loxodes/vna/breakouts/amp_cpw_hmc311/hmc311_cpw.png

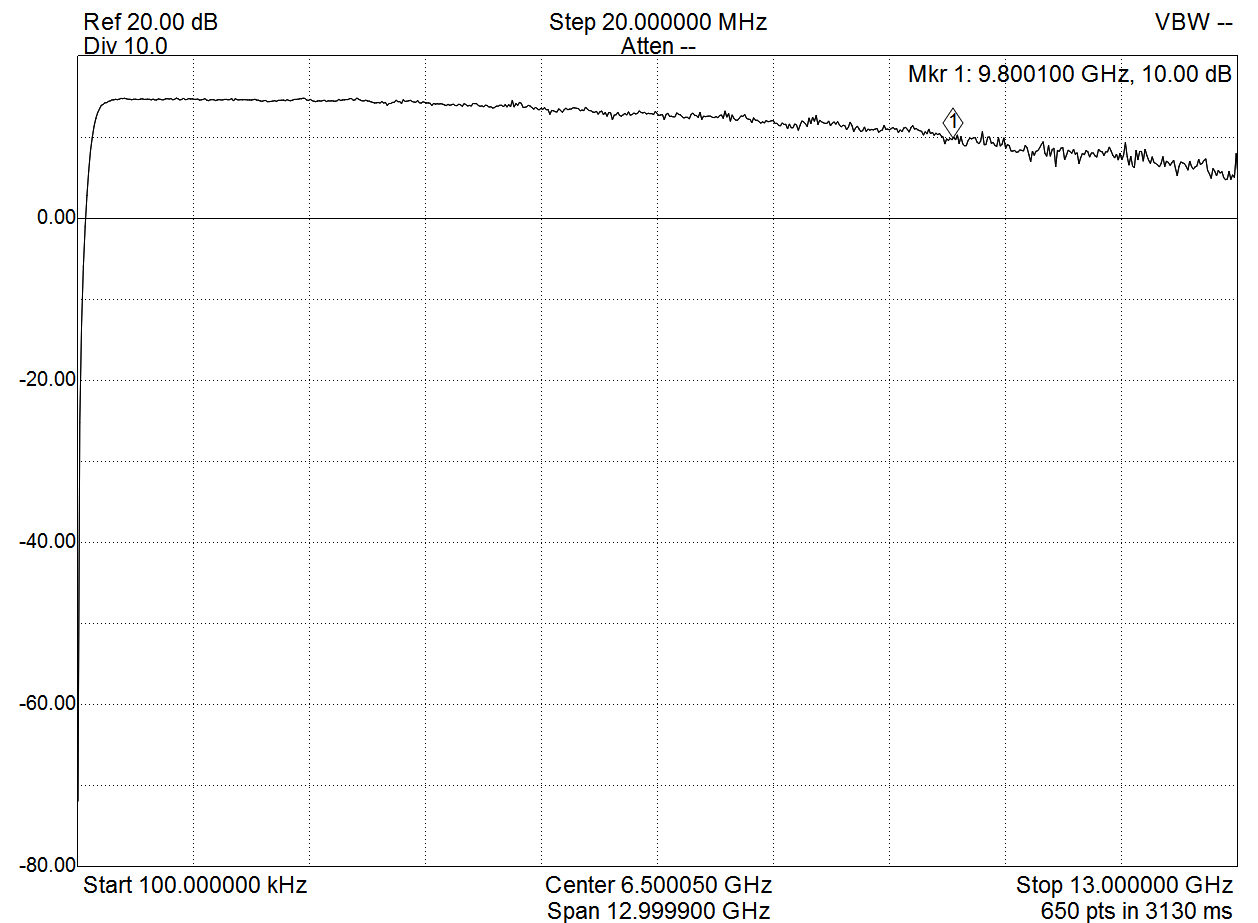
breakouts/amp_cpw_hmc311/hmc311_cpw.png
