loxodes/vna/doc/eevblog_forum_pictures/air_1foot_above_pile.png

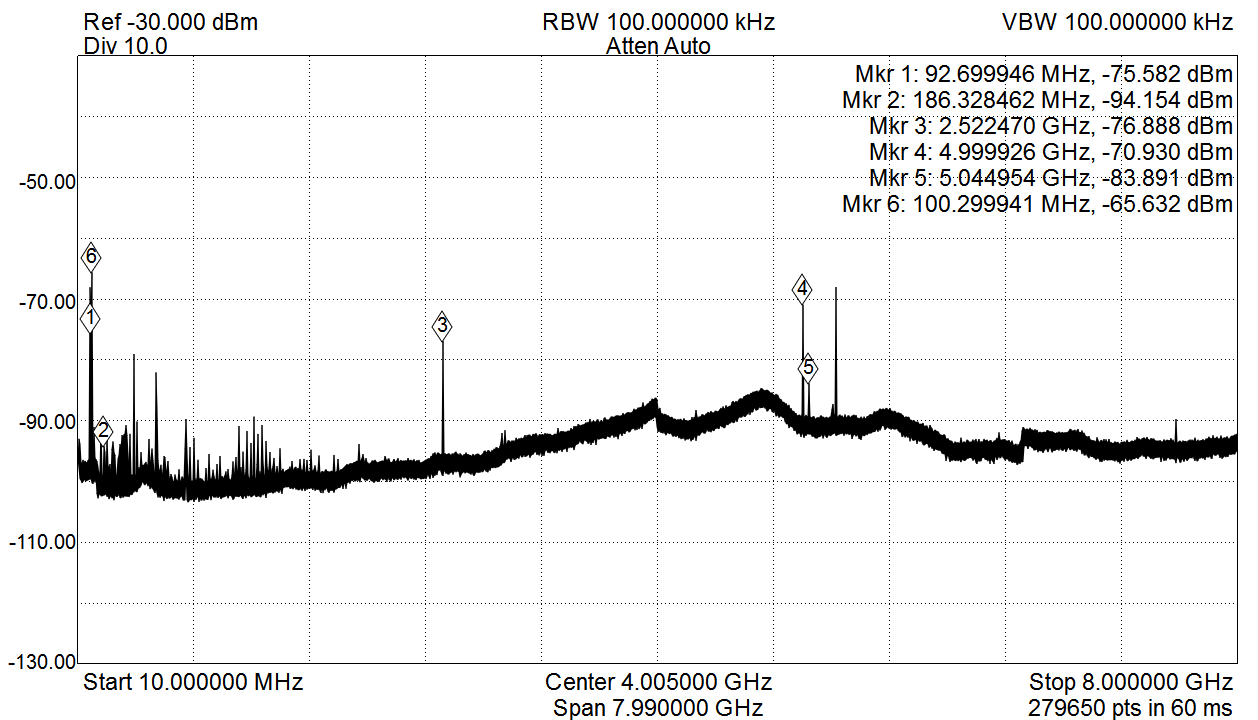
doc/eevblog_forum_pictures/air_1foot_above_pile.png
