loxodes/vna/doc/lpf_smith.png

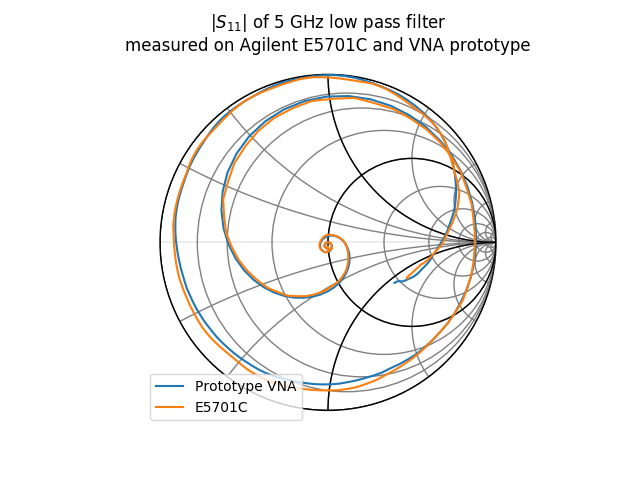
doc/lpf_smith.png
