loxodes/vna/doc/modules.jpg

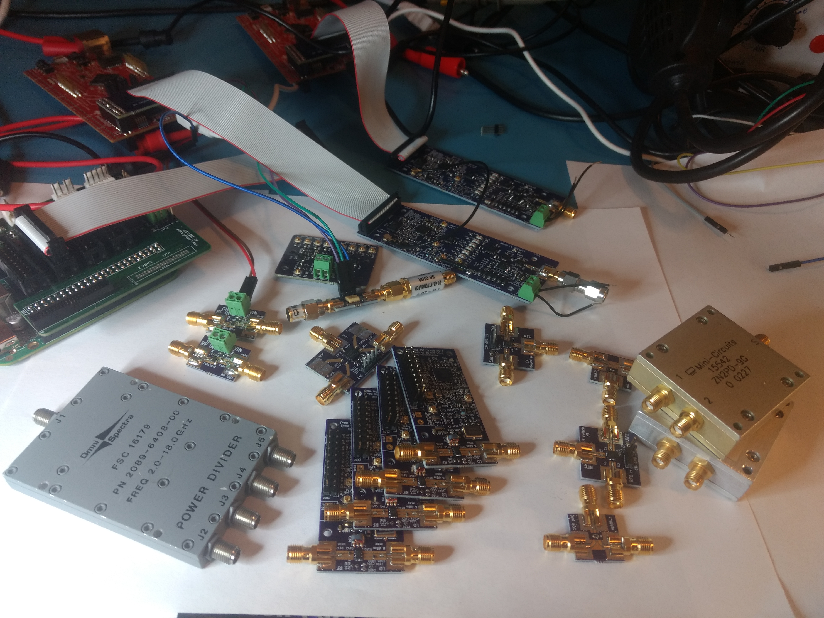
doc/modules.jpg
