loxodes/vna/doc/r0_vna.jpg

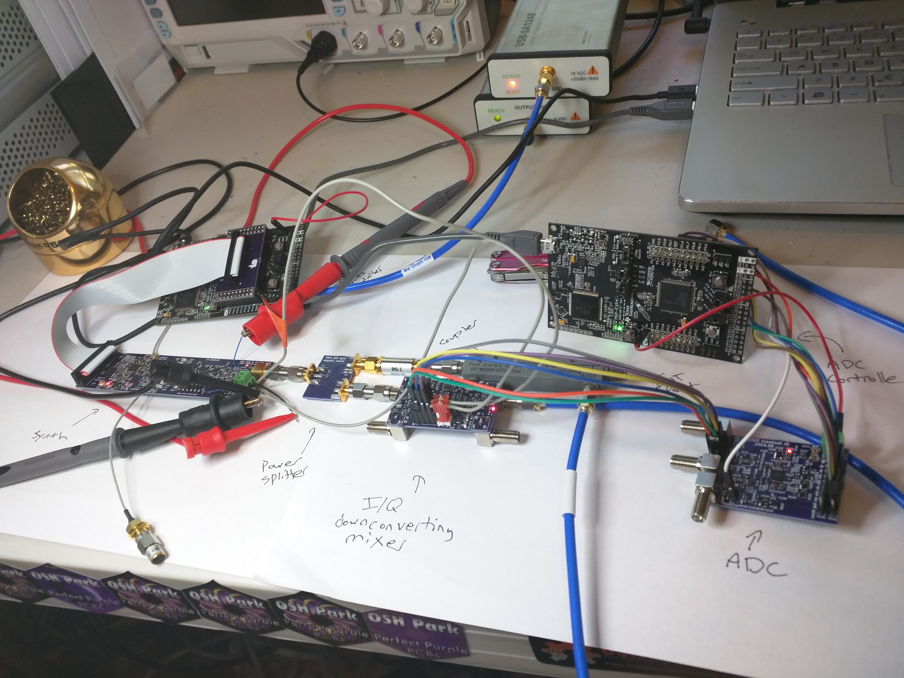
doc/r0_vna.jpg
