loxodes/vna/doc/synth.jpg

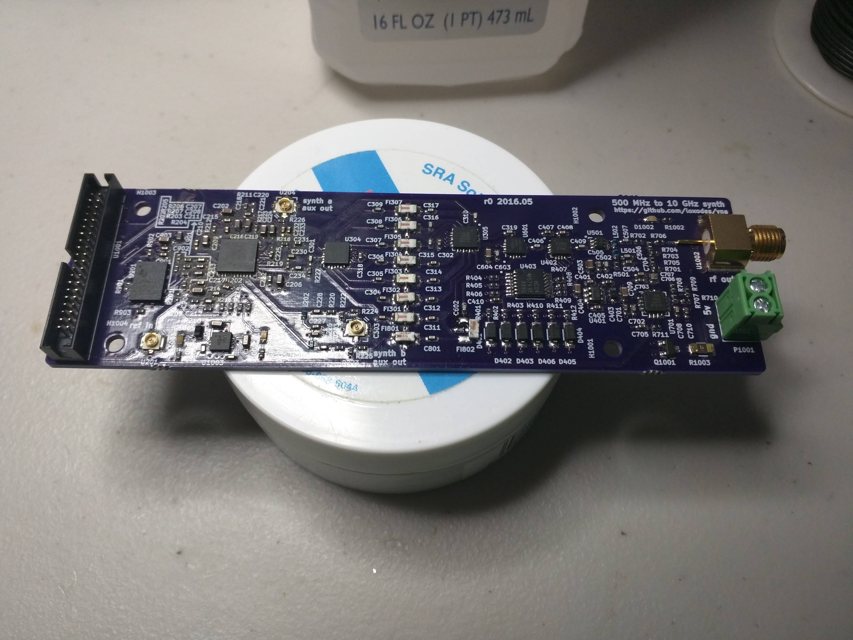
doc/synth.jpg
