loxodes/vna/doc/vna_pictures/cape.jpg

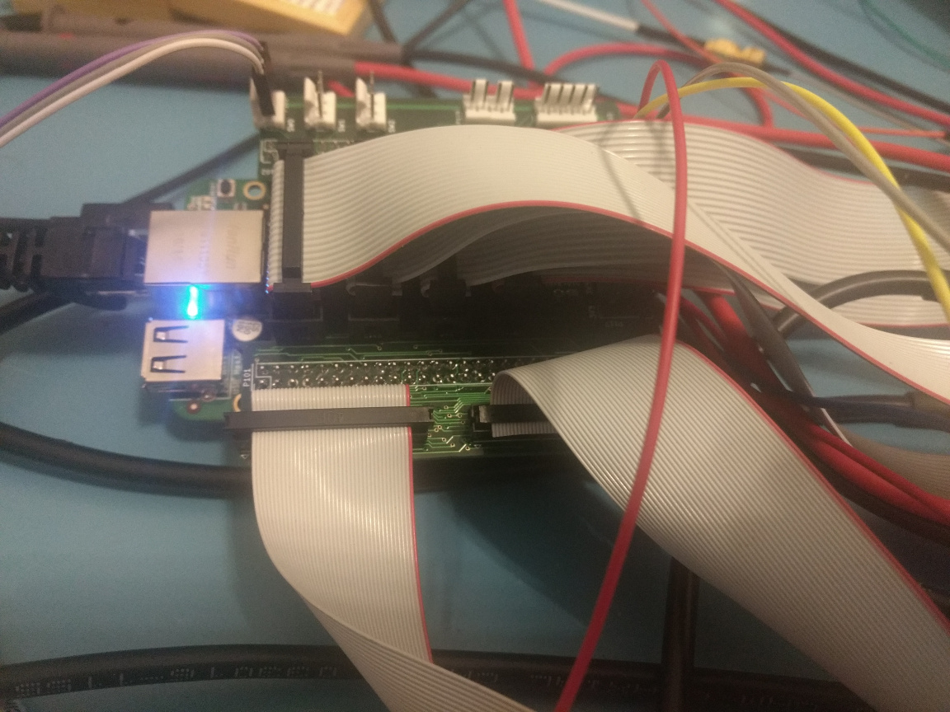
doc/vna_pictures/cape.jpg
