loxodes/vna/doc/vna_pictures/front_module_pile.jpg

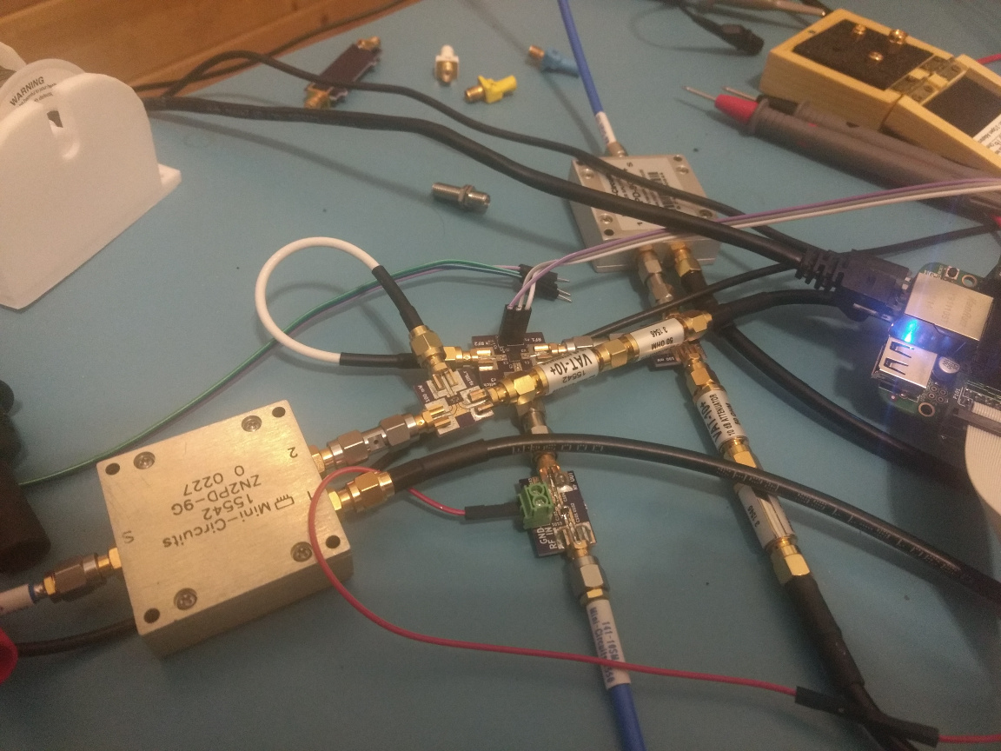
doc/vna_pictures/front_module_pile.jpg
