loxodes/vna/doc/vna_pictures/receivers.jpg

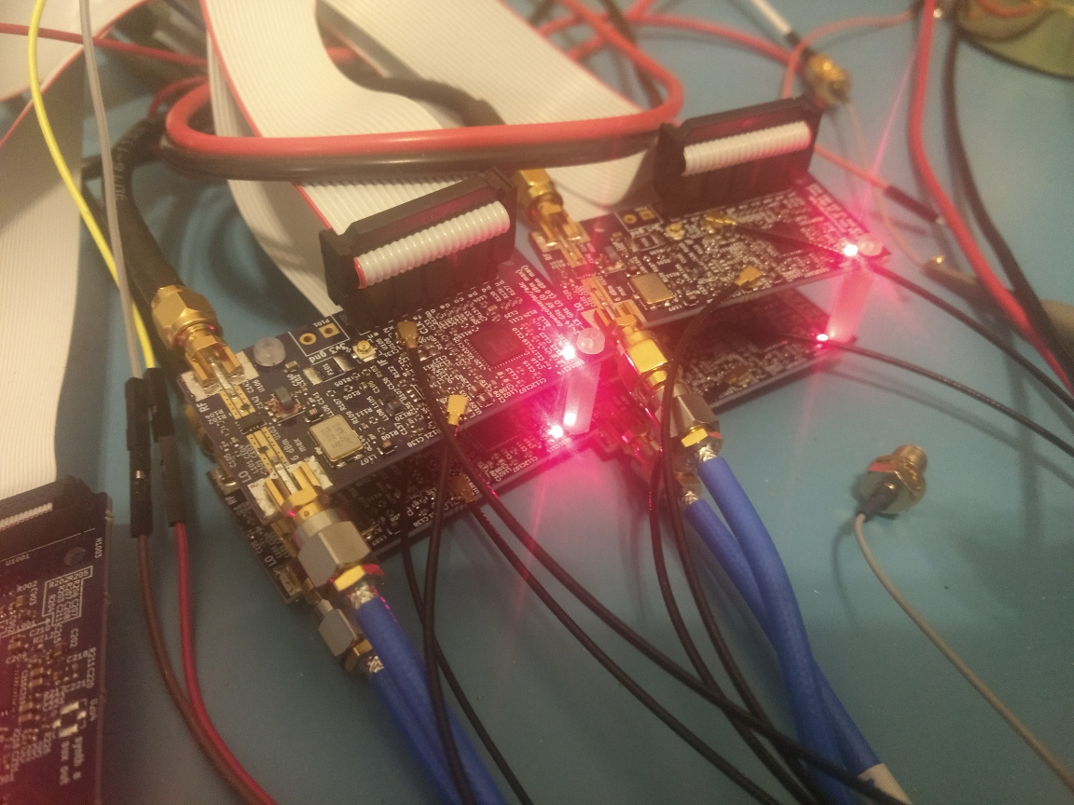
doc/vna_pictures/receivers.jpg
