loxodes/vna/doc/vna_pictures/s11_3dbatt.png

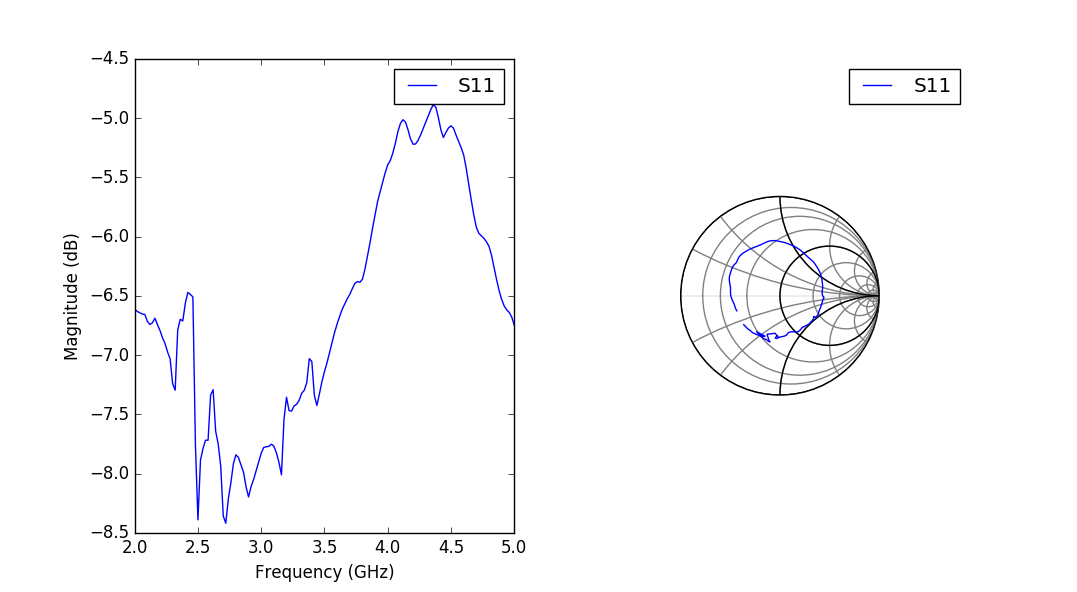
doc/vna_pictures/s11_3dbatt.png
