loxodes/vna/doc/vna_pictures/s11_10dbatt.png

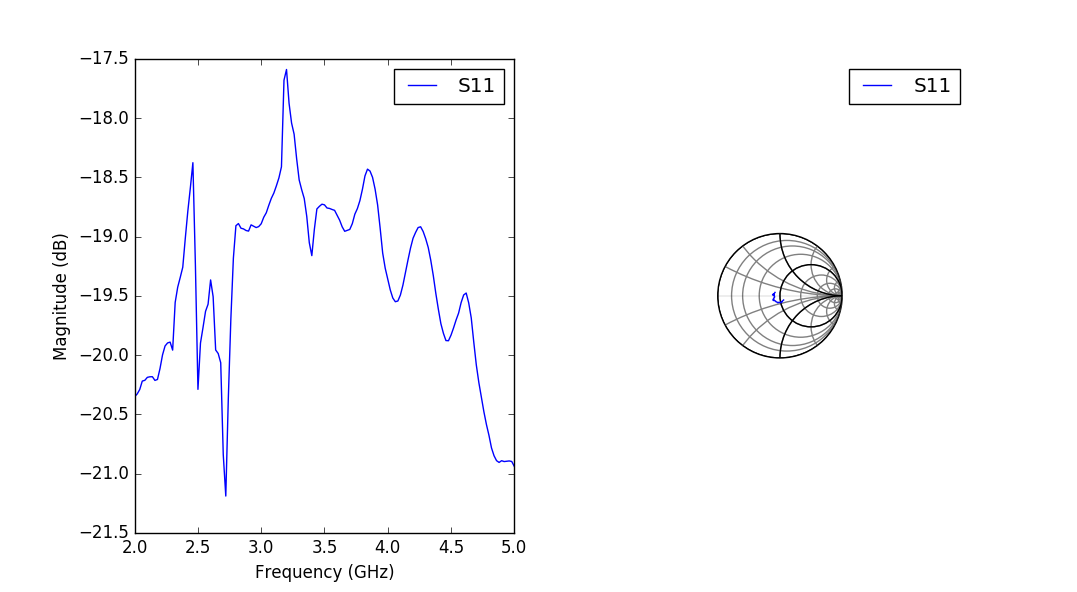
doc/vna_pictures/s11_10dbatt.png
