loxodes/vna/doc/vna_pictures/synth.jpg

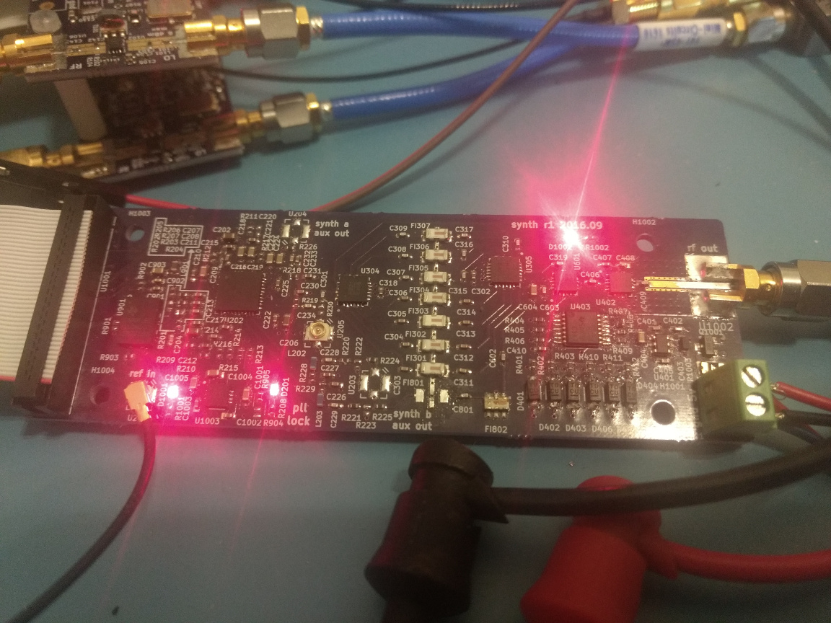
doc/vna_pictures/synth.jpg
