loxodes/vna/doc/vna_r1_ctrl.jpg

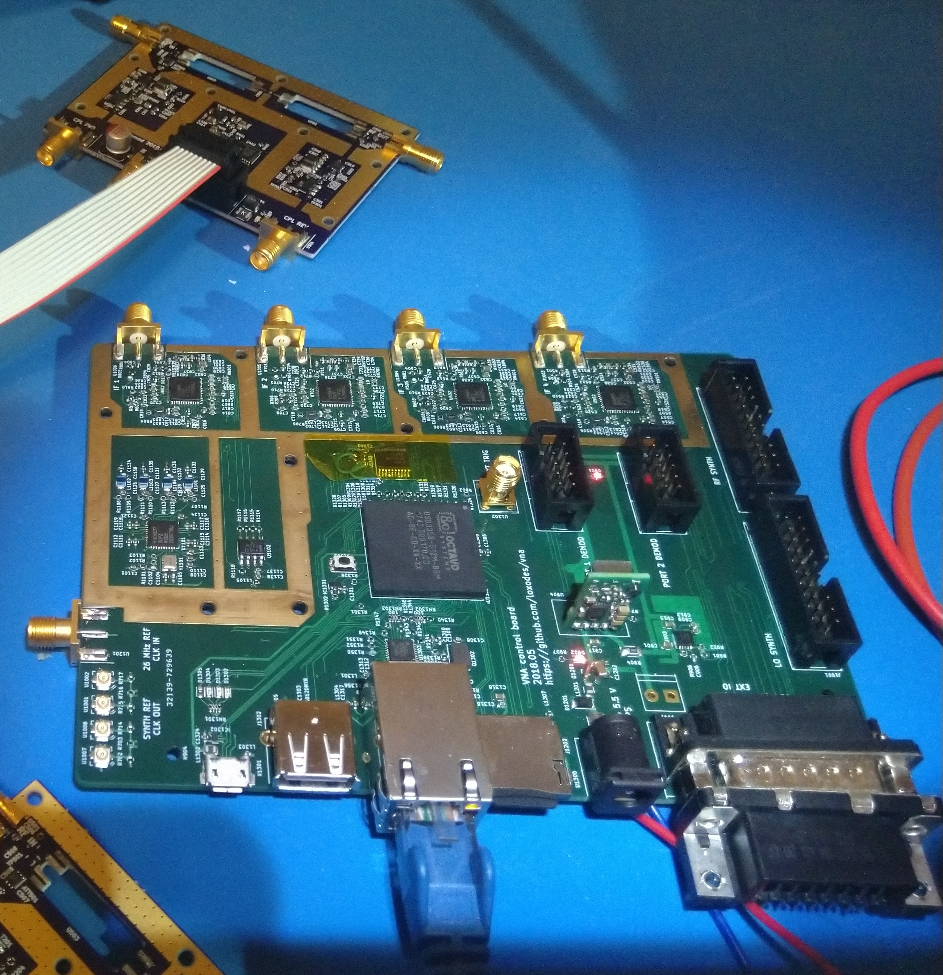
doc/vna_r1_ctrl.jpg
