loxodes/vna/simulations/ltspice/demod_baseband.asc

C1: cap; 22p
C2: cap; 100n
R1: res; 604
R2: res; 604
R3: res; 604
U1: LT1567
V1: voltage; 5
V2: voltage; .7
V3: voltage; ""; AC 1
Named nets: 0, vout
.ac oct 100 1k 5Meg
