loxodes/vna/hardware/mm_reflectometer/evalboards/ep2k1P/ep2k1P.kicad_pcb

## KiCad design hardware/mm_reflectometer/evalboards/ep2k1P/ep2k1P.kicad_pcb (2020-12-29)

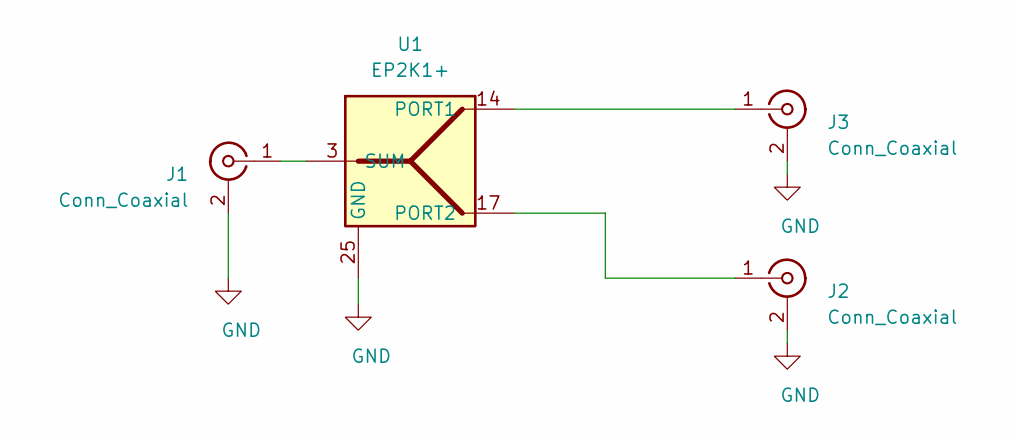
[picture p76: schematic ep2k1P.kicad_sch]

Parts:
J1, J2, J3: Conn_Coaxial; sw_edge_oshpark_4layer
U1: EP2K1+; DG1847; mpn EP2K1+; mouser# 139-EP2K1

Connections:
GND: J1.2 (Ext), J2.2 (Ext), J3.2 (Ext), U1.1 (NC), U1.2 (NC), U1.4 (NC), U1.5 (NC), U1.6 (NC), U1.7 (NC), U1.8 (NC), U1.9 (NC), U1.10 (NC), U1.11 (NC), U1.12 (NC), U1.13 (NC), U1.15 (NC), U1.16 (NC), U1.18 (NC), U1.19 (NC), U1.20 (NC), U1.21 (NC), U1.22 (NC), U1.23 (NC), U1.24 (NC), U1.25 (GND)
unnamed: J1.1 (In), U1.3 (SUM)
unnamed: J3.1 (In), U1.14 (PORT1)
unnamed: J2.1 (In), U1.17 (PORT2)

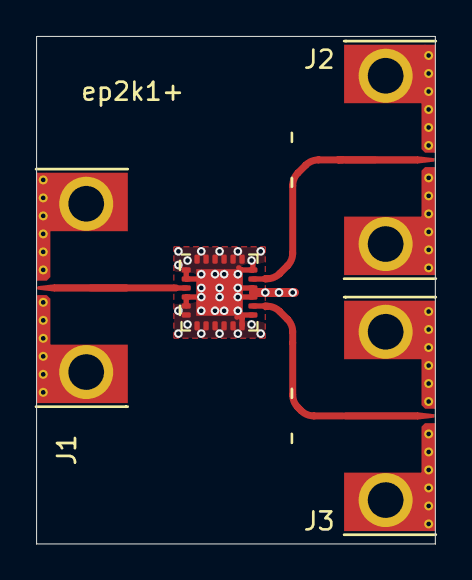
[picture p77: board ep2k1P.kicad_pcb from above]

Board: 4 copper layers, 22.2 x 28.2 mm, 4 parts (0 on the bottom side), 4 nets.
