loxodes/vna/hardware/mm_reflectometer/evalboards/fpc07181/fpc07181.kicad_pcb

## KiCad design hardware/mm_reflectometer/evalboards/fpc07181/fpc07181.kicad_pcb (2020-12-29)

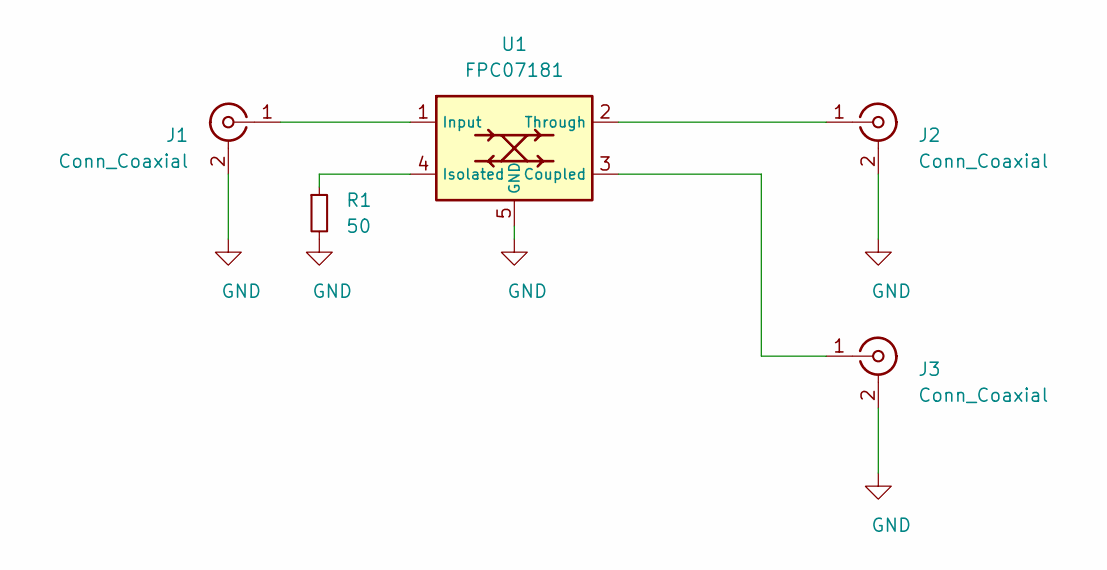
[picture p78: schematic fpc07181.kicad_sch]

Parts:
J1, J2, J3: Conn_Coaxial; sw_edge_oshpark_4layer
R1: 50; R_0402_1005Metric
U1: FPC07181; mpn FPC07181; digikey# 1761-1032-ND

Connections:
GND: J1.2 (Ext), J2.2 (Ext), J3.2 (Ext), R1.2, U1.5 (GND)
unnamed: J1.1 (In), U1.1 (Input)
unnamed: J2.1 (In), U1.2 (Through)
unnamed: J3.1 (In), U1.3 (Coupled)
unnamed: R1.1, U1.4 (Isolated)

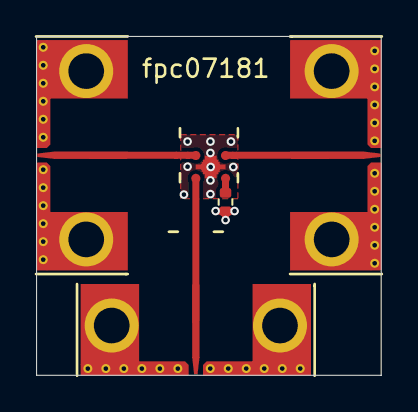
[picture p79: board fpc07181.kicad_pcb from above]

Board: 4 copper layers, 19.2 x 18.8 mm, 5 parts (0 on the bottom side), 5 nets.
