loxodes/vna/breakouts/balun/balun.kicad_pcb

## KiCad design breakouts/balun/balun.kicad_pcb (2020-07-13)

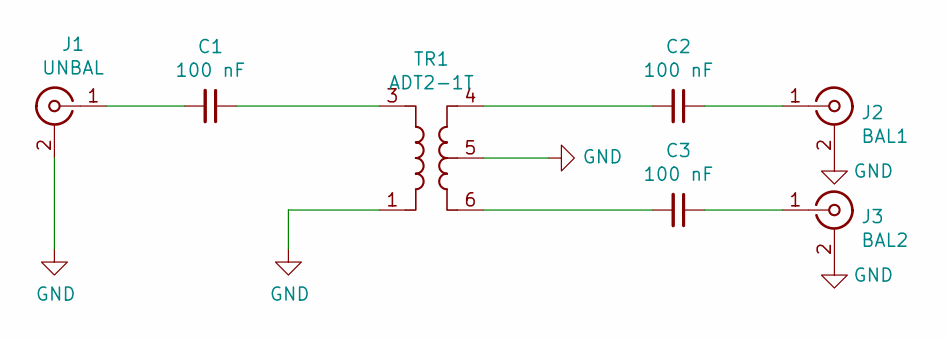
[picture p80: schematic balun.sch]

Parts:
C1, C2, C3: 100 nF; C_0603_1608Metric
J1: UNBAL; SMA_Amphenol_132134_Vertical
J2: BAL1; SMA_Amphenol_132134_Vertical
J3: BAL2; SMA_Amphenol_132134_Vertical
TR1: ADT2-1T; Mini-Circuits_CD542_H2.84mm

Connections:
GND: J1.2 (Ext), J2.2 (Ext), J3.2 (Ext), TR1.1, TR1.5
unnamed: C1.1, TR1.3
unnamed: C1.2, J1.1 (In)
unnamed: C2.1, J2.1 (In)
unnamed: C2.2, TR1.4
unnamed: C3.1, J3.1 (In)
unnamed: C3.2, TR1.6

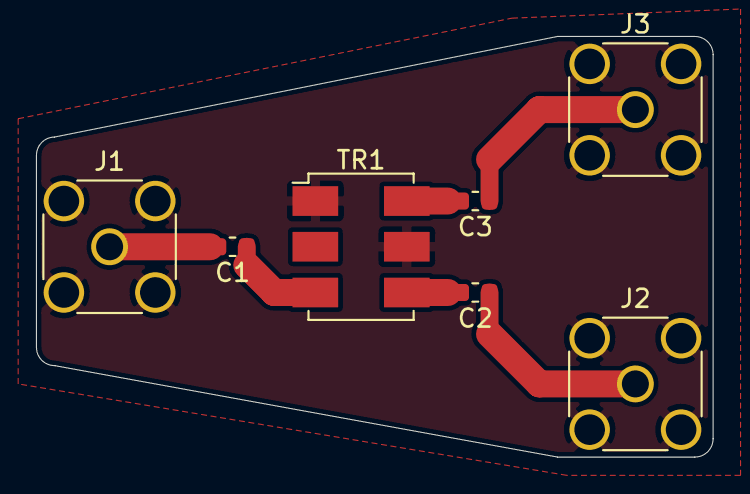
[picture p81: board balun.kicad_pcb from above]

Board: 2 copper layers, 37.6 x 23.4 mm, 7 parts (0 on the bottom side), 7 nets.
