loxodes/vna/hardware/vna_mm_synth/vna_mm_synth.kicad_pcb

## KiCad design hardware/vna_mm_synth/vna_mm_synth.kicad_pcb (2020-04-20)

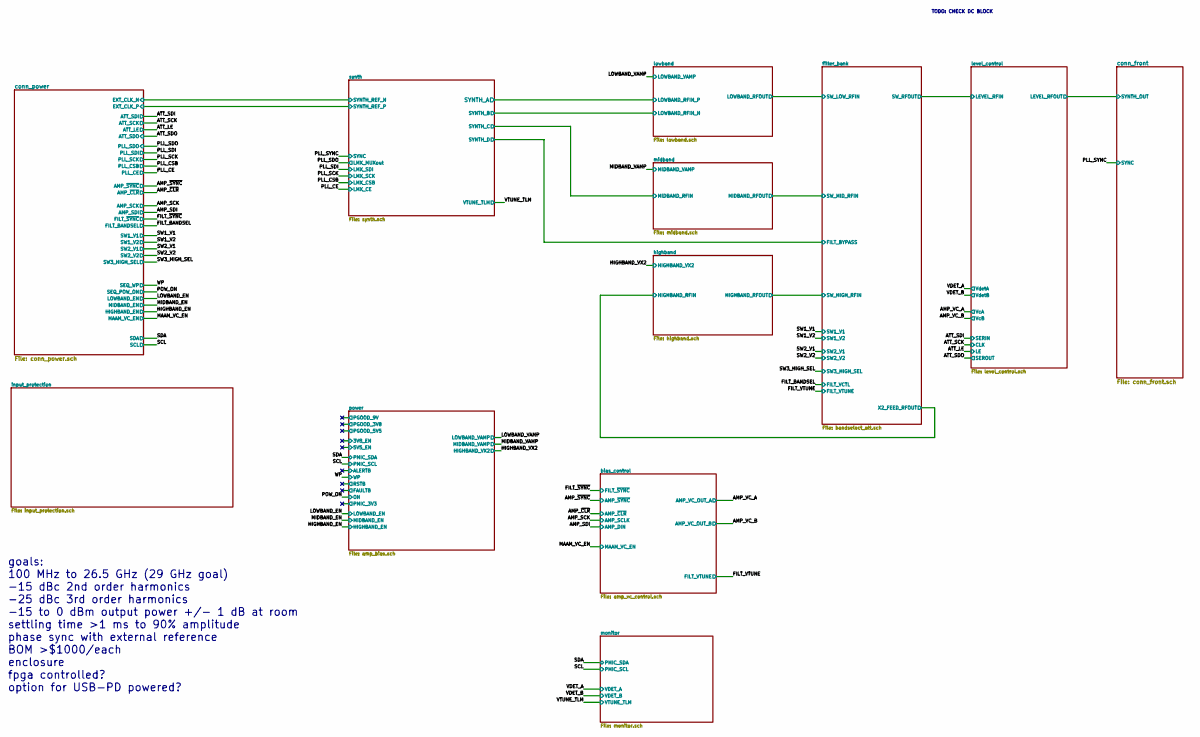
[picture p82: schematic vna_mm_synth.sch]

Notes on the sheet:
goals: 100 MHz to 26.5 GHz (29 GHz goal) -15 dBc 2nd order harmonics -25 dBc 3rd order harmonics -15 to 0 dBm output power +/- 1 dB at room settling time >1 ms to 90% amplitude phase sync with external reference BOM >$1000/each enclosure fpga controlled? option for USB-PD powered?
TODO: CHECK DC BLOCK

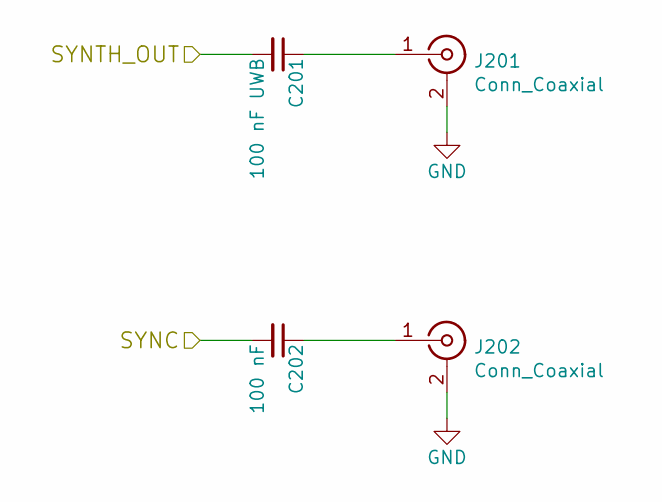
[picture p83: schematic conn_front.sch]

Parts:
C201: 100 nF UWB; C_0402_1005Metric
C202: 100 nF; C_0402_1005Metric
J201: Conn_Coaxial; sw_edge_ro4350b_10mil
J202: Conn_Coaxial; SMA_Amphenol_132289_EdgeMount

Connections:
/PLL_SYNC: C202.2; also elsewhere on the board
/level_control/LEVEL_RFOUT: C201.2; also elsewhere on the board
GND: J201.2 (Ext), J202.2 (Ext); also elsewhere on the board
unnamed: C201.1, J201.1 (In)
unnamed: C202.1, J202.1 (In)

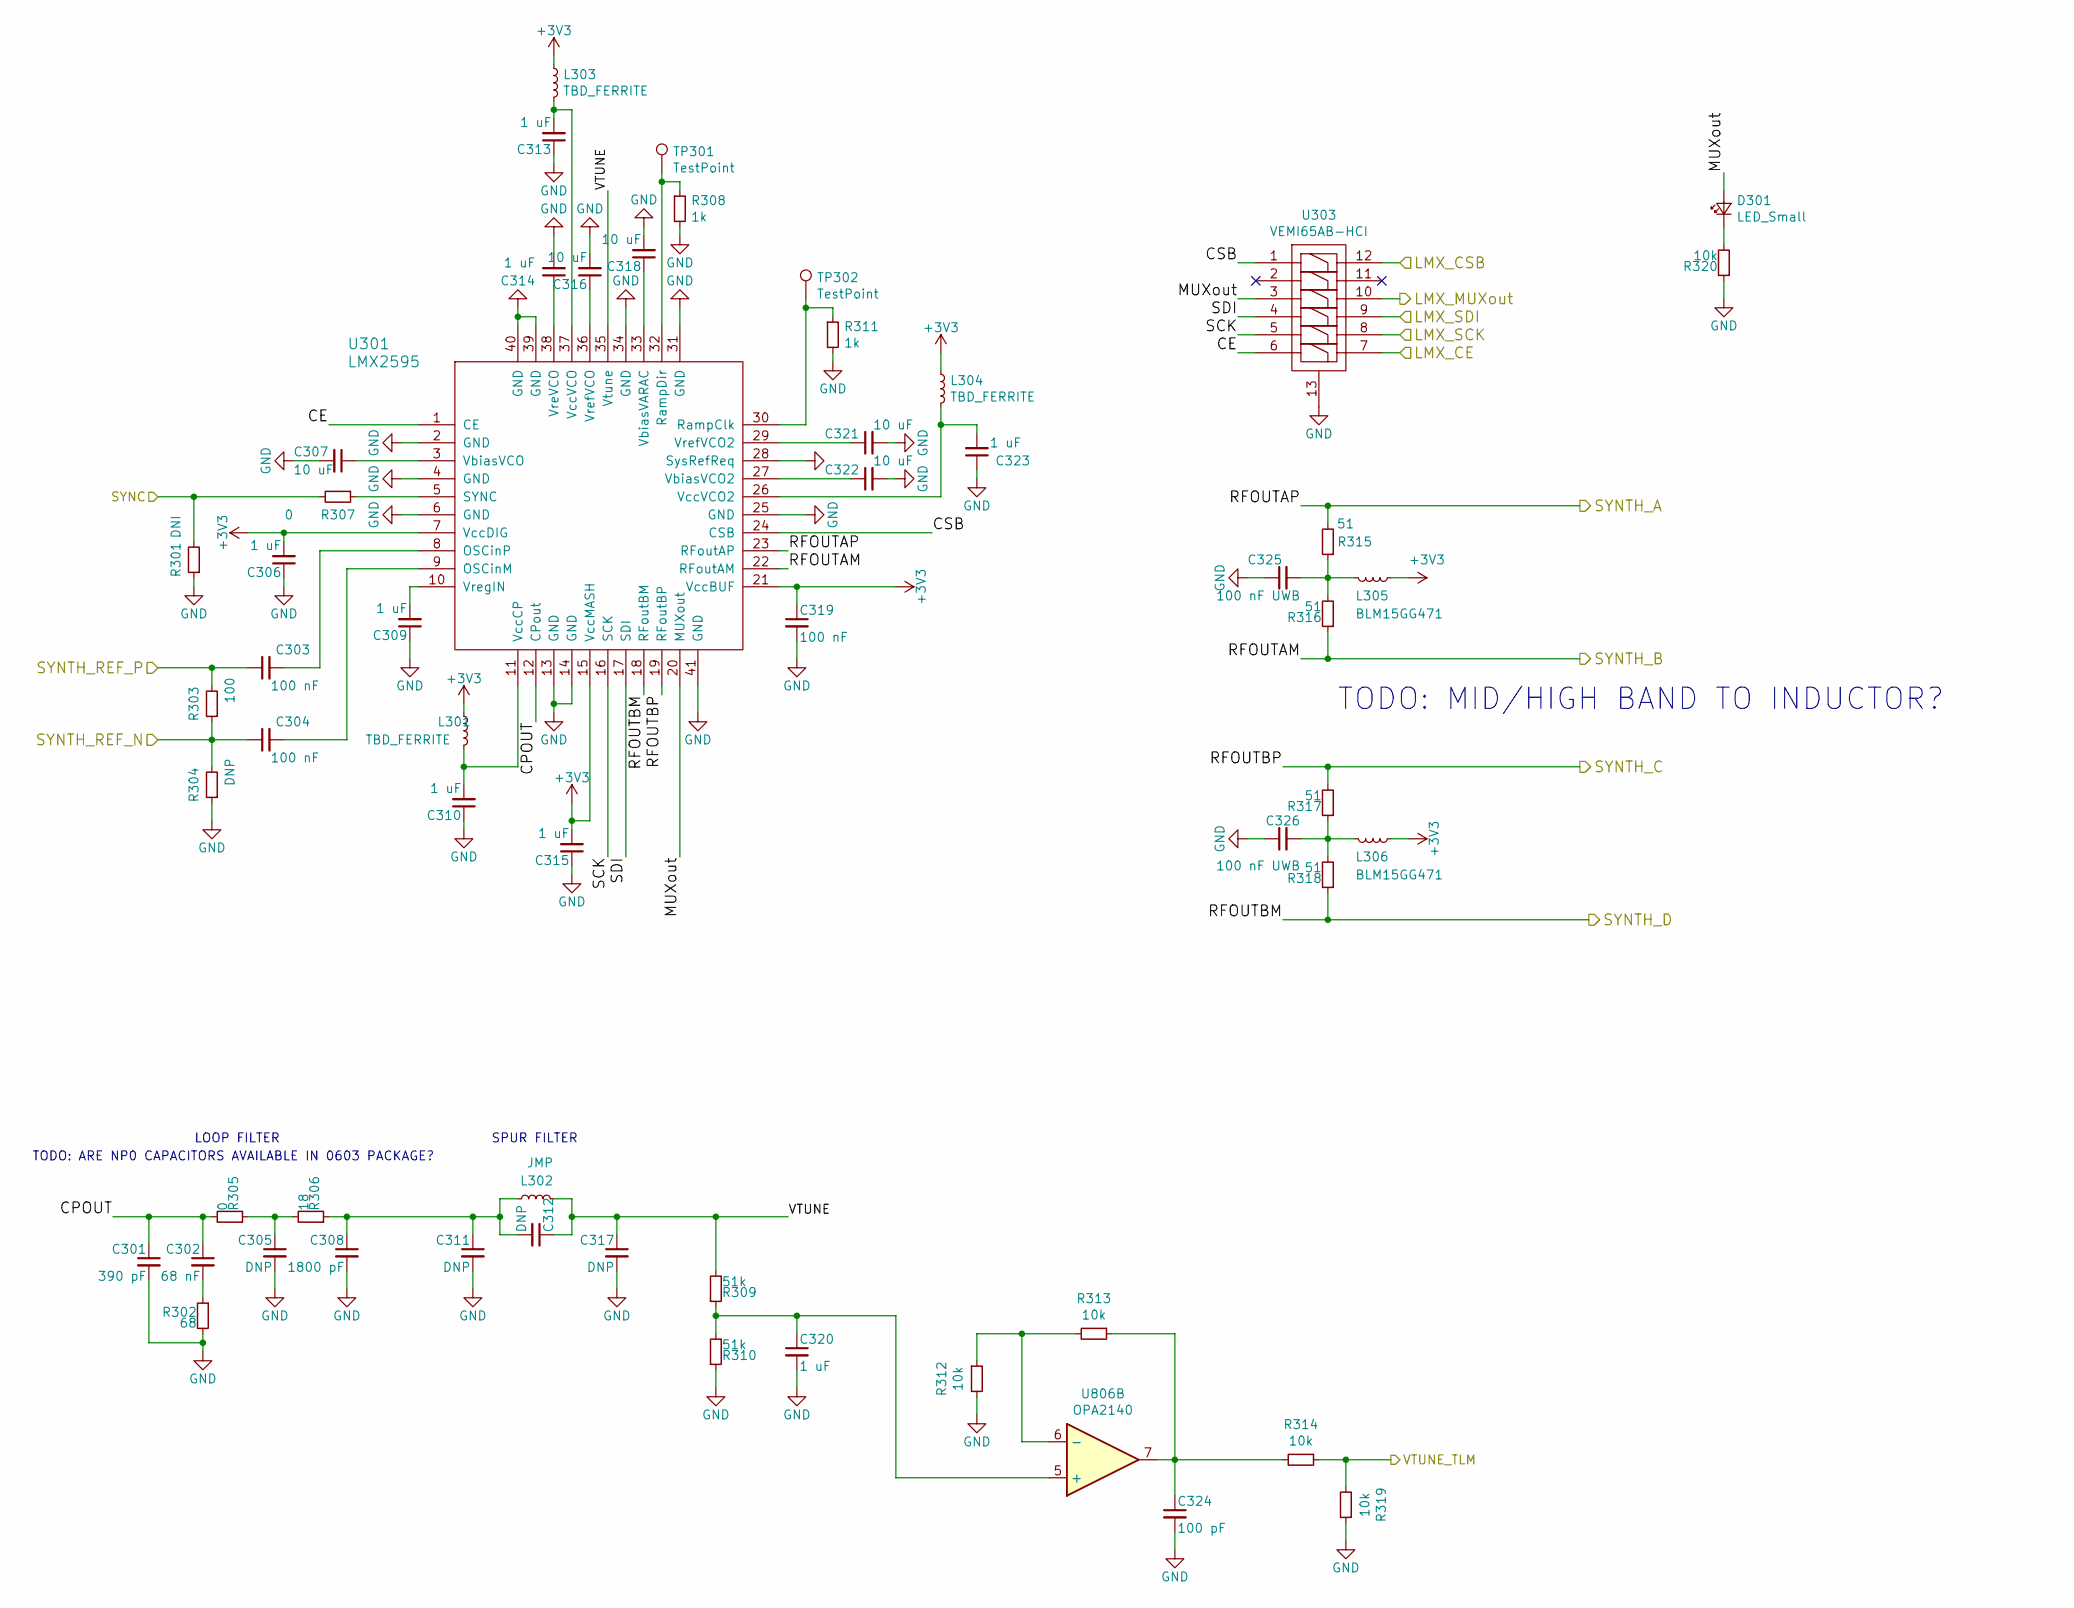
[picture p84: schematic synth.sch]

Parts:
C301: 390 pF; C_0603_1608Metric
C302: 68 nF; C_0603_1608Metric
C303, C304, C319: 100 nF; C_0402_1005Metric
C305, C311, C312, C317: DNP; C_0603_1608Metric
C306, C309, C310, C313, C314, C315, C320, C323: 1 uF; C_0402_1005Metric
C307, C316, C318, C321, C322: 10 uF; C_0603_1608Metric
C308: 1800 pF; C_0603_1608Metric
C324: 100 pF; C_0402_1005Metric
C325, C326: 100 nF UWB; C_0402_1005Metric
D301: LED_Small; LED_0603_1608Metric
L301, L303, L304: TBD_FERRITE; L_0603_1608Metric
L302: JMP; L_0603_1608Metric
L305, L306: BLM15GG471; L_0402_1005Metric
R301: DNI; R_0402_1005Metric
R302: 68; R_0402_1005Metric
R303: 100; R_0402_1005Metric
R304: DNP; R_0402_1005Metric
R305, R307: 0; R_0402_1005Metric
R306: 18; R_0402_1005Metric
R308, R311: 1k; R_0402_1005Metric
R309, R310: 51k; R_0402_1005Metric
R312, R313, R314, R319, R320: 10k; R_0402_1005Metric
R315, R316, R317, R318: 51; R_0402_1005Metric
TP301, TP302: TestPoint; TestPoint_Pad_1.0x1.0mm
U301: LMX2595; Texas_S-PVQFN-N40_EP4.6x4.6mm
U303: VEMI65AB-HCI; LLP2513-13L
U806: OPA2140; MSOP-8_3x3mm_P0.65mm

Connections:
+3V3: C306.2, C315.2, C319.1, L301.1, L303.1, L304.1, L305.1, L306.1, U301.7 (VccDIG), U301.15 (VccMASH), U301.21 (VccBUF); also elsewhere on the board
/PLL_CE: U303.7; also elsewhere on the board
/PLL_CSB: U303.12; also elsewhere on the board
/PLL_SCK: U303.8; also elsewhere on the board
/PLL_SDI: U303.9; also elsewhere on the board
/PLL_SDO: U303.10; also elsewhere on the board
/PLL_SYNC: R301.2, R307.2; also elsewhere on the board
/VTUNE_TLM: R314.1, R319.2; also elsewhere on the board
/conn_power/EXT_CLK_N: C304.1, R303.1, R304.2; also elsewhere on the board
/conn_power/EXT_CLK_P: C303.1, R303.2; also elsewhere on the board
/lowband/LOWBAND_RFIN_N: R316.1, U301.22 (RFoutAM); also elsewhere on the board
/lowband/LOWBAND_RFIN_P: R315.2, U301.23 (RFoutAP); also elsewhere on the board
/midband/MIDBAND_RFIN: R317.2, U301.19 (RFoutBP); also elsewhere on the board
/synth/CE: U301.1 (CE), U303.6
/synth/CPOUT: C301.1, C302.1, R305.2, U301.12 (CPout)
/synth/CSB: U301.24 (CSB), U303.1
/synth/MUXout: D301.2 (A), U301.20 (MUXout), U303.3
/synth/SCK: U301.16 (SCK), U303.5
/synth/SDI: U301.17 (SDI), U303.4
/synth/SYNTH_D: R318.1, U301.18 (RFoutBM)
/synth/VTUNE: C312.1, C317.1, L302.2, R309.2, U301.35 (Vtune)
GND: C301.2, C305.2, C306.1, C307.2, C308.2, C309.1, C310.1, C311.2, C313.1, C314.2, C315.1, C316.2, C317.2, C318.2, C319.2, C320.2, C321.2, C322.2, C323.1, C324.2, C325.1, C326.1, R301.1, R302.2, R304.1, R308.2, R310.1, R311.2, R312.2, R319.1, R320.1, U301.2 (GND), U301.4 (GND), U301.6 (GND), U301.13 (GND), U301.14 (GND), U301.25 (GND), U301.28 (SysRefReq), U301.31 (GND), U301.34 (GND), U301.39 (GND), U301.40 (GND), U301.41 (GND), U303.13; also elsewhere on the board
unnamed: C302.2, R302.1
unnamed: C303.2, U301.8 (OSCinP)
unnamed: C304.2, U301.9 (OSCinM)
unnamed: C305.1, R305.1, R306.2
unnamed: C307.1, U301.3 (VbiasVCO)
unnamed: C308.1, C311.1, C312.2, L302.1, R306.1
unnamed: C309.2, U301.10 (VregIN)
unnamed: C310.2, L301.2, U301.11 (VccCP)
unnamed: C313.2, L303.2, U301.37 (VccVCO)
unnamed: C314.1, U301.38 (VreVCO)
unnamed: C316.1, U301.36 (VrefVCO)
unnamed: C318.1, U301.33 (VbiasVARAC)
unnamed: C320.1, R309.1, R310.2, U806.5 (+)
unnamed: C321.1, U301.29 (VrefVCO2)
unnamed: C322.1, U301.27 (VbiasVCO2)
unnamed: C323.2, L304.2, U301.26 (VccVCO2)
unnamed: C324.1, R313.1, R314.2, U806.7
unnamed: C325.2, L305.2, R315.1, R316.2
unnamed: C326.2, L306.2, R317.1, R318.2
unnamed: D301.1 (K), R320.2
unnamed: R307.1, U301.5 (SYNC)
unnamed: R308.1, TP301.1, U301.32 (RampDir)
unnamed: R311.1, TP302.1, U301.30 (RampClk)
unnamed: R312.1, R313.2, U806.6 (-)

Notes on the sheet:
SPUR FILTER
LOOP FILTER
TODO: ARE NP0 CAPACITORS AVAILABLE IN 0603 PACKAGE?
TODO: MID/HIGH BAND TO INDUCTOR?

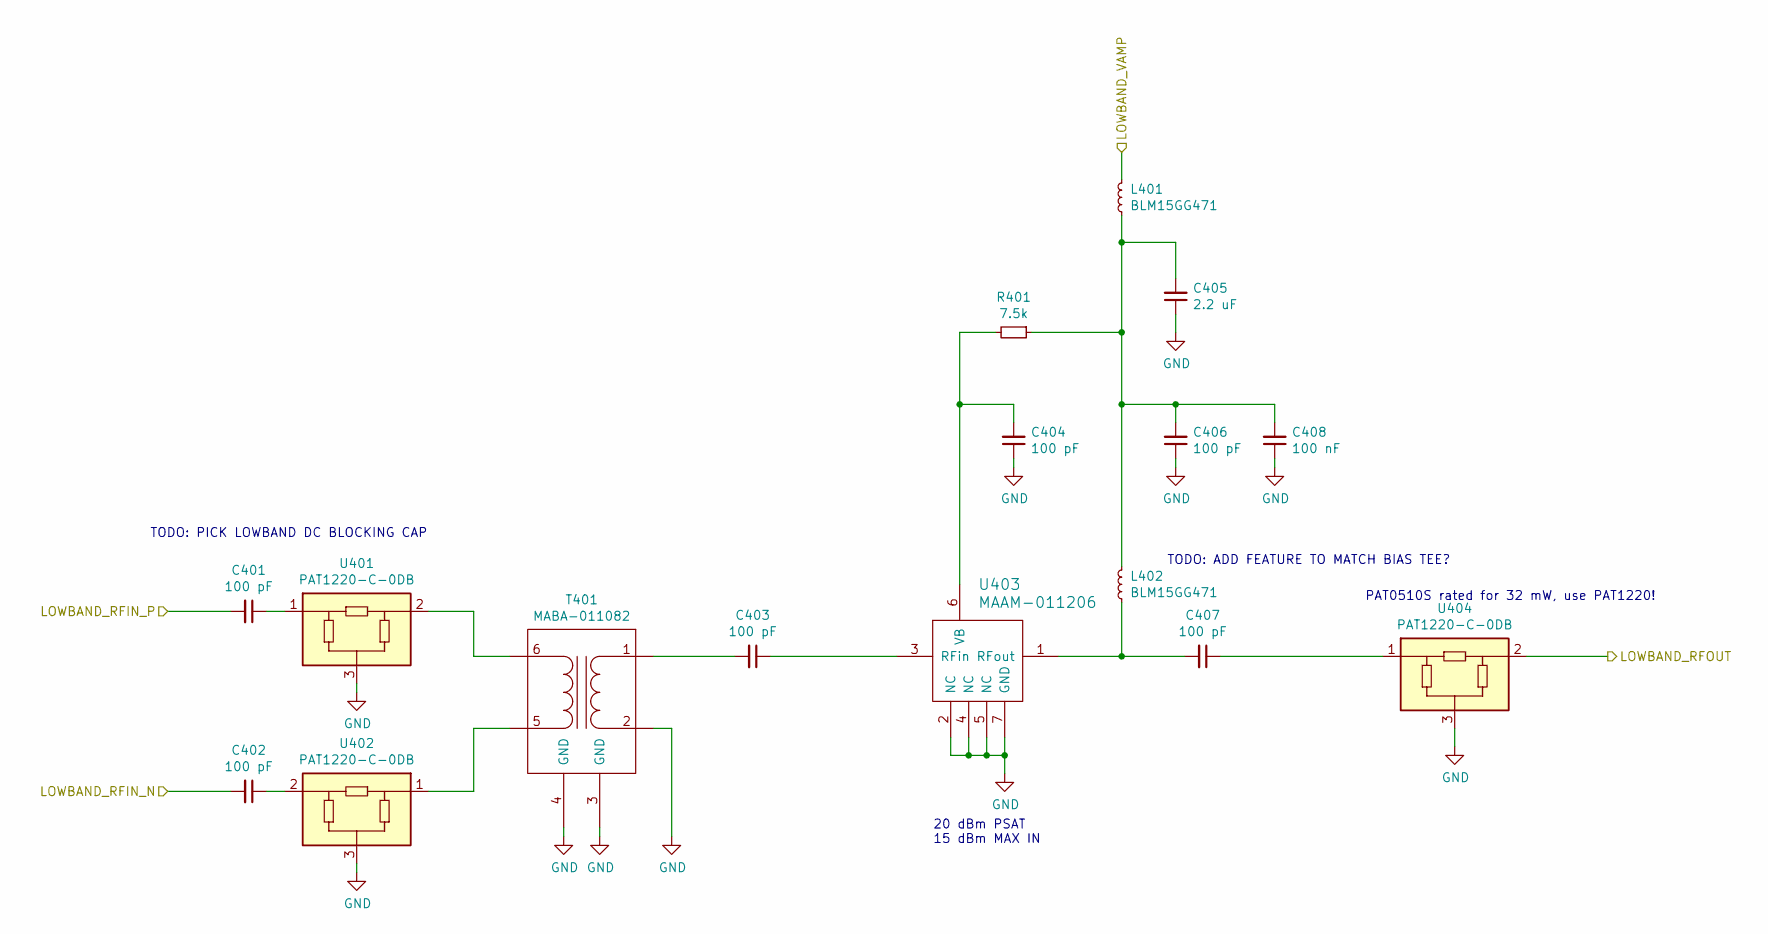
[picture p85: schematic lowband.sch]

Parts:
C401, C402, C403, C404, C406, C407: 100 pF; C_0402_1005Metric
C405: 2.2 uF; C_0603_1608Metric
C408: 100 nF; C_0402_1005Metric
L401, L402: BLM15GG471; L_0402_1005Metric
R401: 7.5k; R_0402_1005Metric
T401: MABA-011082; transformer_3p81_3p81
U401, U402, U404: PAT1220-C-0DB; RF_Attenuator_Susumu_PAT1220
U403: MAAM-011206; TDFN6

Connections:
/LOWBAND_VAMP: L401.2; also elsewhere on the board
/lowband/LOWBAND_RFIN_N: C402.2; also elsewhere on the board
/lowband/LOWBAND_RFIN_P: C401.2; also elsewhere on the board
/lowband/LOWBAND_RFOUT: U404.2; also elsewhere on the board
GND: C404.1, C405.1, C406.1, C408.1, T401.2, T401.3 (GND), T401.4 (GND), U401.3, U402.3, U403.2 (NC), U403.4 (NC), U403.5 (NC), U403.7 (GND), U404.3; also elsewhere on the board
unnamed: C401.1, U401.1
unnamed: C402.1, U402.2
unnamed: C403.1, U403.3 (RFin)
unnamed: C403.2, T401.1
unnamed: C404.2, R401.2, U403.6 (VB)
unnamed: C405.2, C406.2, C408.2, L401.1, L402.2, R401.1
unnamed: C407.1, U404.1
unnamed: C407.2, L402.1, U403.1 (RFout)
unnamed: T401.5, U402.1
unnamed: T401.6, U401.2

Notes on the sheet:
TODO: PICK LOWBAND DC BLOCKING CAP
TODO: ADD FEATURE TO MATCH BIAS TEE?
20 dBm PSAT 15 dBm MAX IN
PAT0510S rated for 32 mW, use PAT1220!

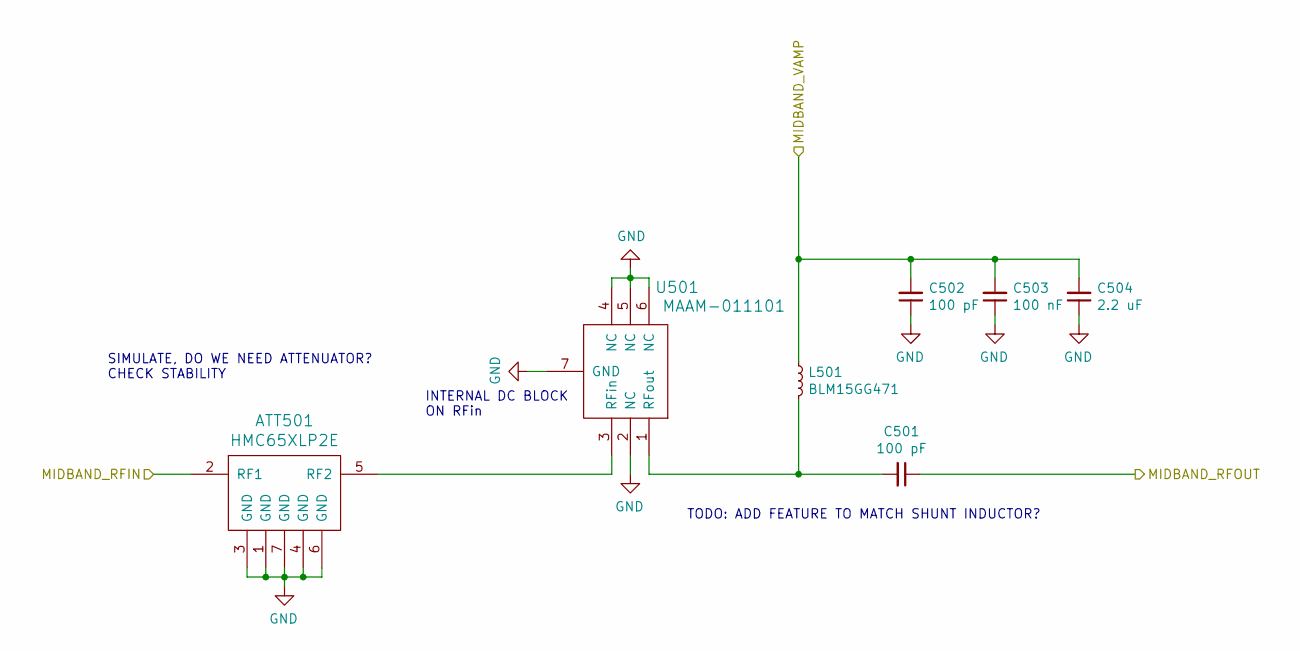
[picture p86: schematic midband.sch]

Parts:
ATT501: HMC65XLP2E; LP2E_DFN6_2x2mm_Pitch0.60mm
C501, C502: 100 pF; C_0402_1005Metric
C503: 100 nF; C_0402_1005Metric
C504: 2.2 uF; C_0603_1608Metric
L501: BLM15GG471; L_0402_1005Metric
U501: MAAM-011101; TDFN6

Connections:
/MIDBAND_VAMP: C502.2, C503.2, C504.2, L501.1; also elsewhere on the board
/midband/MIDBAND_RFIN: ATT501.2 (RF1); also elsewhere on the board
/midband/MIDBAND_RFOUT: C501.1; also elsewhere on the board
GND: ATT501.1 (GND), ATT501.3 (GND), ATT501.4 (GND), ATT501.6 (GND), ATT501.7 (GND), C502.1, C503.1, C504.1, U501.2 (NC), U501.4 (NC), U501.5 (NC), U501.6 (NC), U501.7 (GND); also elsewhere on the board
unnamed: ATT501.5 (RF2), U501.3 (RFin)
unnamed: C501.2, L501.2, U501.1 (RFout)

Notes on the sheet:
INTERNAL DC BLOCK ON RFin
SIMULATE, DO WE NEED ATTENUATOR? CHECK STABILITY
TODO: ADD FEATURE TO MATCH SHUNT INDUCTOR?

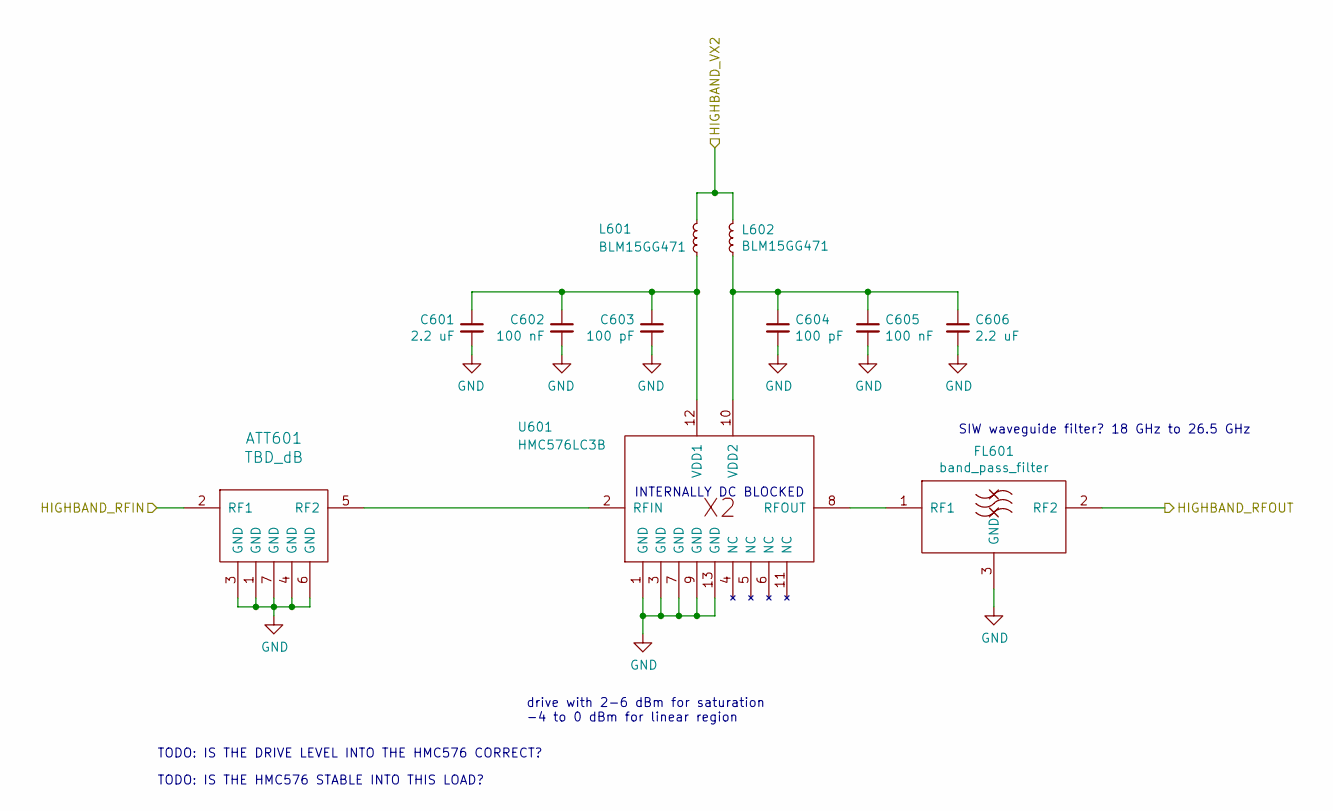
[picture p87: schematic highband.sch]

Parts:
ATT601: TBD_dB; LP2E_DFN6_2x2mm_Pitch0.60mm
C601, C606: 2.2 uF; C_0603_1608Metric
C602, C605: 100 nF; C_0402_1005Metric
C603, C604: 100 pF; C_0402_1005Metric
FL601: band_pass_filter; band_x2_siw_fr408_6p7mil
L601, L602: BLM15GG471; L_0402_1005Metric
U601: HMC576LC3B; LC3B

Connections:
/HIGHBAND_VX2: L601.1, L602.1; also elsewhere on the board
/highband/HIGHBAND_RFIN: ATT601.2 (RF1); also elsewhere on the board
/highband/HIGHBAND_RFOUT: FL601.2 (RF2); also elsewhere on the board
GND: ATT601.1 (GND), ATT601.3 (GND), ATT601.4 (GND), ATT601.6 (GND), ATT601.7 (GND), C601.2, C602.2, C603.2, C604.2, C605.2, C606.2, FL601.3 (GND), U601.1 (GND), U601.3 (GND), U601.7 (GND), U601.9 (GND), U601.13 (GND); also elsewhere on the board
unnamed: ATT601.5 (RF2), U601.2 (RFIN)
unnamed: C601.1, C602.1, C603.1, L601.2, U601.12 (VDD1)
unnamed: C604.1, C605.1, C606.1, L602.2, U601.10 (VDD2)
unnamed: FL601.1 (RF1), U601.8 (RFOUT)

Notes on the sheet:
SIW waveguide filter? 18 GHz to 26.5 GHz
INTERNALLY DC BLOCKED
TODO: IS THE DRIVE LEVEL INTO THE HMC576 CORRECT?
drive with 2-6 dBm for saturation -4 to 0 dBm for linear region
TODO: IS THE HMC576 STABLE INTO THIS LOAD?

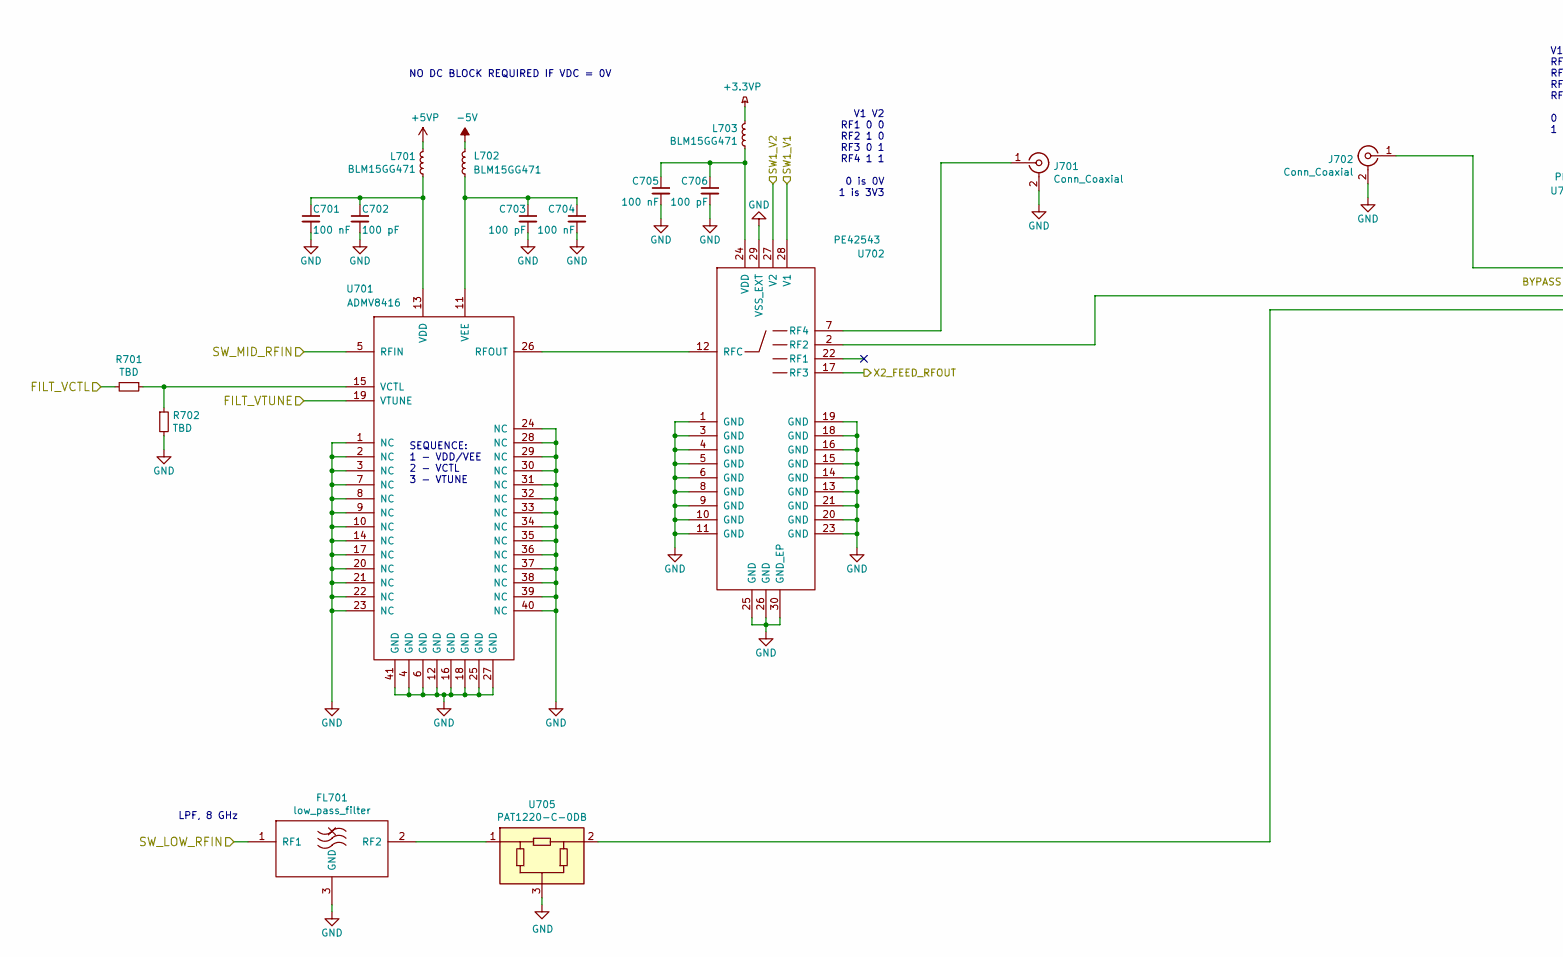
[picture p88: schematic bandselect_att.sch, part in row 1, column 1]

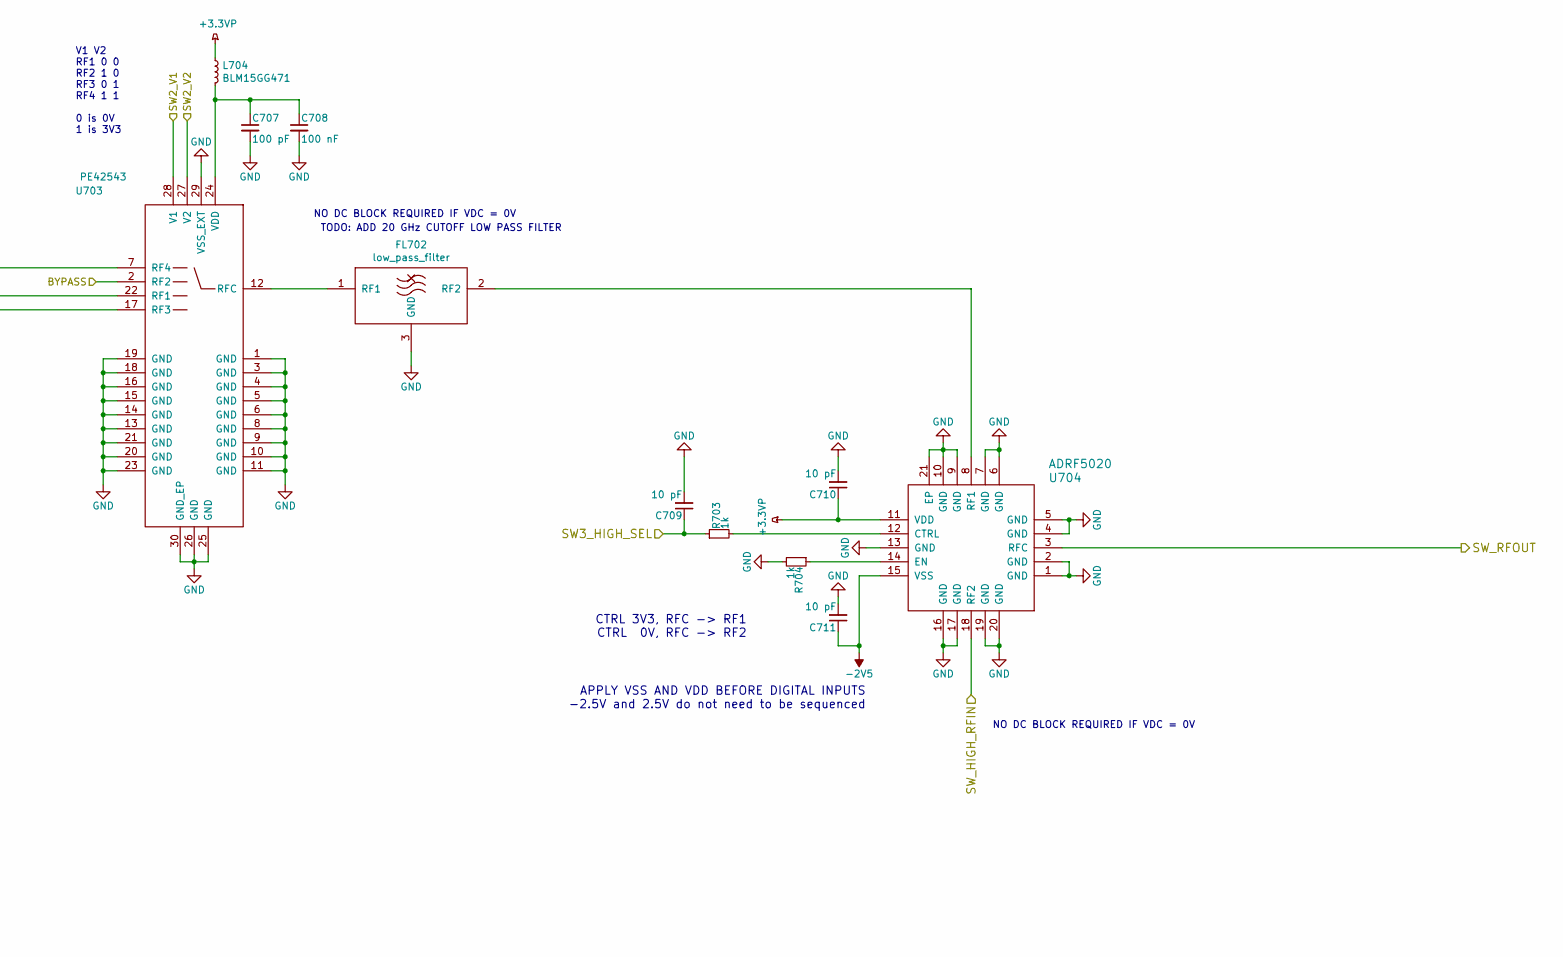
[picture p89: schematic bandselect_att.sch, part in row 1, column 2]

Parts:
C701, C704, C705, C708: 100 nF; C_0402_1005Metric
C702, C703, C706, C707: 100 pF; C_0402_1005Metric
C709, C710, C711: 10 pF; C_0402_1005Metric
FL701: low_pass_filter; stepped_lpf_8ghz_fr408
FL702: low_pass_filter; stepped_lpf_20ghz_fr408
J701, J702: Conn_Coaxial; SF2921-61345
L701, L702, L703, L704: BLM15GG471; L_0402_1005Metric
R701, R702: TBD; R_0402_1005Metric
R703, R704: 1k; R_0402_1005Metric
U701: ADMV8416; QFN-40-1EP_6x6mm_P0.5mm_EP4.6x4.6mm
U702, U703: PE42543; RFSW__PE42543A-X
U704: ADRF5020; ADRF5020BCCZN
U705: PAT1220-C-0DB; RF_Attenuator_Susumu_PAT1220

Connections:
+3.3VP: C710.1, L703.1, L704.1, U704.11 (VDD); also elsewhere on the board
+5VP: L701.1; also elsewhere on the board
-2V5: C711.1, U704.15 (VSS); also elsewhere on the board
-5V: L702.1; also elsewhere on the board
/FILT_BANDSEL: R701.2; also elsewhere on the board
/FILT_VTUNE: U701.19 (VTUNE); also elsewhere on the board
/SW1_V1: U702.28 (V1); also elsewhere on the board
/SW1_V2: U702.27 (V2); also elsewhere on the board
/SW2_V1: U703.28 (V1); also elsewhere on the board
/SW2_V2: U703.27 (V2); also elsewhere on the board
/SW3_HIGH_SEL: C709.1, R703.1; also elsewhere on the board
/filter_bank/BYPASS: U703.2 (RF2)
/highband/HIGHBAND_RFIN: U702.17 (RF3); also elsewhere on the board
/highband/HIGHBAND_RFOUT: U704.18 (RF2); also elsewhere on the board
/level_control/LEVEL_RFIN: U704.3 (RFC); also elsewhere on the board
/lowband/LOWBAND_RFOUT: FL701.1 (RF1); also elsewhere on the board
/midband/MIDBAND_RFOUT: U701.5 (RFIN); also elsewhere on the board
GND: C701.2, C702.2, C703.2, C704.2, C705.2, C706.2, C707.2, C708.2, C709.2, C710.2, C711.2, FL701.3 (GND), FL702.3 (GND), J701.2 (Ext), J702.2 (Ext), R702.2, R704.2, U701.1 (NC), U701.2 (NC), U701.3 (NC), U701.4 (GND), U701.6 (GND), U701.7 (NC), U701.8 (NC), U701.9 (NC), U701.10 (NC), U701.12 (GND), U701.14 (NC), U701.16 (GND), U701.17 (NC), U701.18 (GND), U701.20 (NC), U701.21 (NC), U701.22 (NC), U701.23 (NC), U701.24 (NC), U701.25 (GND), U701.27 (GND), U701.28 (NC), U701.29 (NC), U701.30 (NC), U701.31 (NC), U701.32 (NC), U701.33 (NC), U701.34 (NC), U701.35 (NC), U701.36 (NC), U701.37 (NC), U701.38 (NC), U701.39 (NC), U701.40 (NC), U701.41 (GND), U702.1 (GND), U702.3 (GND), U702.4 (GND), U702.5 (GND), U702.6 (GND), U702.8 (GND), U702.9 (GND), U702.10 (GND), U702.11 (GND), U702.13 (GND), U702.14 (GND), U702.15 (GND), U702.16 (GND), U702.18 (GND), U702.19 (GND), U702.20 (GND), U702.21 (GND), U702.23 (GND), U702.25 (GND), U702.26 (GND), U702.29 (VSS_EXT), U702.30 (GND_EP), U703.1 (GND), U703.3 (GND), U703.4 (GND), U703.5 (GND), U703.6 (GND), U703.8 (GND), U703.9 (GND), U703.10 (GND), U703.11 (GND), U703.13 (GND), U703.14 (GND), U703.15 (GND), U703.16 (GND), U703.18 (GND), U703.19 (GND), U703.20 (GND), U703.21 (GND), U703.23 (GND), U703.25 (GND), U703.26 (GND), U703.29 (VSS_EXT), U703.30 (GND_EP), U704.1 (GND), U704.2 (GND), U704.4 (GND), U704.5 (GND), U704.6 (GND), U704.7 (GND), U704.9 (GND), U704.10 (GND), U704.13 (GND), U704.16 (GND), U704.17 (GND), U704.19 (GND), U704.20 (GND), U704.21 (EP), U705.3; also elsewhere on the board
unnamed: C701.1, C702.1, L701.2, U701.13 (VDD)
unnamed: C703.1, C704.1, L702.2, U701.11 (VEE)
unnamed: C705.1, C706.1, L703.2, U702.24 (VDD)
unnamed: C707.1, C708.1, L704.2, U703.24 (VDD)
unnamed: FL701.2 (RF2), U705.1
unnamed: FL702.1 (RF1), U703.12 (RFC)
unnamed: FL702.2 (RF2), U704.8 (RF1)
unnamed: J701.1 (In), U702.7 (RF4)
unnamed: J702.1 (In), U703.7 (RF4)
unnamed: R701.1, R702.1, U701.15 (VCTL)
unnamed: R703.2, U704.12 (CTRL)
unnamed: R704.1, U704.14 (EN)
unnamed: U701.26 (RFOUT), U702.12 (RFC)
unnamed: U702.2 (RF2), U703.22 (RF1)
unnamed: U703.17 (RF3), U705.2

Notes on the sheet:
APPLY VSS AND VDD BEFORE DIGITAL INPUTS -2.5V and 2.5V do not need to be sequenced
CTRL 3V3, RFC -> RF1 CTRL 0V, RFC -> RF2
LPF, 8 GHz
TODO: ADD 20 GHz CUTOFF LOW PASS FILTER
NO DC BLOCK REQUIRED IF VDC = 0V
V1 V2 RF1 0 0 RF2 1 0 RF3 0 1 RF4 1 1 0 is 0V 1 is 3V3
SEQUENCE: 1 - VDD/VEE 2 - VCTL 3 - VTUNE
