loxodes/vna/hardware/vna_mm_synth/vna_mm_synth.kicad_pcb

## KiCad design hardware/vna_mm_synth/vna_mm_synth.kicad_pcb (continued)

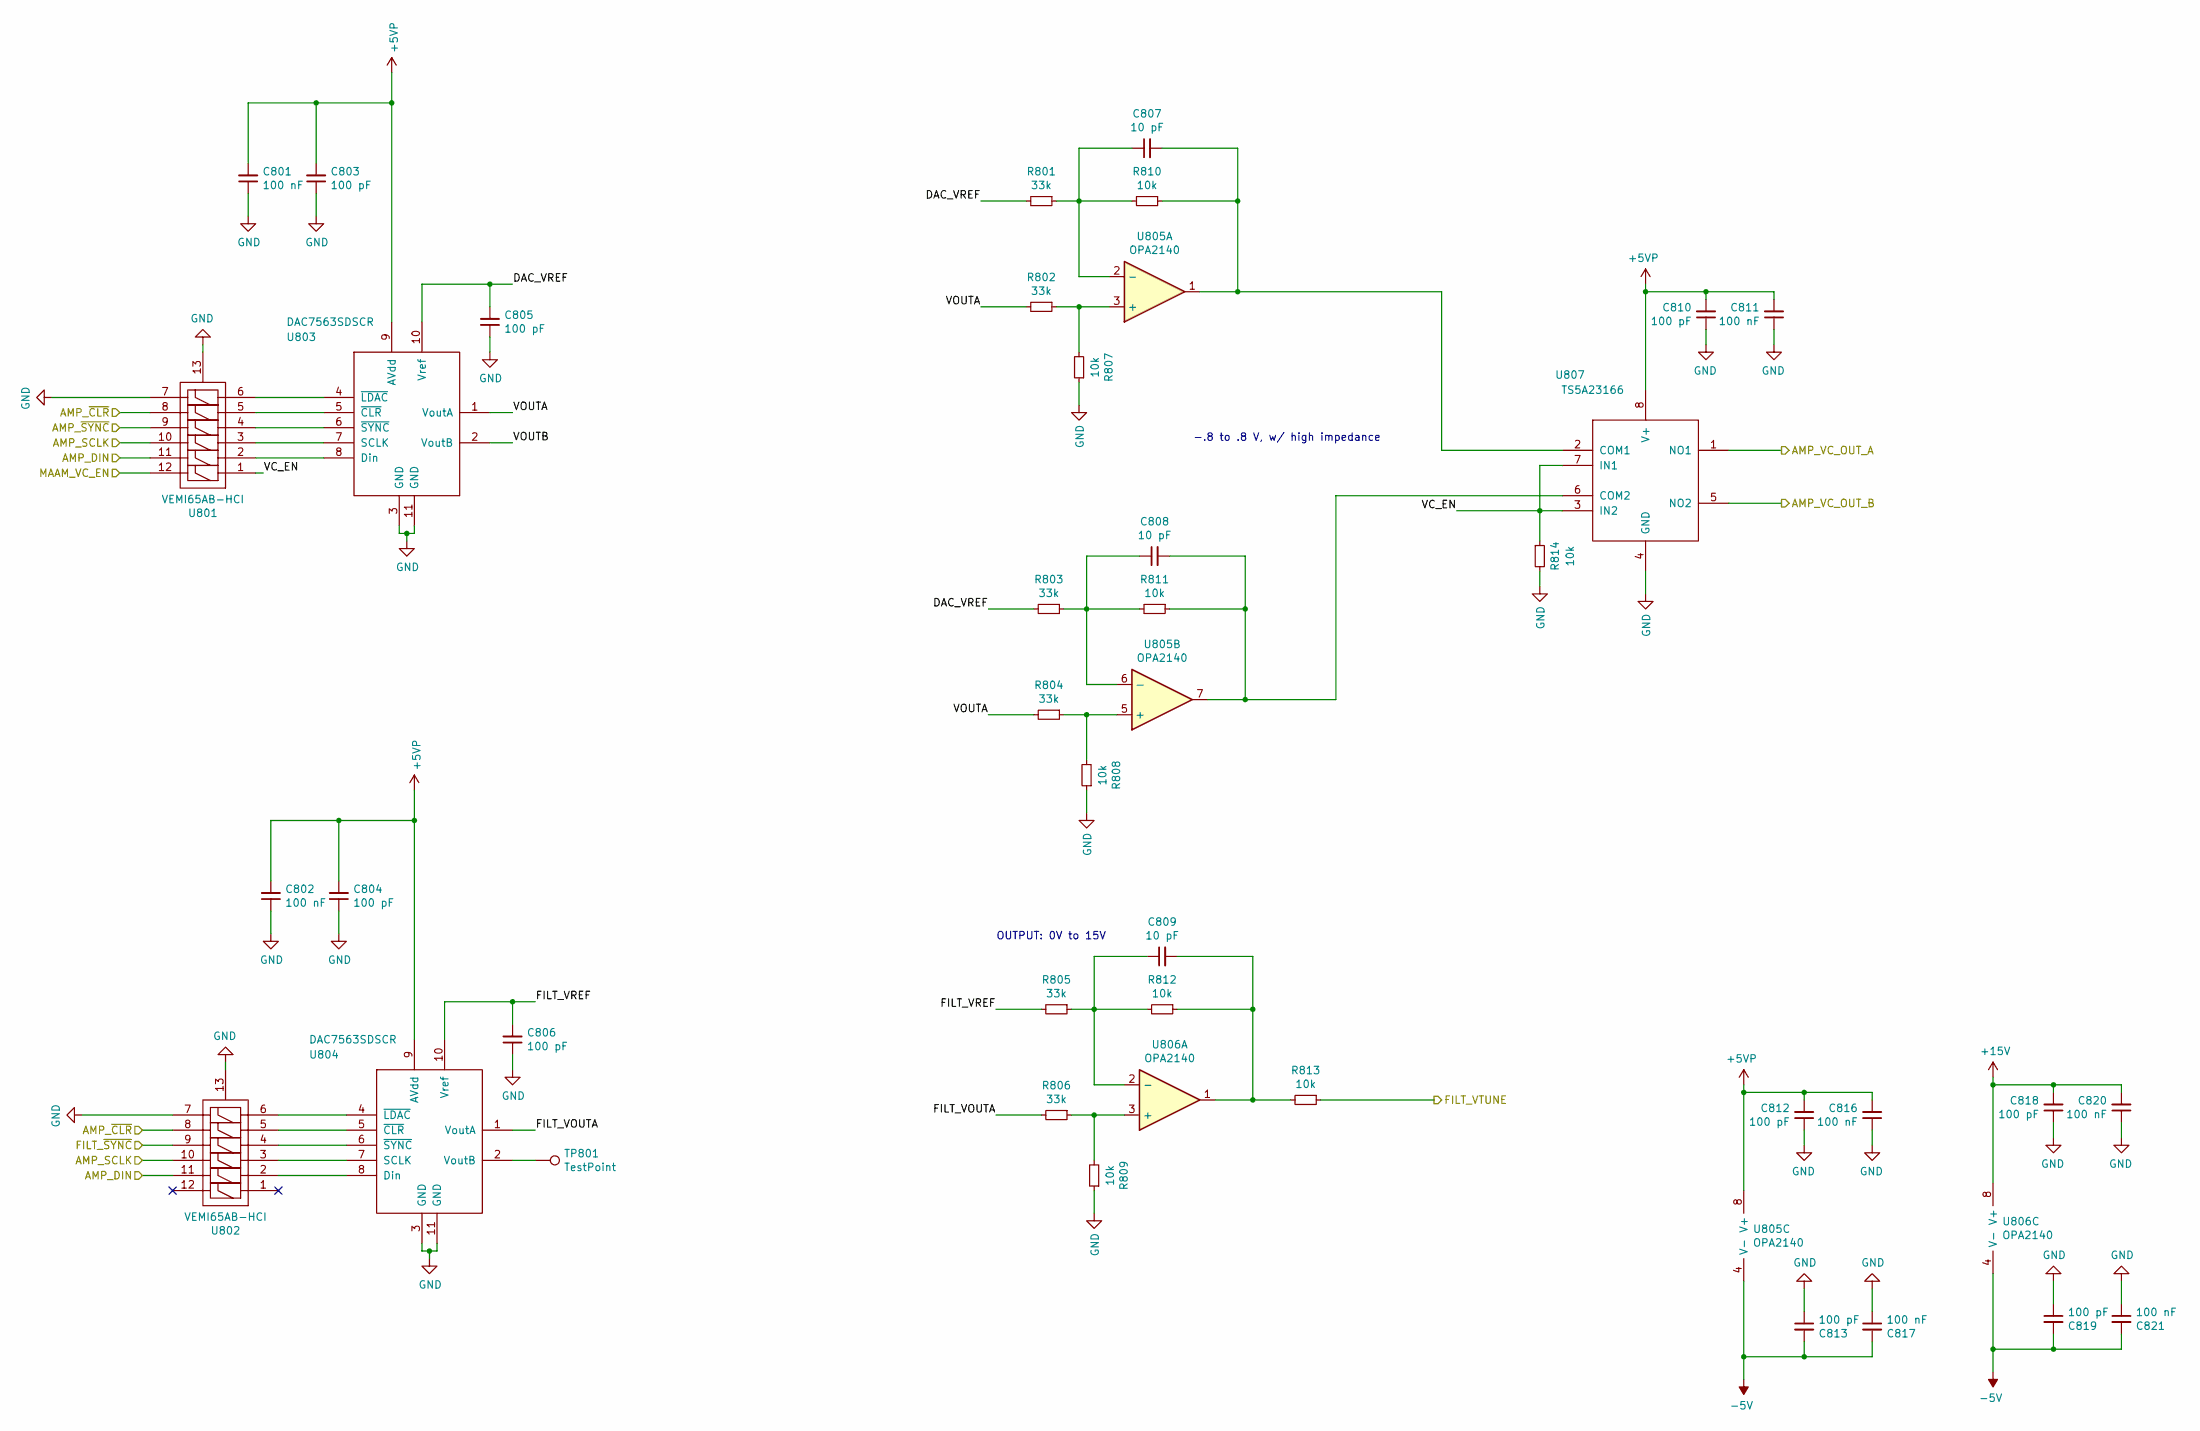
[picture p90: schematic amp_vc_control.sch]

Parts:
C801, C802, C811, C816, C817, C820, C821: 100 nF; C_0402_1005Metric
C803, C804, C805, C806, C810, C812, C813, C818, C819: 100 pF; C_0402_1005Metric
C807, C808, C809: 10 pF; C_0402_1005Metric
R801, R802, R803, R804, R805, R806: 33k; R_0402_1005Metric
R807, R808, R809, R810, R811, R812, R813, R814: 10k; R_0402_1005Metric
TP801: TestPoint; TestPoint_Pad_1.0x1.0mm
U801, U802: VEMI65AB-HCI; LLP2513-13L
U803, U804: DAC7563SDSCR; DFN-10_PWSON_N10_3x3mm_P0.5mm_EP1.05x2.55mm
U805, U806: OPA2140; MSOP-8_3x3mm_P0.65mm
U807: TS5A23166; VSSOP-8

Connections:
+5VP: C801.2, C802.2, C803.2, C804.2, C810.2, C811.2, C812.2, C816.2, U803.9 (AVdd), U804.9 (AVdd), U805.8 (V+), U807.8 (V+); also elsewhere on the board
+15V: C818.2, C820.2, U806.8 (V+); also elsewhere on the board
-5V: C813.2, C817.2, C819.2, C821.2, U805.4 (V-), U806.4 (V-); also elsewhere on the board
/AMP_SCK: U801.10, U802.10; also elsewhere on the board
/AMP_SDI: U801.11, U802.11; also elsewhere on the board
/AMP_VC_A: U807.1 (NO1); also elsewhere on the board
/AMP_VC_B: U807.5 (NO2); also elsewhere on the board
/AMP_~CLR: U801.8, U802.8; also elsewhere on the board
/AMP_~SYNC: U801.9; also elsewhere on the board
/FILT_VTUNE: R813.1; also elsewhere on the board
/FILT_~SYNC: U802.9; also elsewhere on the board
/MAAM_VC_EN: U801.12; also elsewhere on the board
/bias_control/DAC_VREF: C805.2, R801.2, R803.2, U803.10 (Vref)
/bias_control/FILT_VOUTA: R806.2, U804.1 (VoutA)
/bias_control/FILT_VREF: C806.2, R805.2, U804.10 (Vref)
/bias_control/VC_EN: R814.1, U801.1, U807.3 (IN2), U807.7 (IN1)
/bias_control/VOUTA: R802.2, R804.2, U803.1 (VoutA)
/bias_control/VOUTB: U803.2 (VoutB)
GND: C801.1, C802.1, C803.1, C804.1, C805.1, C806.1, C810.1, C811.1, C812.1, C813.1, C816.1, C817.1, C818.1, C819.1, C820.1, C821.1, R807.1, R808.1, R809.1, R814.2, U801.7, U801.13, U802.7, U802.13, U803.3 (GND), U803.11 (GND), U804.3 (GND), U804.11 (GND), U807.4 (GND); also elsewhere on the board
unnamed: C807.1, R801.1, R810.2, U805.2 (-)
unnamed: C807.2, R810.1, U805.1, U807.2 (COM1)
unnamed: C808.1, R803.1, R811.2, U805.6 (-)
unnamed: C808.2, R811.1, U805.7, U807.6 (COM2)
unnamed: C809.1, R805.1, R812.2, U806.2 (-)
unnamed: C809.2, R812.1, R813.2, U806.1
unnamed: R802.1, R807.2, U805.3 (+)
unnamed: R804.1, R808.2, U805.5 (+)
unnamed: R806.1, R809.2, U806.3 (+)
unnamed: TP801.1, U804.2 (VoutB)
unnamed: U801.2, U803.8 (Din)
unnamed: U801.3, U803.7 (SCLK)
unnamed: U801.4, U803.6 (~SYNC)
unnamed: U801.5, U803.5 (~CLR)
unnamed: U801.6, U803.4 (~LDAC)
unnamed: U802.2, U804.8 (Din)
unnamed: U802.3, U804.7 (SCLK)
unnamed: U802.4, U804.6 (~SYNC)
unnamed: U802.5, U804.5 (~CLR)
unnamed: U802.6, U804.4 (~LDAC)

Notes on the sheet:
-.8 to .8 V, w/ high impedance
OUTPUT: 0V to 15V

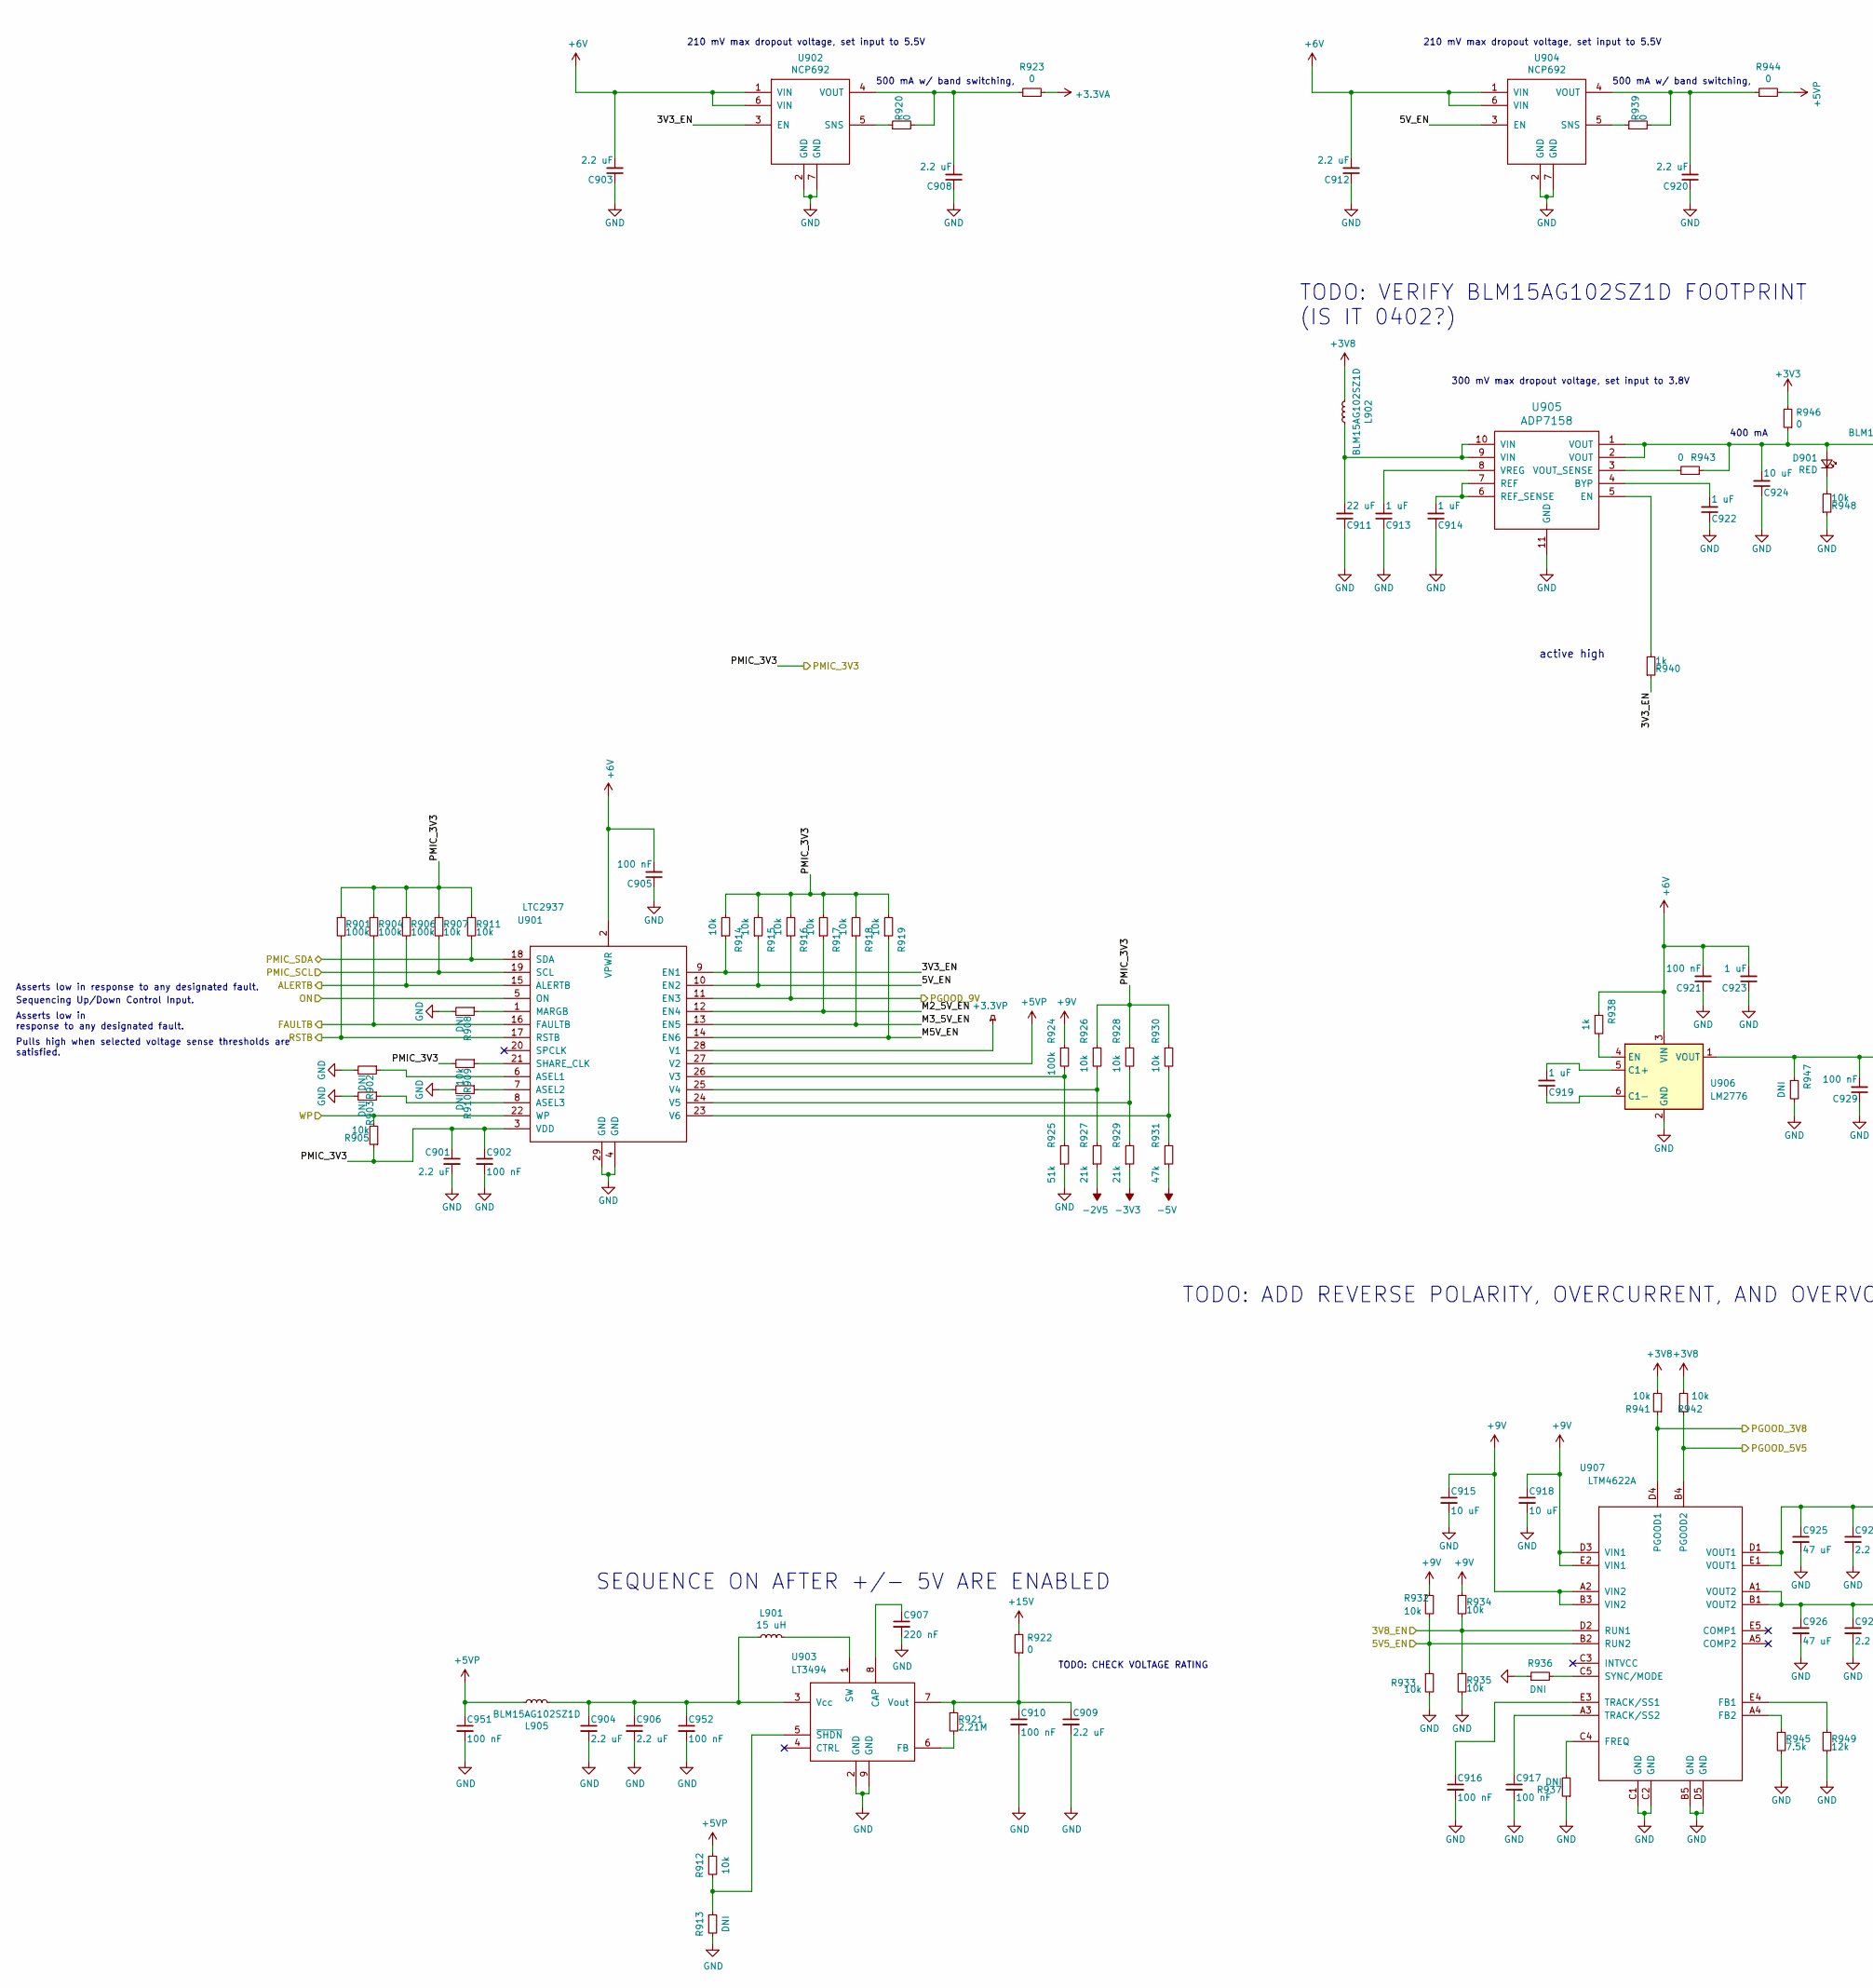
[picture p91: schematic amp_bias.sch, part in row 1, column 1]

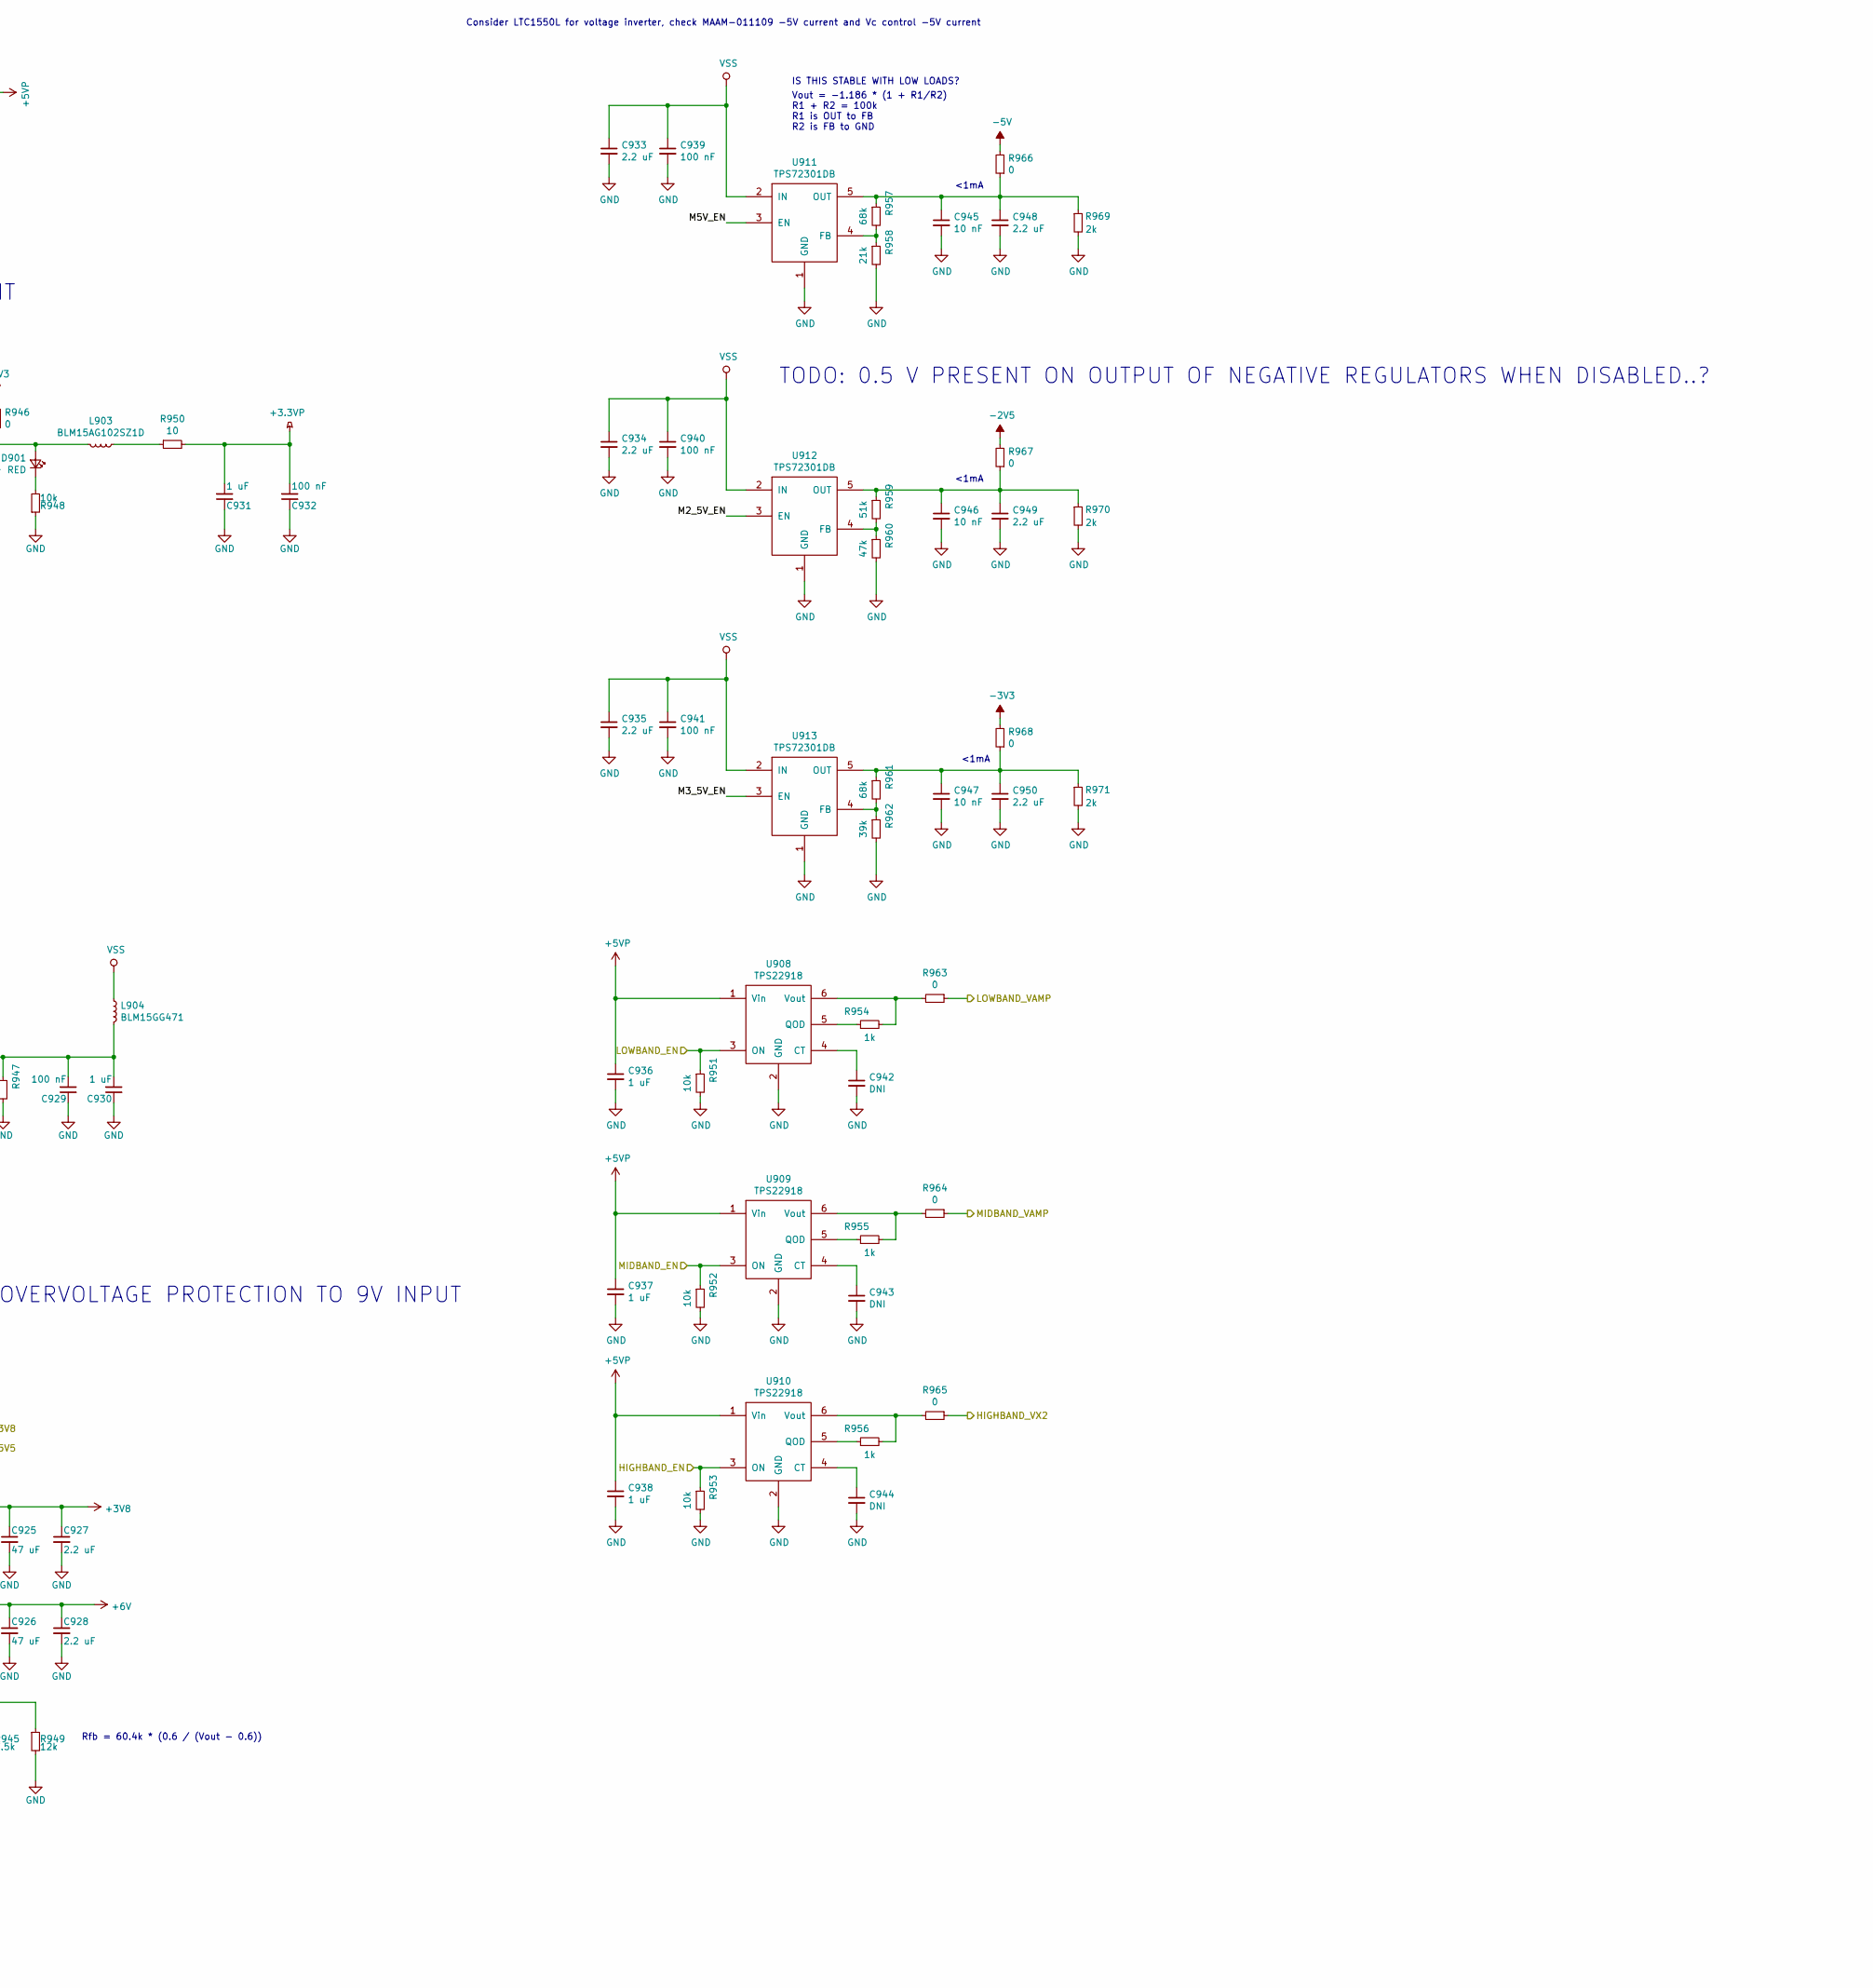
[picture p92: schematic amp_bias.sch, part in row 1, column 2]

Parts:
C901, C903, C904, C906, C908, C909, C912, C920, C927, C928, C933, C934, C935, C948, C949, C950: 2.2 uF; C_0603_1608Metric
C902, C905, C916, C917, C921, C929, C932, C939, C940, C941, C951, C952: 100 nF; C_0402_1005Metric
C907: 220 nF; C_0603_1608Metric
C910: 100 nF; C_0603_1608Metric
C911: 22 uF; C_0603_1608Metric
C913, C914, C919, C922, C923, C930, C931, C936, C937, C938: 1 uF; C_0402_1005Metric
C915, C918, C924: 10 uF; C_0603_1608Metric
C925, C926: 47 uF; C_1210_3225Metric
C942, C943, C944: DNI; C_0402_1005Metric
C945, C946, C947: 10 nF; C_0402_1005Metric
D901: RED; LED_0603_1608Metric
L901: 15 uH; L_1210_3225Metric
L902, L903, L905: BLM15AG102SZ1D; L_0402_1005Metric
L904: BLM15GG471; L_0402_1005Metric
R901, R904, R906, R924: 100k; R_0402_1005Metric
R902, R903, R908, R910, R913, R936, R937, R947: DNI; R_0402_1005Metric
R905, R907, R909, R911, R912, R914, R915, R916, R917, R918, R919, R926, R928, R930, R932, R933, R934, R935, R941, R942, R948, R951, R952, R953: 10k; R_0402_1005Metric
R920, R939, R943: 0; R_0402_1005Metric
R921: 2.21M; R_0402_1005Metric
R922, R923, R944, R946, R963, R964, R965, R966, R967, R968: 0; R_0603_1608Metric
R925, R959: 51k; R_0402_1005Metric
R927, R929, R958: 21k; R_0402_1005Metric
R931, R960: 47k; R_0402_1005Metric
R938, R940, R954, R955, R956: 1k; R_0402_1005Metric
R945: 7.5k; R_0402_1005Metric
R949: 12k; R_0402_1005Metric
R950: 10; R_0402_1005Metric
R957, R961: 68k; R_0402_1005Metric
R962: 39k; R_0402_1005Metric
R969, R970, R971: 2k; R_0402_1005Metric
U901: LTC2937; QFN-28_EP_6x5_Pitch0.5mm
U902, U904: NCP692; DFN-6-1EP_3x3mm_P0.95mm_EP1.7x2.6mm
U903: LT3494; DFN-8-1EP_2x3mm_P0.5mm_EP0.61x2.2mm
U905: ADP7158; DFN-10-1EP_3x3mm_P0.5mm_EP1.65x2.38mm
U906: LM2776; SOT-23-6
U907: LTM4622A; BGA-25_5x5_6.35x6.35mm
U908, U909, U910: TPS22918; SOT-23-6
U911, U912, U913: TPS72301DB; SOT-23-5

Connections:
+3.3VA: R923.2; also elsewhere on the board
+3.3VP: C931.2, C932.2, R950.2, U901.28 (V1); also elsewhere on the board
+3V3: R946.2; also elsewhere on the board
+3V8: C925.1, C927.1, L902.1, R941.2, R942.2, U907.D1 (VOUT1), U907.E1 (VOUT1); also elsewhere on the board
+5VP: C936.1, C937.1, C938.1, C951.1, L905.2, R912.1, R944.2, U901.27 (V2), U908.1 (Vin), U909.1 (Vin), U910.1 (Vin); also elsewhere on the board
+6V: C903.2, C905.2, C912.2, C921.2, C923.2, C926.1, C928.1, R938.1, U901.2 (VPWR), U902.1 (VIN), U902.6 (VIN), U904.1 (VIN), U904.6 (VIN), U906.3 (VIN), U907.A1 (VOUT2), U907.B1 (VOUT2)
+9V: C915.1, C918.1, R924.1, R932.1, R934.1, U907.A2 (VIN2), U907.B3 (VIN2), U907.D3 (VIN1), U907.E2 (VIN1); also elsewhere on the board
+15V: R922.2; also elsewhere on the board
-2V5: R927.1, R967.2; also elsewhere on the board
-3V3: R929.1, R968.2; also elsewhere on the board
-5V: R931.1, R966.2; also elsewhere on the board
/HIGHBAND_EN: R953.1, U910.3 (ON); also elsewhere on the board
/HIGHBAND_VX2: R965.1; also elsewhere on the board
/LOWBAND_EN: R951.1, U908.3 (ON); also elsewhere on the board
/LOWBAND_VAMP: R963.1; also elsewhere on the board
/MIDBAND_EN: R952.1, U909.3 (ON); also elsewhere on the board
/MIDBAND_VAMP: R964.1; also elsewhere on the board
/POW_ON: U901.5 (ON); also elsewhere on the board
/SCL: R907.2, U901.19 (SCL); also elsewhere on the board
/SDA: R911.2, U901.18 (SDA); also elsewhere on the board
/WP: R905.2, U901.22 (WP); also elsewhere on the board
/power/3V3_EN: R914.1, R940.1, U901.9 (EN1), U902.3 (EN)
/power/3V8_EN: R934.2, R935.1, U907.D2 (RUN1)
/power/5V5_EN: R932.2, R933.1, U907.B2 (RUN2)
/power/5V_EN: R915.1, U901.10 (EN2), U904.3 (EN)
/power/ALERTB: R906.2, U901.15 (ALERTB)
/power/FAULTB: R904.2, U901.16 (FAULTB)
/power/M2_5V_EN: R917.1, U901.12 (EN4), U912.3 (EN)
/power/M3_5V_EN: R918.1, U901.13 (EN5), U913.3 (EN)
/power/M5V_EN: R919.1, U901.14 (EN6), U911.3 (EN)
/power/PGOOD_3V8: R941.1, U907.D4 (PGOOD1)
/power/PGOOD_5V5: R942.1, U907.B4 (PGOOD2)
/power/PGOOD_9V: R916.1, U901.11 (EN3)
/power/PMIC_3V3: C901.1, C902.1, R901.1, R904.1, R905.1, R906.1, R907.1, R909.2, R911.1, R914.2, R915.2, R916.2, R917.2, R918.2, R919.2, R926.1, R928.1, R930.1, U901.3 (VDD)
/power/RSTB: R901.2, U901.17 (RSTB)
GND: C901.2, C902.2, C903.1, C904.2, C905.1, C906.2, C907.2, C908.1, C909.2, C910.2, C911.1, C912.1, C913.1, C914.1, C915.2, C916.2, C917.2, C918.2, C920.1, C921.1, C922.1, C923.1, C924.1, C925.2, C926.2, C927.2, C928.2, C929.1, C930.1, C931.1, C932.1, C933.2, C934.2, C935.2, C936.2, C937.2, C938.2, C939.2, C940.2, C941.2, C942.2, C943.2, C944.2, C945.2, C946.2, C947.2, C948.2, C949.2, C950.2, C951.2, C952.2, R902.2, R903.2, R908.2, R910.2, R913.2, R925.1, R933.2, R935.2, R936.1, R937.1, R945.2, R947.2, R948.1, R949.2, R951.2, R952.2, R953.2, R958.2, R960.2, R962.2, R969.2, R970.2, R971.2, U901.4 (GND), U901.29 (GND), U902.2 (GND), U902.7 (GND), U903.2 (GND), U903.9 (GND), U904.2 (GND), U904.7 (GND), U905.11 (GND), U906.2 (GND), U907.B5 (GND), U907.C1 (GND), U907.C2 (GND), U907.D5 (GND), U908.2 (GND), U909.2 (GND), U910.2 (GND), U911.1 (GND), U912.1 (GND), U913.1 (GND); also elsewhere on the board
unnamed: C904.1, C906.1, C952.1, L901.1, L905.1, U903.3 (Vcc)
unnamed: C907.1, U903.8 (CAP)
unnamed: C908.2, R920.2, R923.1, U902.4 (VOUT)
unnamed: C909.1, C910.1, R921.1, R922.1, U903.7 (Vout)
unnamed: C911.2, L902.2, U905.9 (VIN), U905.10 (VIN)
unnamed: C913.2, U905.8 (VREG)
unnamed: C914.2, U905.6 (REF_SENSE), U905.7 (REF)
unnamed: C916.1, U907.E3 (TRACK/SS1)
unnamed: C917.1, U907.A3 (TRACK/SS2)
unnamed: C919.1, U906.6 (C1-)
unnamed: C919.2, U906.5 (C1+)
unnamed: C920.2, R939.2, R944.1, U904.4 (VOUT)
unnamed: C922.2, U905.4 (BYP)
unnamed: C924.2, D901.2 (A), L903.1, R943.1, R946.1, U905.1 (VOUT), U905.2 (VOUT)
unnamed: C929.2, C930.2, L904.2, R947.1, U906.1 (VOUT)
unnamed: C942.1, U908.4 (CT)
unnamed: C943.1, U909.4 (CT)
unnamed: C944.1, U910.4 (CT)
unnamed: C945.1, C948.1, R957.1, R966.1, R969.1, U911.5 (OUT)
unnamed: C946.1, C949.1, R959.1, R967.1, R970.1, U912.5 (OUT)
unnamed: C947.1, C950.1, R961.1, R968.1, R971.1, U913.5 (OUT)
unnamed: D901.1 (K), R948.2
unnamed: L901.2, U903.1 (SW)
unnamed: L903.2, R950.1
unnamed: R902.1, U901.6 (ASEL1)
unnamed: R903.1, U901.8 (ASEL3)
unnamed: R908.1, U901.1 (MARGB)
unnamed: R909.1, U901.21 (SHARE_CLK)
unnamed: R910.1, U901.7 (ASEL2)
unnamed: R912.2, R913.1, U903.5 (~SHDN)
unnamed: R920.1, U902.5 (SNS)
unnamed: R921.2, U903.6 (FB)
unnamed: R924.2, R925.2, U901.26 (V3)
unnamed: R926.2, R927.2, U901.25 (V4)
unnamed: R928.2, R929.2, U901.24 (V5)
unnamed: R930.2, R931.2, U901.23 (V6)
unnamed: R936.2, U907.C5 (SYNC/MODE)
unnamed: R937.2, U907.C4 (FREQ)
unnamed: R938.2, U906.4 (EN)
unnamed: R939.1, U904.5 (SNS)
unnamed: R940.2, U905.5 (EN)
unnamed: R943.2, U905.3 (VOUT_SENSE)
unnamed: R945.1, U907.A4 (FB2)
unnamed: R949.1, U907.E4 (FB1)
unnamed: R954.1, U908.5 (QOD)
unnamed: R954.2, R963.2, U908.6 (Vout)
unnamed: R955.1, U909.5 (QOD)
unnamed: R955.2, R964.2, U909.6 (Vout)
unnamed: R956.1, U910.5 (QOD)
unnamed: R956.2, R965.2, U910.6 (Vout)
unnamed: R957.2, R958.1, U911.4 (FB)
unnamed: R959.2, R960.1, U912.4 (FB)
unnamed: R961.2, R962.1, U913.4 (FB)
VSS: C933.1, C934.1, C935.1, C939.1, C940.1, C941.1, L904.1, U911.2 (IN), U912.2 (IN), U913.2 (IN)

Notes on the sheet:
active high
<1mA
400 mA
IS THIS STABLE WITH LOW LOADS?
Vout = -1.186 * (1 + R1/R2) R1 + R2 = 100k R1 is OUT to FB R2 is FB to GND
Consider LTC1550L for voltage inverter, check MAAM-011109 -5V current and Vc control -5V current
500 mA w/ band switching,
300 mV max dropout voltage, set input to 3.8V
210 mV max dropout voltage, set input to 5.5V
Asserts low in response to any designated fault.
Sequencing Up/Down Control Input.
Asserts low in response to any designated fault.
Pulls high when selected voltage sense thresholds are satisfied.
Rfb = 60.4k * (0.6 / (Vout - 0.6))
TODO: CHECK VOLTAGE RATING
TODO: ADD REVERSE POLARITY, OVERCURRENT, AND OVERVOLTAGE PROTECTION TO 9V INPUT
SEQUENCE ON AFTER +/- 5V ARE ENABLED
TODO: 0.5 V PRESENT ON OUTPUT OF NEGATIVE REGULATORS WHEN DISABLED..?
TODO: VERIFY BLM15AG102SZ1D FOOTPRINT (IS IT 0402?)

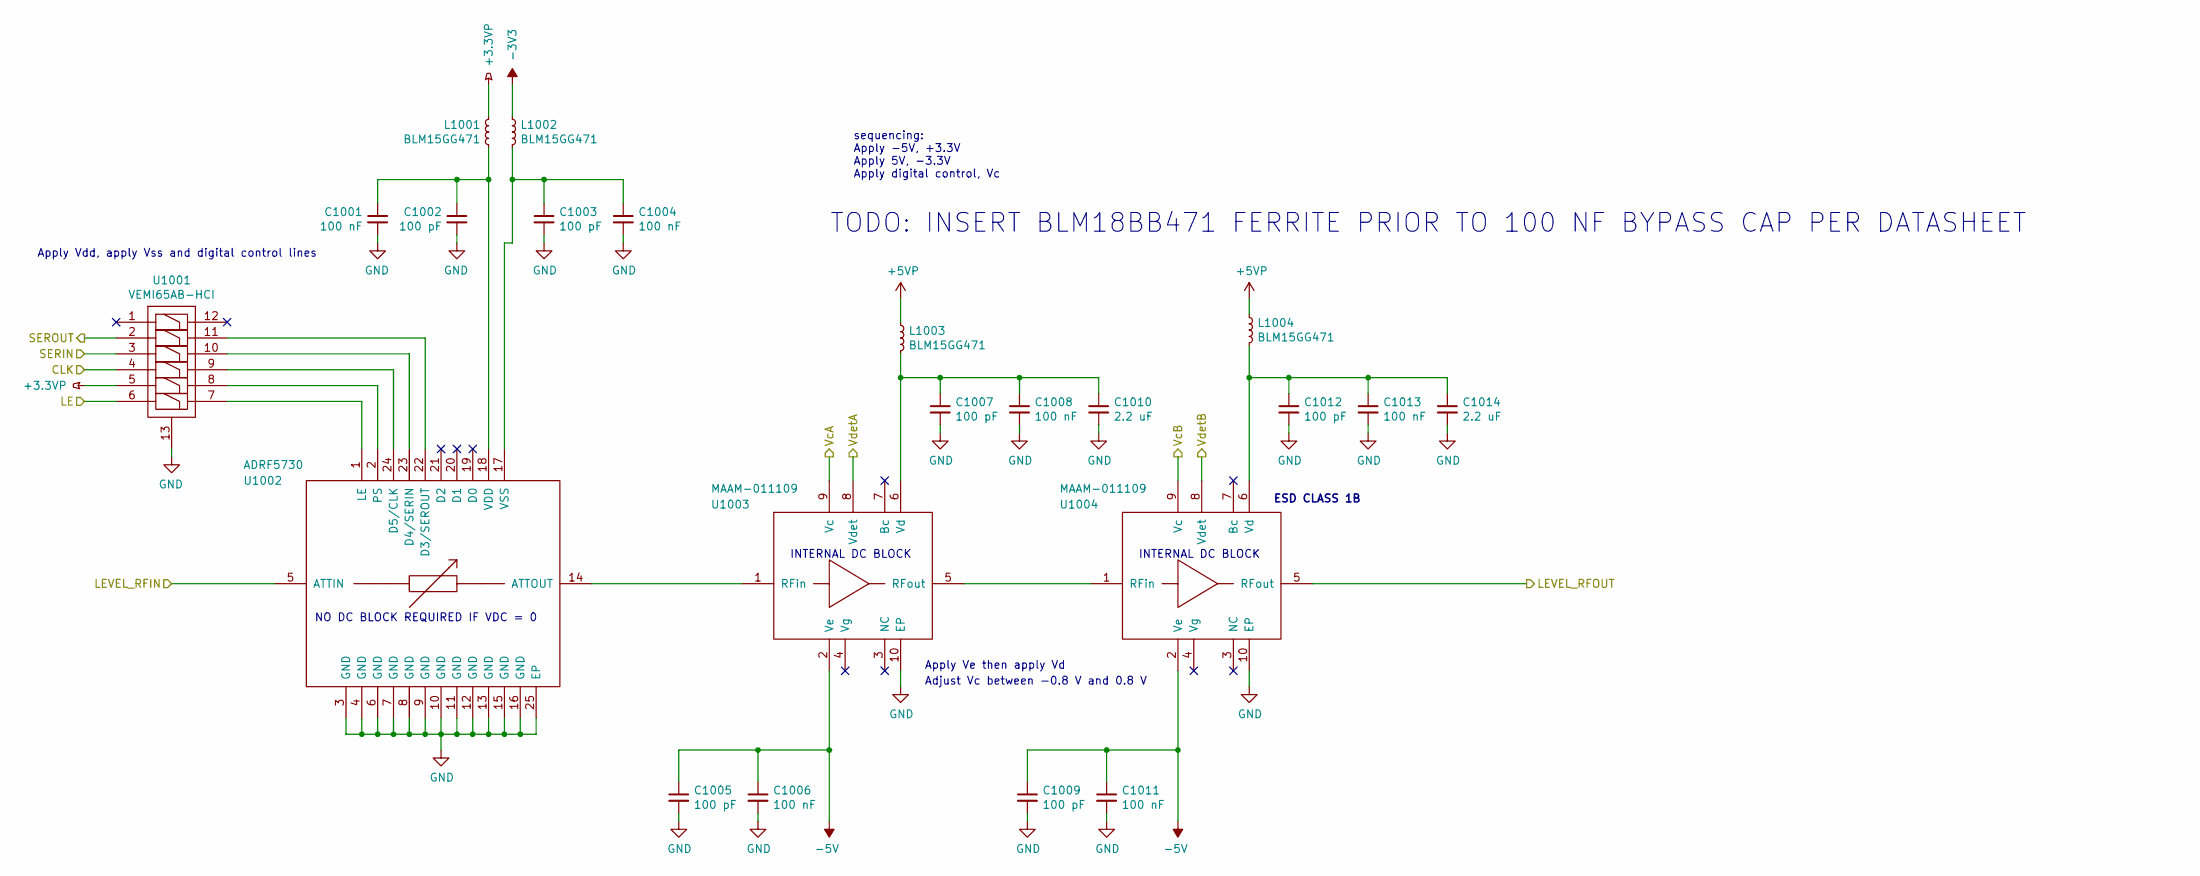
[picture p93: schematic level_control.sch]

Parts:
C1001, C1004, C1006, C1008, C1011, C1013: 100 nF; C_0402_1005Metric
C1002, C1003, C1005, C1007, C1009, C1012: 100 pF; C_0402_1005Metric
C1010, C1014: 2.2 uF; C_0603_1608Metric
L1001, L1002, L1003, L1004: BLM15GG471; L_0402_1005Metric
U1001: VEMI65AB-HCI; LLP2513-13L
U1002: ADRF5730; LGA-24_EP_4x4_Pitch0.5mm
U1003, U1004: MAAM-011109; MACOM_LGA9

Connections:
+3.3VP: L1001.1, U1001.5; also elsewhere on the board
+5VP: L1003.1, L1004.1; also elsewhere on the board
-3V3: L1002.1; also elsewhere on the board
-5V: C1005.1, C1006.1, C1009.1, C1011.1, U1003.2 (Ve), U1004.2 (Ve); also elsewhere on the board
/AMP_VC_A: U1003.9 (Vc); also elsewhere on the board
/AMP_VC_B: U1004.9 (Vc); also elsewhere on the board
/ATT_LE: U1001.6; also elsewhere on the board
/ATT_SCK: U1001.4; also elsewhere on the board
/ATT_SDI: U1001.3; also elsewhere on the board
/ATT_SDO: U1001.2; also elsewhere on the board
/VDET_A: U1003.8 (Vdet); also elsewhere on the board
/VDET_B: U1004.8 (Vdet); also elsewhere on the board
/level_control/LEVEL_RFIN: U1002.5 (ATTIN); also elsewhere on the board
/level_control/LEVEL_RFOUT: U1004.5 (RFout); also elsewhere on the board
GND: C1001.2, C1002.2, C1003.2, C1004.2, C1005.2, C1006.2, C1007.2, C1008.2, C1009.2, C1010.2, C1011.2, C1012.2, C1013.2, C1014.2, U1001.13, U1002.3 (GND), U1002.4 (GND), U1002.6 (GND), U1002.7 (GND), U1002.8 (GND), U1002.9 (GND), U1002.10 (GND), U1002.11 (GND), U1002.12 (GND), U1002.13 (GND), U1002.15 (GND), U1002.16 (GND), U1002.25 (EP), U1003.10 (EP), U1004.10 (EP); also elsewhere on the board
unnamed: C1001.1, C1002.1, L1001.2, U1002.18 (VDD)
unnamed: C1003.1, C1004.1, L1002.2, U1002.17 (VSS)
unnamed: C1007.1, C1008.1, C1010.1, L1003.2, U1003.6 (Vd)
unnamed: C1012.1, C1013.1, C1014.1, L1004.2, U1004.6 (Vd)
unnamed: U1001.7, U1002.1 (LE)
unnamed: U1001.8, U1002.2 (PS)
unnamed: U1001.9, U1002.24 (D5/CLK)
unnamed: U1001.10, U1002.23 (D4/SERIN)
unnamed: U1001.11, U1002.22 (D3/SEROUT)
unnamed: U1002.14 (ATTOUT), U1003.1 (RFin)
unnamed: U1003.5 (RFout), U1004.1 (RFin)

Notes on the sheet:
NO DC BLOCK REQUIRED IF VDC = 0
INTERNAL DC BLOCK
ESD CLASS 1B
Apply Ve then apply Vd
Adjust Vc between -0.8 V and 0.8 V
Apply Vdd, apply Vss and digital control lines
sequencing: Apply -5V, +3.3V Apply 5V, -3.3V Apply digital control, Vc
TODO: INSERT BLM18BB471 FERRITE PRIOR TO 100 NF BYPASS CAP PER DATASHEET
