loxodes/vna/hardware/vna_mm_synth/vna_mm_synth.kicad_pcb

## KiCad design hardware/vna_mm_synth/vna_mm_synth.kicad_pcb (continued)

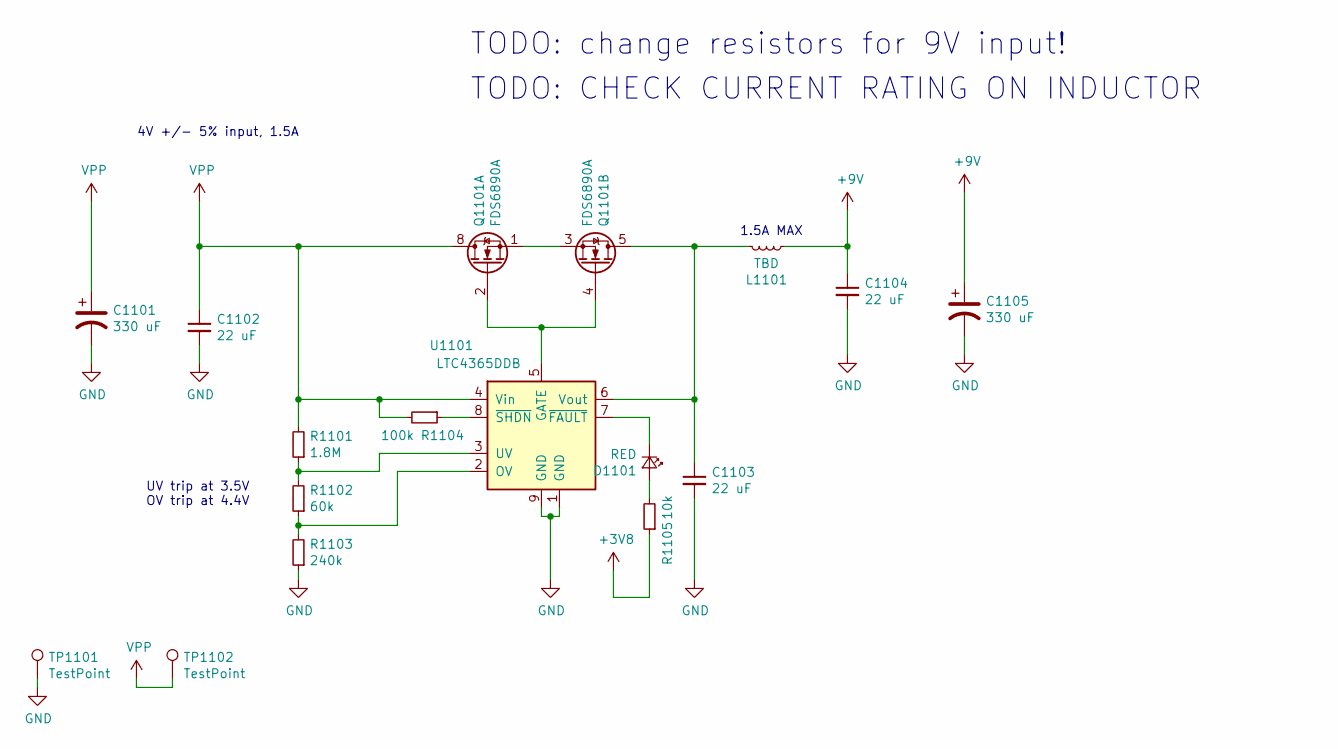
[picture p94: schematic input_protection.sch]

Parts:
C1101, C1105: 330 uF; CP_Elec_6.3x5.9
C1102, C1103, C1104: 22 uF; C_0805_2012Metric
D1101: RED; LED_0603_1608Metric
L1101: TBD; L_0805_2012Metric
Q1101: FDS6890A; SOIC-8_3.9x4.9mm_P1.27mm
R1101: 1.8M; R_0402_1005Metric
R1102: 60k; R_0402_1005Metric
R1103: 240k; R_0402_1005Metric
R1104: 100k; R_0402_1005Metric
R1105: 10k; R_0402_1005Metric
TP1101, TP1102: TestPoint; TURRET_MILLMAX_2101
U1101: LTC4365DDB; DFN-8-1EP_2x3mm_P0.5mm_EP0.61x2.2mm

Connections:
+3V8: R1105.1; also elsewhere on the board
+9V: C1104.1, C1105.1, L1101.1; also elsewhere on the board
GND: C1101.2, C1102.2, C1103.2, C1104.2, C1105.2, R1103.1, TP1101.1, U1101.1 (GND), U1101.9 (GND); also elsewhere on the board
unnamed: C1103.1, L1101.2, Q1101.5 (D2), Q1101.6 (D2), U1101.6 (Vout)
unnamed: D1101.1 (K), U1101.7 (~FAULT)
unnamed: D1101.2 (A), R1105.2
unnamed: Q1101.1 (S1), Q1101.3 (S2)
unnamed: Q1101.2 (G1), Q1101.4 (G2), U1101.5 (GATE)
unnamed: R1101.1, R1102.2, U1101.3 (UV)
unnamed: R1102.1, R1103.2, U1101.2 (OV)
unnamed: R1104.1, U1101.8 (~SHDN)
VPP: C1101.1, C1102.1, Q1101.7 (D1), Q1101.8 (D1), R1101.2, R1104.2, TP1102.1, U1101.4 (Vin); also elsewhere on the board

Notes on the sheet:
1.5A MAX
4V +/- 5% input, 1.5A
UV trip at 3.5V OV trip at 4.4V
TODO: change resistors for 9V input!
TODO: CHECK CURRENT RATING ON INDUCTOR

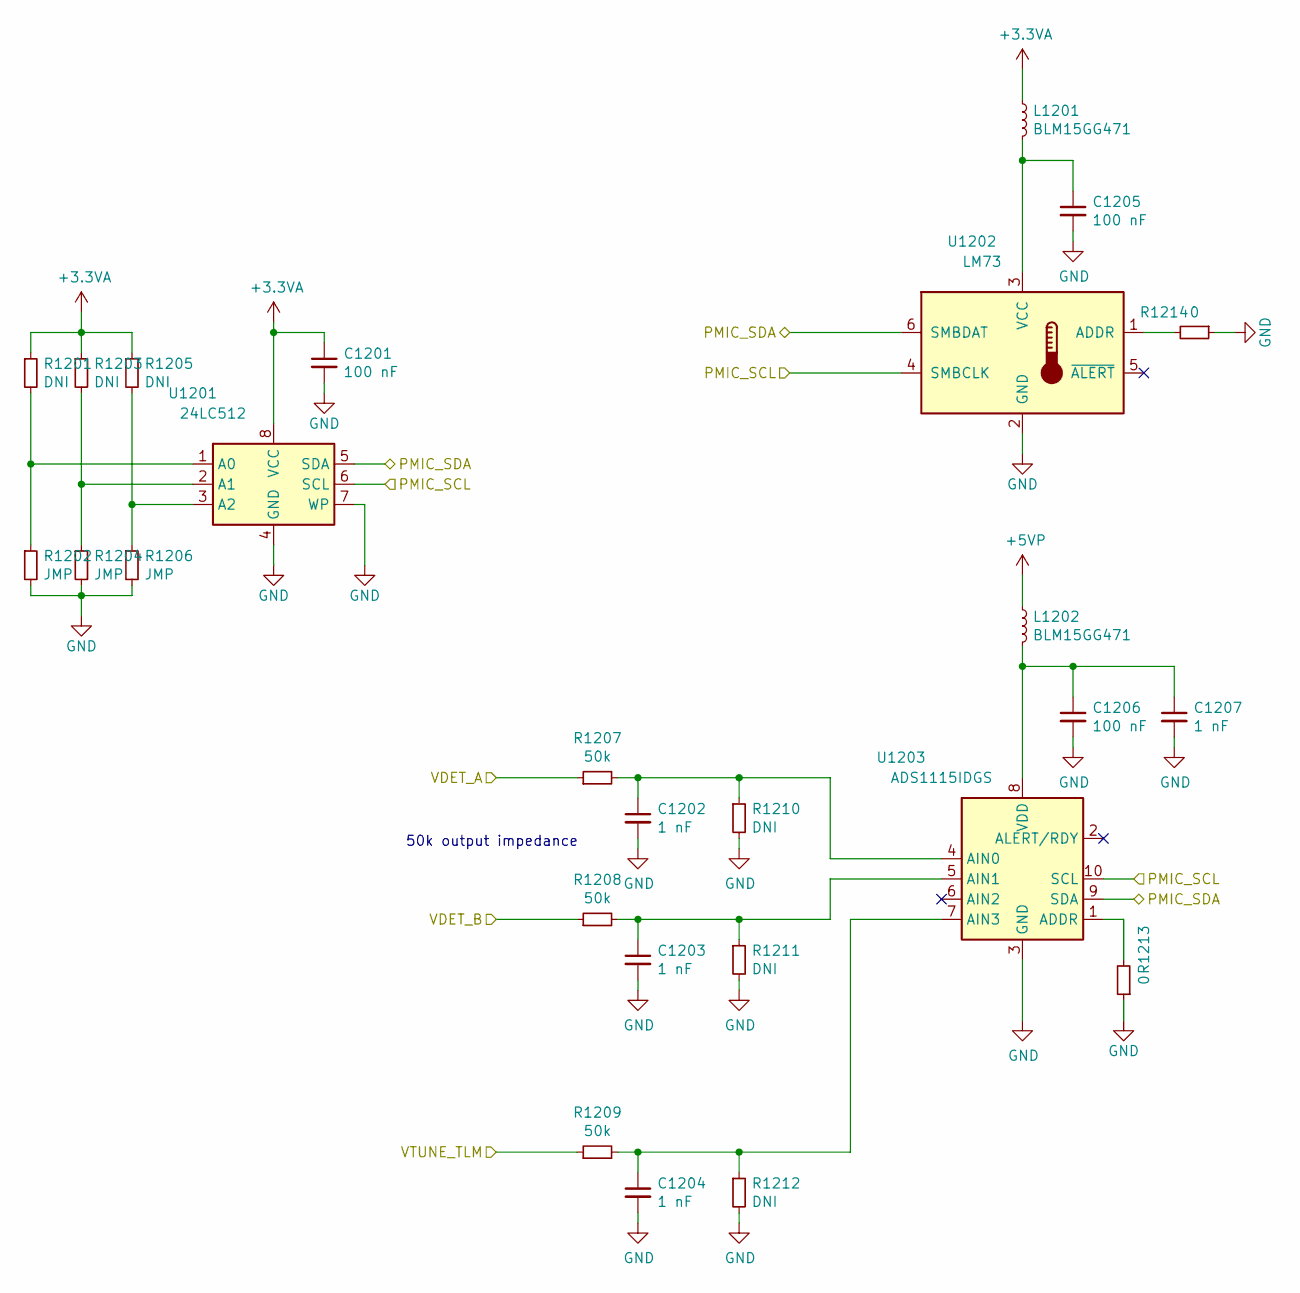
[picture p95: schematic monitor.sch]

Parts:
C1201, C1205, C1206: 100 nF; C_0402_1005Metric
C1202, C1203, C1204, C1207: 1 nF; C_0402_1005Metric
L1201, L1202: BLM15GG471; L_0402_1005Metric
R1201, R1203, R1205, R1210, R1211, R1212: DNI; R_0402_1005Metric
R1202, R1204, R1206: JMP; R_0402_1005Metric
R1207, R1208, R1209: 50k; R_0402_1005Metric
R1213, R1214: 0; R_0402_1005Metric
U1201: 24LC512; TSSOP-8_4.4x3mm_P0.65mm
U1202: LM73; SOT-23-6
U1203: ADS1115IDGS; TSSOP-10_3x3mm_P0.5mm

Connections:
+3.3VA: C1201.1, L1201.1, R1201.1, R1203.1, R1205.1, U1201.8 (VCC); also elsewhere on the board
+5VP: L1202.1; also elsewhere on the board
/SCL: U1201.6 (SCL), U1202.4 (SMBCLK), U1203.10 (SCL); also elsewhere on the board
/SDA: U1201.5 (SDA), U1202.6 (SMBDAT), U1203.9 (SDA); also elsewhere on the board
/VDET_A: R1207.1; also elsewhere on the board
/VDET_B: R1208.1; also elsewhere on the board
/VTUNE_TLM: R1209.1; also elsewhere on the board
GND: C1201.2, C1202.2, C1203.2, C1204.2, C1205.2, C1206.2, C1207.2, R1202.2, R1204.2, R1206.2, R1210.2, R1211.2, R1212.2, R1213.1, R1214.1, U1201.4 (GND), U1201.7 (WP), U1202.2 (GND), U1203.3 (GND); also elsewhere on the board
unnamed: C1202.1, R1207.2, R1210.1, U1203.4 (AIN0)
unnamed: C1203.1, R1208.2, R1211.1, U1203.5 (AIN1)
unnamed: C1204.1, R1209.2, R1212.1, U1203.7 (AIN3)
unnamed: C1205.1, L1201.2, U1202.3 (VCC)
unnamed: C1206.1, C1207.1, L1202.2, U1203.8 (VDD)
unnamed: R1201.2, R1202.1, U1201.1 (A0)
unnamed: R1203.2, R1204.1, U1201.2 (A1)
unnamed: R1205.2, R1206.1, U1201.3 (A2)
unnamed: R1213.2, U1203.1 (ADDR)
unnamed: R1214.2, U1202.1 (ADDR)

Notes on the sheet:
50k output impedance

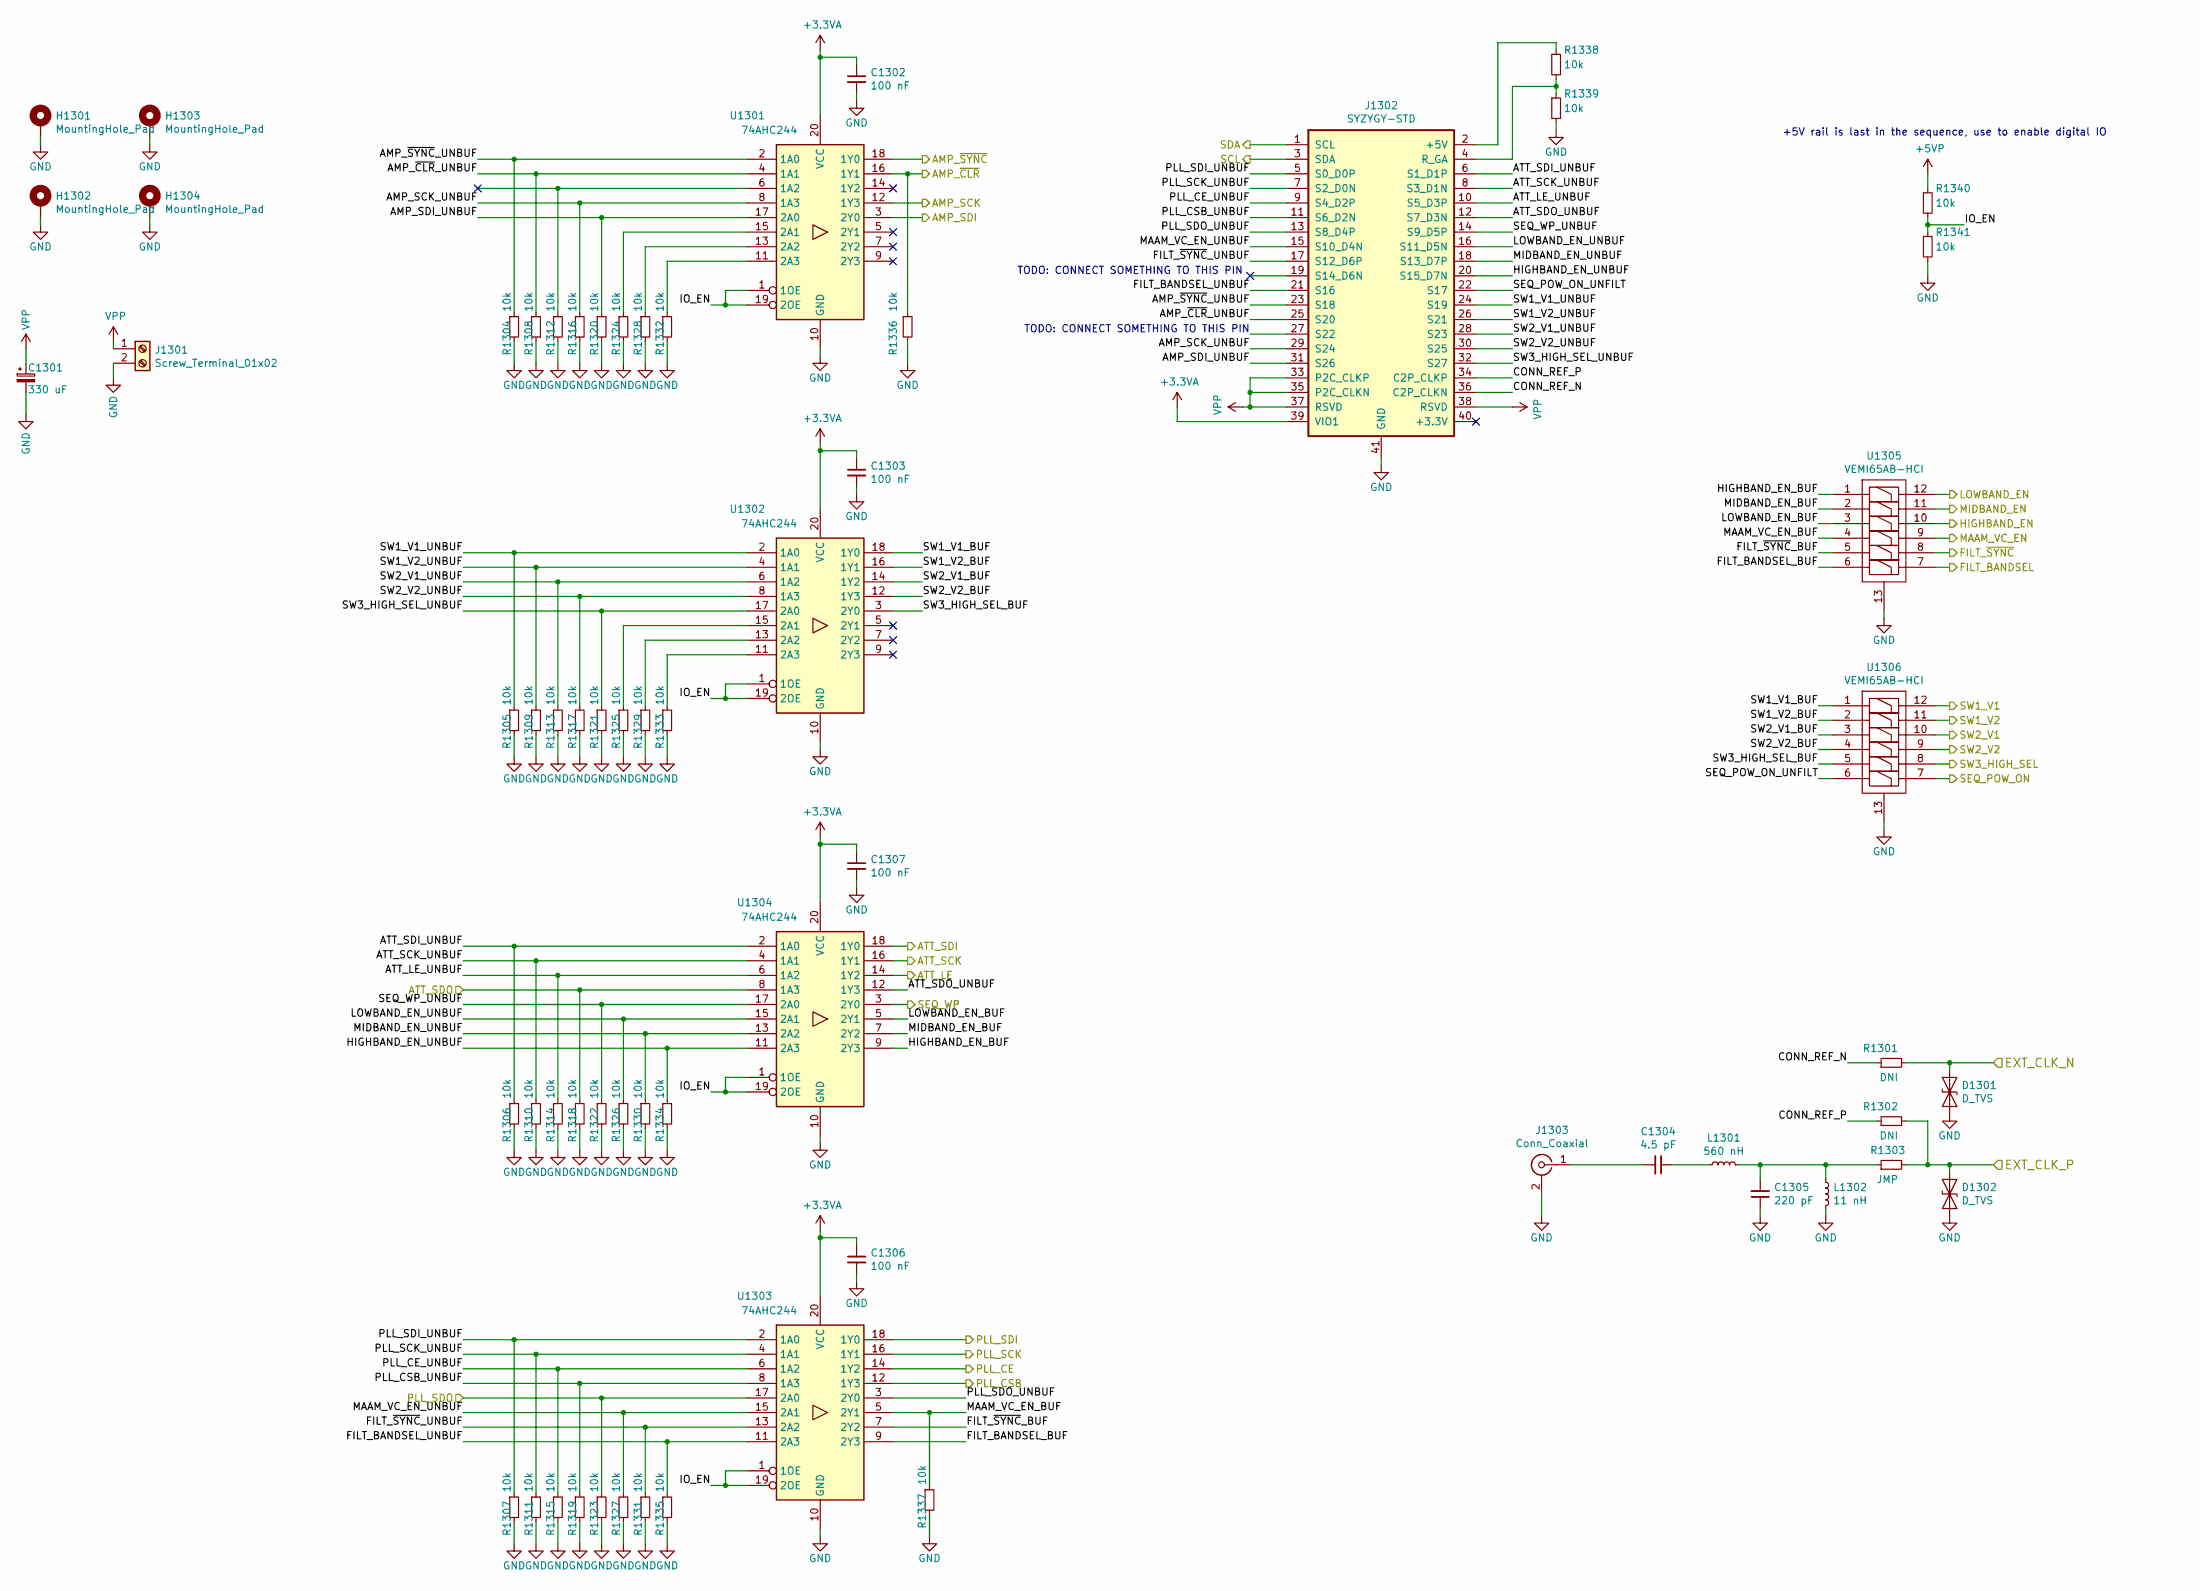
[picture p96: schematic conn_power.sch]

Parts:
C1301: 330 uF; CP_Elec_6.3x5.8
C1302, C1303, C1306, C1307: 100 nF; C_0402_1005Metric
C1304: 4.5 pF; C_0402_1005Metric
C1305: 220 pF; C_0402_1005Metric
D1301, D1302: D_TVS; D_0603_1608Metric
H1301, H1302, H1303, H1304: MountingHole_Pad; MountingHole_2.2mm_M2_Pad_Via
J1301: Screw_Terminal_01x02; TerminalBlock_Phoenix_MPT-0,5-2-2.54_1x02_P2.54mm_Horizontal
J1302: SYZYGY-STD; SYZYGY_standard_carrier
J1303: Conn_Coaxial; SMA_Amphenol_132289_EdgeMount
L1301: 560 nH; L_0603_1608Metric
L1302: 11 nH; L_0402_1005Metric
R1301, R1302: DNI; R_0402_1005Metric
R1303: JMP; R_0402_1005Metric
R1304, R1305, R1306, R1307, R1308, R1309, R1310, R1311, R1312, R1313, R1314, R1315, R1316, R1317, R1318, R1319, R1320, R1321, R1322, R1323, R1324, R1325, R1326, R1327, R1328, R1329, R1330, R1331, R1332, R1333, R1334, R1335, R1336, R1337, R1338, R1339, R1340, R1341: 10k; R_0402_1005Metric
U1301, U1302, U1303, U1304: 74AHC244; TSSOP-20_4.4x6.5mm_P0.65mm
U1305, U1306: VEMI65AB-HCI; LLP2513-13L

Connections:
+3.3VA: C1302.1, C1303.1, C1306.1, C1307.1, J1302.39 (VIO1), U1301.20 (VCC), U1302.20 (VCC), U1303.20 (VCC), U1304.20 (VCC); also elsewhere on the board
+5VP: R1340.1; also elsewhere on the board
/AMP_SCK: U1301.12 (1Y3); also elsewhere on the board
/AMP_SDI: U1301.3 (2Y0); also elsewhere on the board
/AMP_~CLR: R1336.1, U1301.16 (1Y1); also elsewhere on the board
/AMP_~SYNC: U1301.18 (1Y0); also elsewhere on the board
/ATT_LE: U1304.14 (1Y2); also elsewhere on the board
/ATT_SCK: U1304.16 (1Y1); also elsewhere on the board
/ATT_SDI: U1304.18 (1Y0); also elsewhere on the board
/ATT_SDO: R1318.1, U1304.8 (1A3); also elsewhere on the board
/FILT_BANDSEL: U1305.7; also elsewhere on the board
/FILT_~SYNC: U1305.8; also elsewhere on the board
/HIGHBAND_EN: U1305.10; also elsewhere on the board
/LOWBAND_EN: U1305.12; also elsewhere on the board
/MAAM_VC_EN: U1305.9; also elsewhere on the board
/MIDBAND_EN: U1305.11; also elsewhere on the board
/PLL_CE: U1303.14 (1Y2); also elsewhere on the board
/PLL_CSB: U1303.12 (1Y3); also elsewhere on the board
/PLL_SCK: U1303.16 (1Y1); also elsewhere on the board
/PLL_SDI: U1303.18 (1Y0); also elsewhere on the board
/PLL_SDO: R1323.1, U1303.17 (2A0); also elsewhere on the board
/POW_ON: U1306.7; also elsewhere on the board
/SCL: J1302.3 (SDA); also elsewhere on the board
/SDA: J1302.1 (SCL); also elsewhere on the board
/SW1_V1: U1306.12; also elsewhere on the board
/SW1_V2: U1306.11; also elsewhere on the board
/SW2_V1: U1306.10; also elsewhere on the board
/SW2_V2: U1306.9; also elsewhere on the board
/SW3_HIGH_SEL: U1306.8; also elsewhere on the board
/WP: U1304.3 (2Y0); also elsewhere on the board
/conn_power/AMP_SCK_UNBUF: J1302.29 (S24), R1316.1, U1301.8 (1A3)
/conn_power/AMP_SDI_UNBUF: J1302.31 (S26), R1320.1, U1301.17 (2A0)
/conn_power/AMP_~CLR~_UNBUF: J1302.25 (S20), R1308.1, U1301.4 (1A1)
/conn_power/AMP_~SYNC~_UNBUF: J1302.23 (S18), R1304.1, U1301.2 (1A0)
/conn_power/ATT_LE_UNBUF: J1302.10 (S5_D3P), R1314.1, U1304.6 (1A2)
/conn_power/ATT_SCK_UNBUF: J1302.8 (S3_D1N), R1310.1, U1304.4 (1A1)
/conn_power/ATT_SDI_UNBUF: J1302.6 (S1_D1P), R1306.1, U1304.2 (1A0)
/conn_power/ATT_SDO_UNBUF: J1302.12 (S7_D3N), U1304.12 (1Y3)
/conn_power/CONN_REF_N: J1302.36 (C2P_CLKN), R1301.1
/conn_power/CONN_REF_P: J1302.34 (C2P_CLKP), R1302.1
/conn_power/EXT_CLK_N: D1301.1 (A1), R1301.2; also elsewhere on the board
/conn_power/EXT_CLK_P: D1302.1 (A1), R1302.2, R1303.2; also elsewhere on the board
/conn_power/FILT_BANDSEL_BUF: U1303.9 (2Y3), U1305.6
/conn_power/FILT_BANDSEL_UNBUF: J1302.21 (S16), R1335.1, U1303.11 (2A3)
/conn_power/FILT_~SYNC~_BUF: U1303.7 (2Y2), U1305.5
/conn_power/FILT_~SYNC~_UNBUF: J1302.17 (S12_D6P), R1331.1, U1303.13 (2A2)
/conn_power/HIGHBAND_EN_BUF: U1304.9 (2Y3), U1305.1
/conn_power/HIGHBAND_EN_UNBUF: J1302.20 (S15_D7N), R1334.1, U1304.11 (2A3)
/conn_power/IO_EN: R1340.2, R1341.1, U1301.1 (1OE), U1301.19 (2OE), U1302.1 (1OE), U1302.19 (2OE), U1303.1 (1OE), U1303.19 (2OE), U1304.1 (1OE), U1304.19 (2OE)
/conn_power/LOWBAND_EN_BUF: U1304.5 (2Y1), U1305.3
/conn_power/LOWBAND_EN_UNBUF: J1302.16 (S11_D5N), R1326.1, U1304.15 (2A1)
/conn_power/MAAM_VC_EN_BUF: R1337.1, U1303.5 (2Y1), U1305.4
/conn_power/MAAM_VC_EN_UNBUF: J1302.15 (S10_D4N), R1327.1, U1303.15 (2A1)
/conn_power/MIDBAND_EN_BUF: U1304.7 (2Y2), U1305.2
/conn_power/MIDBAND_EN_UNBUF: J1302.18 (S13_D7P), R1330.1, U1304.13 (2A2)
/conn_power/PLL_CE_UNBUF: J1302.9 (S4_D2P), R1315.1, U1303.6 (1A2)
/conn_power/PLL_CSB_UNBUF: J1302.11 (S6_D2N), R1319.1, U1303.8 (1A3)
/conn_power/PLL_SCK_UNBUF: J1302.7 (S2_D0N), R1311.1, U1303.4 (1A1)
/conn_power/PLL_SDI_UNBUF: J1302.5 (S0_D0P), R1307.1, U1303.2 (1A0)
/conn_power/PLL_SDO_UNBUF: J1302.13 (S8_D4P), U1303.3 (2Y0)
/conn_power/SEQ_POW_ON_UNFILT: J1302.22 (S17), U1306.6
/conn_power/SEQ_WP_UNBUF: J1302.14 (S9_D5P), R1322.1, U1304.17 (2A0)
/conn_power/SW1_V1_BUF: U1302.18 (1Y0), U1306.1
/conn_power/SW1_V1_UNBUF: J1302.24 (S19), R1305.1, U1302.2 (1A0)
/conn_power/SW1_V2_BUF: U1302.16 (1Y1), U1306.2
/conn_power/SW1_V2_UNBUF: J1302.26 (S21), R1309.1, U1302.4 (1A1)
/conn_power/SW2_V1_BUF: U1302.14 (1Y2), U1306.3
/conn_power/SW2_V1_UNBUF: J1302.28 (S23), R1313.1, U1302.6 (1A2)
/conn_power/SW2_V2_BUF: U1302.12 (1Y3), U1306.4
/conn_power/SW2_V2_UNBUF: J1302.30 (S25), R1317.1, U1302.8 (1A3)
/conn_power/SW3_HIGH_SEL_BUF: U1302.3 (2Y0), U1306.5
/conn_power/SW3_HIGH_SEL_UNBUF: J1302.32 (S27), R1321.1, U1302.17 (2A0)
GND: C1301.2, C1302.2, C1303.2, C1305.1, C1306.2, C1307.2, D1301.2 (A2), D1302.2 (A2), H1301.1, H1302.1, H1303.1, H1304.1, J1301.2, J1302.41 (GND), J1303.2 (Ext), L1302.2, R1304.2, R1305.2, R1306.2, R1307.2, R1308.2, R1309.2, R1310.2, R1311.2, R1312.2, R1313.2, R1314.2, R1315.2, R1316.2, R1317.2, R1318.2, R1319.2, R1320.2, R1321.2, R1322.2, R1323.2, R1324.2, R1325.2, R1326.2, R1327.2, R1328.2, R1329.2, R1330.2, R1331.2, R1332.2, R1333.2, R1334.2, R1335.2, R1336.2, R1337.2, R1339.2, R1341.2, U1301.10 (GND), U1302.10 (GND), U1303.10 (GND), U1304.10 (GND), U1305.13, U1306.13; also elsewhere on the board
unnamed: C1304.1, L1301.1
unnamed: C1304.2, J1303.1 (In)
unnamed: C1305.2, L1301.2, L1302.1, R1303.1
unnamed: J1302.2 (+5V), R1338.1
unnamed: J1302.4 (R_GA), R1338.2, R1339.1
unnamed: R1312.1, U1301.6 (1A2)
unnamed: R1324.1, U1301.15 (2A1)
unnamed: R1325.1, U1302.15 (2A1)
unnamed: R1328.1, U1301.13 (2A2)
unnamed: R1329.1, U1302.13 (2A2)
unnamed: R1332.1, U1301.11 (2A3)
unnamed: R1333.1, U1302.11 (2A3)
VPP: C1301.1, J1301.1, J1302.33 (P2C_CLKP), J1302.35 (P2C_CLKN), J1302.37 (RSVD), J1302.38 (RSVD); also elsewhere on the board

Notes on the sheet:
+5V rail is last in the sequence, use to enable digital IO
TODO: CONNECT SOMETHING TO THIS PIN

Board: 6 copper layers, 435 parts (0 on the bottom side), 301 nets, no tracks yet.
