loxodes/vna/hardware/vna_mm_ref/vna_mm_ref.kicad_pcb

## KiCad design hardware/vna_mm_ref/vna_mm_ref.kicad_pcb (2020-04-20)

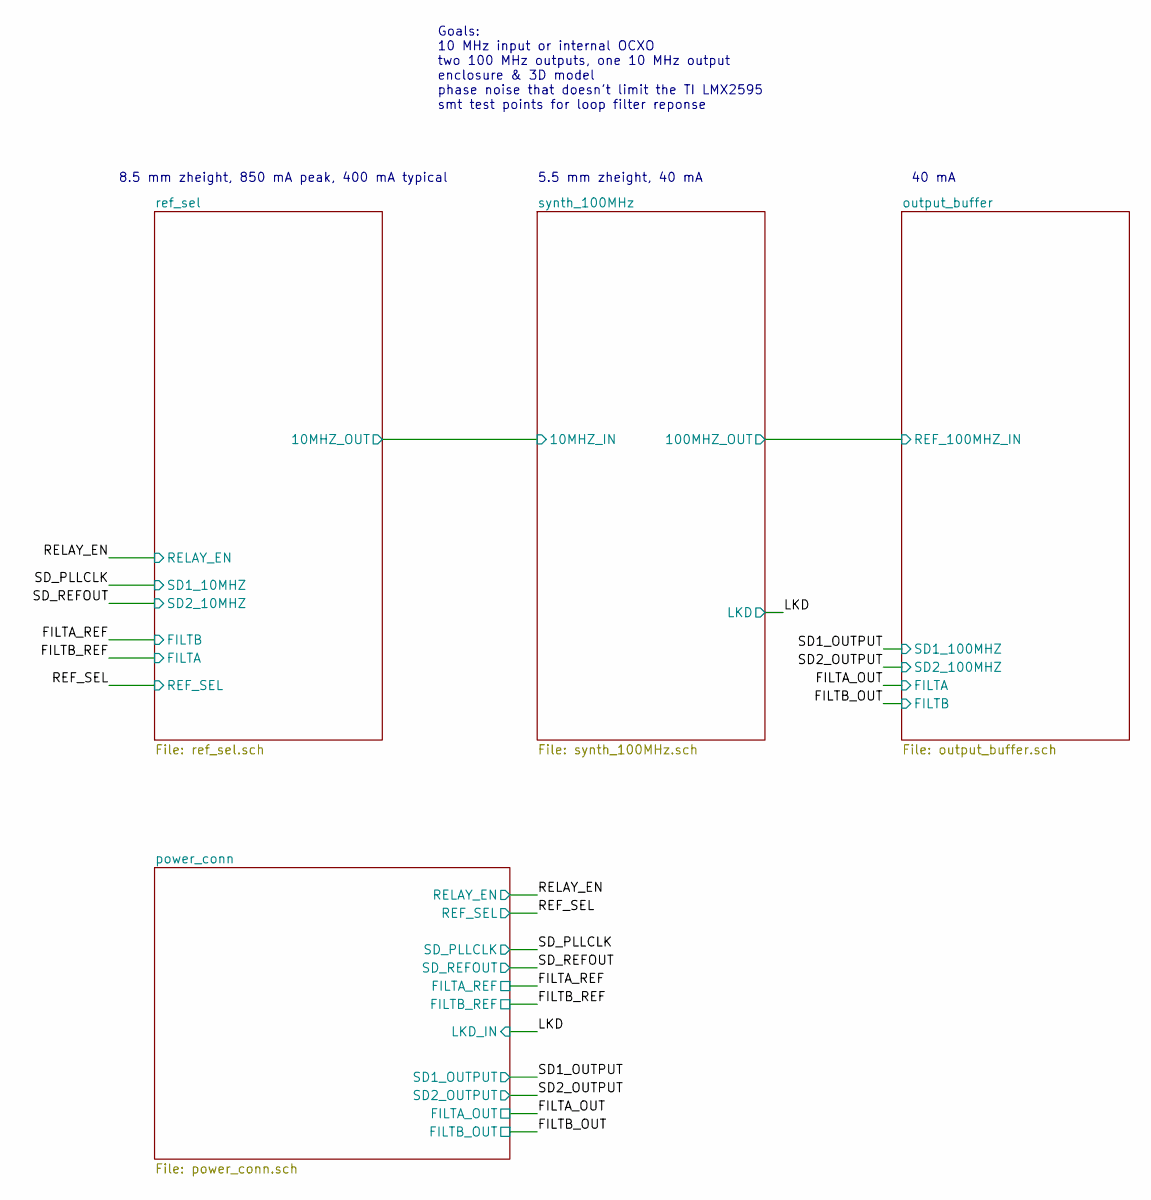
[picture p97: schematic vna_mm_ref.sch]

Notes on the sheet:
Goals: 10 MHz input or internal OCXO two 100 MHz outputs, one 10 MHz output enclosure & 3D model phase noise that doesn't limit the TI LMX2595 smt test points for loop filter reponse
8.5 mm zheight, 850 mA peak, 400 mA typical
5.5 mm zheight, 40 mA
40 mA

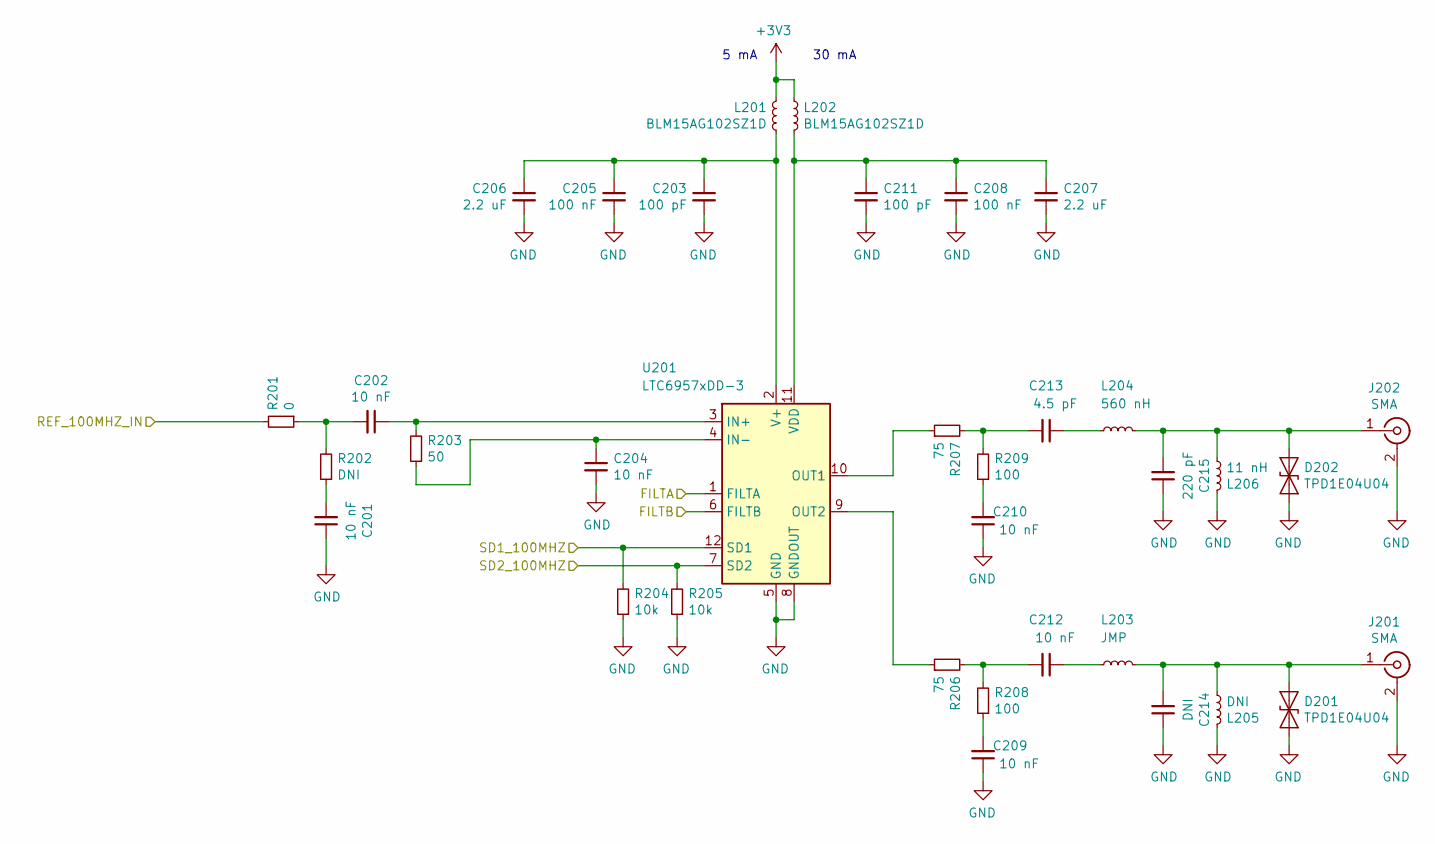
[picture p98: schematic output_buffer.sch]

Parts:
C201, C202, C204, C209, C210, C212: 10 nF; C_0402_1005Metric
C203, C211: 100 pF; C_0402_1005Metric
C205, C208: 100 nF; C_0402_1005Metric
C206, C207: 2.2 uF; C_0603_1608Metric
C213: 4.5 pF; C_0402_1005Metric
C214: DNI; C_0402_1005Metric
C215: 220 pF; C_0402_1005Metric
D201, D202: TPD1E04U04; D_0402_1005Metric
J201, J202: SMA; SMA_Amphenol_132289_EdgeMount
L201, L202: BLM15AG102SZ1D; L_0402_1005Metric
L203: JMP; L_0805_2012Metric
L204: 560 nH; L_0805_2012Metric
L205: DNI; L_0402_1005Metric
L206: 11 nH; L_0402_1005Metric
R201: 0; R_0402_1005Metric
R202: DNI; R_0402_1005Metric
R203: 50; R_0402_1005Metric
R204, R205: 10k; R_0402_1005Metric
R206, R207: 75; R_0402_1005Metric
R208, R209: 100; R_0402_1005Metric
U201: LTC6957xDD-3; DFN-12-1EP_3x3mm_P0.45mm_EP1.66x2.38mm

Connections:
+3V3: L201.1, L202.1; also elsewhere on the board
/FILTA_OUT: U201.1 (FILTA); also elsewhere on the board
/FILTB_OUT: U201.6 (FILTB); also elsewhere on the board
/SD1_OUTPUT: R204.2, U201.12 (SD1); also elsewhere on the board
/SD2_OUTPUT: R205.2, U201.7 (SD2); also elsewhere on the board
/synth_100MHz/100MHZ_OUT: R201.2; also elsewhere on the board
GND: C201.1, C203.2, C204.2, C205.2, C206.2, C207.2, C208.2, C209.1, C210.1, C211.2, C214.1, C215.1, D201.2 (A2), D202.2 (A2), J201.2 (Ext), J202.2 (Ext), L205.1, L206.1, R204.1, R205.1, U201.5 (GND), U201.8 (GNDOUT), U201.13 (GND); also elsewhere on the board
unnamed: C201.2, R202.1
unnamed: C202.1, R203.2, U201.3 (IN+)
unnamed: C202.2, R201.1, R202.2
unnamed: C203.1, C205.1, C206.1, L201.2, U201.2 (V+)
unnamed: C204.1, R203.1, U201.4 (IN-)
unnamed: C207.1, C208.1, C211.1, L202.2, U201.11 (VDD)
unnamed: C209.2, R208.1
unnamed: C210.2, R209.1
unnamed: C212.1, L203.2
unnamed: C212.2, R206.2, R208.2
unnamed: C213.1, L204.2
unnamed: C213.2, R207.2, R209.2
unnamed: C214.2, D201.1 (A1), J201.1 (In), L203.1, L205.2
unnamed: C215.2, D202.1 (A1), J202.1 (In), L204.1, L206.2
unnamed: R206.1, U201.9 (OUT2)
unnamed: R207.1, U201.10 (OUT1)

Notes on the sheet:
5 mA
30 mA

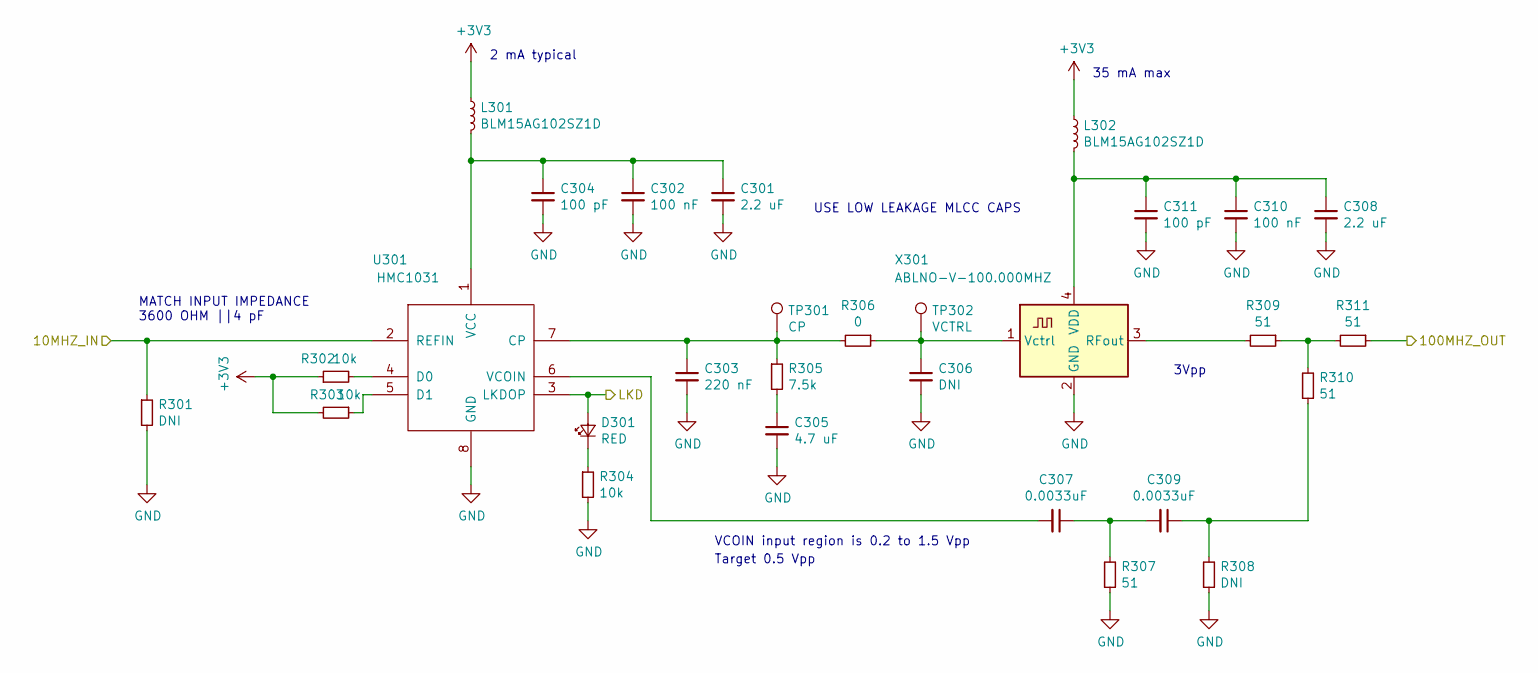
[picture p99: schematic synth_100MHz.sch]

Parts:
C301, C308: 2.2 uF; C_0603_1608Metric
C302, C310: 100 nF; C_0402_1005Metric
C303: 220 nF; C_0402_1005Metric
C304, C311: 100 pF; C_0402_1005Metric
C305: 4.7 uF; C_0603_1608Metric
C306: DNI; C_0402_1005Metric
C307, C309: 0.0033uF; C_0402_1005Metric
D301: RED; LED_0603_1608Metric
L301, L302: BLM15AG102SZ1D; L_0402_1005Metric
R301, R308: DNI; R_0402_1005Metric
R302, R303, R304: 10k; R_0402_1005Metric
R305: 7.5k; R_0402_1005Metric
R306: 0; R_0402_1005Metric
R307, R309, R310, R311: 51; R_0402_1005Metric
TP301: CP; TestPoint_Keystone_5015_Micro-Minature
TP302: VCTRL; TestPoint_Keystone_5015_Micro-Minature
U301: HMC1031; MSOP-8_3x3mm_P0.65mm
X301: ABLNO-V-100.000MHZ; Oscillator_SMD_Abracon_ABLNO

Connections:
+3V3: L301.1, L302.1, R302.1, R303.2; also elsewhere on the board
/LKD: D301.2 (A), U301.3 (LKDOP); also elsewhere on the board
/synth_100MHz/10MHZ_IN: R301.1, U301.2 (REFIN); also elsewhere on the board
/synth_100MHz/100MHZ_OUT: R311.1; also elsewhere on the board
GND: C301.2, C302.2, C303.2, C304.2, C305.2, C306.2, C308.2, C310.2, C311.2, R301.2, R304.2, R307.1, R308.1, U301.8 (GND), X301.2 (GND); also elsewhere on the board
unnamed: C301.1, C302.1, C304.1, L301.2, U301.1 (VCC)
unnamed: C303.1, R305.1, R306.2, TP301.1, U301.7 (CP)
unnamed: C305.1, R305.2
unnamed: C306.1, R306.1, TP302.1, X301.1 (Vctrl)
unnamed: C307.1, C309.2, R307.2
unnamed: C307.2, U301.6 (VCOIN)
unnamed: C308.1, C310.1, C311.1, L302.2, X301.4 (VDD)
unnamed: C309.1, R308.2, R310.1
unnamed: D301.1 (K), R304.1
unnamed: R302.2, U301.4 (D0)
unnamed: R303.1, U301.5 (D1)
unnamed: R309.1, R310.2, R311.2
unnamed: R309.2, X301.3 (RFout)

Notes on the sheet:
USE LOW LEAKAGE MLCC CAPS
2 mA typical
35 mA max
MATCH INPUT IMPEDANCE 3600 OHM ||4 pF
VCOIN input region is 0.2 to 1.5 Vpp
3Vpp
Target 0.5 Vpp

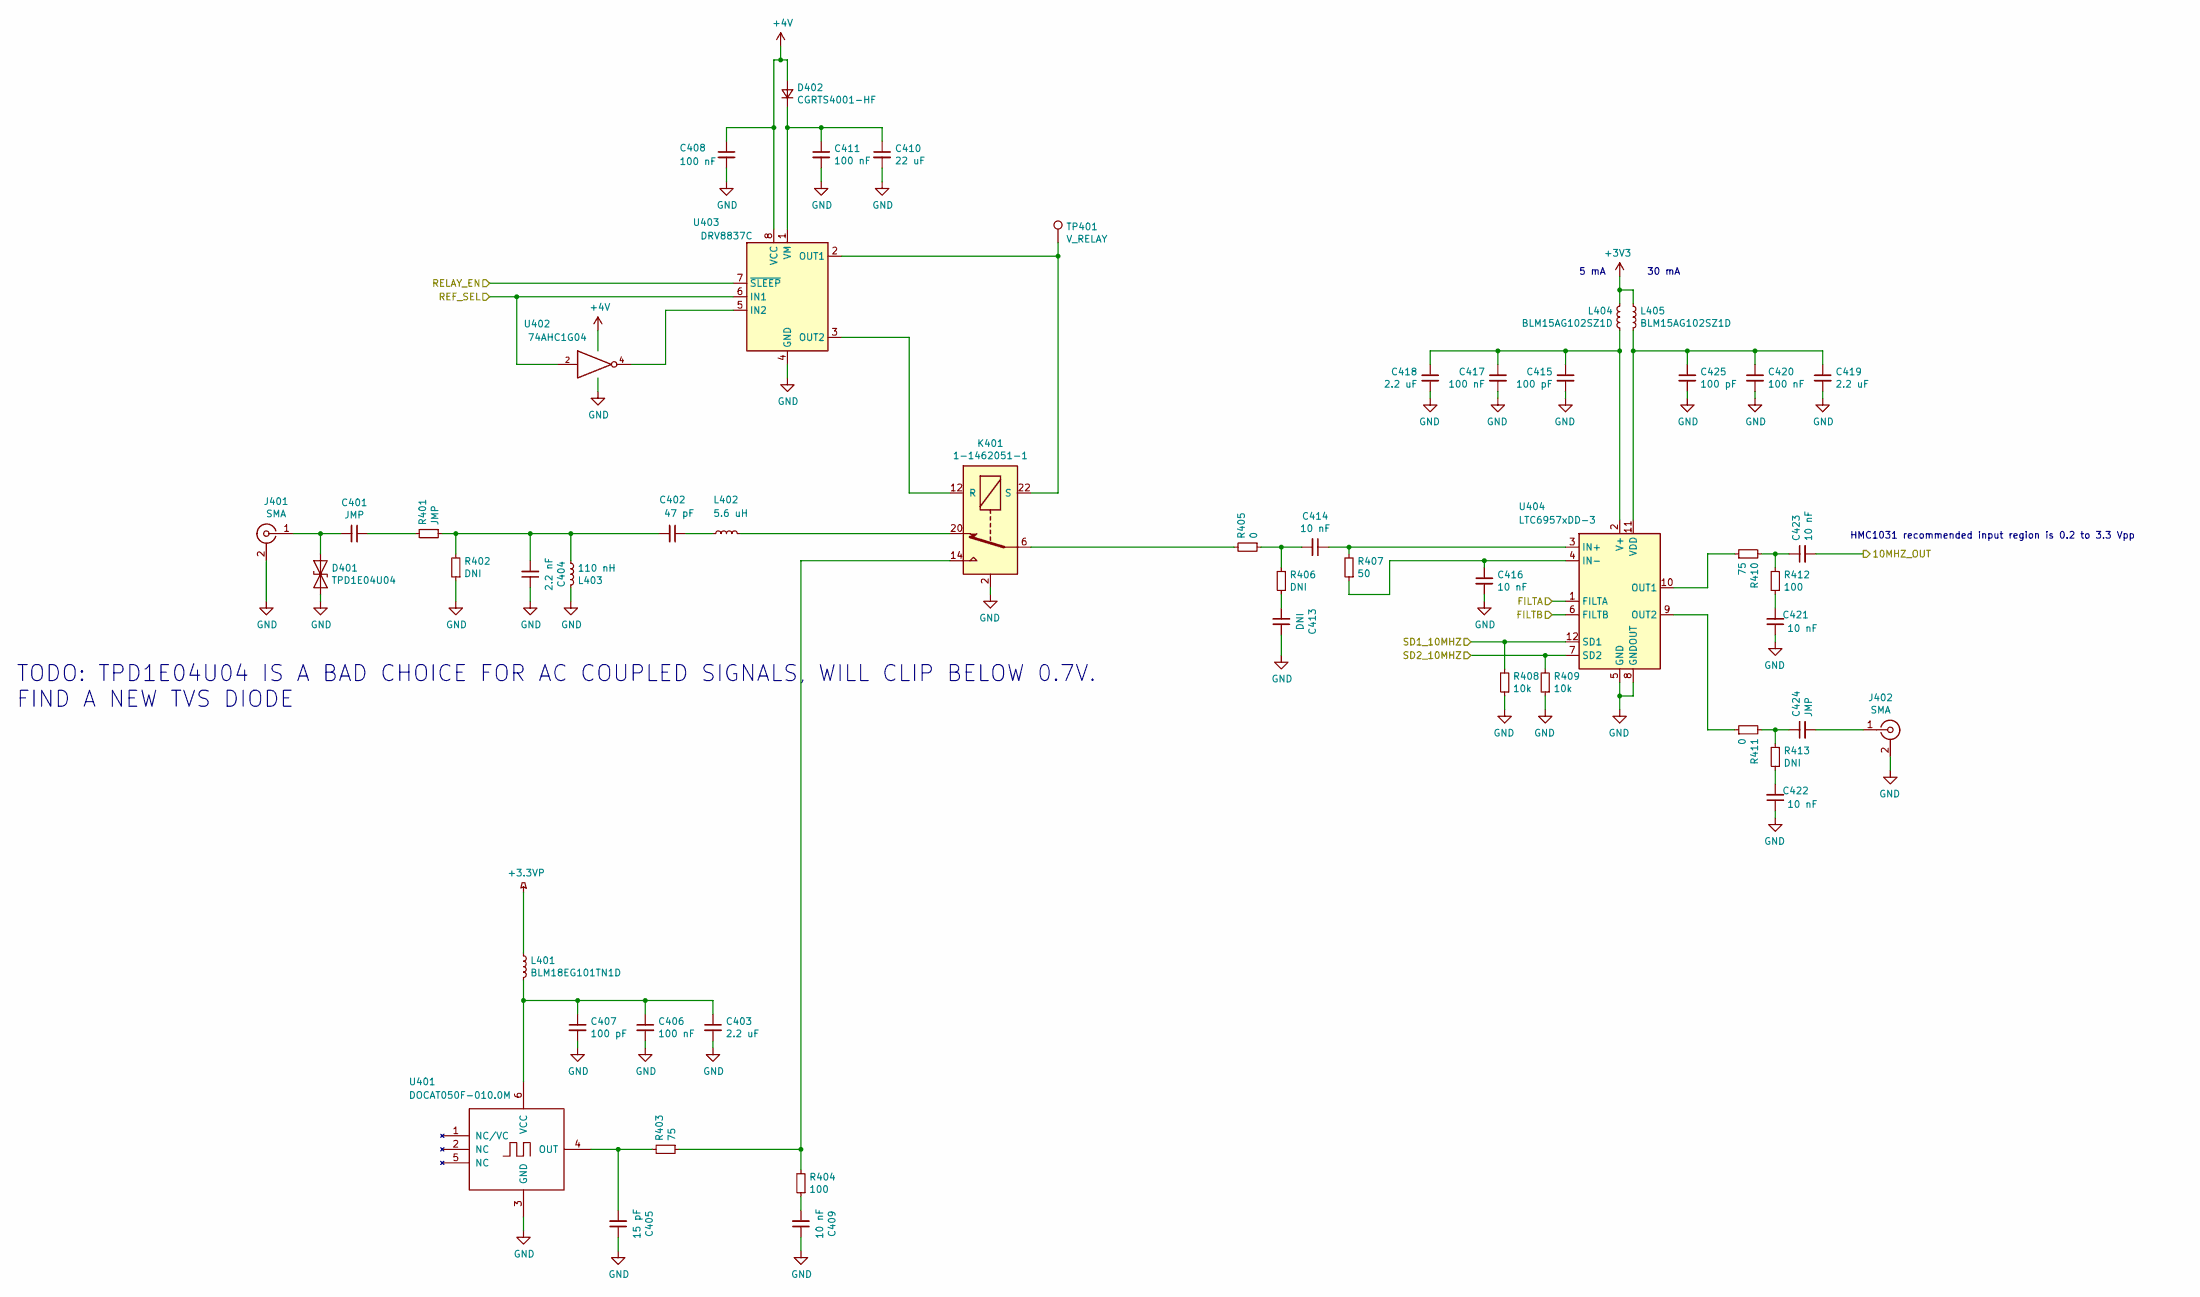
[picture p100: schematic ref_sel.sch]

Parts:
C401, C424: JMP; C_0402_1005Metric
C402: 47 pF; C_0402_1005Metric
C403, C418, C419: 2.2 uF; C_0603_1608Metric
C404: 2.2 nF; C_0402_1005Metric
C405: 15 pF; C_0402_1005Metric
C406, C408, C411, C417, C420: 100 nF; C_0402_1005Metric
C407, C415, C425: 100 pF; C_0402_1005Metric
C409, C414, C416, C421, C422, C423: 10 nF; C_0402_1005Metric
C410: 22 uF; C_0805_2012Metric
C413: DNI; C_0402_1005Metric
D401: TPD1E04U04; D_0402_1005Metric
D402: CGRTS4001-HF; D_SOD-123F
J401, J402: SMA; SMA_Amphenol_132289_EdgeMount
K401: 1-1462051-1; Relay_SPDT_AXICOM_HF3Series_50ohms_Pitch1.27mm
L401: BLM18EG101TN1D; L_0603_1608Metric
L402: 5.6 uH; L_0805_2012Metric
L403: 110 nH; L_0603_1608Metric
L404, L405: BLM15AG102SZ1D; L_0402_1005Metric
R401: JMP; R_0402_1005Metric
R402, R406, R413: DNI; R_0402_1005Metric
R403, R410: 75; R_0402_1005Metric
R404, R412: 100; R_0402_1005Metric
R405, R411: 0; R_0402_1005Metric
R407: 50; R_0402_1005Metric
R408, R409: 10k; R_0402_1005Metric
TP401: V_RELAY; TestPoint_Keystone_5015_Micro-Minature
U401: DOCAT050F-010.0M; DOCAT_9.1x14.1mm
U402: 74AHC1G04; SOT-353_SC-70-5
U403: DRV8837C; WSON-8-1EP_2x2mm_P0.5mm_EP0.9x1.6mm
U404: LTC6957xDD-3; DFN-12-1EP_3x3mm_P0.45mm_EP1.66x2.38mm

Connections:
+3.3VP: L401.1; also elsewhere on the board
+3V3: L404.1, L405.1; also elsewhere on the board
+4V: C408.1, D402.2 (A), U402.5 (VCC), U403.8 (VCC); also elsewhere on the board
/FILTA_REF: U404.6 (FILTB); also elsewhere on the board
/FILTB_REF: U404.1 (FILTA); also elsewhere on the board
/REF_SEL: U402.2, U403.6 (IN1); also elsewhere on the board
/RELAY_EN: U403.7 (~SLEEP); also elsewhere on the board
/SD_PLLCLK: R408.2, U404.12 (SD1); also elsewhere on the board
/SD_REFOUT: R409.2, U404.7 (SD2); also elsewhere on the board
/synth_100MHz/10MHZ_IN: C423.2; also elsewhere on the board
GND: C403.2, C404.1, C405.1, C406.2, C407.2, C408.2, C409.1, C410.2, C411.2, C413.1, C415.2, C416.2, C417.2, C418.2, C419.2, C420.2, C421.1, C422.1, C425.2, D401.2 (A2), J401.2 (Ext), J402.2 (Ext), K401.2, K401.5, K401.7, K401.10, K401.13, K401.15, K401.17, K401.19, K401.21, L403.1, R402.1, R408.1, R409.1, U401.3 (GND), U402.3 (GND), U403.4 (GND), U403.9 (GND), U404.5 (GND), U404.8 (GNDOUT), U404.13 (GND); also elsewhere on the board
unnamed: C401.1, R401.2
unnamed: C401.2, D401.1 (A1), J401.1 (In)
unnamed: C402.1, L402.2
unnamed: C402.2, C404.2, L403.2, R401.1, R402.2
unnamed: C403.1, C406.1, C407.1, L401.2, U401.6 (VCC)
unnamed: C405.2, R403.2, U401.4 (OUT)
unnamed: C409.2, R404.1
unnamed: C410.1, C411.1, D402.1 (K), U403.1 (VM)
unnamed: C413.2, R406.1
unnamed: C414.1, R407.2, U404.3 (IN+)
unnamed: C414.2, R405.1, R406.2
unnamed: C415.1, C417.1, C418.1, L404.2, U404.2 (V+)
unnamed: C416.1, R407.1, U404.4 (IN-)
unnamed: C419.1, C420.1, C425.1, L405.2, U404.11 (VDD)
unnamed: C421.2, R412.1
unnamed: C422.2, R413.1
unnamed: C423.1, R410.2, R412.2
unnamed: C424.1, R411.2, R413.2
unnamed: C424.2, J402.1 (In)
unnamed: K401.1, K401.12 (R), U403.3 (OUT2)
unnamed: K401.6, R405.2
unnamed: K401.11, K401.22 (S), TP401.1, U403.2 (OUT1)
unnamed: K401.14, R403.1, R404.2
unnamed: K401.20, L402.1
unnamed: R410.1, U404.10 (OUT1)
unnamed: R411.1, U404.9 (OUT2)
unnamed: U402.4, U403.5 (IN2)

Notes on the sheet:
5 mA
30 mA
HMC1031 recommended input region is 0.2 to 3.3 Vpp
TODO: TPD1E04U04 IS A BAD CHOICE FOR AC COUPLED SIGNALS, WILL CLIP BELOW 0.7V. FIND A NEW TVS DIODE
