loxodes/vna/hardware/vna_mm_ref/vna_mm_ref.kicad_pcb

## KiCad design hardware/vna_mm_ref/vna_mm_ref.kicad_pcb (continued)

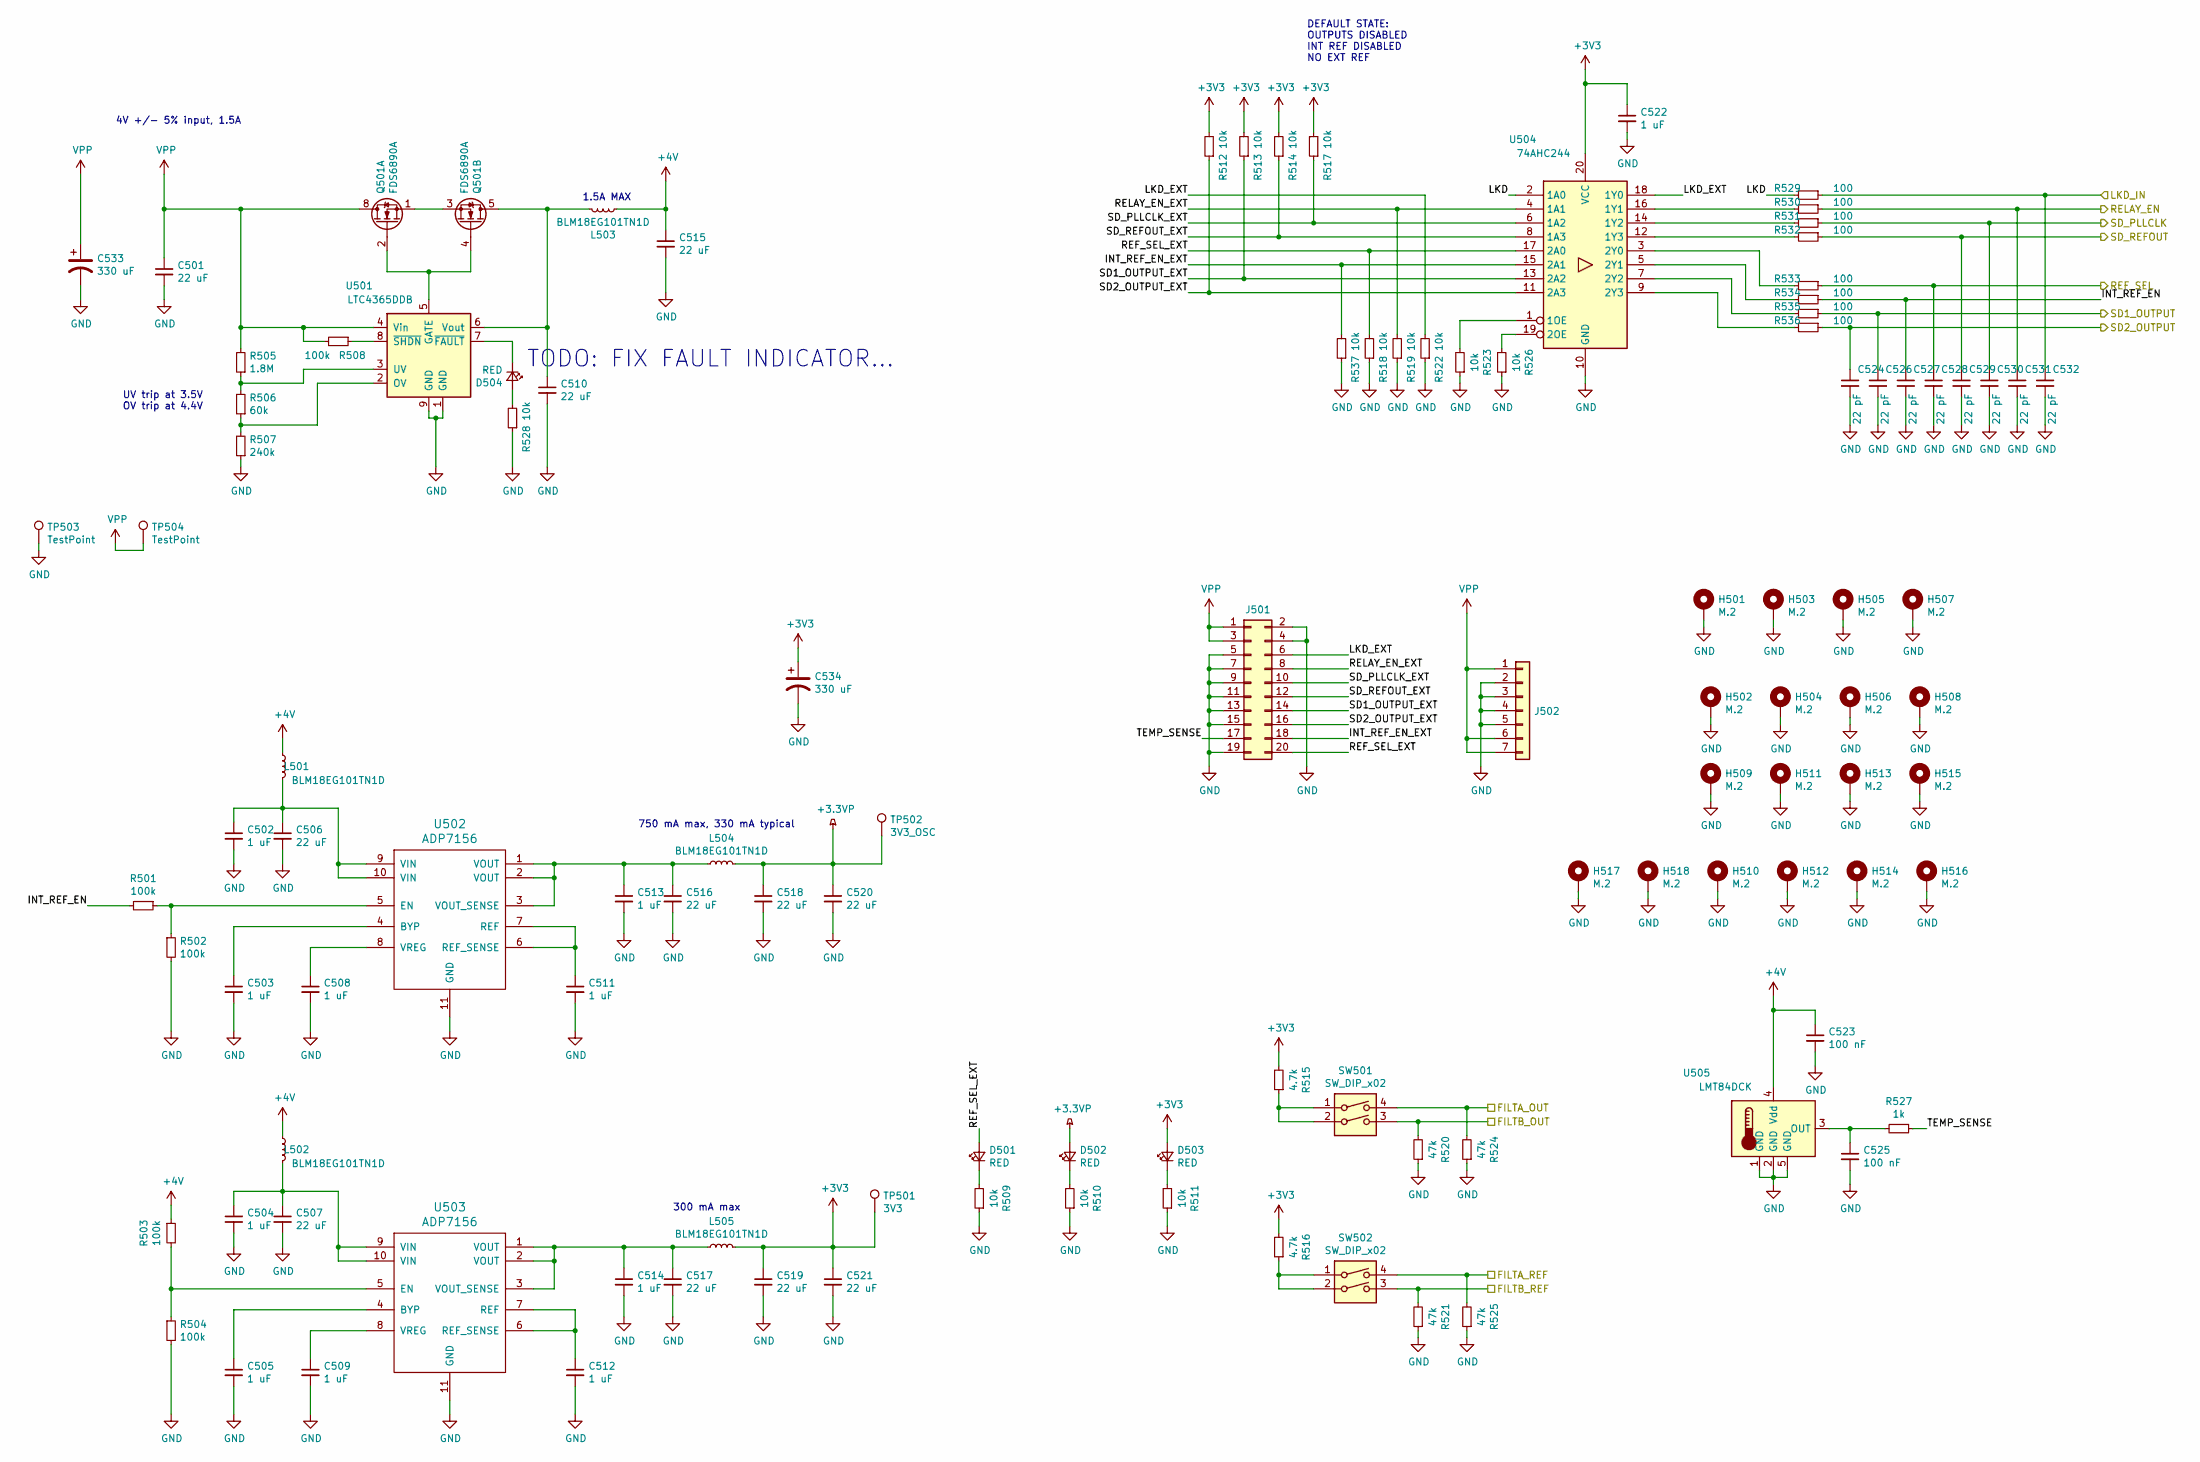
[picture p101: schematic power_conn.sch]

Parts:
C501, C506, C507, C510, C515, C516, C517, C518, C519, C520, C521: 22 uF; C_0805_2012Metric
C502, C503, C504, C505, C508, C509, C511, C512, C513, C514, C522: 1 uF; C_0402_1005Metric
C523, C525: 100 nF; C_0402_1005Metric
C524, C526, C527, C528, C529, C530, C531, C532: 22 pF; C_0402_1005Metric
C533, C534: 330 uF; CP_Elec_6.3x5.9
D501, D502, D503, D504: RED; LED_0603_1608Metric
H501, H502, H503, H504, H505, H506, H507, H508, H509, H510, H511, H512, H513, H514, H515, H516, H517, H518: M.2; MountingHole_2.2mm_M2_Pad_Via
J501: Conn_02x10_Odd_Even; PinHeader_2x10_P2.54mm_Vertical
J502: Conn_01x07; PinHeader_1x07_P2.54mm_Vertical
L501, L502, L503, L504, L505: BLM18EG101TN1D; L_0603_1608Metric
Q501: FDS6890A; SOIC-8_3.9x4.9mm_P1.27mm
R501, R502, R503, R504, R508: 100k; R_0402_1005Metric
R505: 1.8M; R_0402_1005Metric
R506: 60k; R_0402_1005Metric
R507: 240k; R_0402_1005Metric
R509, R510, R511, R512, R513, R514, R517, R518, R519, R522, R523, R526, R528, R537: 10k; R_0402_1005Metric
R515, R516: 4.7k; R_0402_1005Metric
R520, R521, R524, R525: 47k; R_0402_1005Metric
R527: 1k; R_0402_1005Metric
R529, R530, R531, R532, R533, R534, R535, R536: 100; R_0402_1005Metric
SW501, SW502: SW_DIP_x02; SW_DIP_SPSTx02_Slide_6.7x6.64mm_W6.73mm_P2.54mm_LowProfile_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
TP501: 3V3; TestPoint_Keystone_5015_Micro-Minature
TP502: 3V3_OSC; TestPoint_Keystone_5015_Micro-Minature
TP503, TP504: TestPoint; TURRET_MILLMAX_2101
U501: LTC4365DDB; DFN-8-1EP_2x3mm_P0.5mm_EP0.61x2.2mm
U502, U503: ADP7156; DFN-10-1EP_3x3mm_P0.5mm_EP1.65x2.38mm
U504: 74AHC244; TSSOP-20_4.4x6.5mm_P0.65mm
U505: LMT84DCK; SOT-353_SC-70-5

Connections:
+3.3VP: C518.1, C520.1, D502.2 (A), L504.2, TP502.1; also elsewhere on the board
+3V3: C519.1, C521.1, C522.1, C534.1, D503.2 (A), L505.2, R512.2, R513.2, R514.2, R515.2, R516.2, R517.2, TP501.1, U504.20 (VCC); also elsewhere on the board
+4V: C515.1, C523.1, L501.1, L502.1, L503.1, R503.1, U505.4 (Vdd); also elsewhere on the board
/FILTA_OUT: R524.2, SW501.4; also elsewhere on the board
/FILTA_REF: R525.2, SW502.4; also elsewhere on the board
/FILTB_OUT: R520.2, SW501.3; also elsewhere on the board
/FILTB_REF: R521.2, SW502.3; also elsewhere on the board
/LKD: C532.1, R529.1; also elsewhere on the board
/REF_SEL: C528.1, R533.1; also elsewhere on the board
/RELAY_EN: C531.1, R530.1; also elsewhere on the board
/SD1_OUTPUT: C526.1, R535.1; also elsewhere on the board
/SD2_OUTPUT: C524.1, R536.1; also elsewhere on the board
/SD_PLLCLK: C530.1, R531.1; also elsewhere on the board
/SD_REFOUT: C529.1, R532.1; also elsewhere on the board
/power_conn/INT_REF_EN: C527.1, R501.2, R534.1
/power_conn/INT_REF_EN_EXT: J501.18, R537.2, U504.15 (2A1)
/power_conn/LKD: R529.2, U504.2 (1A0)
/power_conn/LKD_EXT: J501.6, R522.2, U504.18 (1Y0)
/power_conn/REF_SEL_EXT: D501.2 (A), J501.20, R518.2, U504.17 (2A0)
/power_conn/RELAY_EN_EXT: J501.8, R519.2, U504.4 (1A1)
/power_conn/SD1_OUTPUT_EXT: J501.14, R513.1, U504.13 (2A2)
/power_conn/SD2_OUTPUT_EXT: J501.16, R512.1, U504.11 (2A3)
/power_conn/SD_PLLCLK_EXT: J501.10, R517.1, U504.6 (1A2)
/power_conn/SD_REFOUT_EXT: J501.12, R514.1, U504.8 (1A3)
/power_conn/TEMP_SENSE: J501.17, R527.1
GND: C501.2, C502.2, C503.2, C504.2, C505.2, C506.2, C507.2, C508.2, C509.2, C510.2, C511.2, C512.2, C513.2, C514.2, C515.2, C516.2, C517.2, C518.2, C519.2, C520.2, C521.2, C522.2, C523.2, C524.2, C525.2, C526.2, C527.2, C528.2, C529.2, C530.2, C531.2, C532.2, C533.2, C534.2, H501.1, H502.1, H503.1, H504.1, H505.1, H506.1, H507.1, H508.1, H509.1, H510.1, H511.1, H512.1, H513.1, H514.1, H515.1, H516.1, H517.1, H518.1, J501.2, J501.4, J501.5, J501.7, J501.9, J501.11, J501.13, J501.15, J501.19, J502.2, J502.3, J502.4, J502.5, R502.2, R504.2, R507.1, R509.1, R510.1, R511.1, R518.1, R519.1, R520.1, R521.1, R522.1, R523.1, R524.1, R525.1, R526.1, R528.1, R537.1, TP503.1, U501.1 (GND), U501.9 (GND), U502.11 (GND), U503.11 (GND), U504.10 (GND), U505.1 (GND), U505.2 (GND), U505.5 (GND); also elsewhere on the board
unnamed: C502.1, C506.1, L501.2, U502.9 (VIN), U502.10 (VIN)
unnamed: C503.1, U502.4 (BYP)
unnamed: C504.1, C507.1, L502.2, U503.9 (VIN), U503.10 (VIN)
unnamed: C505.1, U503.4 (BYP)
unnamed: C508.1, U502.8 (VREG)
unnamed: C509.1, U503.8 (VREG)
unnamed: C510.1, L503.2, Q501.5 (D2), Q501.6 (D2), U501.6 (Vout)
unnamed: C511.1, U502.6 (REF_SENSE), U502.7 (REF)
unnamed: C512.1, U503.6 (REF_SENSE), U503.7 (REF)
unnamed: C513.1, C516.1, L504.1, U502.1 (VOUT), U502.2 (VOUT), U502.3 (VOUT_SENSE)
unnamed: C514.1, C517.1, L505.1, U503.1 (VOUT), U503.2 (VOUT), U503.3 (VOUT_SENSE)
unnamed: C525.1, R527.2, U505.3 (OUT)
unnamed: D501.1 (K), R509.2
unnamed: D502.1 (K), R510.2
unnamed: D503.1 (K), R511.2
unnamed: D504.1 (K), U501.7 (~FAULT)
unnamed: D504.2 (A), R528.2
unnamed: Q501.1 (S1), Q501.3 (S2)
unnamed: Q501.2 (G1), Q501.4 (G2), U501.5 (GATE)
unnamed: R501.1, R502.1, U502.5 (EN)
unnamed: R503.2, R504.1, U503.5 (EN)
unnamed: R505.1, R506.2, U501.3 (UV)
unnamed: R506.1, R507.2, U501.2 (OV)
unnamed: R508.1, U501.8 (~SHDN)
unnamed: R515.1, SW501.1, SW501.2
unnamed: R516.1, SW502.1, SW502.2
unnamed: R523.2, U504.1 (1OE)
unnamed: R526.2, U504.19 (2OE)
unnamed: R530.2, U504.16 (1Y1)
unnamed: R531.2, U504.14 (1Y2)
unnamed: R532.2, U504.12 (1Y3)
unnamed: R533.2, U504.3 (2Y0)
unnamed: R534.2, U504.5 (2Y1)
unnamed: R535.2, U504.7 (2Y2)
unnamed: R536.2, U504.9 (2Y3)
VPP: C501.1, C533.1, J501.1, J501.3, J502.1, J502.6, J502.7, Q501.7 (D1), Q501.8 (D1), R505.2, R508.2, TP504.1, U501.4 (Vin)

Notes on the sheet:
300 mA max
1.5A MAX
750 mA max, 330 mA typical
4V +/- 5% input, 1.5A
UV trip at 3.5V OV trip at 4.4V
DEFAULT STATE: OUTPUTS DISABLED INT REF DISABLED NO EXT REF
TODO: FIX FAULT INDICATOR...

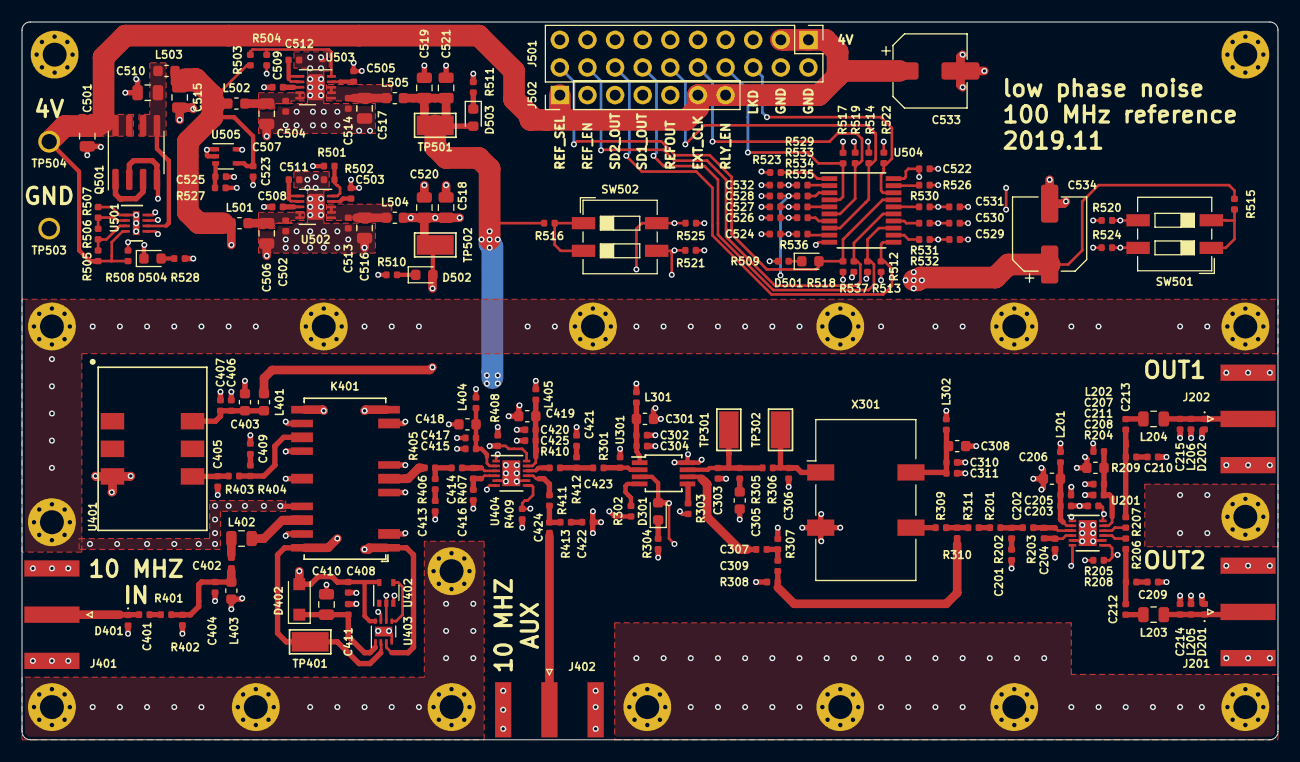
[picture p102: board vna_mm_ref.kicad_pcb from above]

Board: 4 copper layers, 115.5 x 66.0 mm, 228 parts (0 on the bottom side), 120 nets.
