loxodes/vna/breakouts/hyperram/hyperram_3p3v/hyperram_3p3v.kicad_pcb

## KiCad design breakouts/hyperram/hyperram_3p3v/hyperram_3p3v.kicad_pcb (2020-04-20)

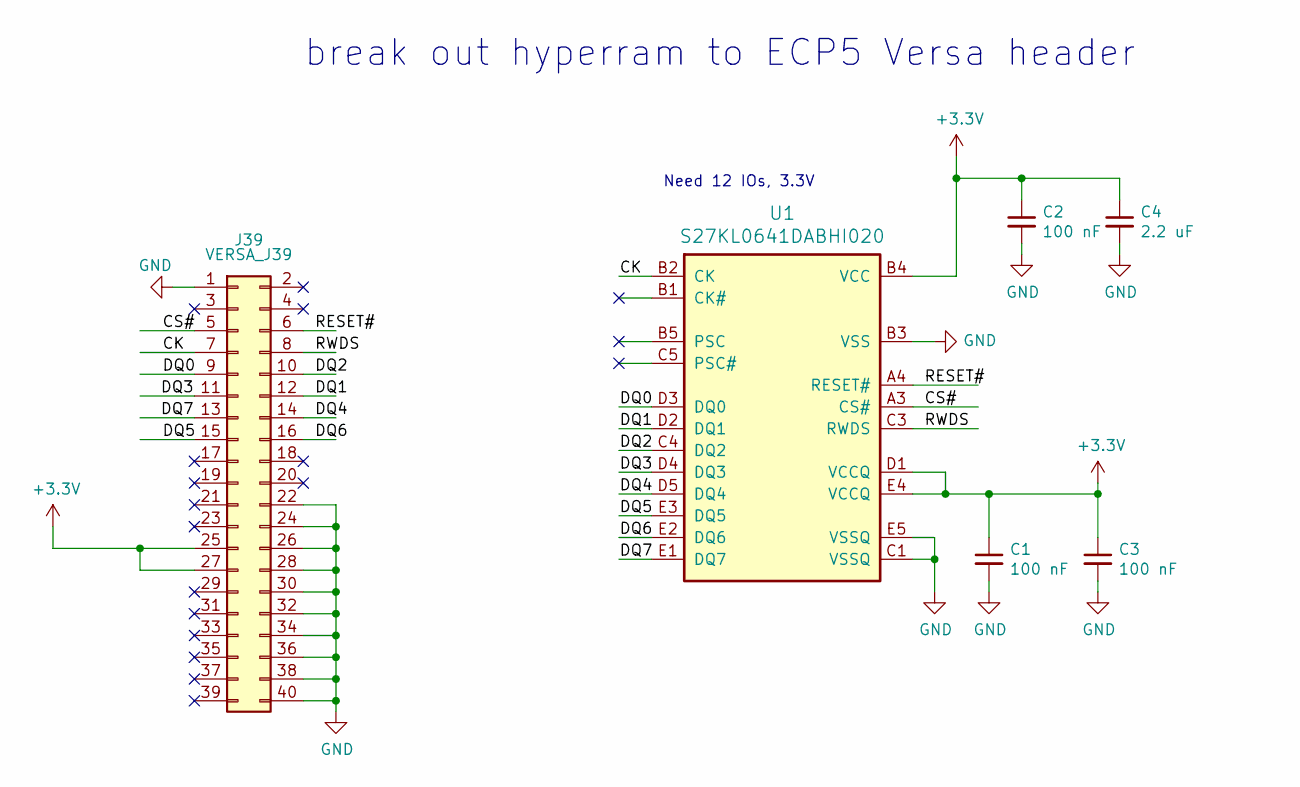
[picture p103: schematic hyperram_3p3v.sch]

Parts:
C1, C2, C3: 100 nF; C_0402_1005Metric
C4: 2.2 uF; C_0603_1608Metric
J39: VERSA_J39; PinSocket_2x20_P2.54mm_Vertical
U1: S27KL0641DABHI020; T-PBGA-24_6.0x8.0mm_Layout5x5_P1.0mm

Connections:
+3V3: C1.1, C2.1, C3.1, C4.1, J39.25, J39.27, U1.B4 (VCC), U1.D1 (VCCQ), U1.E4 (VCCQ)
/CK: J39.7, U1.B2 (CK)
/CS#: J39.5, U1.A3 (CS#)
/DQ0: J39.9, U1.D3 (DQ0)
/DQ1: J39.12, U1.D2 (DQ1)
/DQ2: J39.10, U1.C4 (DQ2)
/DQ3: J39.11, U1.D4 (DQ3)
/DQ4: J39.14, U1.D5 (DQ4)
/DQ5: J39.15, U1.E3 (DQ5)
/DQ6: J39.16, U1.E2 (DQ6)
/DQ7: J39.13, U1.E1 (DQ7)
/RESET#: J39.6, U1.A4 (RESET#)
/RWDS: J39.8, U1.C3 (RWDS)
GND: C1.2, C2.2, C3.2, C4.2, J39.1, J39.22, J39.24, J39.26, J39.28, J39.30, J39.32, J39.34, J39.36, J39.38, J39.40, U1.B3 (VSS), U1.C1 (VSSQ), U1.E5 (VSSQ)

Notes on the sheet:
Need 12 IOs, 3.3V
break out hyperram to ECP5 Versa header

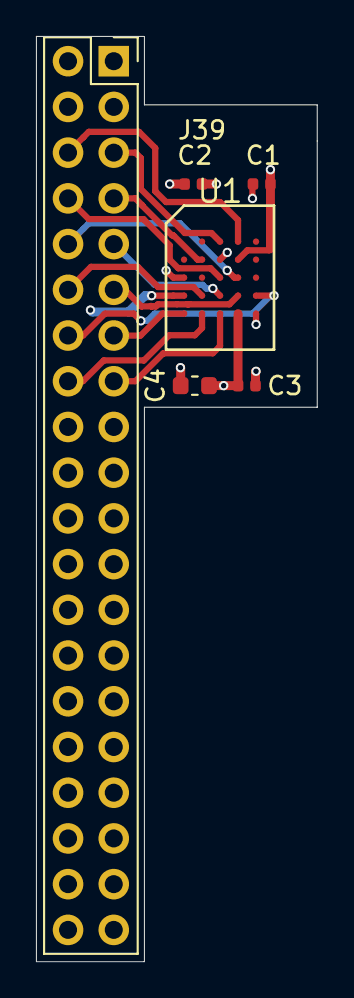
[picture p104: board hyperram_3p3v.kicad_pcb from above]

Board: 4 copper layers, 15.6 x 51.4 mm, 6 parts (0 on the bottom side), 14 nets.
