loxodes/vna/hardware/vna_rev1/vna_r1_demod/vna_r1_demod.kicad_pcb

## KiCad design hardware/vna_rev1/vna_r1_demod/vna_r1_demod.kicad_pcb (2018-05-20)

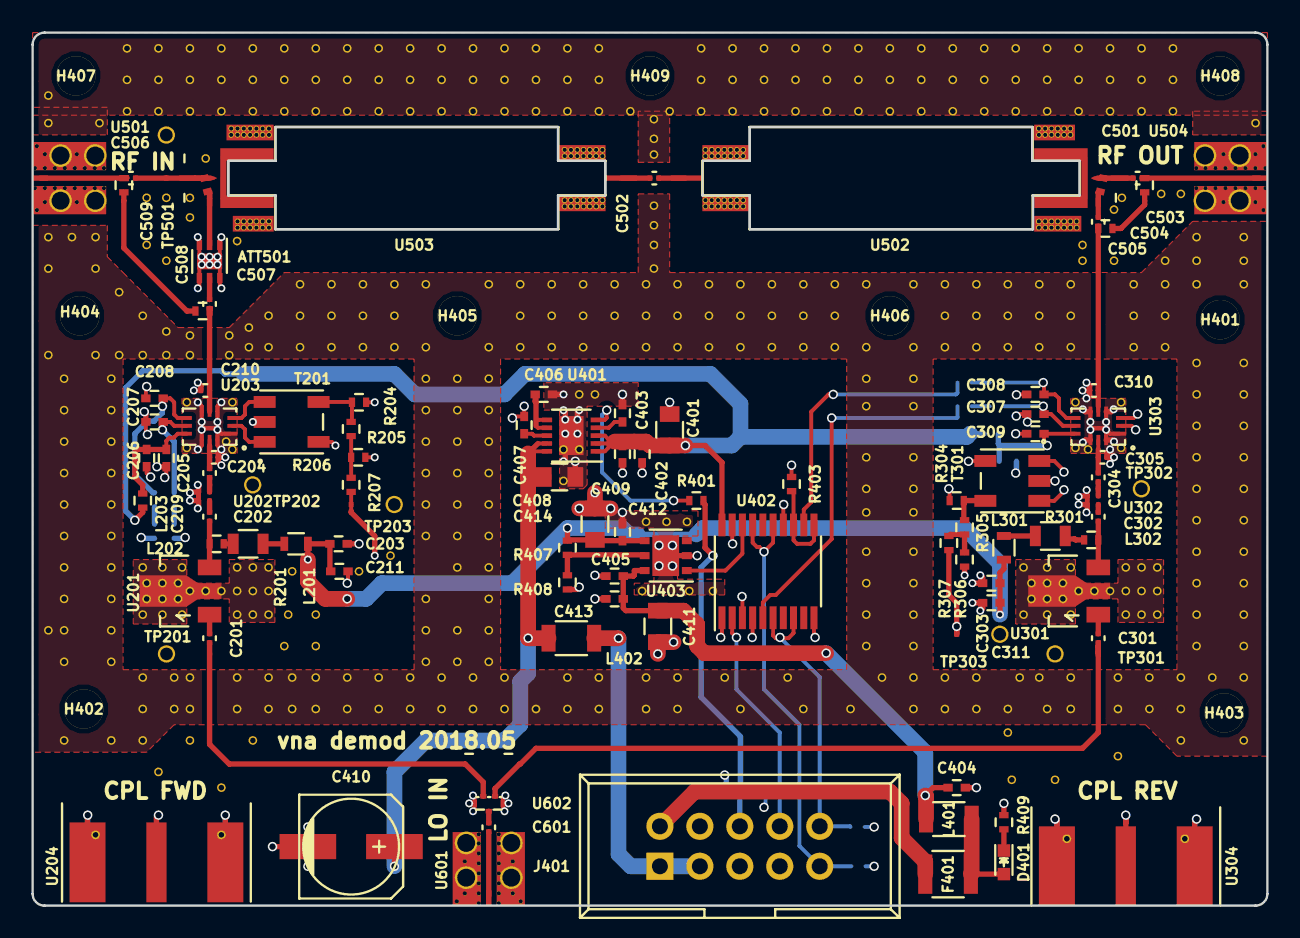
[picture p105: board vna_r1_demod.kicad_pcb from above]

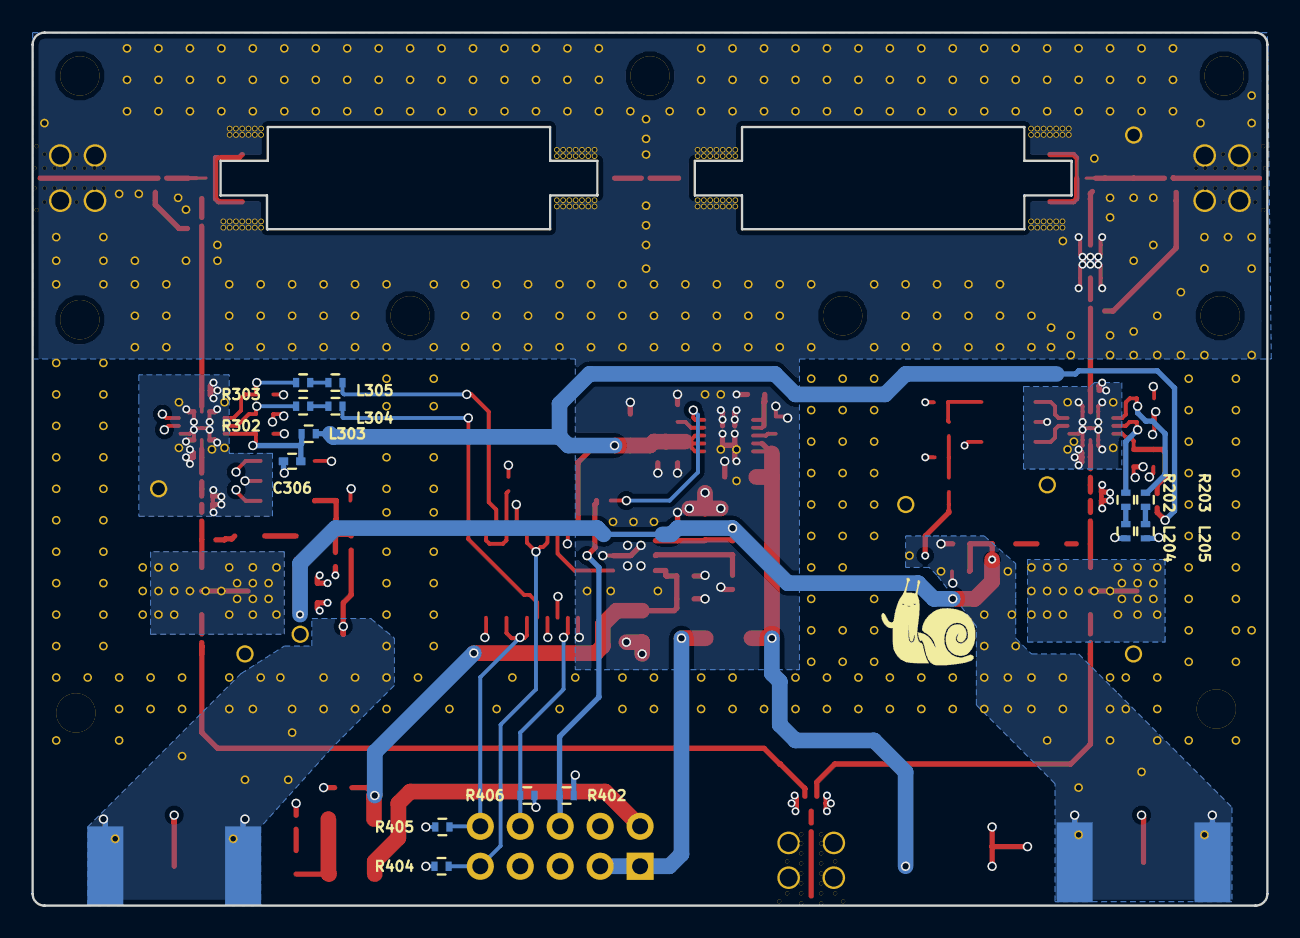
[picture p106: board vna_r1_demod.kicad_pcb from below]

Board: 4 copper layers, 78.5 x 55.5 mm, 120 parts (14 on the bottom side), 75 nets.

Parts:
ATT501: HMC657LP2E; DFN-6-1EP_2x2mm_Pitch0.65mm
C201, C202, C204, C205, C301, C302, C304, C305, C505, C507, C601: C_Small; C_0201
C203, C206, C207, C208, C209, C211, C303, C306, C307, C308, C309, C311, C409: C_Small; C_0402
C210, C310: DNP; C_0201
C401, C408: 10 uF; C_0805
C402, C403, C404, C406, C407, C413: 1 uF; C_0402
C405, C412: 100 nF; C_0402
C410: 4.7 uF; c_elec_6.3x5.8
C411, C414: 4.7 uF; C_0805
C501, C502, C506: 10 pF; C_0201
C503, C504, C508, C509: DNP; R_0402
D401: LED; LED_0603
F401: Polyfuse_Small; R_1210
H401, H402, H403, H404, H405, H406, H407, H408, H409: MOUNTING_HOLE; MountingHole_2-5mm
J401: Conn_02x05_Odd_Even; IDC_Header_Straight_10pins
L201, L301: L_Small; R_0603
L202, L203, L204, L205, L302, L303, L304, L305: L_Small; R_0402
L401, L402: L_Small; R_1206
R201, R301: 13; R_0805
R202, R203, R204, R205, R206, R207, R302, R303, R304, R305, R306, R307: R_Small; R_0402
R401: 100; R_0402
R402, R403, R404, R405, R406, R409: 10k; R_0402
R407: 47k; R_0402
R408: 12k; R_0402
T201, T301: Transformer_SP_1S; 5LEAD_BALUN_4p83mm_3p3mm
TP201, TP202, TP203, TP301, TP302, TP303, TP501: TP_RF; TP-P20B
U201, U301: SKY65013-70LF; SOT89-3_Housing
U202, U302: PAT0510S-C-XDB-T10; PAT0510S
U203, U303: LTC5548; QFN_12_3mm2mm
U204, U304: CONN_SMA; 732511150_sma_thin
U401: ADP7158; DFN-10-1EP_3x3mm_Pitch0.5mm
U402: 74HC244; TSSOP-20_4.4x6.5mm_Pitch0.65mm
U403: LD39100; DFN-6-1EP_3x3mm_Pitch0.95mm
U501, U504, U601: CONN_SMA_2GND; SMA_901-10512_6p7MIL_FR408_CPW_LAUNCH
U502: resistive_bridge; resistive_bridge_osh_fr408_ustrip_mirrored
U503: resistive_bridge; resistive_bridge_osh_fr408_ustrip
U602: PWR_SPLITTER; PS1608

Connections:
+3V3: C401.1, C402.1, C409.1, L203.2, L303.2, U401.1, U401.2, U401.3, U402.20
+5V: C404.1, C405.1, C411.1, C413.1, L401.2, U403.6
/LO_AMP_A: C203.2, C211.2, C303.2, C311.2, C412.1, C414.1, L201.2, L301.2, R407.1, U403.4
/MIX_EN_A: L205.2, U402.14
/MIX_EN_B: L305.2, U402.12
/X2_EN_A: L204.2, U402.3
/X2_EN_B: L304.2, U402.5
/couplers/CPL_FWD: C210.2, C507.1, C508.2, U203.5
/couplers/CPL_REV: C310.2, C504.2, C505.1, U303.5
/lo_split/LO_A: C201.2, TP201.1, U602.3
/lo_split/LO_B: C301.2, TP301.1, U602.2
/power_conn/EXT_3V3_EN: J401.6, R401.2, R402.2
/power_conn/EXT_LO_AMP_EN: J401.8, R406.2, U402.2
/power_conn/EXT_MIX_EN: J401.10, R405.2, U402.6, U402.8
/power_conn/EXT_X2_EN: J401.9, R404.2, U402.15, U402.17
/power_conn/LO_AMP_EN: U402.18, U403.1
GND: ATT501.1, ATT501.3, ATT501.4, ATT501.6, ATT501.7, C203.1, C205.2, C206.2, C207.1, C208.1, C209.2, C210.1, C211.1, C303.1, C305.2, C306.2, C307.1, C308.1, C309.2, C310.1, C311.1, C401.2, C402.2, C403.2, C404.2, C405.2, C406.2, C407.2, C408.2, C409.2, C410.2, C411.2, C412.2, C413.2, C414.2, J401.4, J401.5, J401.7, R204.2, R206.2, R304.2, R306.2, R402.1, R403.1, R404.1, R405.1, R406.1, R408.2, R409.1, T201.2, T201.5, T301.2, T301.5, TP201.2, TP202.2, TP203.2, TP301.2, TP302.2, TP303.2, TP501.2, U201.2, U202.3, U202.4, U203.1, U203.4, U203.6, U203.10, U203.12, U203.13, U204.2, U204.3, U204.4, U204.5, U301.2, U302.3, U302.4, U303.1, U303.4, U303.6, U303.10, U303.12, U303.13, U304.2, U304.3, U304.4, U304.5, U401.11, U402.1, U402.4, U402.10, U402.19, U403.2, U403.7, U501.2, U501.3, U502.4, U503.4, U504.2, U504.3, U601.2, U601.3, U602.4
unnamed: ATT501.2, U503.3
unnamed: ATT501.5, C507.2
unnamed: C201.1, U201.1
unnamed: C202.1, U202.2
unnamed: C202.2, L202.1, U201.3
unnamed: C204.1, TP202.1, U202.1
unnamed: C204.2, C205.1, U203.11
unnamed: C206.1, C209.1, L203.1, U203.9
unnamed: C207.2, R202.1, U203.8
unnamed: C208.2, R203.1, U203.7
unnamed: C301.1, U301.1
unnamed: C302.1, U302.2
unnamed: C302.2, L302.1, U301.3
unnamed: C304.1, TP302.1, U302.1
unnamed: C304.2, C305.1, U303.11
unnamed: C306.1, C309.1, L303.1, U303.9
unnamed: C307.2, R302.1, U303.8
unnamed: C308.2, R303.1, U303.7
unnamed: C403.1, U401.4
unnamed: C406.1, U401.6, U401.7
unnamed: C407.1, U401.8
unnamed: C501.1, U502.2
unnamed: C501.2, C503.2, U504.1
unnamed: C502.1, U503.1
unnamed: C502.2, U502.1
unnamed: C503.1, C504.1
unnamed: C505.2, U502.3
unnamed: C506.1, C509.2, U501.1
unnamed: C506.2, TP501.1, U503.2
unnamed: C508.1, C509.1
unnamed: C601.1, U602.1
unnamed: C601.2, U601.1
unnamed: D401.1, R409.2
unnamed: D401.2, F401.1, L401.1
unnamed: F401.2, J401.2
unnamed: J401.1, J401.3, L402.2
unnamed: L201.1, R201.2
unnamed: L202.2, R201.1
unnamed: L204.1, R202.2
unnamed: L205.1, R203.2
unnamed: L301.1, R301.2
unnamed: L302.2, R301.1
unnamed: L304.1, R302.2
unnamed: L305.1, R303.2
unnamed: R204.1, R205.1, T201.4
unnamed: R205.2, R206.1, R207.1
unnamed: R207.2, TP203.1, U204.1
unnamed: R304.1, R305.1, T301.4
unnamed: R305.2, R306.1, R307.1
unnamed: R307.2, TP303.1, U304.1
unnamed: R401.1, U401.5
unnamed: R403.2, U402.11, U402.13
unnamed: R407.2, R408.1, U403.5
unnamed: T201.1, U203.2
unnamed: T201.3, U203.3
unnamed: T301.1, U303.2
unnamed: T301.3, U303.3
VPP: C408.1, C410.1, L402.1, U401.9, U401.10
