loxodes/vna/hardware/vna_rev1/vna_r1_controller/vna_r1.kicad_pcb

## KiCad design hardware/vna_rev1/vna_r1_controller/vna_r1.kicad_pcb (2019-08-02)

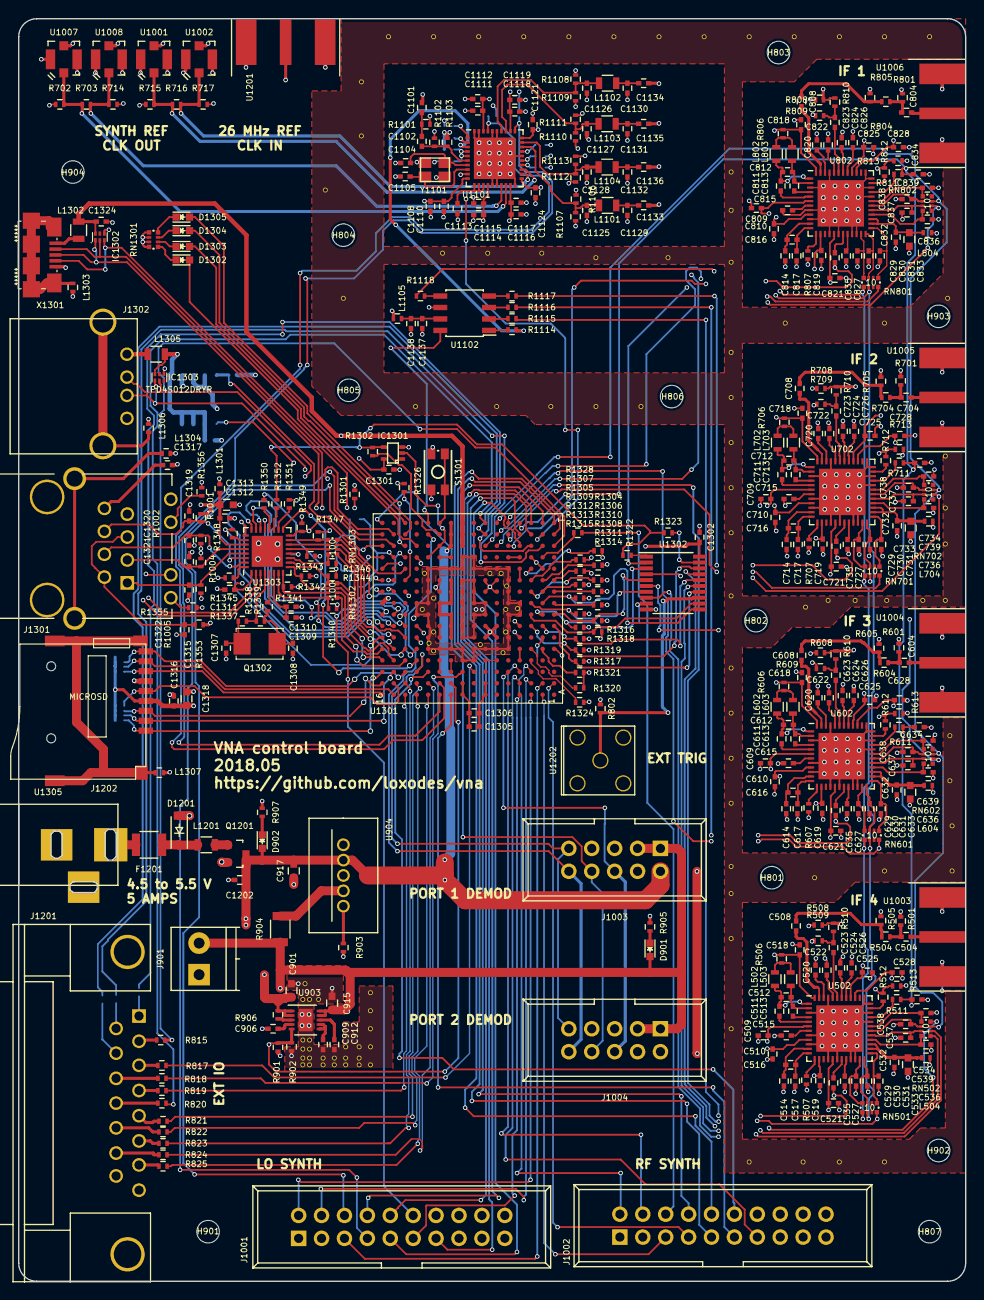
[picture p107: board vna_r1.kicad_pcb from above]

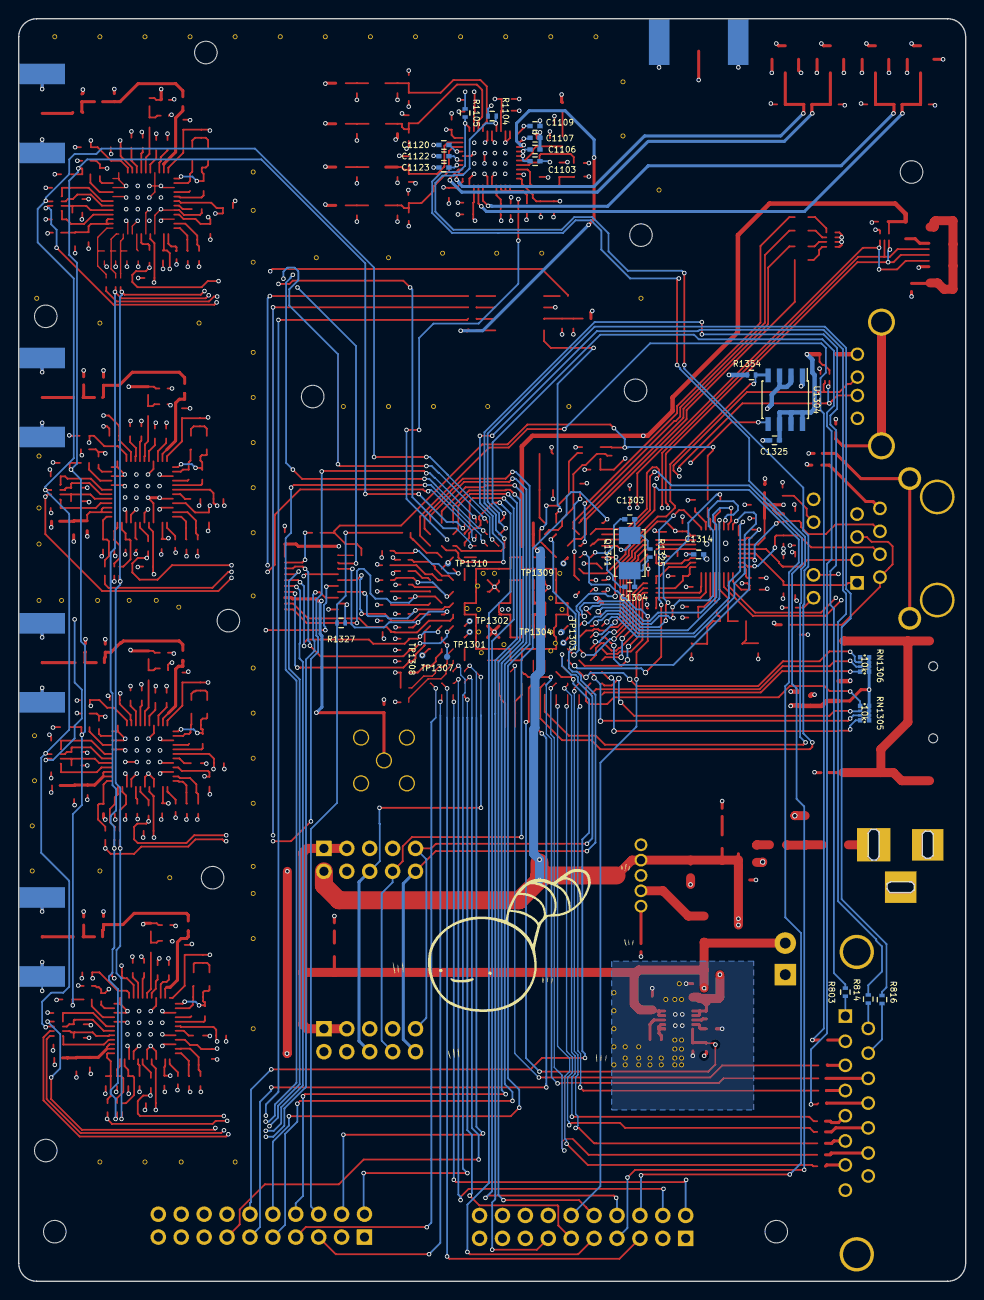
[picture p108: board vna_r1.kicad_pcb from below]

Board: 4 copper layers, 105.0 x 140.0 mm, 447 parts (31 on the bottom side), 375 nets.

Parts:
C504, C508, C516, C523, C524, C604, C608, C616, C623, C624, C704, C708, C716, C723, C724, C804, C808, C816, C823, C824, C1110, C1111, C1115, C1117, C1118: 10 nF; C_0402
C509, C510, C518, C519, C520, C521, C522, C525, C527, C528, C532, C535, C609, C610, C618, C619, C620, C621, C622, C625, C627, C628, C632, C635, C709, C710, C718, C719, C720, C721, C722, C725, C727, C728, C732, C735, C809, C810, C818, C819, C820, C821, C822, C825, C827, C828, C832, C835, C1101, C1103, C1106, C1107, C1108, C1109, C1112, C1114, C1116, C1119, C1120, C1121, C1122, C1123, C1124, C1133, C1134, C1135, C1136, C1137, C1202, C1301, C1302, C1305, C1311, C1312, C1314, C1316, C1324, C1325: 100 nF; C_0402
C511, C513, C514, C517, C611, C613, C614, C617, C711, C713, C714, C717, C811, C813, C814, C817: 100 pF; C_0402
C512, C612, C712, C812, C1129, C1130, C1131, C1132: 120 pF; C_0402
C515, C615, C715, C815: 2.2 nF; C_0402
C526, C626, C726, C826, C1306: 1 nF; C_0402
C529, C530, C531, C534, C536, C537, C538, C539, C629, C630, C631, C634, C636, C637, C638, C639, C729, C730, C731, C734, C736, C737, C738, C739, C829, C830, C831, C834, C836, C837, C838, C839: 10 pF; C_0402
C533, C633, C733, C833, C901, C915, C917, C1313, C1318: 10 uF; C_0603
C906, C909, C912, C1138, C1309: 1 uF; C_0402
C1102, C1104, C1105: 22 pF; C_0402
C1113: 220 nF; C_0402
C1125, C1126, C1127, C1128, C1303, C1304: 18 pF; C_0402
C1307, C1308: 30 pF; C_0402
C1310: 470 pF; C_0402
C1315, C1317: 22 nF; C_0402
C1319, C1320, C1321, C1322: 15 pF; C_0402
D901, D902: LED_Small; LED_0603
D1201: 5.6V; SOD-123
D1302: USR0; LED_0603
D1303: USR1; LED_0603
D1304: USR2; LED_0603
D1305: USR3; LED_0603
F1201: Polyfuse_Small; R_1210
H801, H802, H803, H804, H805, H806, H807, H901, H902, H903, H904: MOUNTING_HOLE; MountingHole_2-5mm
IC1301: SN74LVC1G07DCK; SC-70-5
IC1302, IC1303: TPD4S012DRYR; SON-6(TI)-DRY
J901: CONN_01X02; TerminalBlock_Pheonix_PT-3.5mm_2pol
J1001, J1002: Conn_02x10_Odd_Even; IDC_Header_Straight_20pins
J1003, J1004: Conn_02x05_Odd_Even; IDC_Header_Straight_10pins
J1201: DB15_FEMALE_MountingHoles; DB15MC
J1202: BARREL_JACK
J1301: 0480254000; RJ45_TRANSFO
J1302: USB_A
L502, L503, L602, L603, L702, L703, L802, L803: 6.8 uH BRL1608T6R8M; R_0603
L504, L604, L704, L804: BLM15GG471; R_0402
L1101, L1102, L1103, L1104: 130 nH; R_0805
L1105, L1301, L1303, L1304, L1306, L1307: L_Small; R_0402
L1201, L1302, L1305: L_Small; R_0805
Q1201: Q_PMOS_DGS; SOT-23
Q1301: 24 MHz; CRYSTAL_5X3.2MM
Q1302: 25 MHz; CRYSTAL_5X3.2MM
R501, R513, R601, R613, R701, R702, R713, R714, R715, R716, R717, R801, R813, R901, R1320, R1321: DNP; R_0402
R504, R604, R704, R804: 470 nH; R_0402
R505, R605, R705, R805: 22 pF; R_0402
R506, R606, R706, R806, R1001, R1002, R1004, R1005, R1101: 51; R_0402
R507, R607, R707, R807, R1304, R1305, R1306, R1307, R1308, R1309, R1310, R1311, R1312, R1313, R1314, R1315, R1316, R1317, R1318, R1319: 100k; R_0402
R508, R509, R510, R608, R609, R610, R708, R709, R710, R808, R809, R810: R_Small; R_0402
R511, R611, R711, R811, R1325, R1355, R1356: 1k; R_0402
R512, R612, R712, R812, R906, R1114, R1302, R1322, R1323, R1326, R1327, R1328, R1339, R1352, R1353: JMP; R_0402
R703, R902, R905, R907, R1102, R1103, R1104, R1105, R1106, R1107, R1108, R1109, R1110, R1111, R1112, R1113, R1301, R1324, R1340, R1341, R1342, R1343, R1351, R1354: 10k; R_0402
R802: 50; R_0402
R803, R814, R815, R816, R817, R818, R819, R820, R821, R822, R823, R824, R825: 22; R_0402
R903: 390; R_0402
R904: JMP; R_1206
R1115, R1116, R1117, R1118: 30; R_0402
R1337: 10; R_0402
R1338: 1M; R_0402
R1344, R1346, R1347, R1349: 1.5k; R_0402
R1345: 12.1k; R_0402
R1348, R1350: 100; R_0402
RN501, RN502, RN601, RN602, RN701, RN702, RN801, RN802: 10; RN0804
RN1301: RESISTOR.NETWORK-_4_; RN0804
RN1302, RN1303: 100; RN0804
RN1305, RN1306: 10k; RN0804
S1301: MINI_PUSHBUTTON
TP1301, TP1302, TP1303, TP1304, TP1307, TP1308, TP1309, TP1310: TEST; TP07R
U502, U602, U702, U802: ad9864; QFN-48-1EP_7x7mm_Pitch0.5mm
U903: ADP7158; DFN-10-1EP_3x3mm_Pitch0.5mm
U904: OKR-T/3-W12-C; OKRT3_C72
U1001, U1002, U1007, U1008: CONN_SMA_2GND; 734120110_ufl_umc
U1003, U1004, U1005, U1006, U1201: CONN_SMA; 732511150_sma_thin
U1101: AD9577; QFN-40-1EP_6x6mm_Pitch0.5mm
U1102: NB3N551; SOIC-8_3.9x4.9mm_Pitch1.27mm
U1202: CONN_SMA; 732512200_SMA
U1301: OSD3358-512M-BSM; OSD335X-BGA-256
U1302: 74HC244; TSSOP-20_4.4x6.5mm_Pitch0.65mm
U1303: LAN8710A; QFN-32-1EP_5x5mm_Pitch0.5mm
U1304: TPS2051; SOIC-8_3.9x4.9mm_Pitch1.27mm
U1305: MICROSD
X1301: 10118192-0001LF; 10118192-0001LF(MICRO-USB-B-AMPHENOL-FCI)
Y1101: 26 MHz 7M-26.000MEEQ-T; crystal_FA238-TSX3225

Connections:
+1V8: U1301.F10, U1301.G10, U1301.H10, U1301.H11, U1301.J10, U1301.J11, U1301.K10, U1301.L10
+3V3: C509.1, C510.1, C518.2, C519.2, C521.2, C525.2, C528.2, C609.1, C610.1, C618.2, C619.2, C621.2, C625.2, C628.2, C709.1, C710.1, C718.2, C719.2, C721.2, C725.2, C728.2, C809.1, C810.1, C818.2, C819.2, C821.2, C825.2, C828.2, C901.2, C1103.1, C1106.1, C1107.1, C1108.1, C1109.1, C1110.1, C1111.1, C1112.1, C1114.1, C1115.1, C1116.1, C1117.1, C1118.1, C1119.1, C1120.1, C1121.1, C1122.1, C1123.1, C1124.1, L504.2, L604.2, L704.2, L804.2, L1105.1, R506.1, R606.1, R706.1, R806.1, R906.2, R1102.1, R1104.1, R1105.1, R1106.1, R1108.1, R1110.1, R1112.1, U502.6, U502.9, U502.14, U502.17, U502.39, U502.40, U502.48, U602.6, U602.9, U602.14, U602.17, U602.39, U602.40, U602.48, U702.6, U702.9, U702.14, U702.17, U702.39, U702.40, U702.48, U802.6, U802.9, U802.14, U802.17, U802.39, U802.40, U802.48, U903.1, U903.2, U1101.1, U1101.2, U1101.4, U1101.5, U1101.10, U1101.14, U1101.19, U1101.21, U1101.24, U1101.25, U1101.27, U1101.30, U1101.32, U1101.38
+5V: C917.2, C1202.1, D902.2, J1001.19, J1001.20, J1002.19, J1002.20, J1003.2, J1004.2, J1201.8, Q1201.3, U904.2, U1301.P10, U1301.R10, U1301.T10
/3V3_DEMOD_EXT_EN: J1003.6, J1004.6, U1301.C5
/3V3_PLL_EN: R901.2, R902.1, U903.5, U1301.B10
/ADC_CLK_A: C535.2, R512.1, R513.2, R1115.2
/ADC_CLK_B: C635.2, R612.1, R613.2, R1116.2
/ADC_CLK_C: C735.2, R712.1, R713.2, R1117.2
/ADC_CLK_D: C835.2, R812.1, R813.2, R1118.1
/ADC_CLK_EN: U1102.8, U1301.T12
/AD_CLKOUT: RN502.5, U1302.15
/AD_DOUTA_A: RN502.6, U1302.8
/AD_DOUTA_B: RN602.6, U1302.6
/AD_DOUTA_C: RN702.6, U1302.4
/AD_DOUTA_D: RN802.6, U1302.2
/AD_DOUTB: RN502.7, RN602.7, RN702.7, RN802.7, U1301.P7
/AD_FS: RN502.8, U1302.17
/AD_PC: RN501.5, RN601.5, RN701.5, RN801.5, U1301.R6
/AD_PD: RN501.6, RN601.6, RN701.6, RN801.6, U1301.T6
/AD_PE_A: RN501.8, U1301.P6
/AD_PE_B: RN601.8, U1301.T5
/AD_PE_C: RN701.8, U1301.R5
/AD_PE_D: RN801.8, U1301.P5
/AD_SYNCB: C534.1, C634.1, C734.1, C834.1, R511.1, R611.1, R711.1, R811.1, U1301.T4
/EXT_AIN0: R817.1, U1301.C8
/EXT_AIN1: R818.1, U1301.C9
/EXT_IO_0: R803.1, U1301.P3
/EXT_IO_1: R814.1, U1301.P2
/EXT_IO_2: R815.1, U1301.P1
/EXT_IO_3: R816.1, U1301.R7
/EXT_PLL_REF: C1101.2, U1201.1
/EXT_SPI_CLK: R823.1, U1301.B14
/EXT_SPI_CS0: R819.1, U1301.A14
/EXT_SPI_CS1: R820.1, U1301.T7
/EXT_SPI_MISO: R821.1, U1301.B13
/EXT_SPI_MOSI: R822.1, U1301.A13
/EXT_TRIG: R802.1, U1202.1, U1302.13
/EXT_UART_MRX: R825.1, U1301.A12
/EXT_UART_MTX: R824.1, U1301.B12
/IF_REF_A: C1134.1, R508.1, R510.1
/IF_REF_B: C1135.1, R608.1, R610.1
/IF_REF_C: C1136.1, R708.1, R710.1
/IF_REF_D: C1133.1, R808.1, R810.1
/LO_3V3_EN: J1001.12, U1301.N14
/LO_-5V_EN: J1001.13, U1301.R3
/LO_AMP_EN: J1001.11, U1301.A4
/LO_BUF_AMP_EN: J1003.8, J1004.8, U1301.T16
/LO_DAC_CS: J1001.7, U1301.R16
/LO_PORT_SEL: J1001.6, U1301.P15
/LO_SPI_CLK: J1001.2, U1301.A3
/LO_SPI_SDI: J1001.4, U1301.B3
/LO_SYNTH_CE: J1001.8, U1301.R4
/LO_SYNTH_CS: J1001.5, U1301.B2
/LO_SYNTH_LOCK: J1001.9, U1301.P4
/MIX_EN: J1003.10, J1004.10, U1301.R12
/MIX_X2: J1003.9, J1004.9, U1301.C13
/PLL_REF_SEL: U1101.9, U1301.R2
/RF_3V3_EN: J1002.12, U1301.C12
/RF_-5V_EN: J1002.13, U1301.B4
/RF_AMP_EN: J1002.11, U1301.A10
/RF_DAC_CS: J1002.7, U1301.B1
/RF_FILT_SW_1: J1002.10, U1301.R1
/RF_FILT_SW_2: J1001.10, U1301.T3
/RF_PORT_SEL: J1002.6, R1327.2, R1328.2
/RF_SPI_CLK: J1002.2, U1301.C3
/RF_SPI_SDI: J1002.4, U1301.C4
/RF_SYNTH_CE: J1002.8, U1301.T2
/RF_SYNTH_CS: J1002.5, U1301.A2
/RF_SYNTH_LOCK: J1002.9, U1301.T1
/SCL: R1104.2, U1101.37, U1301.B11
/SDA: R1105.2, U1101.31, U1301.A11
/SYNTH_REF_AN: R703.2, R714.1, U1008.1, U1101.17
/SYNTH_REF_AP: R702.2, R703.1, U1007.1, U1101.18
/SYNTH_REF_BN: R716.2, R717.1, U1002.1, U1101.22
/SYNTH_REF_BP: R715.2, R716.1, U1001.1, U1101.23
/clock_synth/ADC_CLK: R1114.2, U1101.3
/clock_synth/OUT0N: C1127.1, L1103.1, R1110.2, R1111.1, U1101.33
/clock_synth/OUT0P: C1126.1, L1102.1, R1108.2, R1109.1, U1101.34
/clock_synth/OUT1N: C1125.1, L1101.1, R1106.2, R1107.1, U1101.28
/clock_synth/OUT1P: C1128.1, L1104.1, R1112.2, R1113.1, U1101.29
/control/EEPROM_WP: TP1310.1, U1301.M2, U1301.N3
/control/ETH_LEDG: J1301.GA, U1303.3
/control/ETH_LEDY: J1301.YA, U1303.2
/control/LCD_D7: R1312.1, U1301.J2, U1302.11
/control/MDC: U1301.D13, U1303.17
/control/MDIO: R1349.2, U1301.E13, U1303.16
/control/MII_COL: RN1303.4, U1301.F15
/control/MII_CRS: RN1303.3, U1301.F14
/control/MII_RXD0: RN1303.1, U1301.E14
/control/MII_RXD1: RN1302.4, U1301.D16
/control/MII_RXD2: RN1302.3, U1301.D15
/control/MII_RXD3: RN1302.2, U1301.D14
/control/MII_RX_CLK: RN1302.1, U1301.E16
/control/MII_RX_DV: R1348.2, U1301.F16
/control/MII_RX_ER: RN1303.2, U1301.E15
/control/MII_TXD0: U1301.H15, U1303.22
/control/MII_TXD1: U1301.H14, U1303.23
/control/MII_TXD2: U1301.G16, U1303.24
/control/MII_TXD3: U1301.G15, U1303.25
/control/MII_TX_CLK: R1350.1, U1301.H16
/control/MII_TX_EN: U1301.G14, U1303.21
/control/MMC0_CD: RN1306.2, U1301.C14, U1305.9
/control/MMC0_CLK: RN1305.1, U1301.B15, U1305.5
/control/MMC0_CMD: RN1305.2, U1301.B16, U1305.3
/control/MMC0_D0: RN1306.4, U1301.A16, U1305.7
/control/MMC0_D1: RN1306.3, U1301.A15, U1305.8
/control/MMC0_D2: RN1305.4, U1301.C16, U1305.1
/control/MMC0_D3: RN1305.3, U1301.C15, U1305.2
/control/PMIC_PGOOD: IC1301.2, U1301.N12, U1301.P11
/control/PORT_SEL_GPIO: R1328.1, U1301.N2
/control/PORT_SEL_PRU: R1327.1, U1302.9
/control/RX_N: C1319.1, J1301.6, R1001.2, U1303.30
/control/RX_P: C1320.1, J1301.4, R1002.2, U1303.31
/control/TX_N: C1321.1, J1301.3, R1004.2, U1303.28
/control/TX_P: C1322.1, J1301.1, R1005.2, U1303.29
/control/USB1_DRVVBUS: R1354.1, U1301.M14, U1304.4
/control/USB_DEV_DM: IC1302.2, U1301.K16, X1301.D-
/control/USB_DEV_DP: IC1302.1, U1301.K15, X1301.D+
/control/USB_DEV_ID: IC1302.3, U1301.K14, X1301.ID
/control/USB_HOST_DM: IC1303.2, J1302.2, U1301.L16
/control/USB_HOST_DP: IC1303.1, J1302.3, U1301.L15
/control/USB_HOST_OC: U1301.R15, U1304.5
/control/USR0_LED: D1302.2, U1301.P13
/control/USR1_LED: D1303.2, U1301.T14
/control/USR2_LED: D1304.2, U1301.R14
/control/USR3_LED: D1305.2, U1301.P14
/control/nRST: IC1301.4, R1302.1, R1322.1, R1323.1, R1352.1
/demod_a/CLKP: C535.1, U502.19
/demod_a/FREF: R512.2, U502.35
/demod_a/IFIN: C508.2, U502.47
/demod_b/CLKP: C635.1, U602.19
/demod_b/FREF: R612.2, U602.35
/demod_b/IFIN: C608.2, U602.47
/demod_c/CLKP: C735.1, U702.19
/demod_c/FREF: R712.2, U702.35
/demod_c/IFIN: C708.2, U702.47
/demod_d/CLKP: C835.1, U802.19
/demod_d/FREF: R812.2, U802.35
/demod_d/IFIN: C808.2, U802.47
/front_panel/DEMOD_1: C504.2, U1003.1
/front_panel/DEMOD_2: C604.2, U1004.1
/front_panel/DEMOD_3: C704.2, U1005.1
/front_panel/DEMOD_4: C804.2, U1006.1
GND: C509.2, C510.2, C514.1, C515.2, C517.1, C518.1, C519.1, C520.2, C521.1, C522.2, C524.2, C525.1, C526.2, C527.1, C528.1, C529.1, C530.1, C531.1, C532.1, C533.1, C534.2, C536.1, C537.1, C538.1, C539.1, C609.2, C610.2, C614.1, C615.2, C617.1, C618.1, C619.1, C620.2, C621.1, C622.2, C624.2, C625.1, C626.2, C627.1, C628.1, C629.1, C630.1, C631.1, C632.1, C633.1, C634.2, C636.1, C637.1, C638.1, C639.1, C709.2, C710.2, C714.1, C715.2, C717.1, C718.1, C719.1, C720.2, C721.1, C722.2, C724.2, C725.1, C726.2, C727.1, C728.1, C729.1, C730.1, C731.1, C732.1, C733.1, C734.2, C736.1, C737.1, C738.1, C739.1, C809.2, C810.2, C814.1, C815.2, C817.1, C818.1, C819.1, C820.2, C821.1, C822.2, C824.2, C825.1, C826.2, C827.1, C828.1, C829.1, C830.1, C831.1, C832.1, C833.1, C834.2, C836.1, C837.1, C838.1, C839.1, C901.1, C906.1, C909.1, C912.1, C915.1, C917.1, C1103.2, C1104.2, C1105.2, C1106.2, C1107.2, C1108.2, C1109.2, C1110.2, C1111.2, C1112.2, C1113.2, C1114.2, C1115.2, C1116.2, C1117.2, C1118.2, C1119.2, C1120.2, C1121.2, C1122.2, C1123.2, C1124.2, C1125.2, C1126.2, C1127.2, C1128.2, C1129.2, C1130.2, C1131.2, C1132.2, C1137.2, C1138.2, C1202.2, C1301.2, C1302.2, C1307.2, C1308.2, C1309.2, C1310.2, C1311.2, C1312.2, C1313.2, C1314.2, C1315.2, C1316.2, C1317.2, C1318.2, C1319.2, C1320.2, C1321.2, C1322.2, C1324.2, C1325.2, D1201.2, IC1301.3, IC1302.4, IC1303.4, J901.1, J1001.1, J1001.3, J1001.14, J1001.17, J1001.18, J1002.1, J1002.3, J1002.14, J1002.17, J1002.18, J1003.4, J1003.5, J1003.7, J1004.4, J1004.5, J1004.7, J1201.15, J1202.2, J1202.3, J1302.4, L1303.2, L1304.1, L1306.2, L1307.2, Q1201.2, R501.2, R505.2, R507.2, R508.2, R509.2, R513.1, R601.2, R605.2, R607.2, R608.2, R609.2, R613.1, R701.2, R702.1, R705.2, R707.2, R708.2, R709.2, R713.1, R714.2, R715.1, R717.2, R801.2, R802.2, R805.2, R807.2, R808.2, R809.2, R813.1, R902.2, R903.2, R905.2, R907.2, R1101.2, R1103.2, R1107.2, R1109.2, R1111.2, R1113.2, R1301.2, R1304.2, R1306.2, R1307.2, R1308.2, R1309.2, R1310.2, R1311.2, R1312.2, R1313.2, R1314.2, R1317.2, R1318.2, R1319.2, R1324.2, R1326.1, R1340.2, R1341.2, R1342.2, R1343.2, R1345.2, R1351.1, R1354.2, R1355.1, R1356.1, RN1301.5, RN1301.6, RN1301.7, RN1301.8, S1301.1, S1301.2, U502.3, U502.8, U502.10, U502.16, U502.18, U502.21, U502.22, U502.32, U502.34, U502.36, U502.37, U502.45, U502.49, U602.3, U602.8, U602.10, U602.16, U602.18, U602.21, U602.22, U602.32, U602.34, U602.36, U602.37, U602.45, U602.49, U702.3, U702.8, U702.10, U702.16, U702.18, U702.21, U702.22, U702.32, U702.34, U702.36, U702.37, U702.45, U702.49, U802.3, U802.8, U802.10, U802.16, U802.18, U802.21, U802.22, U802.32, U802.34, U802.36, U802.37, U802.45, U802.49, U903.11, U904.3, U1001.2, U1001.3, U1002.2, U1002.3, U1003.2, U1003.3, U1003.4, U1003.5, U1004.2, U1004.3, U1004.4, U1004.5, U1005.2, U1005.3, U1005.4, U1005.5, U1006.2, U1006.3, U1006.4, U1006.5, U1007.2, U1007.3, U1008.2, U1008.3, U1101.15, U1101.16, U1101.20, U1101.26, U1101.35, U1101.36, U1101.39, U1101.40, U1101.41, U1102.6, U1201.2, U1201.3, U1201.4, U1201.5, U1202.2, U1202.3, U1202.4, U1202.5, U1301.D8, U1301.D9, U1301.E5, U1301.E6, U1301.E7, U1301.E8, U1301.E9, U1301.E10, U1301.E11, U1301.E12, U1301.F5, U1301.F12, U1301.G5, U1301.G12, U1301.H4, U1301.H5, U1301.H12, U1301.H13, U1301.J4, U1301.J5, U1301.J12, U1301.J13, U1301.K5, U1301.K12, U1301.L5, U1301.L12, U1301.M5, U1301.M6, U1301.M7, U1301.M8, U1301.M9, U1301.M10, U1301.M11, U1301.M12, U1301.N8, U1301.N9, U1302.10, U1303.33, U1304.1, U1305.6, X1301.GND, Y1101.2, Y1101.4
unnamed: C504.1, R501.1, R504.1
unnamed: C508.1, R504.2, R505.1
unnamed: C511.1, C512.1, L502.2, U502.1
unnamed: C511.2, U502.5
unnamed: C512.2, C513.1, L503.2, U502.2
unnamed: C513.2, U502.4
unnamed: C514.2, C516.1, U502.11
unnamed: C515.1, U502.7
unnamed: C516.2, C517.2, U502.12
unnamed: C520.1, U502.46
unnamed: C522.1, U502.44
unnamed: C523.1, U502.43
unnamed: C523.2, R509.1, R510.2
unnamed: C524.1, U502.42
unnamed: C526.1, U502.41
unnamed: C527.2, U502.20
unnamed: C529.2, RN501.4, U502.23
unnamed: C530.2, RN501.3, U502.24
unnamed: C531.2, RN501.1, U502.25
unnamed: C532.2, C533.2, L504.1, U502.26, U502.27
unnamed: C536.2, RN502.4, U502.28
unnamed: C537.2, RN502.3, U502.29
unnamed: C538.2, RN502.2, U502.30
unnamed: C539.2, RN502.1, U502.31
unnamed: C604.1, R601.1, R604.1
unnamed: C608.1, R604.2, R605.1
unnamed: C611.1, C612.1, L602.2, U602.1
unnamed: C611.2, U602.5
unnamed: C612.2, C613.1, L603.2, U602.2
unnamed: C613.2, U602.4
unnamed: C614.2, C616.1, U602.11
unnamed: C615.1, U602.7
unnamed: C616.2, C617.2, U602.12
unnamed: C620.1, U602.46
unnamed: C622.1, U602.44
unnamed: C623.1, U602.43
unnamed: C623.2, R609.1, R610.2
unnamed: C624.1, U602.42
unnamed: C626.1, U602.41
unnamed: C627.2, U602.20
unnamed: C629.2, RN601.4, U602.23
unnamed: C630.2, RN601.3, U602.24
unnamed: C631.2, RN601.1, U602.25
unnamed: C632.2, C633.2, L604.1, U602.26, U602.27
unnamed: C636.2, RN602.4, U602.28
unnamed: C637.2, RN602.3, U602.29
unnamed: C638.2, RN602.2, U602.30
unnamed: C639.2, RN602.1, U602.31
unnamed: C704.1, R701.1, R704.1
unnamed: C708.1, R704.2, R705.1
unnamed: C711.1, C712.1, L702.2, U702.1
unnamed: C711.2, U702.5
unnamed: C712.2, C713.1, L703.2, U702.2
unnamed: C713.2, U702.4
unnamed: C714.2, C716.1, U702.11
unnamed: C715.1, U702.7
unnamed: C716.2, C717.2, U702.12
unnamed: C720.1, U702.46
unnamed: C722.1, U702.44
unnamed: C723.1, U702.43
unnamed: C723.2, R709.1, R710.2
unnamed: C724.1, U702.42
unnamed: C726.1, U702.41
unnamed: C727.2, U702.20
unnamed: C729.2, RN701.4, U702.23
unnamed: C730.2, RN701.3, U702.24
unnamed: C731.2, RN701.1, U702.25
unnamed: C732.2, C733.2, L704.1, U702.26, U702.27
unnamed: C736.2, RN702.4, U702.28
unnamed: C737.2, RN702.3, U702.29
unnamed: C738.2, RN702.2, U702.30
unnamed: C739.2, RN702.1, U702.31
unnamed: C804.1, R801.1, R804.1
unnamed: C808.1, R804.2, R805.1
unnamed: C811.1, C812.1, L802.2, U802.1
unnamed: C811.2, U802.5
unnamed: C812.2, C813.1, L803.2, U802.2
unnamed: C813.2, U802.4
unnamed: C814.2, C816.1, U802.11
unnamed: C815.1, U802.7
unnamed: C816.2, C817.2, U802.12
unnamed: C820.1, U802.46
unnamed: C822.1, U802.44
unnamed: C823.1, U802.43
unnamed: C823.2, R809.1, R810.2
unnamed: C824.1, U802.42
unnamed: C826.1, U802.41
unnamed: C827.2, U802.20
unnamed: C829.2, RN801.4, U802.23
unnamed: C830.2, RN801.3, U802.24
unnamed: C831.2, RN801.1, U802.25
unnamed: C832.2, C833.2, L804.1, U802.26, U802.27
unnamed: C836.2, RN802.4, U802.28
unnamed: C837.2, RN802.3, U802.29
unnamed: C838.2, RN802.2, U802.30
unnamed: C839.2, RN802.1, U802.31
unnamed: C906.2, U903.4
unnamed: C909.2, U903.6, U903.7
unnamed: C912.2, U903.8
unnamed: C1101.1, C1102.2, R1101.1
unnamed: C1102.1, R1102.2, R1103.1, U1101.6
unnamed: C1104.1, U1101.7, Y1101.1
unnamed: C1105.1, U1101.8, Y1101.3
unnamed: C1113.1, U1101.11, U1101.12, U1101.13
unnamed: C1129.1, C1133.2, L1101.2
unnamed: C1130.1, C1134.2, L1102.2
unnamed: C1131.1, C1135.2, L1103.2
unnamed: C1132.1, C1136.2, L1104.2
unnamed: C1137.1, C1138.1, L1105.2, U1102.7
unnamed: C1303.1, Q1301.2, R1325.1, U1301.P16
unnamed: C1303.2, C1304.2, U1301.N15
unnamed: C1304.1, Q1301.1, R1325.2, U1301.N16
unnamed: C1305.1, C1306.1, U1301.A7, U1301.B7
unnamed: C1305.2, C1306.2, U1301.A9, U1301.B9
unnamed: C1307.1, Q1302.2, R1337.1
unnamed: C1308.1, Q1302.1, R1338.2, R1339.2
unnamed: C1309.1, C1310.1, U1303.6
unnamed: C1311.1, C1312.1, C1313.1, L1301.2, R1001.1, R1002.1, R1004.1, R1005.1, R1353.1, U1303.1, U1303.27
unnamed: C1315.1, J1301.2, J1301.5, R1353.2
unnamed: C1317.1, J1301.8
unnamed: D901.1, R905.1
unnamed: D902.1, R907.1
unnamed: D1201.1, F1201.1, L1201.1
unnamed: D1302.1, RN1301.1
unnamed: D1303.1, RN1301.2
unnamed: D1304.1, RN1301.3
unnamed: D1305.1, RN1301.4
unnamed: F1201.2, J1202.1
unnamed: J1201.1, R803.2
unnamed: J1201.2, R815.2
unnamed: J1201.3, R817.2
unnamed: J1201.4, R819.2
unnamed: J1201.5, R821.2
unnamed: J1201.6, R823.2
unnamed: J1201.7, R825.2
unnamed: J1201.9, R814.2
unnamed: J1201.10, R816.2
unnamed: J1201.11, R818.2
unnamed: J1201.12, R820.2
unnamed: J1201.13, R822.2
unnamed: J1201.14, R824.2
unnamed: J1301.13, L1304.2
unnamed: J1301.GK, R1355.2
unnamed: J1301.YK, R1356.2
unnamed: J1302.1, L1305.1
unnamed: J1302.5, L1306.1
unnamed: L502.1, L503.1, R506.2
unnamed: L602.1, L603.1, R606.2
unnamed: L702.1, L703.1, R706.2
unnamed: L802.1, L803.1, R806.2
unnamed: L1201.2, Q1201.1
unnamed: L1302.2, X1301.VBUS
unnamed: L1303.1, X1301.CGND
unnamed: L1307.1, U1305.G1, U1305.G2, U1305.G3, U1305.G4
unnamed: R507.1, U502.13
unnamed: R511.2, U502.33
unnamed: R607.1, U602.13
unnamed: R611.2, U602.33
unnamed: R707.1, U702.13
unnamed: R711.2, U702.33
unnamed: R807.1, U802.13
unnamed: R811.2, U802.33
unnamed: R903.1, U904.5
unnamed: R904.2, U904.4
unnamed: R906.1, U903.3
unnamed: R1114.1, U1102.1
unnamed: R1115.1, U1102.2
unnamed: R1116.1, U1102.3
unnamed: R1117.1, U1102.4
unnamed: R1118.2, U1102.5
unnamed: R1301.1, U1301.M16
unnamed: R1302.2, U1301.R11
unnamed: R1304.1, U1301.M3
unnamed: R1305.1, U1301.L1
unnamed: R1306.1, U1301.L2
unnamed: R1307.1, U1301.L3
unnamed: R1308.1, U1301.K1
unnamed: R1309.1, U1301.K2
unnamed: R1310.1, U1301.K3
unnamed: R1311.1, U1301.J1
unnamed: R1313.1, U1301.J3, U1302.7
unnamed: R1314.1, U1301.H1, U1302.5
unnamed: R1315.1, U1301.H2, U1302.3
unnamed: R1316.1, U1301.H3, U1302.12
unnamed: R1317.1, U1301.G1, U1302.14
unnamed: R1318.1, U1301.G2, U1302.16
unnamed: R1319.1, U1301.G3, U1302.18
unnamed: R1320.1, U1301.E3
unnamed: R1321.1, U1301.E2
unnamed: R1322.2, U1302.1
unnamed: R1323.2, U1302.19
unnamed: R1324.1, U1301.D3
unnamed: R1326.2, U1301.L14
unnamed: R1337.2, R1338.1, U1303.4
unnamed: R1339.1, U1303.5
unnamed: R1340.1, RN1302.8, U1303.7
unnamed: R1341.1, RN1302.7, U1303.8
unnamed: R1342.1, RN1302.6, U1303.9
unnamed: R1343.1, RN1303.7, U1303.13
unnamed: R1344.1, RN1302.5, U1303.10
unnamed: R1345.1, U1303.32
unnamed: R1346.1, RN1303.8, U1303.11
unnamed: R1347.1, RN1303.5, U1303.15
unnamed: R1348.1, U1303.26
unnamed: R1350.2, U1303.20
unnamed: R1351.2, U1303.18
unnamed: R1352.2, U1303.19
unnamed: RN1303.6, U1303.14
unnamed: S1301.3, S1301.4, U1301.T11
unnamed: TP1301.1, U1301.F4
unnamed: TP1302.1, U1301.G4
unnamed: TP1303.1, U1301.F13
unnamed: TP1304.1, U1301.G13
unnamed: TP1307.1, U1301.F2
unnamed: TP1308.1, U1301.E1
unnamed: TP1309.1, U1301.N13
unnamed: U1301.C10, U1301.D10
unnamed: U1301.C11, U1301.D11
unnamed: U1301.D4, U1301.E4
unnamed: U1301.D6, U1301.D7
unnamed: U1301.L4, U1301.M4
unnamed: U1301.N4, U1301.N5
unnamed: U1301.N10, U1301.N11
SYS_5V: U1301.K6, U1301.K7, U1301.L6, U1301.L7, U1304.2, U1304.3
USB_DC: C1324.1, IC1302.6, L1302.1, U1301.J16, U1301.P9, U1301.R9, U1301.T9
VDD_3V3A: C1302.1, R1305.2, R1315.2, R1316.2, R1320.2, R1321.2, U1301.F8, U1301.F9, U1301.G8, U1301.G9, U1301.H7, U1301.H8, U1301.H9, U1301.J7, U1301.J8, U1301.J9, U1301.K8, U1301.K9, U1301.L8, U1301.L9, U1302.20
VDD_3V3AUX: U1301.F11, U1301.G11
VDD_3V3B: C1314.1, C1316.1, C1318.1, L1301.1, R1344.2, R1346.2, R1347.2, R1349.1, RN1305.5, RN1305.6, RN1305.7, RN1305.8, RN1306.5, RN1306.6, RN1306.7, RN1306.8, U1301.F6, U1301.F7, U1301.G6, U1301.G7, U1303.12, U1305.4
VDD_5V: C1325.1, IC1303.6, L1305.2, U1304.6, U1304.7, U1304.8
VDD_RTC: C1301.1, IC1301.5, U1301.K11, U1301.L11
VPP: C915.2, D901.2, J901.2, J1001.15, J1001.16, J1002.15, J1002.16, J1003.1, J1003.3, J1004.1, J1004.3, R901.1, R904.1, U903.9, U903.10
