loxodes/vna/hardware/vna_rev1/vna_r1_synth/vna_r1_synth.kicad_pcb

## KiCad design hardware/vna_rev1/vna_r1_synth/vna_r1_synth.kicad_pcb (2018-05-20)

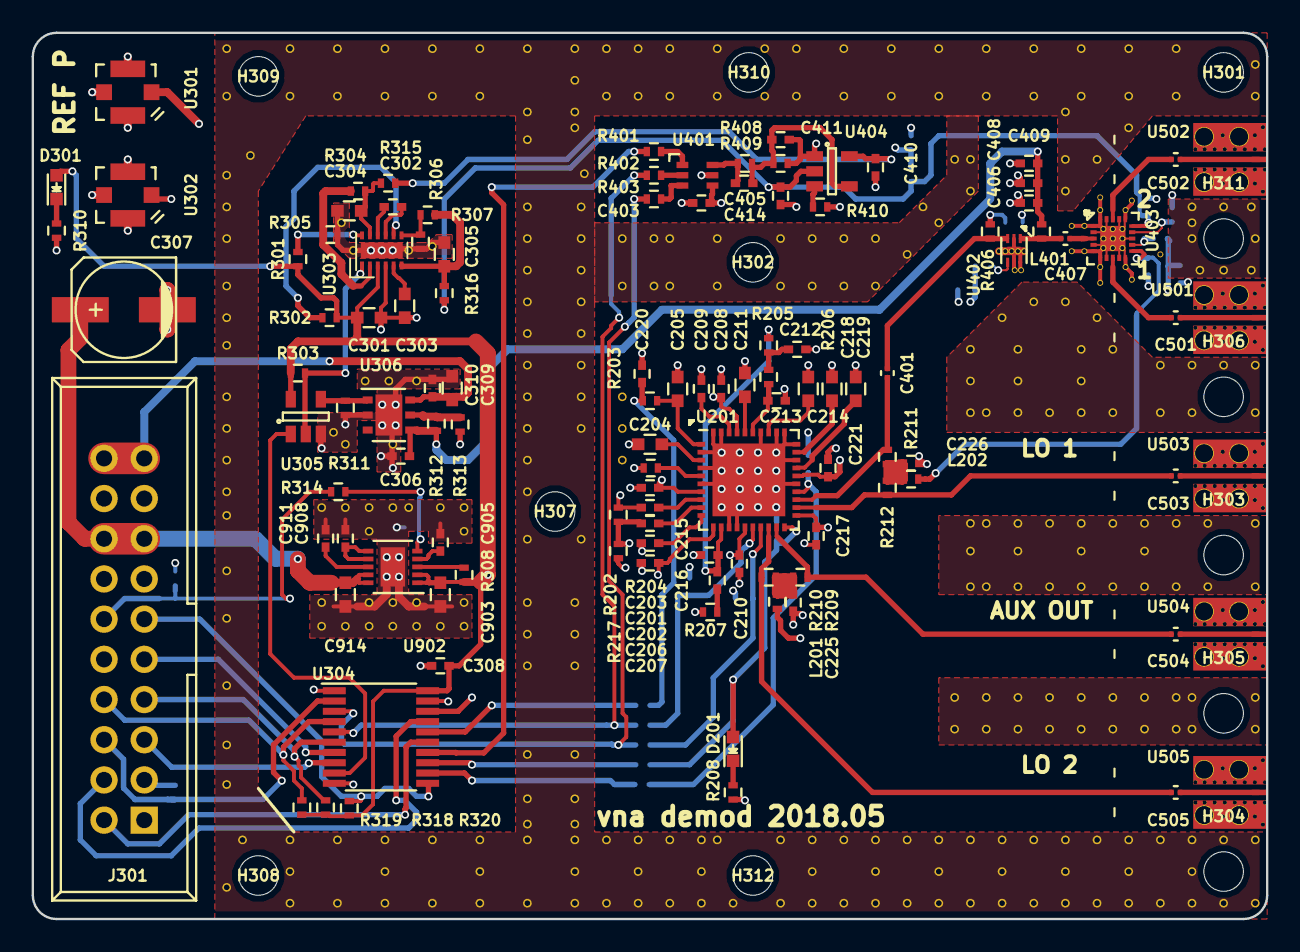
[picture p109: board vna_r1_synth.kicad_pcb from above]

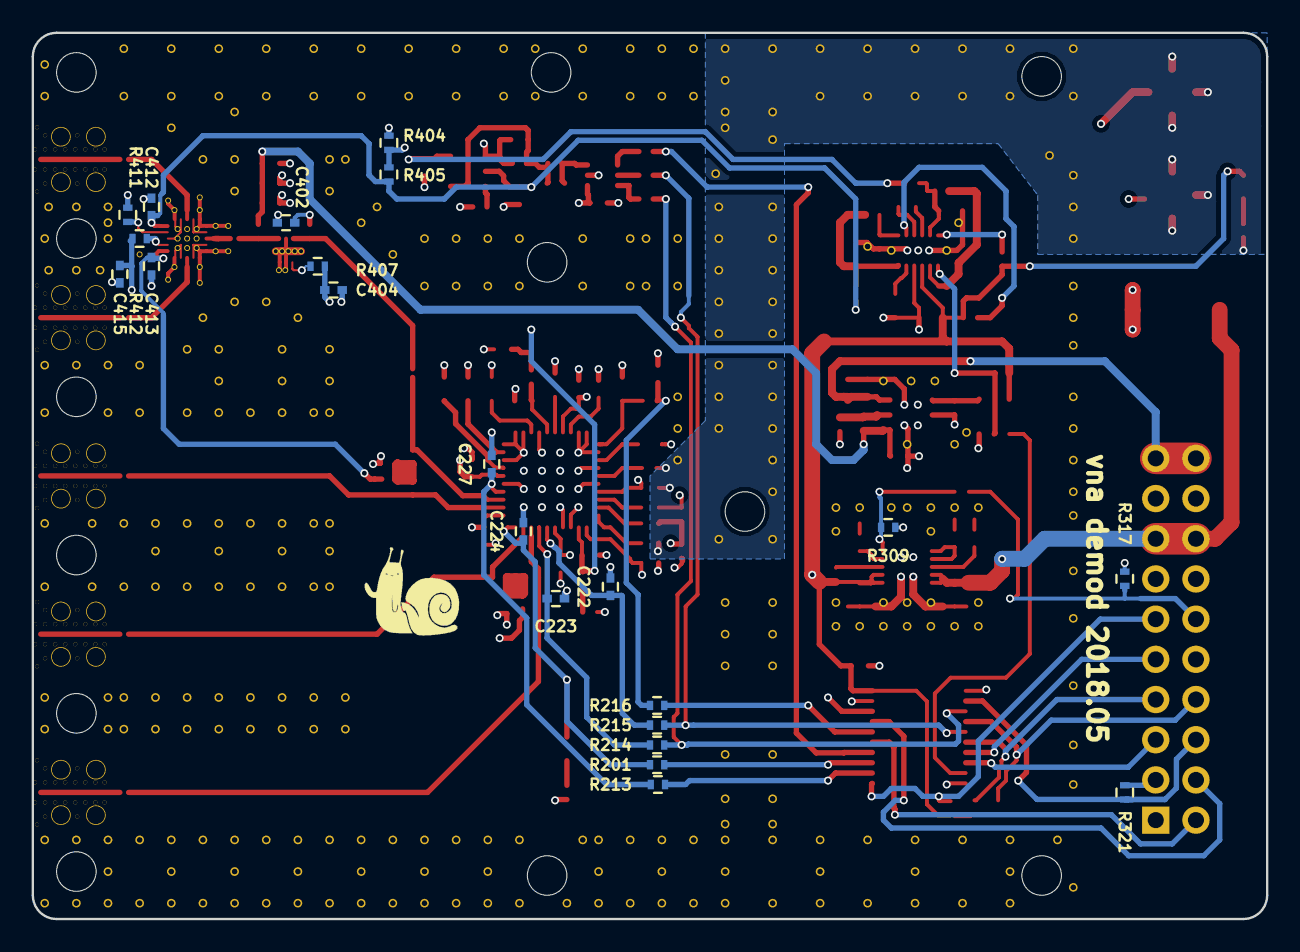
[picture p110: board vna_r1_synth.kicad_pcb from below]

Board: 4 copper layers, 78.0 x 56.0 mm, 147 parts (22 on the bottom side), 92 nets.

Parts:
C201, C202, C217, C310, C402, C403, C408, C410, C414: 100 nF; C_0402
C203, C206, C207, C208, C209, C210, C221, C302, C308, C409, C905, C908, C911: 1 uF; C_0402
C204, C211, C214, C218, C219, C903, C914: 10 uF; C_0603
C205: 10 pF; C_0603
C212, C405, C411: DNP; C_0402
C213: 1800 pF; C_0402
C215: 390 pF; C_0402
C216: 68 nF; C_0402
C220, C222, C223, C224, C227, C404, C406, C412, C413, C415: 10 pF; C_0402
C225, C226: 10 nF; C_0402
C301, C303, C304, C305, C309: 2.2 uF; C_0603
C306: 2.2 uF; C_0402
C307: 220 uF; c_elec_6.3x5.8
C401, C407: 10 pF; C_0201
C501, C502, C503, C504, C505: C_Small; C_0201
D201, D301: RED; LED_0603
H301, H302, H303, H304, H305, H306, H307, H308, H309, H310, H311, H312: MOUNTING_HOLE; MountingHole_2-5mm
J301: Conn_02x10_Odd_Even; IDC_Header_Straight_20pins
L201, L202: 22 nH; R_0402
L401: BLM15GG471; R_0402
R201, R214, R215, R216: 22; R_0402
R202: 100; R_0402
R203, R204, R314, R406, R412: 1k; R_0402
R205, R308, R315, R316, R407, R410, R411: JMP; R_0402
R206: 18; R_0402
R207: 68; R_0402
R208, R301, R302, R303, R309, R310, R311, R312, R317, R318, R319, R320, R321: 10k; R_0402
R209, R210, R211, R212, R213: 51; R_0402
R217: DNP; R_0402
R304, R305, R306, R307: 499k; R_0402
R313: 47k; R_0402
R401, R402, R403: R_Small; R_0402
R404: 4k7; R_0402
R405: 1k2; R_0402
R408: 100k; R_0402
R409: 82k; R_0402
U201: LMX2594; QFN-40-1EP_6x6mm_Pitch0.5mm
U301, U302: CONN_SMA_2GND; 734120110_ufl_umc
U303: LM27762; WSON-12-1EP_3x2mm_Pitch0.5mm
U304: 74HC244; TSSOP-20_4.4x6.5mm_Pitch0.65mm
U305: 74LVC1G32; SOT-23-5
U306: LD39100; DFN-6-1EP_3x3mm_Pitch0.95mm
U401: LTC2630-LZ8; SC-70-6
U402: MAAM-011100; TDFN6
U403: ADRF5020; ADRF5020BCCZN
U404: LTC2054CS5; SOT-23-5
U501, U502, U503, U504, U505: CONN_SMA_2GND; SMA_901-10512_6p7MIL_FR408_CPW_LAUNCH
U902: ADP7158; DFN-10-1EP_3x3mm_Pitch0.5mm

Connections:
+2V5: C410.1, R315.2, U404.5
+3V3: C203.2, C207.2, C208.2, C210.2, C217.1, C221.2, C301.2, C308.2, C403.2, C413.1, C903.2, D301.2, L201.1, L202.1, R301.2, R302.2, R303.2, R308.1, R318.1, R319.1, R320.1, U201.7, U201.11, U201.15, U201.21, U201.26, U201.37, U303.3, U304.20, U305.5, U401.4, U403.11, U902.1, U902.2
+5V: C309.2, C310.2, J301.19, J301.20, U306.6
-2V5: C412.1, C414.1, R316.2, R405.1, U403.15, U404.2
/AMP_VD: C306.2, C406.1, C408.1, C409.1, L401.1, R312.2, U306.4
/AUX_OUT: C504.2, R209.2, U201.19
/DAC_CS: R401.2, U304.14
/LO_PORT1: C503.2, R212.1, U201.22
/LO_PORT2: C505.2, R210.1, U201.18
/PORT_SEL: C415.1, R412.1, U304.18
/RF_PORT: C401.2, R211.2, U201.23
/SPI_SCK: R215.2, R402.2, U304.5
/SPI_SDI: R214.2, R403.2, U304.3
/conn_front/PORT_1: C501.2, U403.8
/conn_front/PORT_2: C502.2, U403.18
/conn_power/3V3_DEMOD_ENABLE: J301.12, R314.1, R317.2
/conn_power/DAC_CS_EXT: J301.7, R318.2, U304.6
/conn_power/LMX_CE: R216.2, U304.16
/conn_power/LMX_CE_EXT: J301.8, R319.2, U304.4
/conn_power/LMX_CS: R213.2, U304.12
/conn_power/LMX_CS_EXT: J301.5, U304.8
/conn_power/LMX_LCK: R201.2, U304.13
/conn_power/LMX_LCK_EXT: J301.9, U304.7
/conn_power/PORT_SEL_EXT: J301.6, R321.2, U304.2
/conn_power/SCK_EXT: J301.2, U304.15
/conn_power/SDI_EXT: J301.4, U304.17
/conn_power/SYNTH_REF_N: C202.1, R202.1, R217.2, U302.1
/conn_power/SYNTH_REF_P: C201.1, R202.2, U301.1
/conn_power/~AMP_EN: U304.9, U305.1
/conn_power/~AMP_EN_EXT: J301.11, R320.2, U304.11
/conn_power/~PGOOD: R303.1, U303.1, U305.2
/rf_port_amp_sw/AMP_VCTL: C404.1, C411.2, R407.1, R409.1, U404.1
/synth/CE: C220.1, R203.2, R216.1
/synth/CPOUT: C215.1, C216.1, R205.2, U201.12
/synth/CSB: C227.1, R213.1, U201.24
/synth/MUXout: C224.1, D201.2, R201.1, U201.20
/synth/SCK: C222.1, R215.1, U201.16
/synth/SDI: C223.1, R214.1, U201.17
GND: C203.1, C204.2, C205.2, C206.1, C207.1, C208.1, C209.2, C210.1, C211.2, C212.2, C213.2, C214.2, C215.2, C217.2, C218.2, C219.2, C220.2, C221.1, C222.2, C223.2, C224.2, C225.1, C226.1, C227.2, C301.1, C303.1, C304.1, C305.2, C306.1, C307.2, C308.1, C309.1, C310.1, C402.2, C403.1, C404.2, C406.2, C408.2, C409.2, C410.2, C412.2, C413.2, C414.2, C415.2, C903.1, C905.1, C908.1, C911.1, C914.1, J301.1, J301.3, J301.14, J301.17, J301.18, R204.2, R207.2, R208.1, R217.1, R305.1, R306.2, R309.1, R310.1, R311.2, R313.1, R317.1, R321.1, R404.2, R410.1, R411.2, U201.2, U201.4, U201.6, U201.13, U201.14, U201.25, U201.28, U201.30, U201.31, U201.32, U201.34, U201.39, U201.40, U201.41, U301.2, U301.3, U302.2, U302.3, U303.4, U303.13, U304.1, U304.10, U304.19, U305.3, U306.2, U306.7, U401.5, U402.2, U402.5, U402.6, U402.7, U403.1, U403.2, U403.4, U403.5, U403.6, U403.7, U403.9, U403.10, U403.13, U403.16, U403.17, U403.19, U403.20, U403.21, U501.2, U501.3, U502.2, U502.3, U503.2, U503.3, U504.2, U504.3, U505.2, U505.3, U902.11
unnamed: C201.2, U201.8
unnamed: C202.2, U201.9
unnamed: C204.1, U201.3
unnamed: C205.1, R203.1, U201.1
unnamed: C206.2, U201.10
unnamed: C209.1, U201.38
unnamed: C211.1, U201.36
unnamed: C212.1, R205.1, R206.2
unnamed: C213.1, R206.1, U201.35
unnamed: C214.1, U201.33
unnamed: C216.2, R207.1
unnamed: C218.1, U201.29
unnamed: C219.1, U201.27
unnamed: C225.2, L201.2, R209.1, R210.2
unnamed: C226.2, L202.2, R211.1, R212.2
unnamed: C302.1, U303.10
unnamed: C302.2, U303.9
unnamed: C303.2, U303.5
unnamed: C304.2, R304.2, R315.1, U303.11
unnamed: C305.1, R307.1, R316.1, U303.6
unnamed: C401.1, R406.2, U402.3
unnamed: C402.1, R404.1, R405.2, R406.1
unnamed: C405.1, R408.1, U401.6
unnamed: C405.2, C411.1, R408.2, R409.2, U404.4
unnamed: C407.1, U403.3
unnamed: C407.2, L401.2, U402.1
unnamed: C501.1, U501.1
unnamed: C502.1, U502.1
unnamed: C503.1, U503.1
unnamed: C504.1, U504.1
unnamed: C505.1, U505.1
unnamed: C905.2, U902.4
unnamed: C908.2, U902.6, U902.7
unnamed: C911.2, U902.8
unnamed: D201.1, R208.2
unnamed: D301.1, R310.2
unnamed: R204.1, U201.5
unnamed: R301.1, U303.12
unnamed: R302.1, U303.8
unnamed: R304.1, R305.2, U303.2
unnamed: R306.1, R307.2, U303.7
unnamed: R308.2, U902.3
unnamed: R309.2, R314.2, U902.5
unnamed: R311.1, U305.4, U306.1
unnamed: R312.1, R313.2, U306.5
unnamed: R401.1, U401.1
unnamed: R402.1, U401.2
unnamed: R403.1, U401.3
unnamed: R407.2, U402.4
unnamed: R410.2, U404.3
unnamed: R411.1, U403.14
unnamed: R412.2, U403.12
VPP: C307.1, C914.2, J301.15, J301.16, U902.9, U902.10
