loxodes/vna/breakouts/maam_011109_bias/maam_011109_bias.kicad_pcb

## KiCad design breakouts/maam_011109_bias/maam_011109_bias.kicad_pcb (2019-10-19)

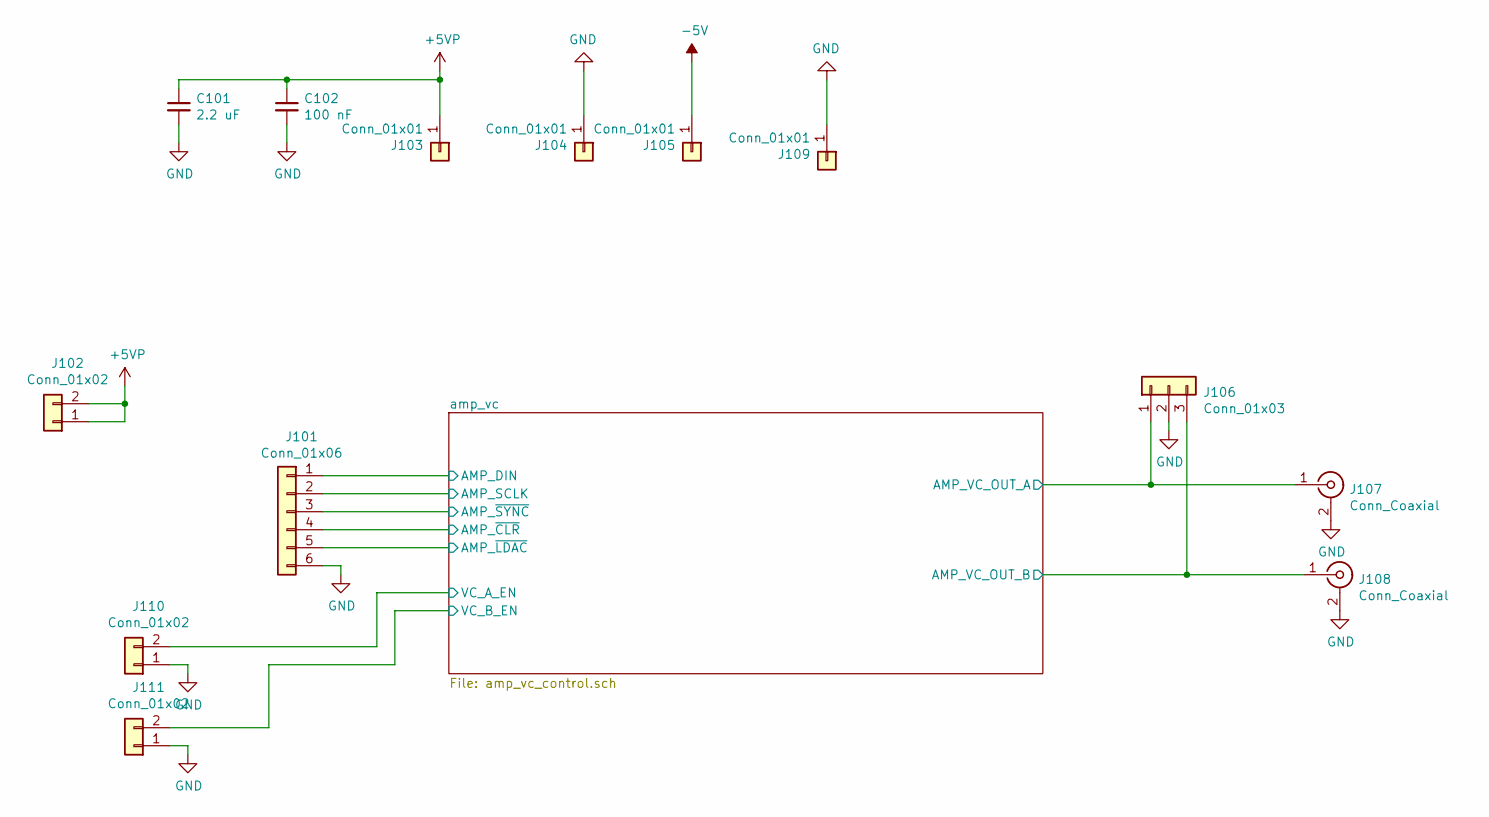
[picture p111: schematic maam_011109_bias.sch]

Parts:
C101: 2.2 uF; C_0603
C102: 100 nF; C_0402
J101: Conn_01x06; Pin_Header_Straight_1x06
J102, J110, J111: Conn_01x02; Pin_Header_Straight_1x02
J103, J104, J105, J109: Conn_01x01; TURRET_MILLMAX_2101
J106: Conn_01x03; Pin_Header_Straight_1x03
J107, J108: Conn_Coaxial; 732512200_SMA

Connections:
+5VP: C101.1, C102.1, J102.1, J102.2, J103.1; also elsewhere on the board
-5V: J105.1; also elsewhere on the board
/amp_vc/AMP_DIN: J101.1; also elsewhere on the board
/amp_vc/AMP_SCLK: J101.2; also elsewhere on the board
/amp_vc/AMP_VC_OUT_A: J106.1, J107.1 (In); also elsewhere on the board
/amp_vc/AMP_VC_OUT_B: J106.3, J108.1 (In); also elsewhere on the board
/amp_vc/AMP_~CLR: J101.4; also elsewhere on the board
/amp_vc/AMP_~LDAC: J101.5; also elsewhere on the board
/amp_vc/AMP_~SYNC: J101.3; also elsewhere on the board
/amp_vc/VC_A_EN: J110.2; also elsewhere on the board
/amp_vc/VC_B_EN: J111.2; also elsewhere on the board
GND: C101.2, C102.2, J101.6, J104.1, J106.2, J107.2 (Ext), J108.2 (Ext), J109.1, J110.1, J111.1; also elsewhere on the board
