loxodes/vna/breakouts/maam_011109_bias/maam_011109_bias.kicad_pcb

## KiCad design breakouts/maam_011109_bias/maam_011109_bias.kicad_pcb (continued)

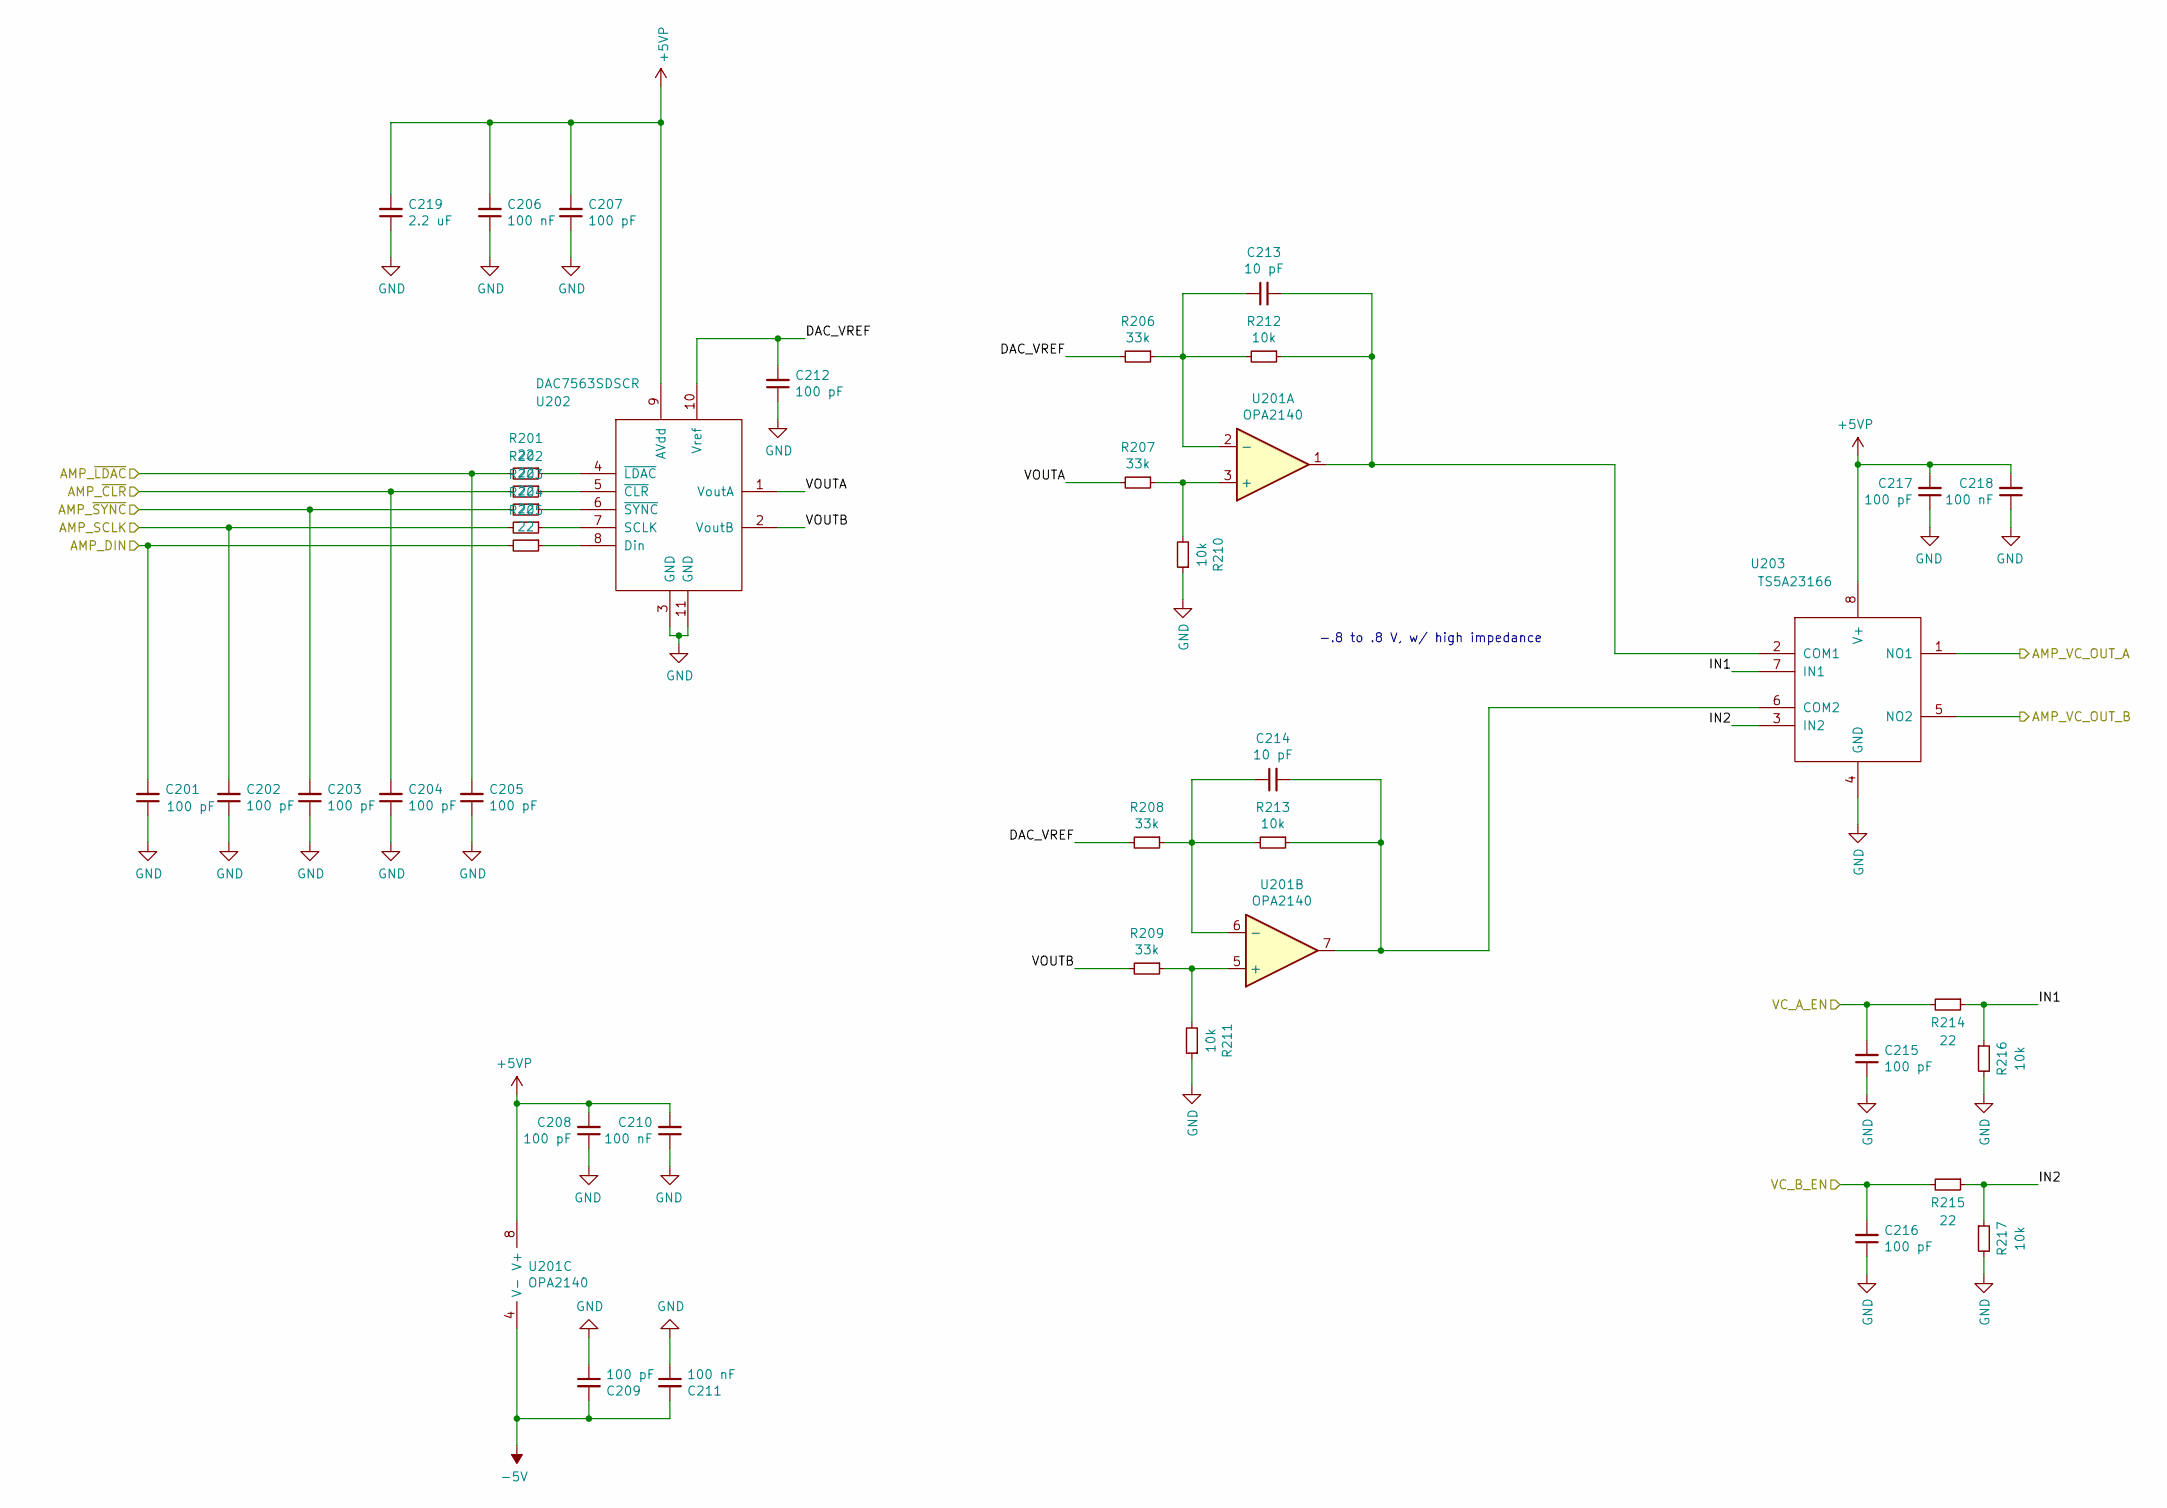
[picture p112: schematic amp_vc_control.sch]

Parts:
C201, C202, C203, C204, C205, C207, C208, C209, C212, C215, C216, C217: 100 pF; C_0402
C206, C210, C211, C218: 100 nF; C_0402
C213, C214: 10 pF; C_0402
C219: 2.2 uF; C_0603
R201, R202, R203, R204, R205, R214, R215: 22; R_0402
R206, R207, R208, R209: 33k; R_0603
R210, R211, R212, R213: 10k; R_0603
R216, R217: 10k; R_0402
U201: OPA2140; MSOP-8_3x3mm_Pitch0.65mm
U202: DAC7563SDSCR; DFN-10-1EP_3x3mm_Pitch0.5mm
U203: TS5A23166; VSSOP-8

Connections:
+5VP: C206.2, C207.2, C208.2, C210.2, C217.2, C218.2, C219.2, U201.8 (V+), U202.9 (AVdd), U203.8 (V+); also elsewhere on the board
-5V: C209.2, C211.2, U201.4 (V-); also elsewhere on the board
/amp_vc/AMP_DIN: C201.2, R205.2; also elsewhere on the board
/amp_vc/AMP_SCLK: C202.2, R204.2; also elsewhere on the board
/amp_vc/AMP_VC_OUT_A: U203.1 (NO1); also elsewhere on the board
/amp_vc/AMP_VC_OUT_B: U203.5 (NO2); also elsewhere on the board
/amp_vc/AMP_~CLR: C204.2, R202.2; also elsewhere on the board
/amp_vc/AMP_~LDAC: C205.2, R201.2; also elsewhere on the board
/amp_vc/AMP_~SYNC: C203.2, R203.2; also elsewhere on the board
/amp_vc/DAC_VREF: C212.2, R206.2, R208.2, U202.10 (Vref)
/amp_vc/IN1: R214.1, R216.1, U203.7 (IN1)
/amp_vc/IN2: R215.1, R217.1, U203.3 (IN2)
/amp_vc/VC_A_EN: C215.2, R214.2; also elsewhere on the board
/amp_vc/VC_B_EN: C216.2, R215.2; also elsewhere on the board
/amp_vc/VOUTA: R207.2, U202.1 (VoutA)
/amp_vc/VOUTB: R209.2, U202.2 (VoutB)
GND: C201.1, C202.1, C203.1, C204.1, C205.1, C206.1, C207.1, C208.1, C209.1, C210.1, C211.1, C212.1, C215.1, C216.1, C217.1, C218.1, C219.1, R210.1, R211.1, R216.2, R217.2, U202.3 (GND), U202.11 (GND), U203.4 (GND); also elsewhere on the board
unnamed: C213.1, R206.1, R212.2, U201.2 (-)
unnamed: C213.2, R212.1, U201.1, U203.2 (COM1)
unnamed: C214.1, R208.1, R213.2, U201.6 (-)
unnamed: C214.2, R213.1, U201.7, U203.6 (COM2)
unnamed: R201.1, U202.4 (~LDAC)
unnamed: R202.1, U202.5 (~CLR)
unnamed: R203.1, U202.6 (~SYNC)
unnamed: R204.1, U202.7 (SCLK)
unnamed: R205.1, U202.8 (Din)
unnamed: R207.1, R210.2, U201.3 (+)
unnamed: R209.1, R211.2, U201.5 (+)

Notes on the sheet:
-.8 to .8 V, w/ high impedance

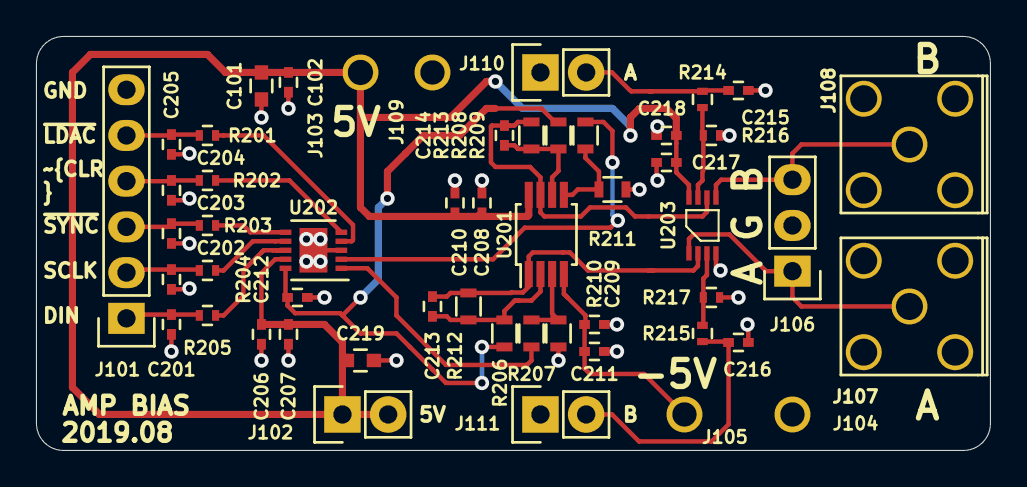
[picture p113: board maam_011109_bias.kicad_pcb from above]

Board: 2 copper layers, 53.0 x 23.0 mm, 52 parts (0 on the bottom side), 28 nets.
