loxodes/vna/breakouts/sequencing_ltc2937/sequencing_ltc2937.kicad_pcb

## KiCad design breakouts/sequencing_ltc2937/sequencing_ltc2937.kicad_pcb (2019-10-01)

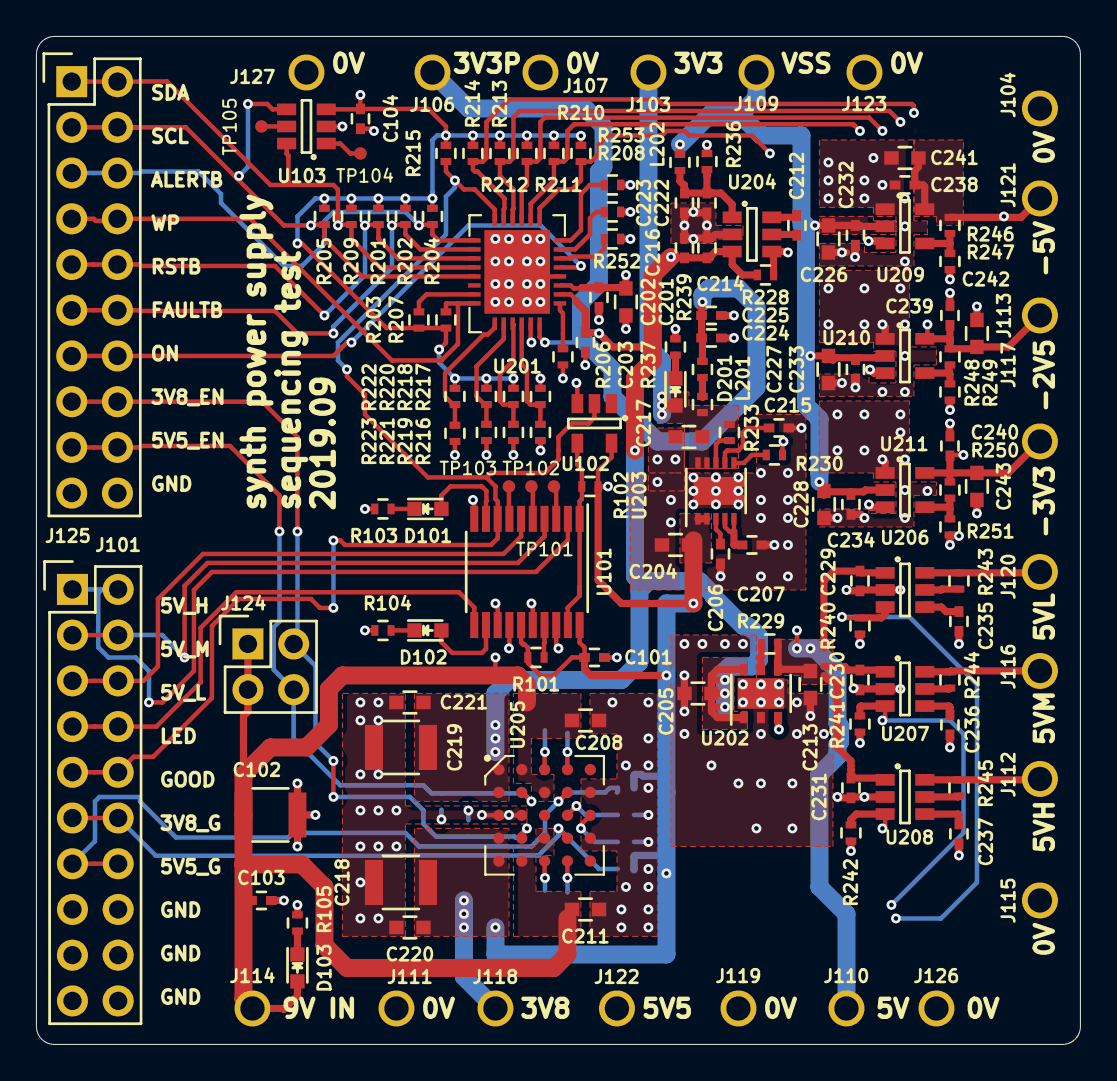
[picture p114: board sequencing_ltc2937.kicad_pcb from above]

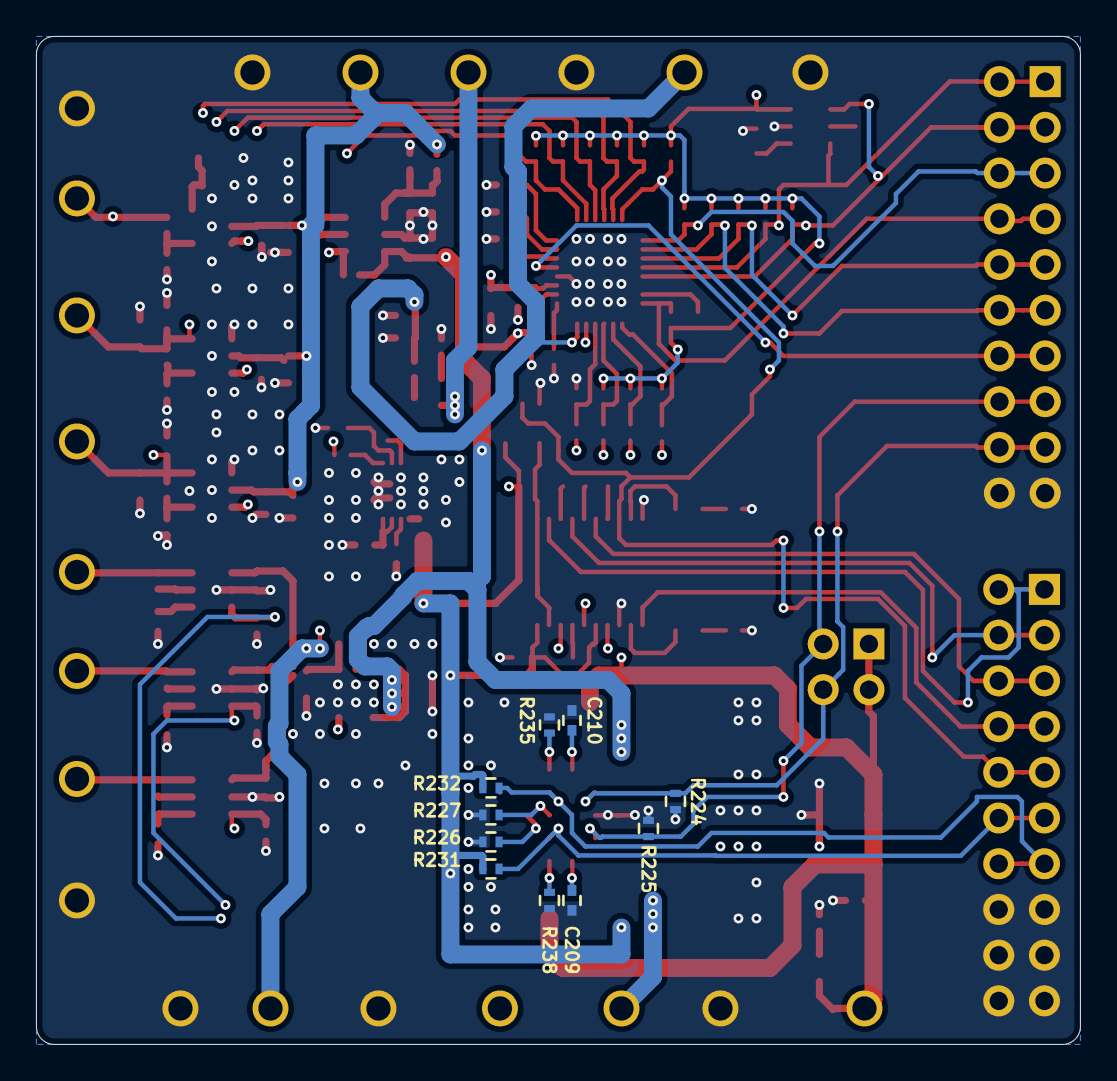
[picture p115: board sequencing_ltc2937.kicad_pcb from below]

Board: 4 copper layers, 58.0 x 56.0 mm, 153 parts (10 on the bottom side), 87 nets.

Parts:
C101, C104, C202, C203, C209, C210, C214, C222, C225, C232, C233, C234: 100 nF; C_0402
C102, C218, C219: 47 uF; C_1210
C103, C206, C207, C212, C215, C216, C223, C224, C229, C230, C231: 1 uF; C_0402
C201, C205, C213, C220, C221, C226, C227, C228, C241, C242, C243: 2.2 uF; C_0603
C204, C208, C211, C217: 10 uF; C_0603
C235, C236, C237: DNI; C_0402
C238, C239, C240: 10 nF; C_0402
D101, D102, D103, D201: LED_Small; LED_0603
J101, J125: Conn_02x10_Odd_Even; Pin_Header_Straight_2x10
J103, J106: 3.3VP; TURRET_MILLMAX_2101
J104, J107, J111, J115, J119, J123, J126, J127: GND; TURRET_MILLMAX_2101
J109: VSS; TURRET_MILLMAX_2101
J110: +5VP; TURRET_MILLMAX_2101
J112: VX2; TURRET_MILLMAX_2101
J113: -2V5; TURRET_MILLMAX_2101
J114: +9V; TURRET_MILLMAX_2101
J116: VAMP_MID; TURRET_MILLMAX_2101
J117: -3V3; TURRET_MILLMAX_2101
J118: +3V8; TURRET_MILLMAX_2101
J120: VAMP_LOW; TURRET_MILLMAX_2101
J121: -5V; TURRET_MILLMAX_2101
J122: +6V; TURRET_MILLMAX_2101
J124: Conn_02x02_Odd_Even; Pin_Header_Straight_2x02
L201, L202: BLM15GG471; R_0402
R101, R102, R103, R104, R105, R203, R205, R207, R209, R210, R211, R212, R213, R214, R215, R218, R220, R222, R224, R225, R231, R232, R237, R240, R241, R242: 10k; R_0402
R201, R202, R204, R216: 100k; R_0402
R206, R208, R226, R227, R236, R252, R253: DNI; R_0402
R217, R248: 51k; R_0402
R219, R221, R247: 21k; R_0402
R223, R249: 47k; R_0402
R228, R230, R243, R244, R245: 1k; R_0402
R229, R233: 0; R_0402
R235: 7.5k; R_0402
R238: 12k; R_0402
R239: 10; R_0402
R246, R250: 68k; R_0402
R251: 39k; R_0402
TP101: 3V8_WEAK; TP07R
TP102: 3V8; TP07R
TP103: GND; TP07R
TP104: ADDR; TP07R
TP105: ALERT; TP07R
U101: 74HC244; TSSOP-20_4.4x6.5mm_Pitch0.65mm
U102: 74xx1G14; SOT-23-5
U103: LM73; SOT-23-6
U201: LTC2937; QFN-28_EP_6x5_Pitch0.5mm
U202: NCP692; DFN-6-1EP_3x3mm_Pitch0.95mm
U203: ADP7158; DFN-10-1EP_3x3mm_Pitch0.5mm
U204: LM2776; SOT-23-6
U205: LTM4622A; BGA-25_5x5_6.35x6.35mm
U206, U207, U208: TPS22918; SOT-23-6
U209, U210, U211: TPS72301DB; SOT-23-5

Connections:
+3.3VP: C224.2, C225.2, J106.1, R239.2, U201.28
+3V3: C217.2, D201.2, J103.1, L201.1, R233.1, U203.9, U203.10
+3V8: C101.1, C204.2, C218.1, C220.1, J118.1, R101.1, R102.1, R231.2, R232.2, U101.15, U101.20, U102.5, U203.1, U203.2, U205.D1, U205.E1
+5VP: C213.2, C229.1, C230.1, C231.1, J110.1, R229.2, U201.27, U202.4, U206.1, U207.1, U208.1
+6V: C203.2, C205.2, C214.2, C216.2, C219.1, C221.1, J122.1, R228.1, U201.2, U202.1, U202.6, U204.3, U205.A1, U205.B1
+9V: C102.1, C103.1, C208.1, C211.1, D103.2, J114.1, J124.1, J124.3, R216.1, U205.A2, U205.B3, U205.D3, U205.E2
-2V5: C239.1, C242.1, J113.1, R219.1, R248.1, U210.5
-3V3: C240.1, C243.1, J117.1, R221.1, R250.1, U211.5
-5V: C238.1, C241.1, J121.1, R223.1, R246.1, U209.5
/3V8_EN: J124.2, J125.15, J125.16, R225.1, U205.D2
/5V5_EN: J124.4, J125.17, J125.18, R224.1, U205.B2
/ALERTB: J125.5, J125.6, R204.2, U201.15
/FAULTB: J125.11, J125.12, R202.2, U201.16
/HIGHBAND_CONN: J101.1, J101.2, U101.2
/HIGHBAND_EN: R242.1, U101.18, U208.3
/HIGHBAND_VX2: J112.1, R245.2, U208.6
/LED_CONN: J101.7, J101.8, U101.11
/LOWBAND_CONN: J101.5, J101.6, U101.6
/LOWBAND_EN: R240.1, U101.14, U206.3
/LOWBAND_VAMP: J120.1, R243.2, U206.6
/MIDBAND_CONN: J101.3, J101.4, U101.4
/MIDBAND_EN: R241.1, U101.16, U207.3
/MIDBAND_VAMP: J116.1, R244.2, U207.6
/ON: J125.13, J125.14, U201.5
/PGOOD_3V8: J101.11, J101.12, R231.1, U205.D4
/PGOOD_5V5: J101.13, J101.14, R232.1, U205.B4
/PGOOD_ALL: J101.9, J101.10, R215.1, U101.8, U102.2, U201.14
/PGOOD_INV: R102.2, U101.1, U101.19, U102.4
/PGOOD_LED: D102.2, U101.12
/PMIC_3V3: C104.1, C201.1, C202.1, R201.1, R202.1, R203.1, R204.1, R205.1, R207.2, R209.1, R210.2, R211.2, R212.2, R213.2, R214.2, R215.2, R218.1, R220.1, R222.1, U103.3, U201.3
/PMIC_SCL: J125.3, J125.4, R205.2, U103.4, U201.19
/PMIC_SDA: J125.1, J125.2, R209.2, U103.6, U201.18
/RSTB: J125.9, J125.10, R201.2, U201.17
/WP: J125.7, J125.8, R203.2, U201.22
/amp_bias/3V3_EN: R213.1, R230.1, U201.12
/amp_bias/5V_EN: R214.1, U201.13, U202.3
/amp_bias/M2_5V_EN: R211.1, U201.10, U210.3
/amp_bias/M3_5V_EN: R212.1, U201.11, U211.3
/amp_bias/M5V_EN: R210.1, U201.9, U209.3
GND: C101.2, C102.2, C103.2, C104.2, C201.2, C202.2, C203.1, C204.1, C205.1, C206.1, C207.1, C208.2, C209.2, C210.2, C211.2, C213.1, C214.1, C215.1, C216.1, C217.1, C218.2, C219.2, C220.2, C221.2, C222.1, C223.1, C224.1, C225.1, C226.2, C227.2, C228.2, C229.2, C230.2, C231.2, C232.2, C233.2, C234.2, C235.2, C236.2, C237.2, C238.2, C239.2, C240.2, C241.2, C242.2, C243.2, J101.15, J101.16, J101.17, J101.18, J101.19, J101.20, J104.1, J107.1, J111.1, J115.1, J119.1, J123.1, J125.19, J125.20, J126.1, J127.1, R103.2, R104.2, R105.2, R206.2, R208.2, R217.1, R224.2, R225.2, R226.1, R227.1, R235.2, R236.2, R237.1, R238.2, R240.2, R241.2, R242.2, R247.2, R249.2, R251.2, R252.2, R253.2, U101.10, U101.13, U102.3, U103.2, U201.4, U201.29, U202.2, U202.7, U203.11, U204.2, U205.B5, U205.C1, U205.C2, U205.D5, U206.2, U207.2, U208.2, U209.1, U210.1, U211.1
unnamed: C206.2, U203.3
unnamed: C207.2, U203.4, U203.5
unnamed: C209.1, U205.E3
unnamed: C210.1, U205.A3
unnamed: C212.1, U204.6
unnamed: C212.2, U204.5
unnamed: C215.2, U203.7
unnamed: C222.2, C223.2, L202.2, R236.1, U204.1
unnamed: C235.1, U206.4
unnamed: C236.1, U207.4
unnamed: C237.1, U208.4
unnamed: D101.1, R103.1
unnamed: D101.2, U101.9
unnamed: D102.1, R104.1
unnamed: D103.1, R105.1
unnamed: D201.1, R237.2
unnamed: L201.2, R239.1
unnamed: R101.2, U101.17
unnamed: R206.1, U201.1
unnamed: R207.1, U201.21
unnamed: R208.1, U201.7
unnamed: R216.2, R217.2, U201.26
unnamed: R218.2, R219.2, U201.25
unnamed: R220.2, R221.2, U201.24
unnamed: R222.2, R223.2, U201.23
unnamed: R226.2, U205.C5
unnamed: R227.2, U205.C4
unnamed: R228.2, U204.4
unnamed: R229.1, U202.5
unnamed: R230.2, U203.6
unnamed: R233.2, U203.8
unnamed: R235.1, U205.A4
unnamed: R238.1, U205.E4
unnamed: R243.1, U206.5
unnamed: R244.1, U207.5
unnamed: R245.1, U208.5
unnamed: R246.2, R247.1, U209.4
unnamed: R248.2, R249.1, U210.4
unnamed: R250.2, R251.1, U211.4
unnamed: R252.1, U201.6
unnamed: R253.1, U201.8
unnamed: TP101.1, U101.3
unnamed: TP102.1, U101.5
unnamed: TP103.1, U101.7
unnamed: TP104.1, U103.1
unnamed: TP105.1, U103.5
VSS: C226.1, C227.1, C228.1, C232.1, C233.1, C234.1, J109.1, L202.1, U209.2, U210.2, U211.2
