loxodes/vna/breakouts/sw_edge_fr408_oshpark/siw/siw.kicad_pcb

## KiCad design breakouts/sw_edge_fr408_oshpark/siw/siw.kicad_pcb (2019-09-25)

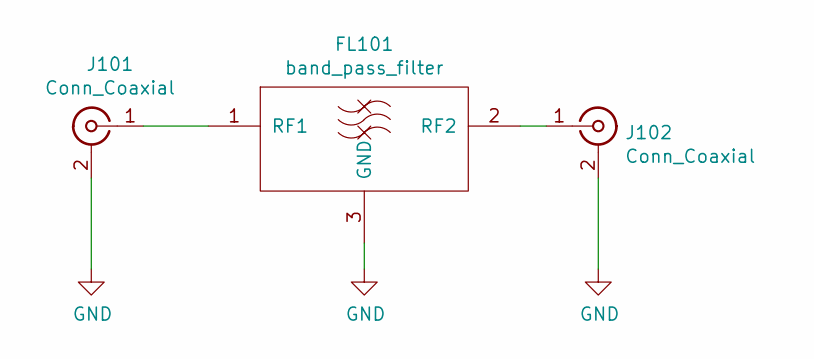
[picture p116: schematic siw.sch]

Parts:
FL101: band_pass_filter; band_x2_siw_fr408_6p7mil
J101, J102: Conn_Coaxial; sw_edge_oshpark_4layer

Connections:
GND: FL101.3 (GND), J101.2 (Ext), J102.2 (Ext)
unnamed: FL101.1 (RF1), J101.1 (In)
unnamed: FL101.2 (RF2), J102.1 (In)

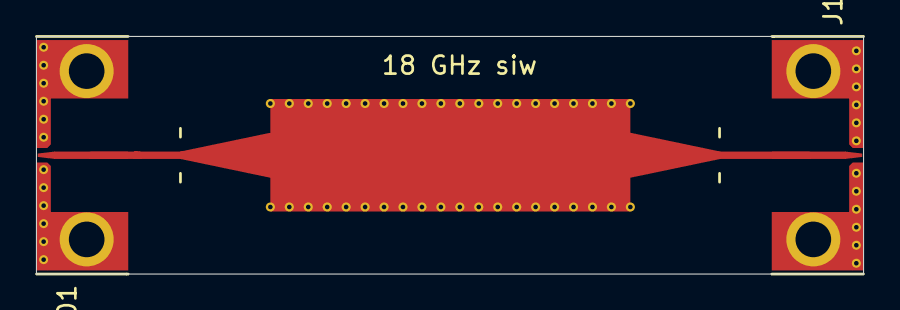
[picture p117: board breakouts/sw_edge_fr408_oshpark/siw/siw.kicad_pcb from above]

Board: 4 copper layers, 45.9 x 13.2 mm, 3 parts (0 on the bottom side), 3 nets.
