loxodes/vna/breakouts/sw_edge_fr408_oshpark/trl_0402_series/siw.kicad_pcb

## KiCad design breakouts/sw_edge_fr408_oshpark/trl_0402_series/siw.kicad_pcb (2019-09-25)

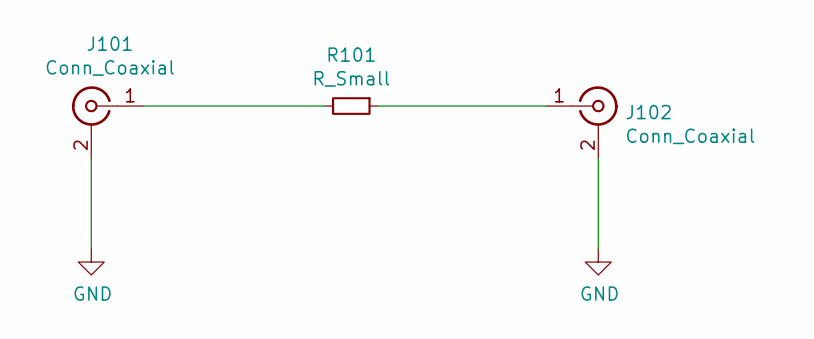
[picture p118: schematic siw.sch]

Parts:
J101, J102: Conn_Coaxial; sw_edge_oshpark_4layer
R101: R_Small; R_0402

Connections:
GND: J101.2 (Ext), J102.2 (Ext)
unnamed: J101.1 (In), R101.2
unnamed: J102.1 (In), R101.1

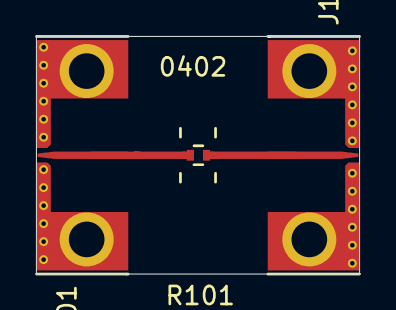
[picture p119: board breakouts/sw_edge_fr408_oshpark/trl_0402_series/siw.kicad_pcb from above]

Board: 4 copper layers, 17.9 x 13.2 mm, 3 parts (0 on the bottom side), 3 nets.
