loxodes/vna/breakouts/sw_edge_fr408_oshpark/trl_att_hmc/siw.kicad_pcb

## KiCad design breakouts/sw_edge_fr408_oshpark/trl_att_hmc/siw.kicad_pcb (2019-09-25)

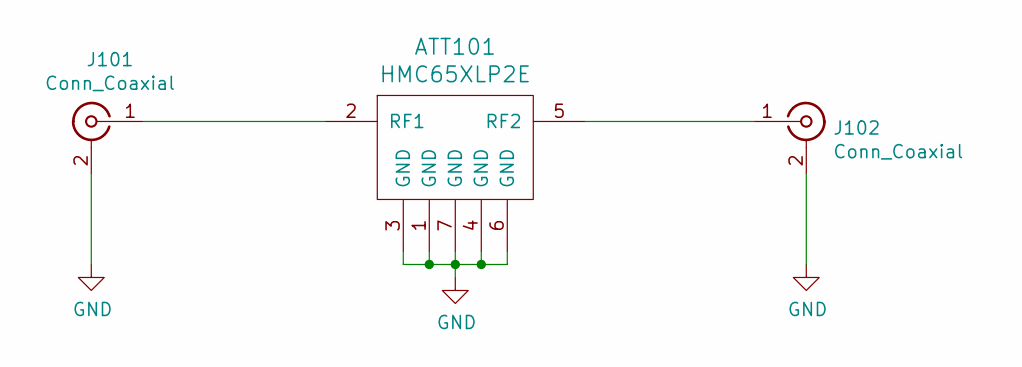
[picture p120: schematic siw.sch]

Parts:
ATT101: HMC65XLP2E; LP2E_DFN6_2x2mm_Pitch0.60mm
J101, J102: Conn_Coaxial; sw_edge_oshpark_4layer

Connections:
GND: ATT101.1 (GND), ATT101.3 (GND), ATT101.4 (GND), ATT101.6 (GND), ATT101.7 (GND), J101.2 (Ext), J102.2 (Ext)
unnamed: ATT101.2 (RF1), J101.1 (In)
unnamed: ATT101.5 (RF2), J102.1 (In)

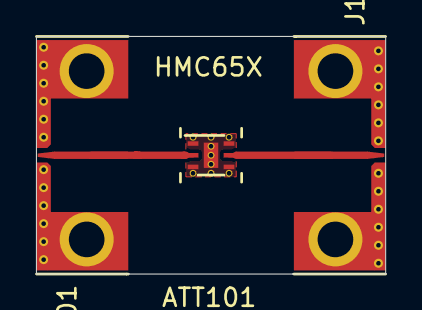
[picture p121: board breakouts/sw_edge_fr408_oshpark/trl_att_hmc/siw.kicad_pcb from above]

Board: 4 copper layers, 19.4 x 13.2 mm, 3 parts (0 on the bottom side), 3 nets.
