loxodes/vna/breakouts/sw_edge_fr408_oshpark/trl_admv/siw.kicad_pcb

## KiCad design breakouts/sw_edge_fr408_oshpark/trl_admv/siw.kicad_pcb (2019-09-25)

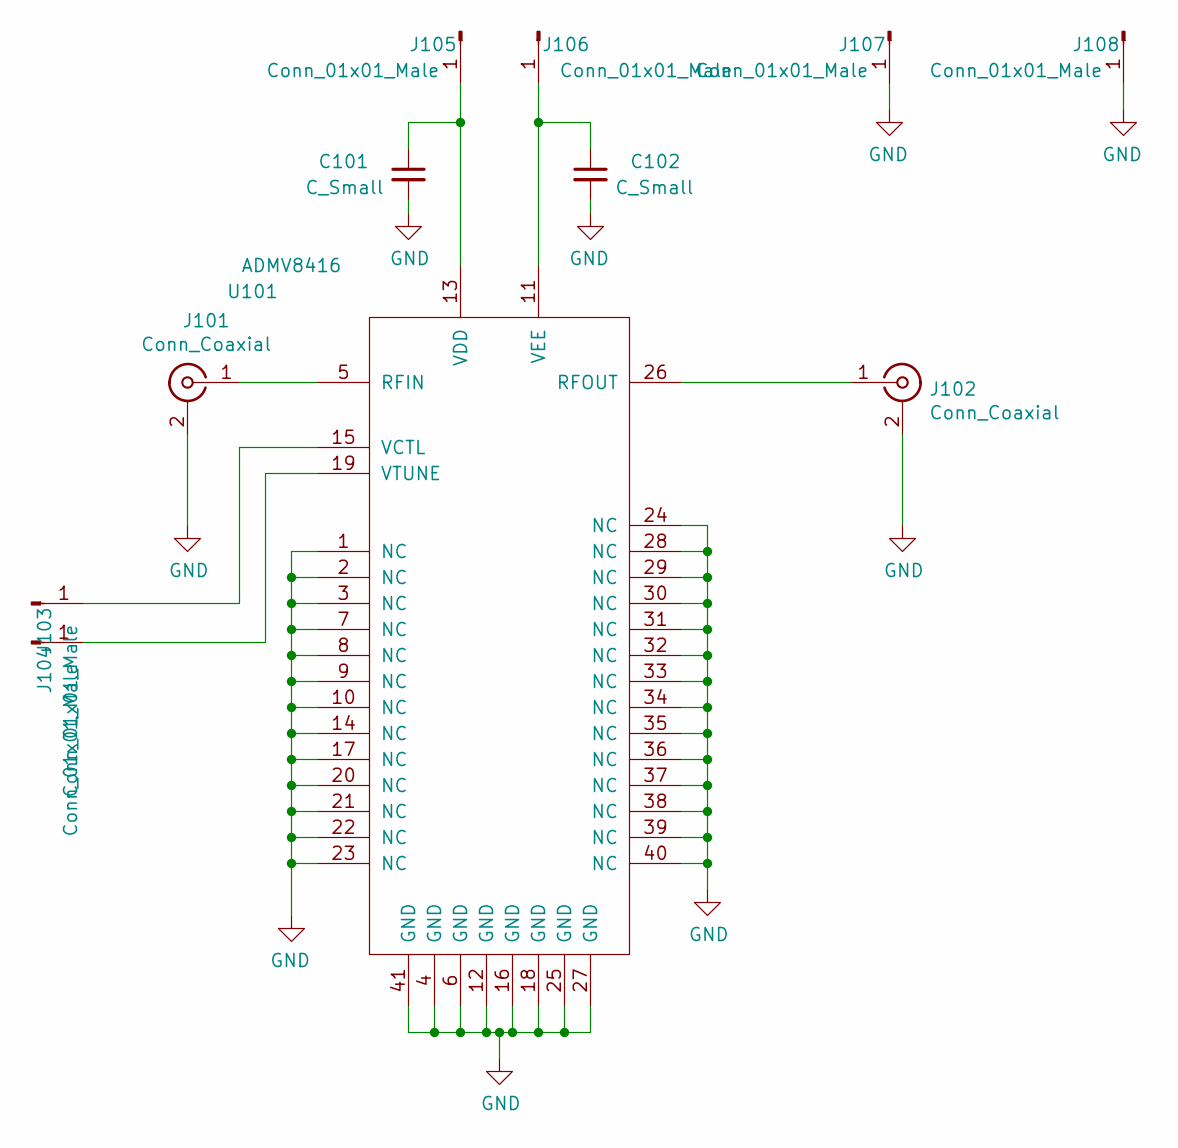
[picture p122: schematic siw.sch]

Parts:
C101, C102: C_Small; C_0402
J101, J102: Conn_Coaxial; sw_edge_oshpark_4layer
J103, J104, J105, J106, J107, J108: Conn_01x01_Male; TURRET_MILLMAX_2101
U101: ADMV8416; QFN-40-1EP_6x6mm_Pitch0.5mm

Connections:
GND: C101.2, C102.2, J101.2 (Ext), J102.2 (Ext), J107.1, J108.1, U101.1 (NC), U101.2 (NC), U101.3 (NC), U101.4 (GND), U101.6 (GND), U101.7 (NC), U101.8 (NC), U101.9 (NC), U101.10 (NC), U101.12 (GND), U101.14 (NC), U101.16 (GND), U101.17 (NC), U101.18 (GND), U101.20 (NC), U101.21 (NC), U101.22 (NC), U101.23 (NC), U101.24 (NC), U101.25 (GND), U101.27 (GND), U101.28 (NC), U101.29 (NC), U101.30 (NC), U101.31 (NC), U101.32 (NC), U101.33 (NC), U101.34 (NC), U101.35 (NC), U101.36 (NC), U101.37 (NC), U101.38 (NC), U101.39 (NC), U101.40 (NC), U101.41 (GND)
unnamed: C101.1, J105.1, U101.13 (VDD)
unnamed: C102.1, J106.1, U101.11 (VEE)
unnamed: J101.1 (In), U101.5 (RFIN)
unnamed: J102.1 (In), U101.26 (RFOUT)
unnamed: J103.1, U101.15 (VCTL)
unnamed: J104.1, U101.19 (VTUNE)

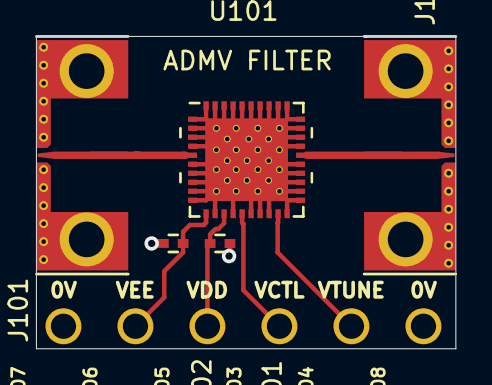
[picture p123: board breakouts/sw_edge_fr408_oshpark/trl_admv/siw.kicad_pcb from above]

Board: 4 copper layers, 23.3 x 17.3 mm, 11 parts (0 on the bottom side), 7 nets.
