loxodes/vna/breakouts/sw_edge_fr408_oshpark/trl_vatt/siw.kicad_pcb

## KiCad design breakouts/sw_edge_fr408_oshpark/trl_vatt/siw.kicad_pcb (2019-09-25)

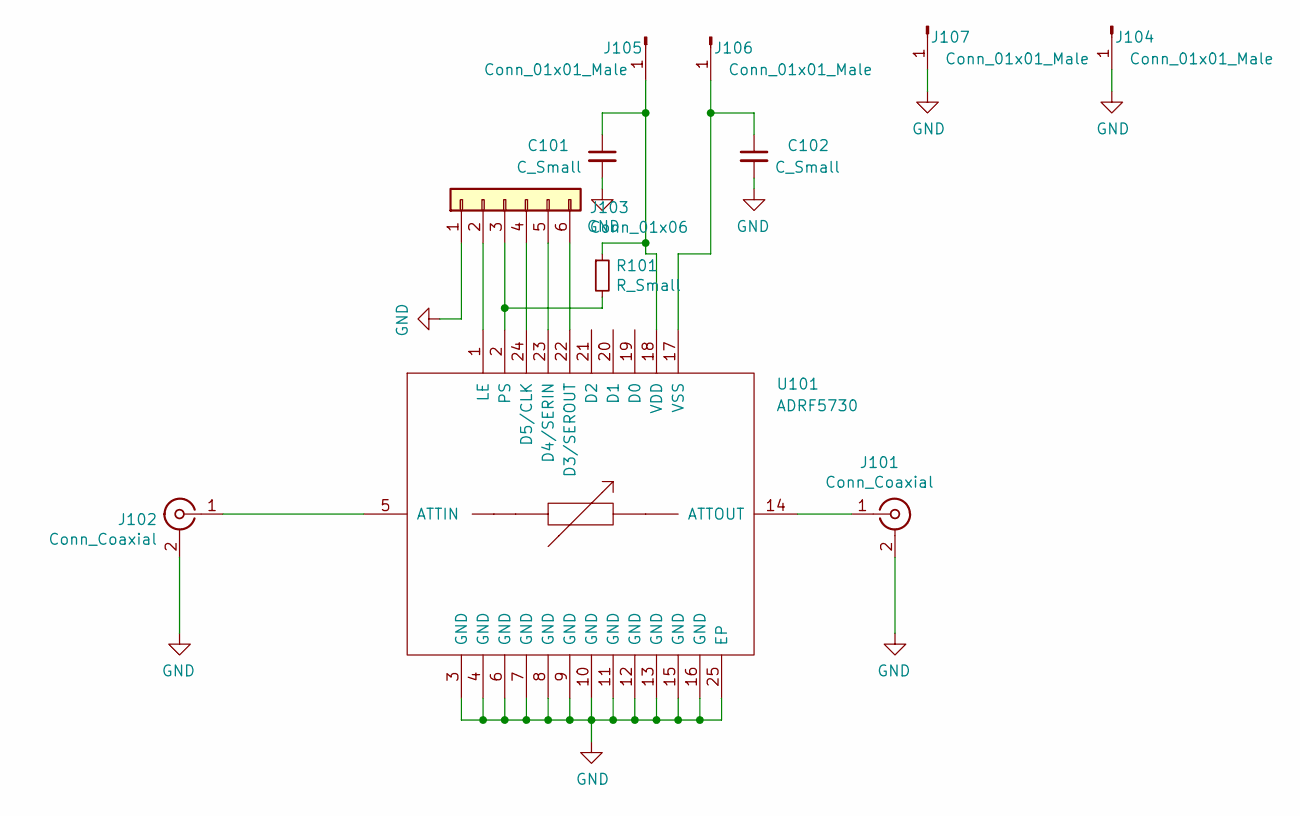
[picture p124: schematic siw.sch]

Parts:
C101, C102: C_Small; C_0402
J101, J102: Conn_Coaxial; sw_edge_oshpark_4layer
J103: Conn_01x06; Pin_Header_Straight_1x06
J104, J105, J106, J107: Conn_01x01_Male; TURRET_MILLMAX_2101
R101: R_Small; R_0402
U101: ADRF5730; QFN-24-1EP_4x4mm_Pitch0.5mm

Connections:
GND: C101.2, C102.2, J101.2 (Ext), J102.2 (Ext), J103.1, J104.1, J107.1, U101.3 (GND), U101.4 (GND), U101.6 (GND), U101.7 (GND), U101.8 (GND), U101.9 (GND), U101.10 (GND), U101.11 (GND), U101.12 (GND), U101.13 (GND), U101.15 (GND), U101.16 (GND), U101.25 (EP)
unnamed: C101.1, J105.1, R101.1, U101.18 (VDD)
unnamed: C102.1, J106.1, U101.17 (VSS)
unnamed: J101.1 (In), U101.14 (ATTOUT)
unnamed: J102.1 (In), U101.5 (ATTIN)
unnamed: J103.2, U101.1 (LE)
unnamed: J103.3, R101.2, U101.2 (PS)
unnamed: J103.4, U101.24 (D5/CLK)
unnamed: J103.5, U101.23 (D4/SERIN)
unnamed: J103.6, U101.22 (D3/SEROUT)

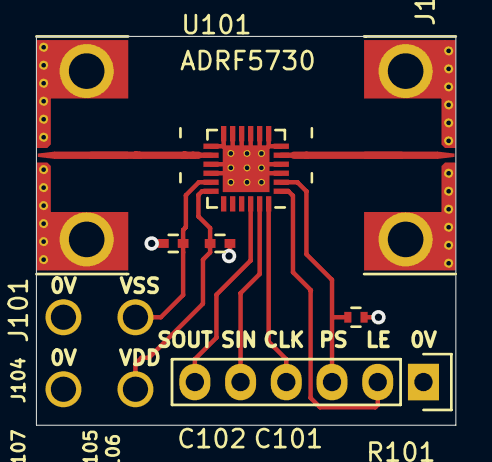
[picture p125: board breakouts/sw_edge_fr408_oshpark/trl_vatt/siw.kicad_pcb from above]

Board: 4 copper layers, 23.3 x 21.6 mm, 11 parts (0 on the bottom side), 10 nets.
