loxodes/vna/breakouts/pe42543_breakout/pe42543_breakout.kicad_pcb

## KiCad design breakouts/pe42543_breakout/pe42543_breakout.kicad_pcb (2019-09-08)

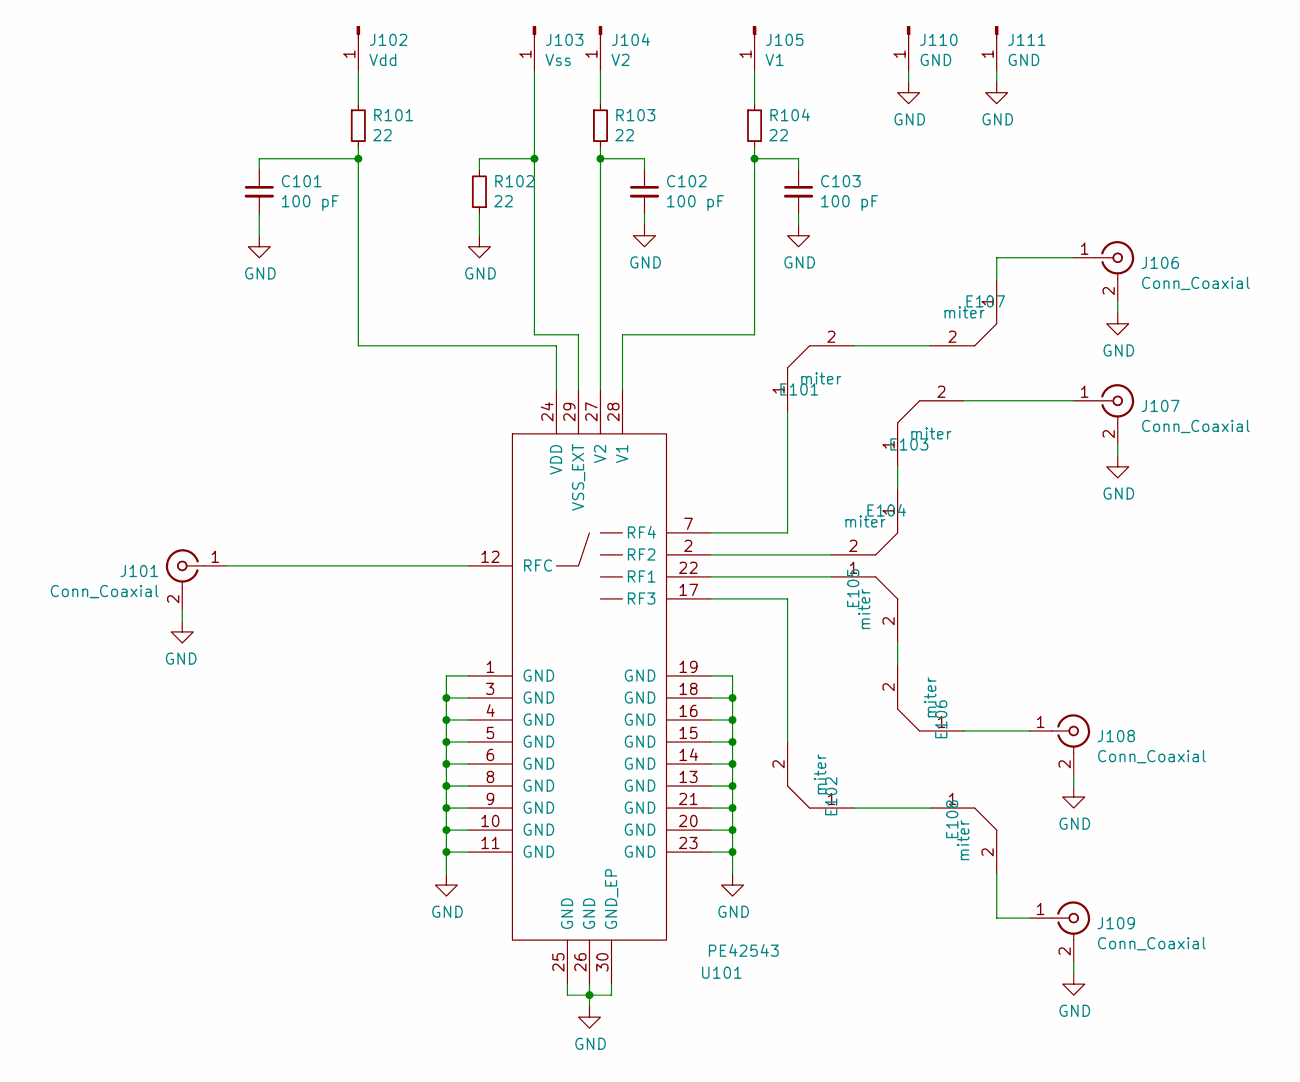
[picture p126: schematic pe42543_breakout.sch]

Parts:
C101, C102, C103: 100 pF; C_0402
E101, E102, E103, E104, E105, E106, E107, E108: miter; p41mm_miter
J101, J106, J107, J108, J109: Conn_Coaxial; sw_edge_oshpark_4layer
J102: Vdd; TURRET_MILLMAX_2101
J103: Vss; TURRET_MILLMAX_2101
J104: V2; TURRET_MILLMAX_2101
J105: V1; TURRET_MILLMAX_2101
J110, J111: GND; TURRET_MILLMAX_2101
R101, R102, R103, R104: 22; R_0402
U101: PE42543; RFSW__PE42543A-X

Connections:
GND: C101.2, C102.2, C103.2, J101.2 (Ext), J106.2 (Ext), J107.2 (Ext), J108.2 (Ext), J109.2 (Ext), J110.1, J111.1, R102.1, U101.1 (GND), U101.3 (GND), U101.4 (GND), U101.5 (GND), U101.6 (GND), U101.8 (GND), U101.9 (GND), U101.10 (GND), U101.11 (GND), U101.13 (GND), U101.14 (GND), U101.15 (GND), U101.16 (GND), U101.18 (GND), U101.19 (GND), U101.20 (GND), U101.21 (GND), U101.23 (GND), U101.25 (GND), U101.26 (GND), U101.30 (GND_EP)
unnamed: C101.1, R101.2, U101.24 (VDD)
unnamed: C102.1, R103.2, U101.27 (V2)
unnamed: C103.1, R104.2, U101.28 (V1)
unnamed: E101.1, U101.7 (RF4)
unnamed: E101.2, E107.2
unnamed: E102.1, E108.1
unnamed: E102.2, U101.17 (RF3)
unnamed: E103.1, E104.1
unnamed: E103.2, J107.1 (In)
unnamed: E104.2, U101.2 (RF2)
unnamed: E105.1, U101.22 (RF1)
unnamed: E105.2, E106.2
unnamed: E106.1, J108.1 (In)
unnamed: E107.1, J106.1 (In)
unnamed: E108.2, J109.1 (In)
unnamed: J101.1 (In), U101.12 (RFC)
unnamed: J102.1, R101.1
unnamed: J103.1, R102.2, U101.29 (VSS_EXT)
unnamed: J104.1, R103.1
unnamed: J105.1, R104.1

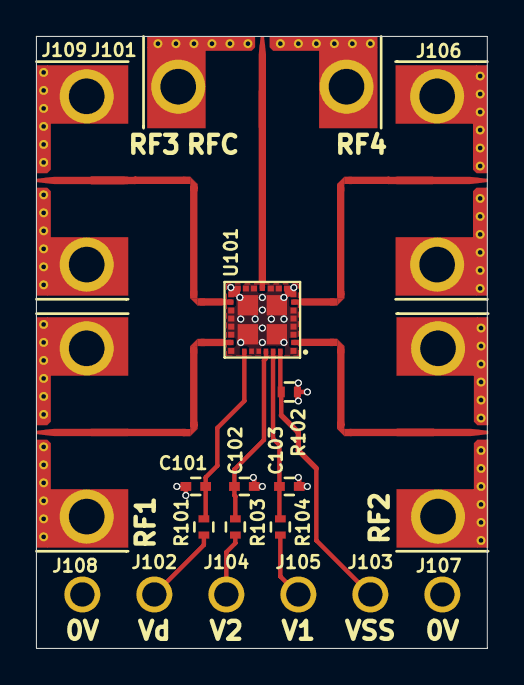
[picture p127: board pe42543_breakout.kicad_pcb from above]

Board: 4 copper layers, 25.1 x 34.0 mm, 27 parts (0 on the bottom side), 21 nets.
