loxodes/vna/breakouts/maam_011109/maam_011109/maam_011109.kicad_pcb

## KiCad design breakouts/maam_011109/maam_011109/maam_011109.kicad_pcb (2019-08-04)

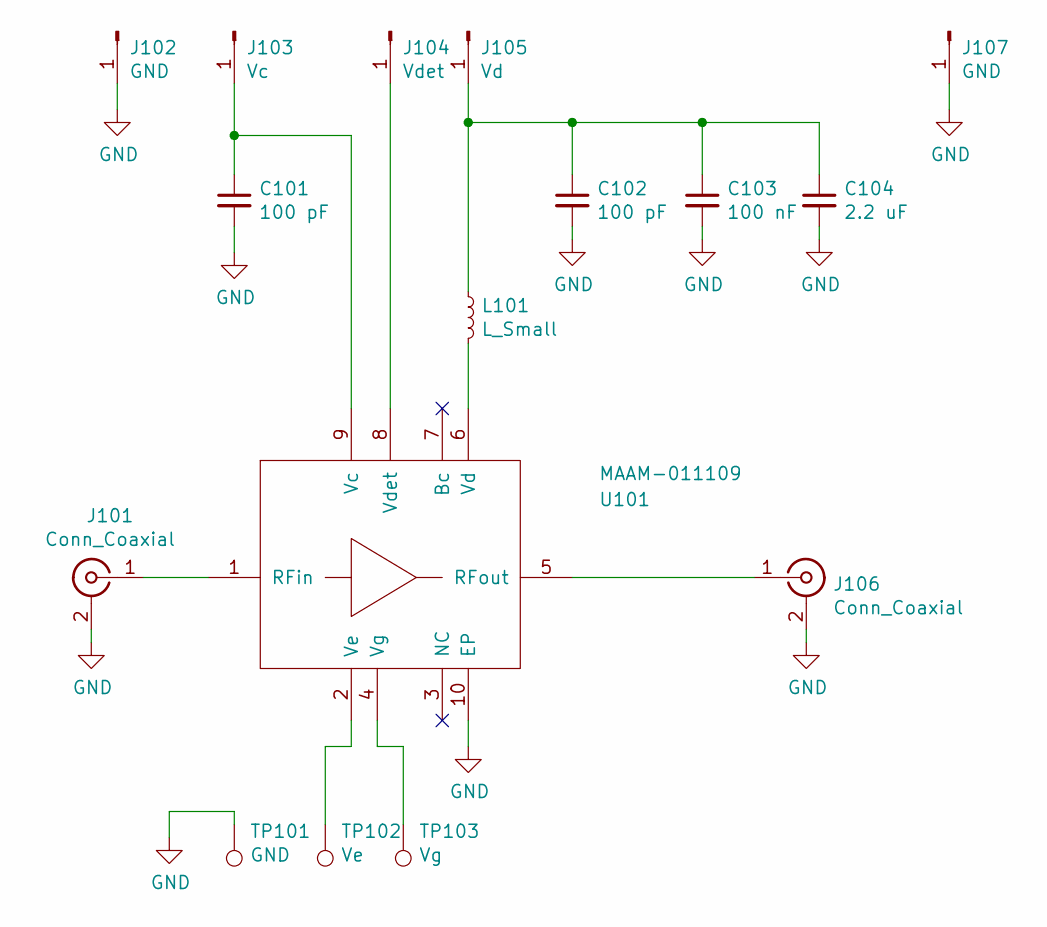
[picture p128: schematic maam_011109.sch]

Parts:
C101, C102: 100 pF; C_0402
C103: 100 nF; C_0402
C104: 2.2 uF; C_0603
J101, J106: Conn_Coaxial; sw_edge_oshpark_4layer
J102, J107: GND; TURRET_MILLMAX_2101
J103: Vc; TURRET_MILLMAX_2101
J104: Vdet; TURRET_MILLMAX_2101
J105: Vd; TURRET_MILLMAX_2101
L101: L_Small; C_0402
TP101: GND; TP07R
TP102: Ve; TP07R
TP103: Vg; TP07R
U101: MAAM-011109; MACOM_LGA9

Connections:
GND: C101.2, C102.2, C103.2, C104.2, J101.2 (Ext), J102.1, J106.2 (Ext), J107.1, TP101.1, U101.10 (EP)
unnamed: C101.1, J103.1, U101.9 (Vc)
unnamed: C102.1, C103.1, C104.1, J105.1, L101.1
unnamed: J101.1 (In), U101.1 (RFin)
unnamed: J104.1, U101.8 (Vdet)
unnamed: J106.1 (In), U101.5 (RFout)
unnamed: L101.2, U101.6 (Vd)
unnamed: TP102.1, U101.2 (Ve)
unnamed: TP103.1, U101.4 (Vg)

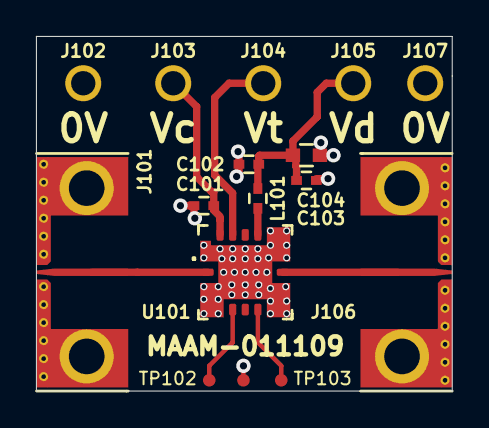
[picture p129: board maam_011109.kicad_pcb from above]

Board: 4 copper layers, 23.1 x 19.7 mm, 16 parts (0 on the bottom side), 9 nets.
