loxodes/vna/breakouts/res_splitter/trl_thru.kicad_pcb

## KiCad design breakouts/res_splitter/trl_thru.kicad_pcb (2019-06-30)

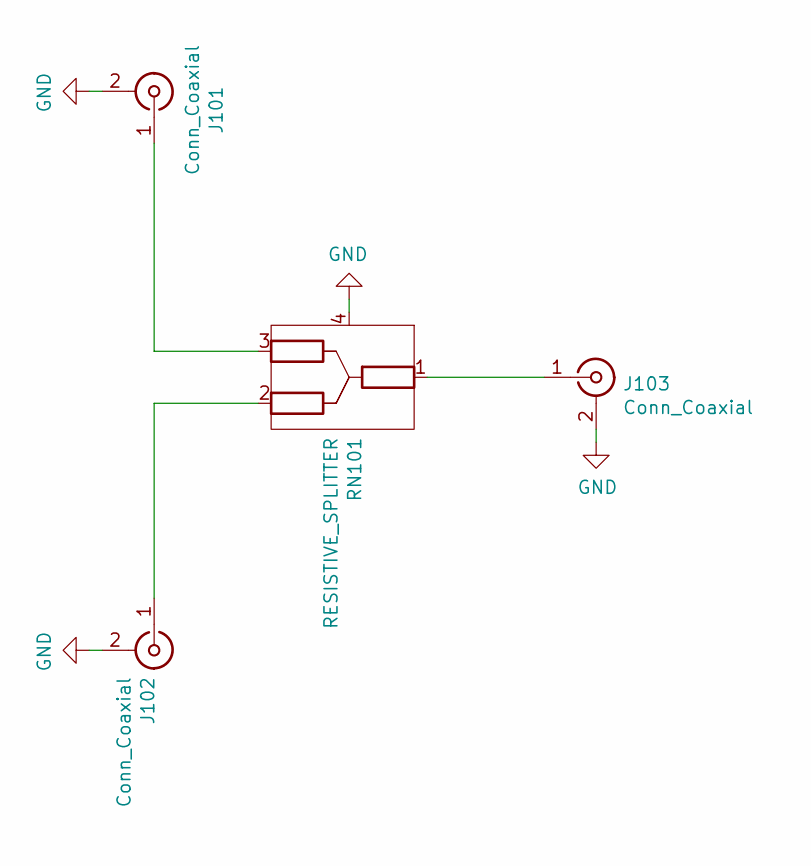
[picture p130: schematic trl_thru.sch]

Parts:
J101, J102, J103: Conn_Coaxial; sw_edge_oshpark_4layer
RN101: RESISTIVE_SPLITTER; PDR06380

Connections:
GND: J101.2 (Ext), J102.2 (Ext), J103.2 (Ext), RN101.4
unnamed: J101.1 (In), RN101.3
unnamed: J102.1 (In), RN101.2
unnamed: J103.1 (In), RN101.1

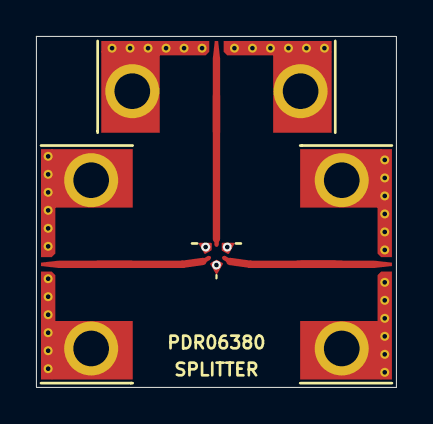
[picture p131: board breakouts/res_splitter/trl_thru.kicad_pcb from above]

Board: 4 copper layers, 20.0 x 19.5 mm, 4 parts (0 on the bottom side), 4 nets.
