loxodes/vna/breakouts/hmc576_breakout/trl_thru.kicad_pcb

## KiCad design breakouts/hmc576_breakout/trl_thru.kicad_pcb (2019-06-30)

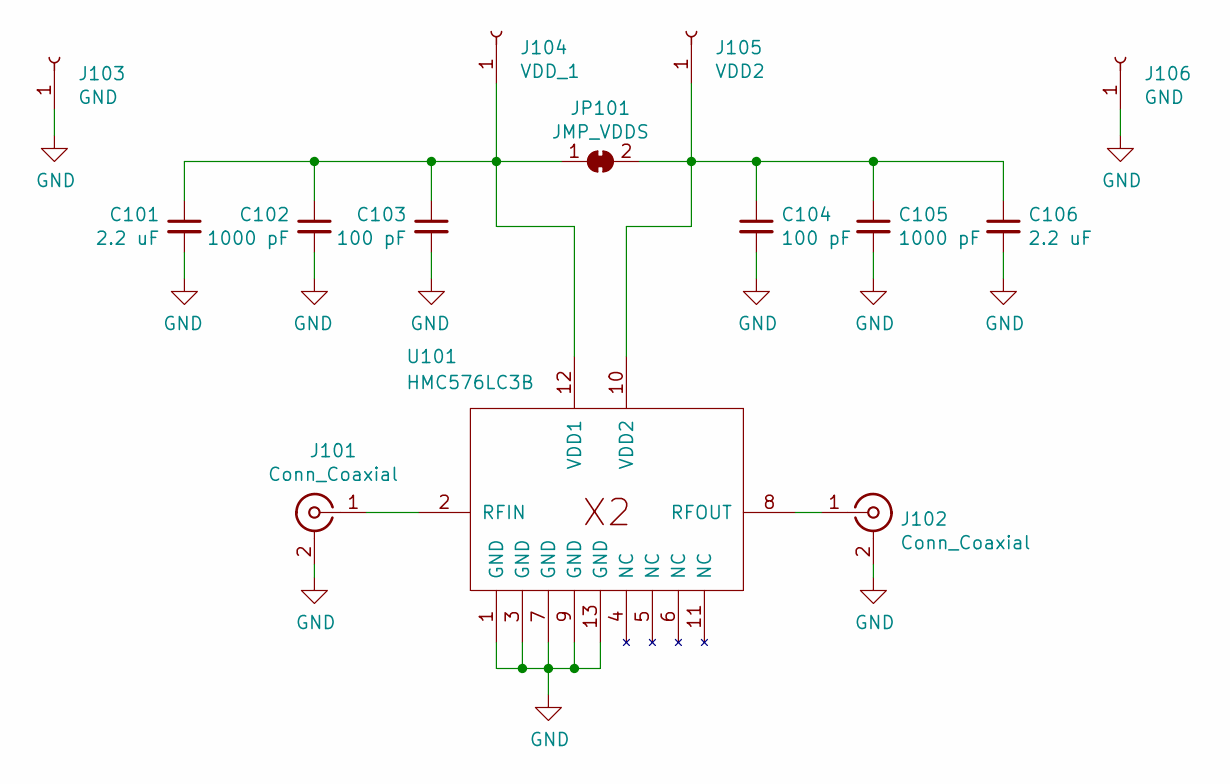
[picture p132: schematic trl_thru.sch]

Parts:
C101, C106: 2.2 uF; C_0805
C102, C105: 1000 pF; C_0402
C103, C104: 100 pF; C_0402
J101, J102: Conn_Coaxial; sw_edge_oshpark_4layer
J103, J106: GND; TURRET_MILLMAX_2101
J104: VDD_1; TURRET_MILLMAX_2101
J105: VDD2; TURRET_MILLMAX_2101
JP101: JMP_VDDS; R_0402
U101: HMC576LC3B; LC3B

Connections:
GND: C101.2, C102.2, C103.2, C104.2, C105.2, C106.2, J101.2 (Ext), J102.2 (Ext), J103.1, J106.1, U101.1 (GND), U101.3 (GND), U101.7 (GND), U101.9 (GND), U101.13 (GND)
unnamed: C101.1, C102.1, C103.1, J104.1, JP101.1 (A), U101.12 (VDD1)
unnamed: C104.1, C105.1, C106.1, J105.1, JP101.2 (B), U101.10 (VDD2)
unnamed: J101.1 (In), U101.2 (RFIN)
unnamed: J102.1 (In), U101.8 (RFOUT)

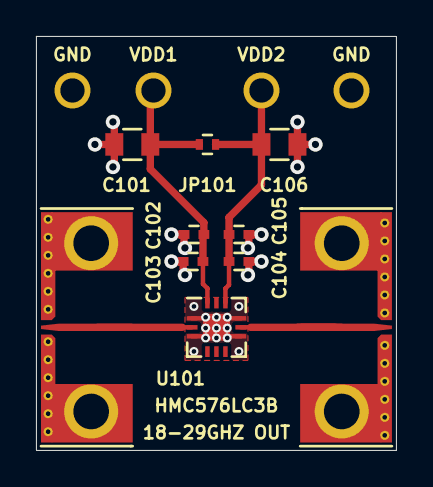
[picture p133: board breakouts/hmc576_breakout/trl_thru.kicad_pcb from above]

Board: 4 copper layers, 20.0 x 23.0 mm, 14 parts (0 on the bottom side), 5 nets.
