loxodes/vna/hardware/oshpark_4layer_trl_cal/cap_0201/trl_line.sch

## KiCad design hardware/oshpark_4layer_trl_cal/cap_0201/trl_line.sch (2018-04-02)

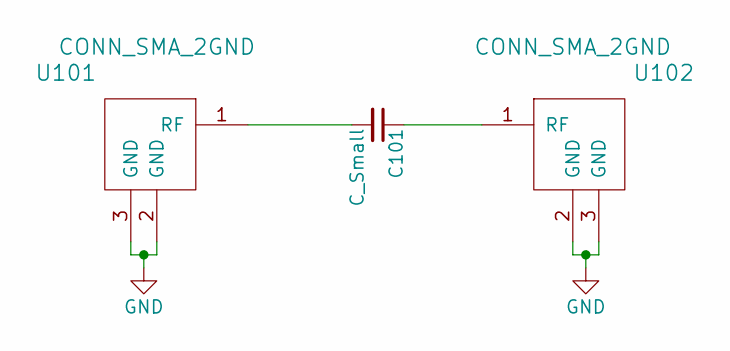
[picture p134: schematic trl_line.sch]

Parts:
C101: C_Small; C_0201
U101, U102: CONN_SMA_2GND; SMA_901-10512_6p7MIL_FR408_CPW_LAUNCH

Connections:
GND: U101.2 (GND), U101.3 (GND), U102.2 (GND), U102.3 (GND)
unnamed: C101.1, U102.1 (RF)
unnamed: C101.2, U101.1 (RF)
