loxodes/vna/hardware/oshpark_4layer_trl_cal/shunt_0402/trl_line.sch

## KiCad design hardware/oshpark_4layer_trl_cal/shunt_0402/trl_line.sch (2018-04-02)

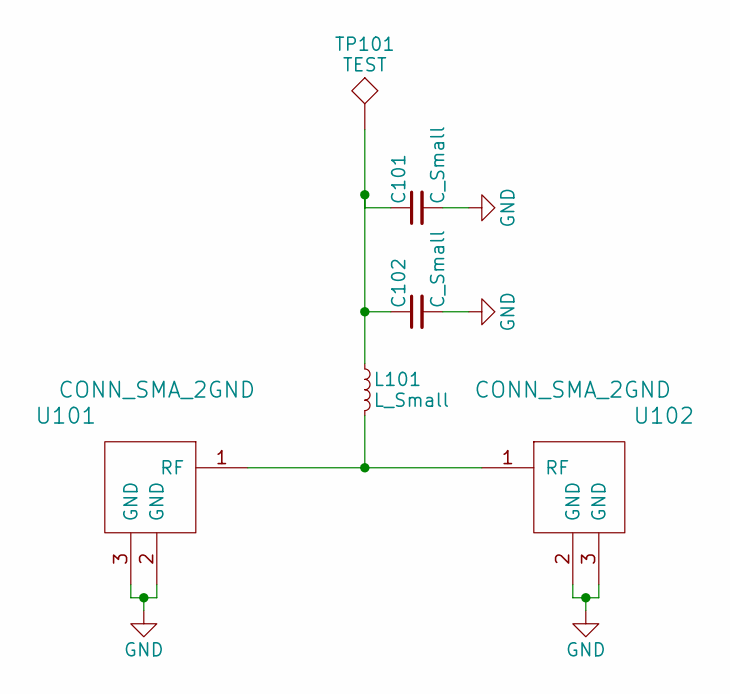
[picture p135: schematic trl_line.sch]

Parts:
C101, C102: C_Small; C_0402
L101: L_Small; R_0402
TP101: TEST; TP07R
U101, U102: CONN_SMA_2GND; SMA_901-10512_6p7MIL_FR408_CPW_LAUNCH

Connections:
GND: C101.2, C102.2, U101.2 (GND), U101.3 (GND), U102.2 (GND), U102.3 (GND)
unnamed: C101.1, C102.1, L101.1, TP101.1
unnamed: L101.2, U101.1 (RF), U102.1 (RF)
