loxodes/vna/hardware/vna_r0/vna_control/clock_gen.sch

## KiCad design hardware/vna_r0/vna_control/clock_gen.sch (2017-08-02)

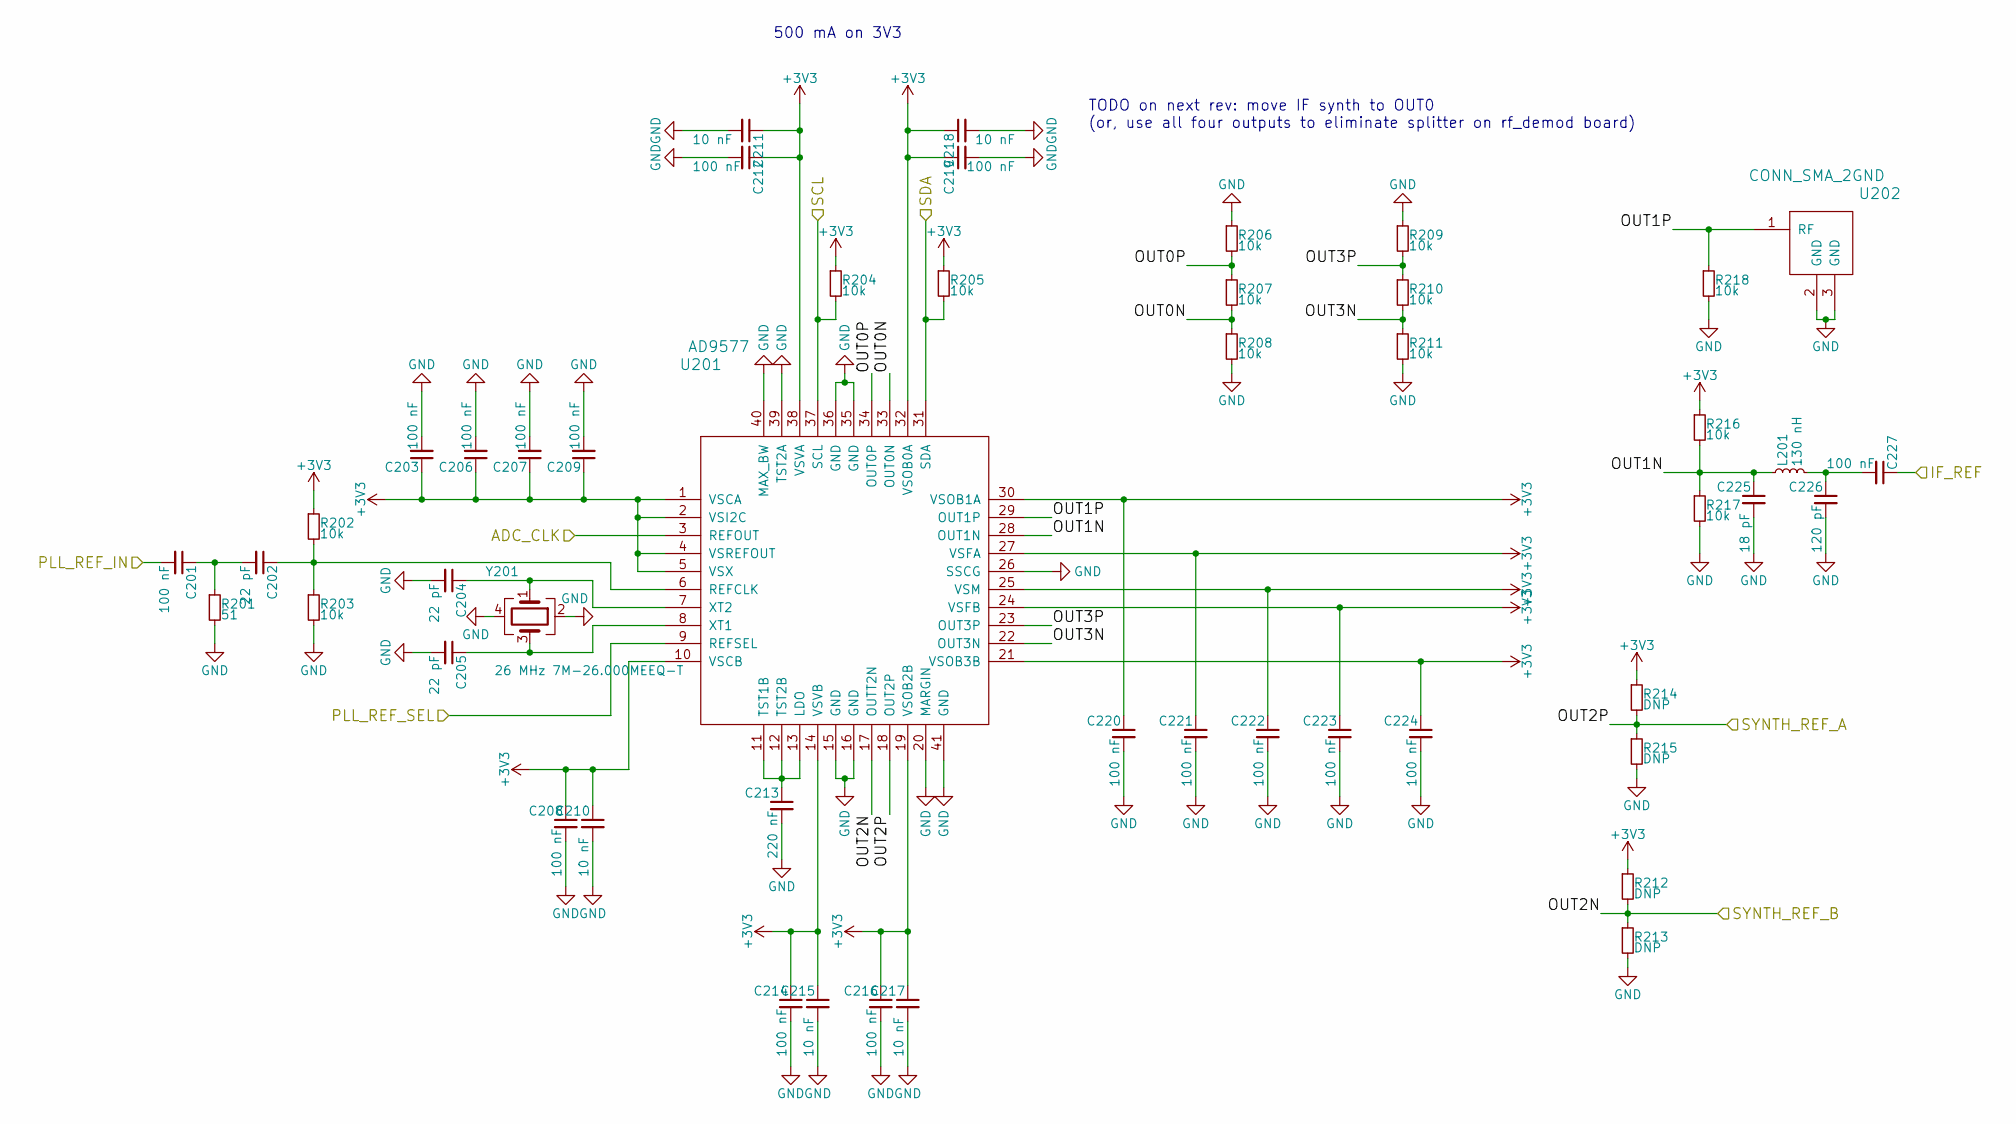
[picture p136: schematic clock_gen.sch]

Parts:
C201, C203, C206, C207, C208, C209, C212, C214, C216, C219, C220, C221, C222, C223, C224, C227: 100 nF; C_0402
C202, C204, C205: 22 pF; C_0402
C210, C211, C215, C217, C218: 10 nF; C_0402
C213: 220 nF; C_0402
C225: 18 pF; C_0402
C226: 120 pF; C_0402
L201: 130 nH; R_0805
R201: 51; R_0402
R202, R203, R204, R205, R206, R207, R208, R209, R210, R211, R216, R217, R218: 10k; R_0402
R212, R213, R214, R215: DNP; R_0402
U201: AD9577; QFN-40-1EP_6x6mm_Pitch0.5mm
U202: CONN_SMA_2GND; 734120110_ufl_umc
Y201: 26 MHz 7M-26.000MEEQ-T; crystal_FA238-TSX3225

Connections:
+3V3: C203.1, C206.1, C207.1, C208.1, C209.1, C210.1, C211.1, C212.1, C214.1, C215.1, C216.1, C217.1, C218.1, C219.1, C220.1, C221.1, C222.1, C223.1, C224.1, R202.1, R204.1, R205.1, R212.1, R214.1, R216.1, U201.1 (VSCA), U201.2 (VSI2C), U201.4 (VSREFOUT), U201.5 (VSX), U201.10 (VSCB), U201.14 (VSVB), U201.19 (VSOB2B), U201.21 (VSOB3B), U201.24 (VSFB), U201.25 (VSM), U201.27 (VSFA), U201.30 (VSOB1A), U201.32 (VSOB0A), U201.38 (VSVA)
ADC_CLK: U201.3 (REFOUT)
GND: C203.2, C204.2, C205.2, C206.2, C207.2, C208.2, C209.2, C210.2, C211.2, C212.2, C213.2, C214.2, C215.2, C216.2, C217.2, C218.2, C219.2, C220.2, C221.2, C222.2, C223.2, C224.2, C225.2, C226.2, R201.2, R203.2, R206.1, R208.2, R209.1, R211.2, R213.2, R215.2, R217.2, R218.2, U201.15 (GND), U201.16 (GND), U201.20 (MARGIN), U201.26 (SSCG), U201.35 (GND), U201.36 (GND), U201.39 (TST2A), U201.40 (MAX_BW), U201.41 (GND), U202.2 (GND), U202.3 (GND), Y201.2, Y201.4
IF_REF: C227.1
unnamed: C201.1, C202.2, R201.1
unnamed: C202.1, R202.2, R203.1, U201.6 (REFCLK)
unnamed: C204.1, U201.7 (XT2), Y201.1
unnamed: C205.1, U201.8 (XT1), Y201.3
unnamed: C213.1, U201.11 (TST1B), U201.12 (TST2B), U201.13 (LDO)
unnamed: C226.1, C227.2, L201.2
OUT0N: R207.2, R208.1, U201.33 (OUT0N)
OUT0P: R206.2, R207.1, U201.34 (OUT0P)
OUT1N: C225.1, L201.1, R216.2, R217.1, U201.28 (OUT1N)
OUT1P: R218.1, U201.29 (OUT1P), U202.1 (RF)
OUT2N: R212.2, R213.1, U201.17 (OUTT2N)
OUT2P: R214.2, R215.1, U201.18 (OUT2P)
OUT3N: R210.2, R211.1, U201.22 (OUT3N)
OUT3P: R209.2, R210.1, U201.23 (OUT3P)
PLL_REF_IN: C201.2
PLL_REF_SEL: U201.9 (REFSEL)
SCL: R204.2, U201.37 (SCL)
SDA: R205.2, U201.31 (SDA)

Notes on the sheet:
500 mA on 3V3
TODO on next rev: move IF synth to OUT0 (or, use all four outputs to eliminate splitter on rf_demod board)
