loxodes/vna/hardware/vna_r0/vna_control/connectors.sch

## KiCad design hardware/vna_r0/vna_control/connectors.sch (2017-09-25)

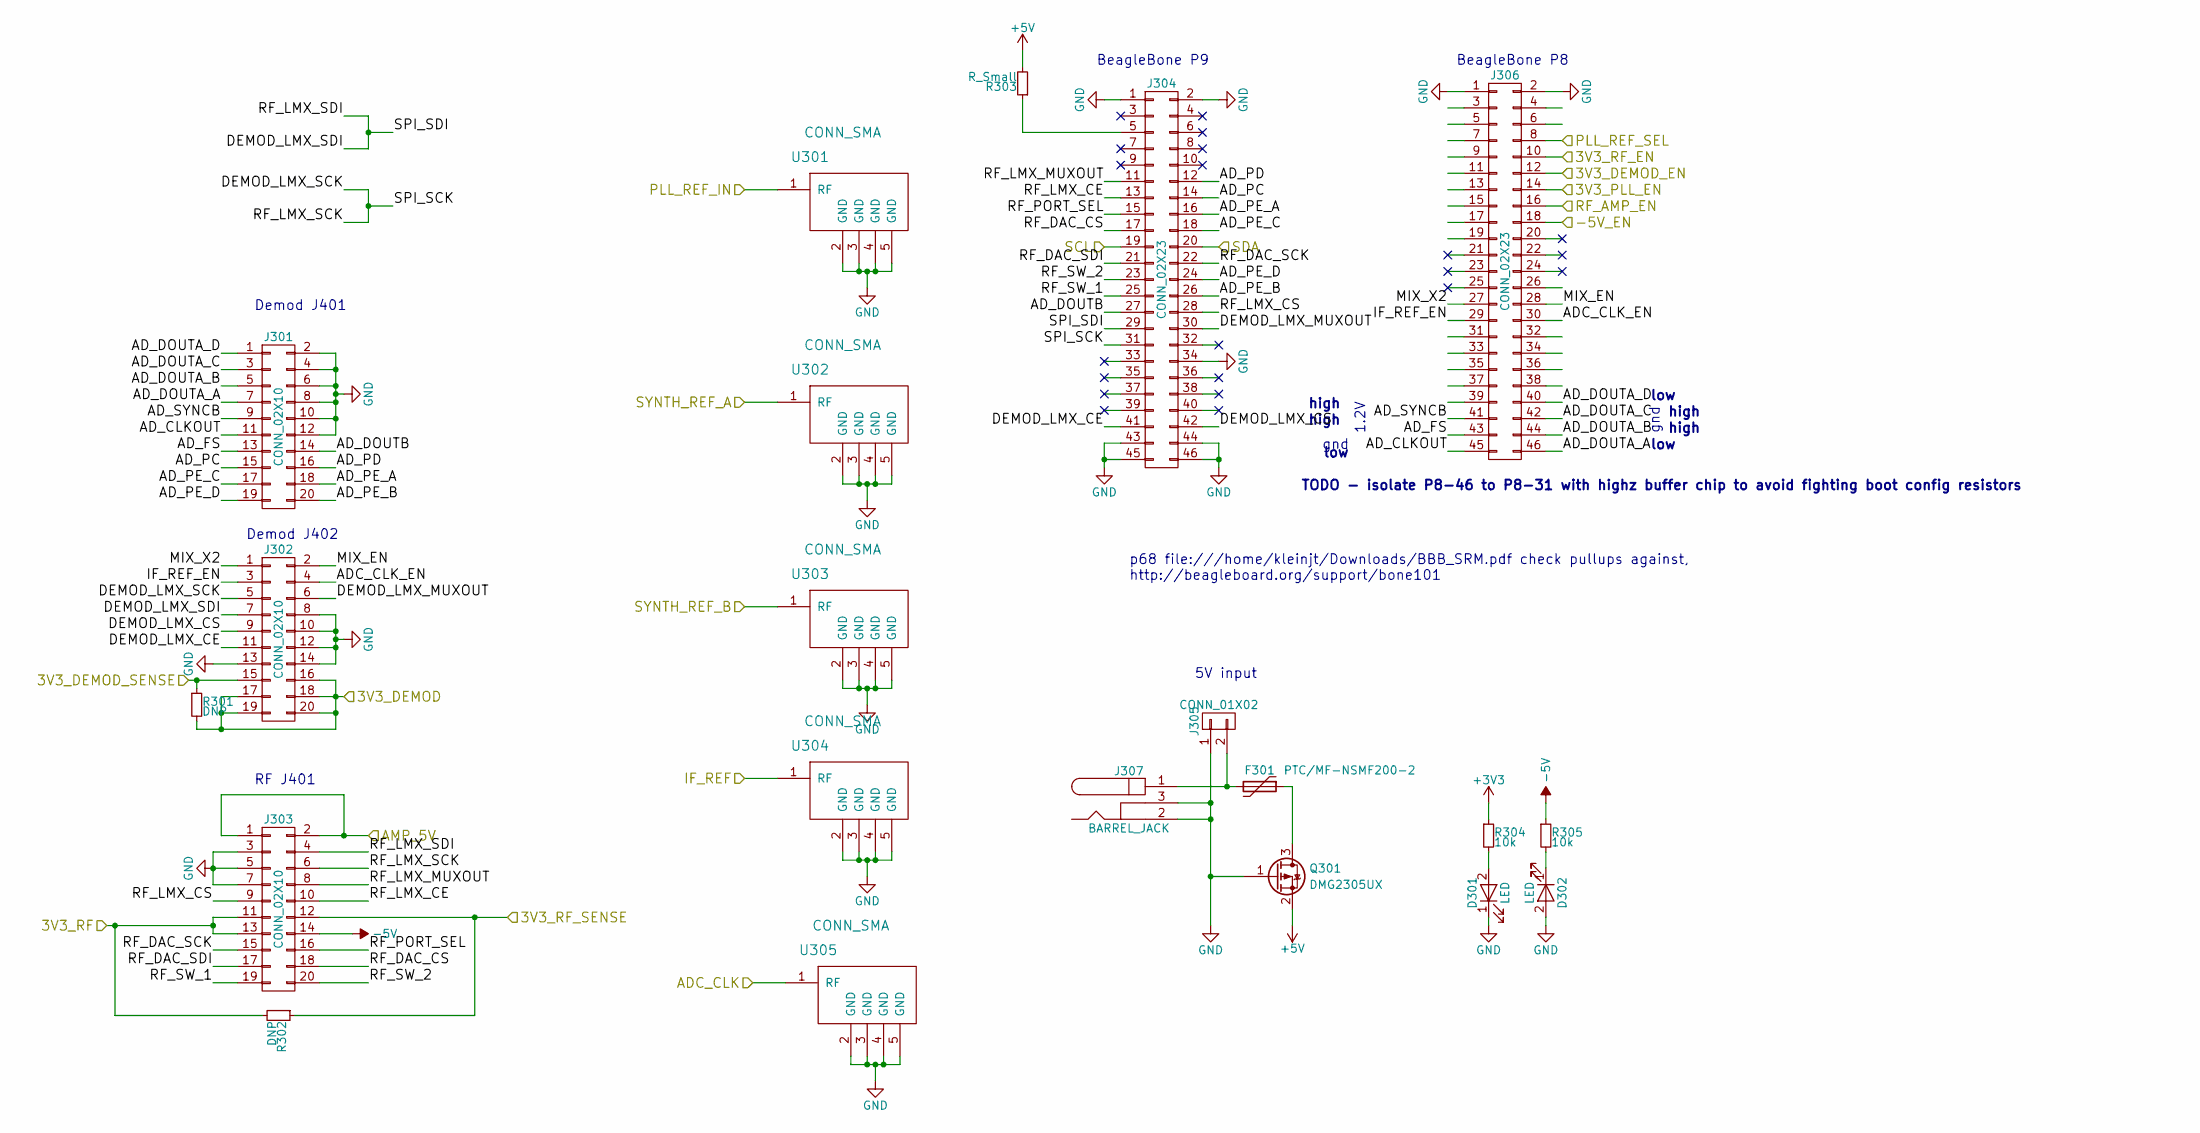
[picture p137: schematic connectors.sch]

Parts:
D301, D302: LED; LED_0603
F301: PTC/MF-NSMF200-2; R_1206
J301, J302, J303: CONN_02X10; IDC_Header_Straight_20pins
J304, J306: CONN_02X23; Pin_Header_Straight_2x23
J305: CONN_01X02; TerminalBlock_Pheonix_PT-3.5mm_2pol
J307: BARREL_JACK
Q301: DMG2305UX; SOT-23
R301, R302: DNP; R_0402
R303: R_Small; R_0402
R304, R305: 10k; R_0402
U301, U302, U303, U304, U305: CONN_SMA; 732511150_sma_thin

Connections:
3V3_DEMOD: J302.16, J302.17, J302.18, J302.19, J302.20, R301.2
3V3_DEMOD_EN: J306.12
3V3_DEMOD_SENSE: J302.15, R301.1
3V3_PLL_EN: J306.14
3V3_RF: J303.11, J303.13, R302.2
3V3_RF_EN: J306.10
3V3_RF_SENSE: J303.12, R302.1
+3V3: R304.1
+5V: Q301.2 (S), R303.2
-5V: J303.14, R305.1
-5V_EN: J306.18
ADC_CLK: U305.1 (RF)
ADC_CLK_EN: J302.4, J306.30
AD_CLKOUT: J301.11, J306.45
AD_DOUTA_A: J301.7, J306.46
AD_DOUTA_B: J301.5, J306.44
AD_DOUTA_C: J301.3, J306.42
AD_DOUTA_D: J301.1, J306.40
AD_DOUTB: J301.14, J304.27
AD_FS: J301.13, J306.43
AD_PC: J301.15, J304.14
AD_PD: J301.16, J304.12
AD_PE_A: J301.18, J304.16
AD_PE_B: J301.20, J304.26
AD_PE_C: J301.17, J304.18
AD_PE_D: J301.19, J304.24
AD_SYNCB: J301.9, J306.41
AMP_5V: J303.1, J303.2
DEMOD_LMX_CE: J302.11, J304.41
DEMOD_LMX_CS: J302.9, J304.42
DEMOD_LMX_MUXOUT: J302.6, J304.30
DEMOD_LMX_SCK: J302.5, J303.6, J304.31
DEMOD_LMX_SDI: J302.7, J303.4, J304.29
GND: D301.1 (K), D302.2 (A), J301.2, J301.4, J301.6, J301.8, J301.10, J301.12, J302.8, J302.10, J302.12, J302.13, J302.14, J303.3, J303.5, J303.7, J304.1, J304.2, J304.34, J304.43, J304.44, J304.45, J304.46, J305.1, J306.1, J306.2, J307.2, J307.3, Q301.1 (G), U301.2 (GND), U301.3 (GND), U301.4 (GND), U301.5 (GND), U302.2 (GND), U302.3 (GND), U302.4 (GND), U302.5 (GND), U303.2 (GND), U303.3 (GND), U303.4 (GND), U303.5 (GND), U304.2 (GND), U304.3 (GND), U304.4 (GND), U304.5 (GND), U305.2 (GND), U305.3 (GND), U305.4 (GND), U305.5 (GND)
IF_REF: U304.1 (RF)
IF_REF_EN: J302.3, J306.29
MIX_EN: J302.2, J306.28
MIX_X2: J302.1, J306.27
unnamed: D301.2 (A), R304.2
unnamed: D302.1 (K), R305.2
unnamed: F301.1, Q301.3 (D)
unnamed: F301.2, J305.2, J307.1
unnamed: J304.5, R303.1
PLL_REF_IN: U301.1 (RF)
PLL_REF_SEL: J306.8
RF_AMP_EN: J306.16
RF_DAC_CS: J303.18, J304.17
RF_DAC_SCK: J303.15, J304.22
RF_DAC_SDI: J303.17, J304.21
RF_LMX_CE: J303.10, J304.13
RF_LMX_CS: J303.9, J304.28
RF_LMX_MUXOUT: J303.8, J304.11
RF_PORT_SEL: J303.16, J304.15
RF_SW_1: J303.19, J304.25
RF_SW_2: J303.20, J304.23
SCL: J304.19
SDA: J304.20
SYNTH_REF_A: U302.1 (RF)
SYNTH_REF_B: U303.1 (RF)

Notes on the sheet:
BeagleBone P9
BeagleBone P8
Demod J401
RF J401
Demod J402
5V input
p68 file:///home/kleinjt/Downloads/BBB_SRM.pdf check pullups against, http://beagleboard.org/support/bone101
gnd
1.2V
low
high
TODO - isolate P8-46 to P8-31 with highz buffer chip to avoid fighting boot config resistors
