loxodes/vna/hardware/vna_r0/vna_control/power.sch

## KiCad design hardware/vna_r0/vna_control/power.sch (2017-08-02)

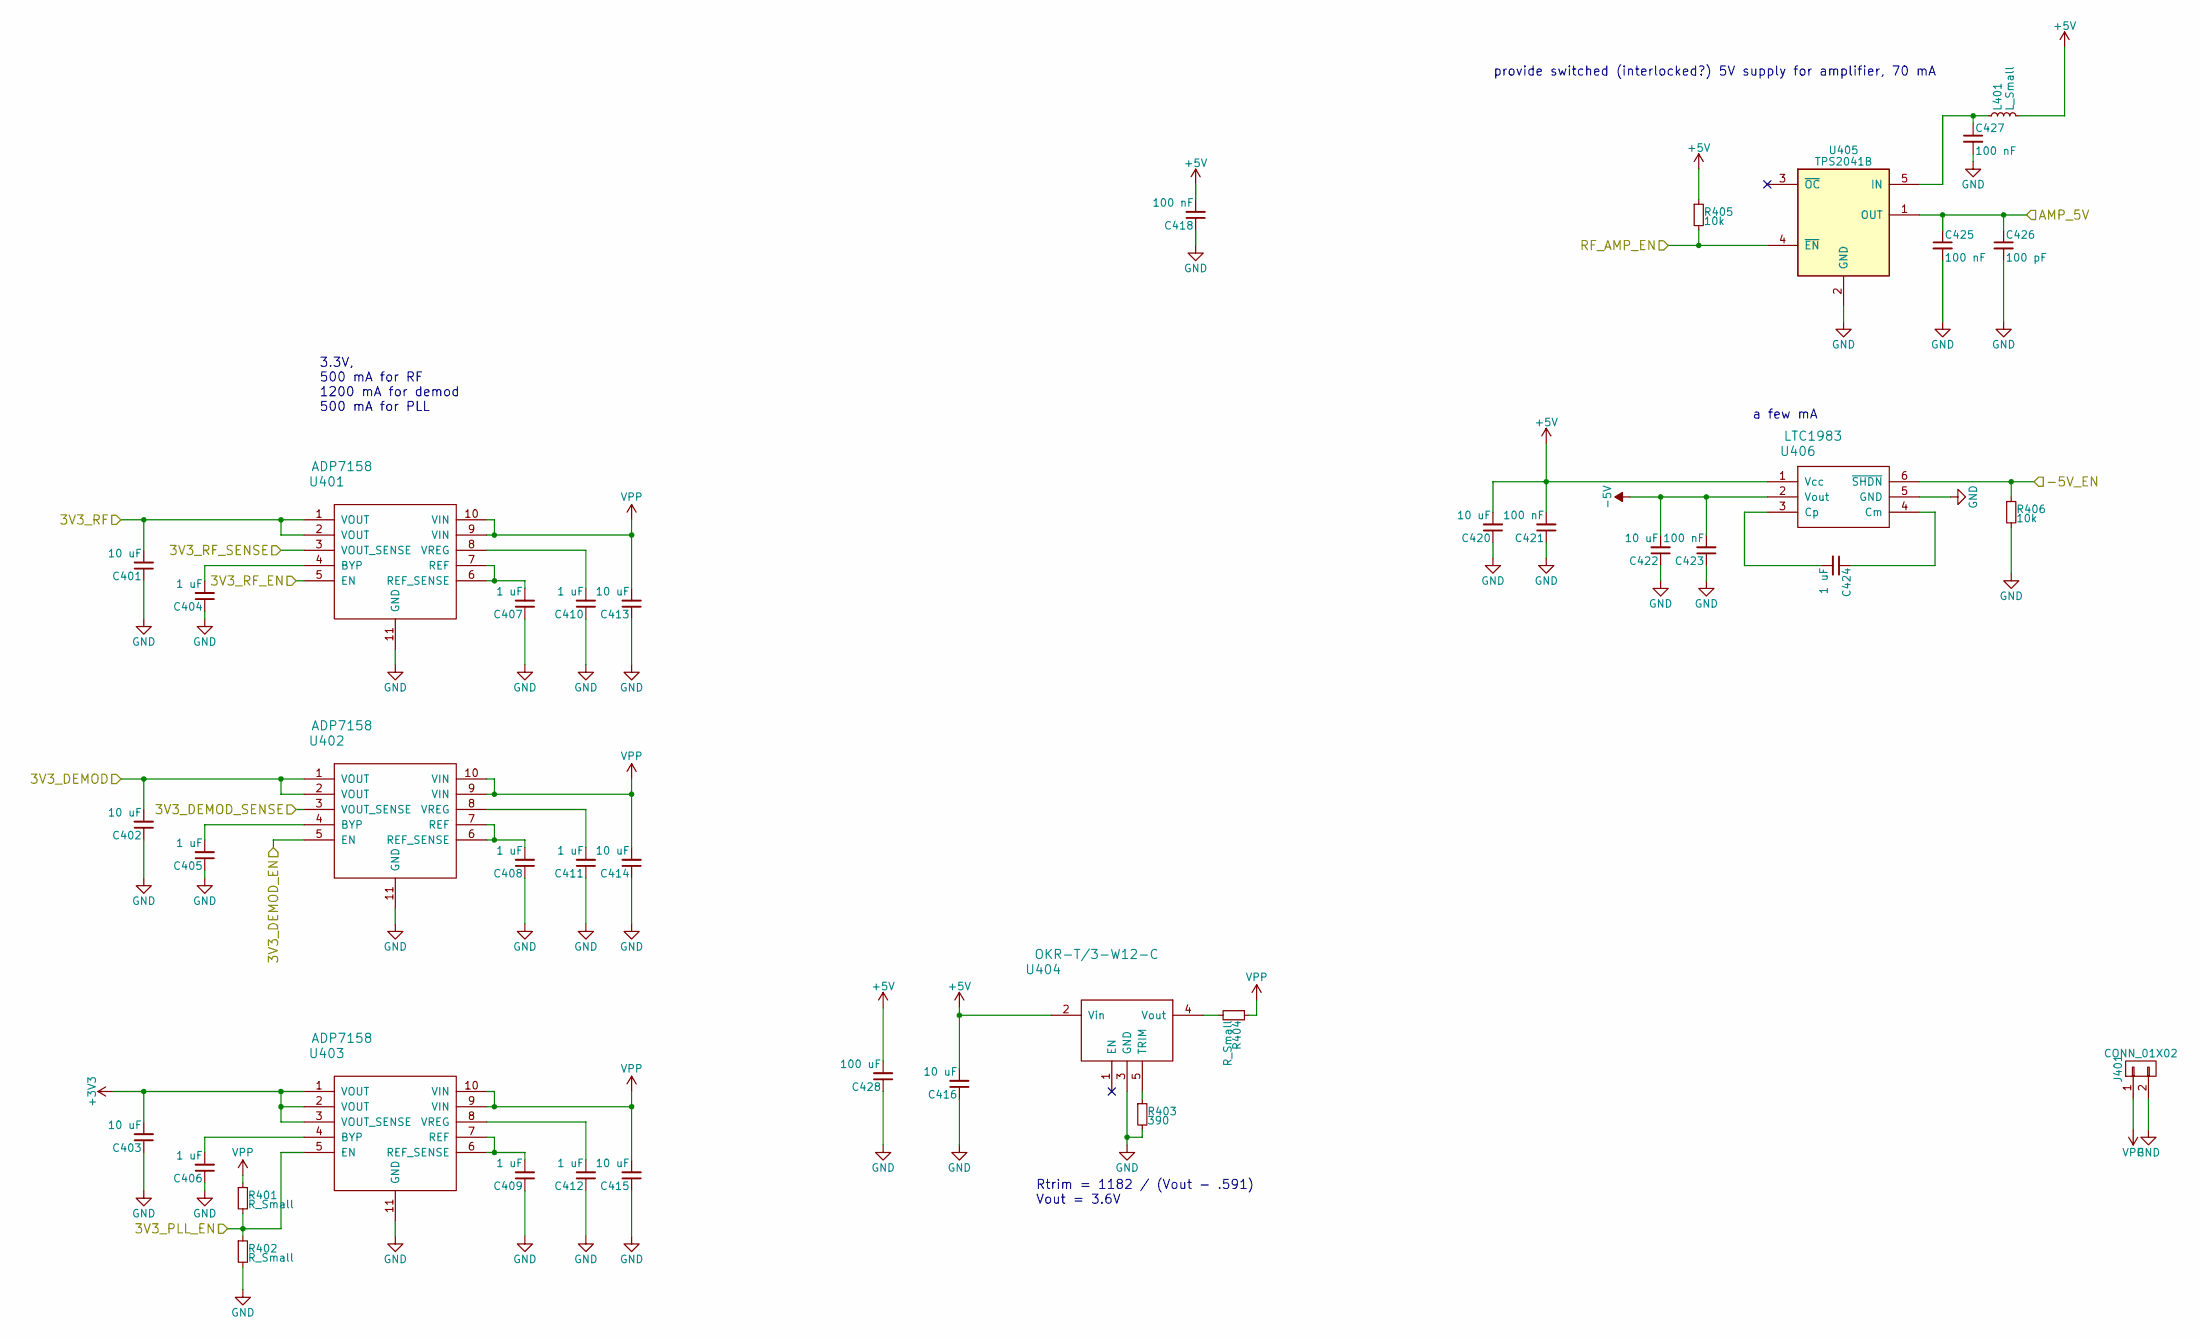
[picture p138: schematic power.sch]

Parts:
C401, C402, C403, C413, C414, C415, C416, C420, C422: 10 uF; C_0603
C404, C405, C406, C407, C408, C409, C410, C411, C412, C424: 1 uF; C_0402
C418, C421, C423, C425, C427: 100 nF; C_0402
C426: 100 pF; C_0402
C428: 100 uF; c_elec_10x10
J401: CONN_01X02; TerminalBlock_Pheonix_PT-3.5mm_2pol
L401: L_Small; R_0805
R401, R402: R_Small; R_0402
R403: 390; R_0402
R404: R_Small; R_1206
R405, R406: 10k; R_0402
U401, U402, U403: ADP7158; DFN-10-1EP_3x3mm_Pitch0.5mm
U404: OKR-T/3-W12-C; OKRT3_C72
U405: TPS2041B; SOT-23-5
U406: LTC1983; SOT-23-6

Connections:
3V3_DEMOD: C402.2, U402.1 (VOUT), U402.2 (VOUT)
3V3_DEMOD_EN: U402.5 (EN)
3V3_DEMOD_SENSE: U402.3 (VOUT_SENSE)
3V3_PLL_EN: R401.2, R402.1, U403.5 (EN)
3V3_RF: C401.2, U401.1 (VOUT), U401.2 (VOUT)
3V3_RF_EN: U401.5 (EN)
3V3_RF_SENSE: U401.3 (VOUT_SENSE)
+3V3: C403.2, U403.1 (VOUT), U403.2 (VOUT), U403.3 (VOUT_SENSE)
+5V: C416.2, C418.2, C420.2, C421.2, C428.2, L401.2, R405.1, U404.2 (Vin), U406.1 (Vcc)
-5V: C422.2, C423.2, U406.2 (Vout)
-5V_EN: R406.1, U406.6 (~SHDN)
AMP_5V: C425.1, C426.1, U405.1 (OUT)
GND: C401.1, C402.1, C403.1, C404.1, C405.1, C406.1, C407.1, C408.1, C409.1, C410.1, C411.1, C412.1, C413.1, C414.1, C415.1, C416.1, C418.1, C420.1, C421.1, C422.1, C423.1, C425.2, C426.2, C427.2, C428.1, J401.2, R402.2, R403.2, R406.2, U401.11 (GND), U402.11 (GND), U403.11 (GND), U404.3 (GND), U405.2 (GND), U406.5 (GND)
unnamed: C404.2, U401.4 (BYP)
unnamed: C405.2, U402.4 (BYP)
unnamed: C406.2, U403.4 (BYP)
unnamed: C407.2, U401.6 (REF_SENSE), U401.7 (REF)
unnamed: C408.2, U402.6 (REF_SENSE), U402.7 (REF)
unnamed: C409.2, U403.6 (REF_SENSE), U403.7 (REF)
unnamed: C410.2, U401.8 (VREG)
unnamed: C411.2, U402.8 (VREG)
unnamed: C412.2, U403.8 (VREG)
unnamed: C424.1, U406.4 (Cm)
unnamed: C424.2, U406.3 (Cp)
unnamed: C427.1, L401.1, U405.5 (IN)
unnamed: R403.1, U404.5 (TRIM)
unnamed: R404.2, U404.4 (Vout)
RF_AMP_EN: R405.2, U405.4 (~EN)
VPP: C413.2, C414.2, C415.2, J401.1, R401.1, R404.1, U401.9 (VIN), U401.10 (VIN), U402.9 (VIN), U402.10 (VIN), U403.9 (VIN), U403.10 (VIN)

Notes on the sheet:
provide switched (interlocked?) 5V supply for amplifier, 70 mA
a few mA
3.3V, 500 mA for RF 1200 mA for demod 500 mA for PLL
Rtrim = 1182 / (Vout - .591) Vout = 3.6V
