loxodes/vna/hardware/vna_r0/vna_demod/clock_distro.sch

## KiCad design hardware/vna_r0/vna_demod/clock_distro.sch (2017-07-08)

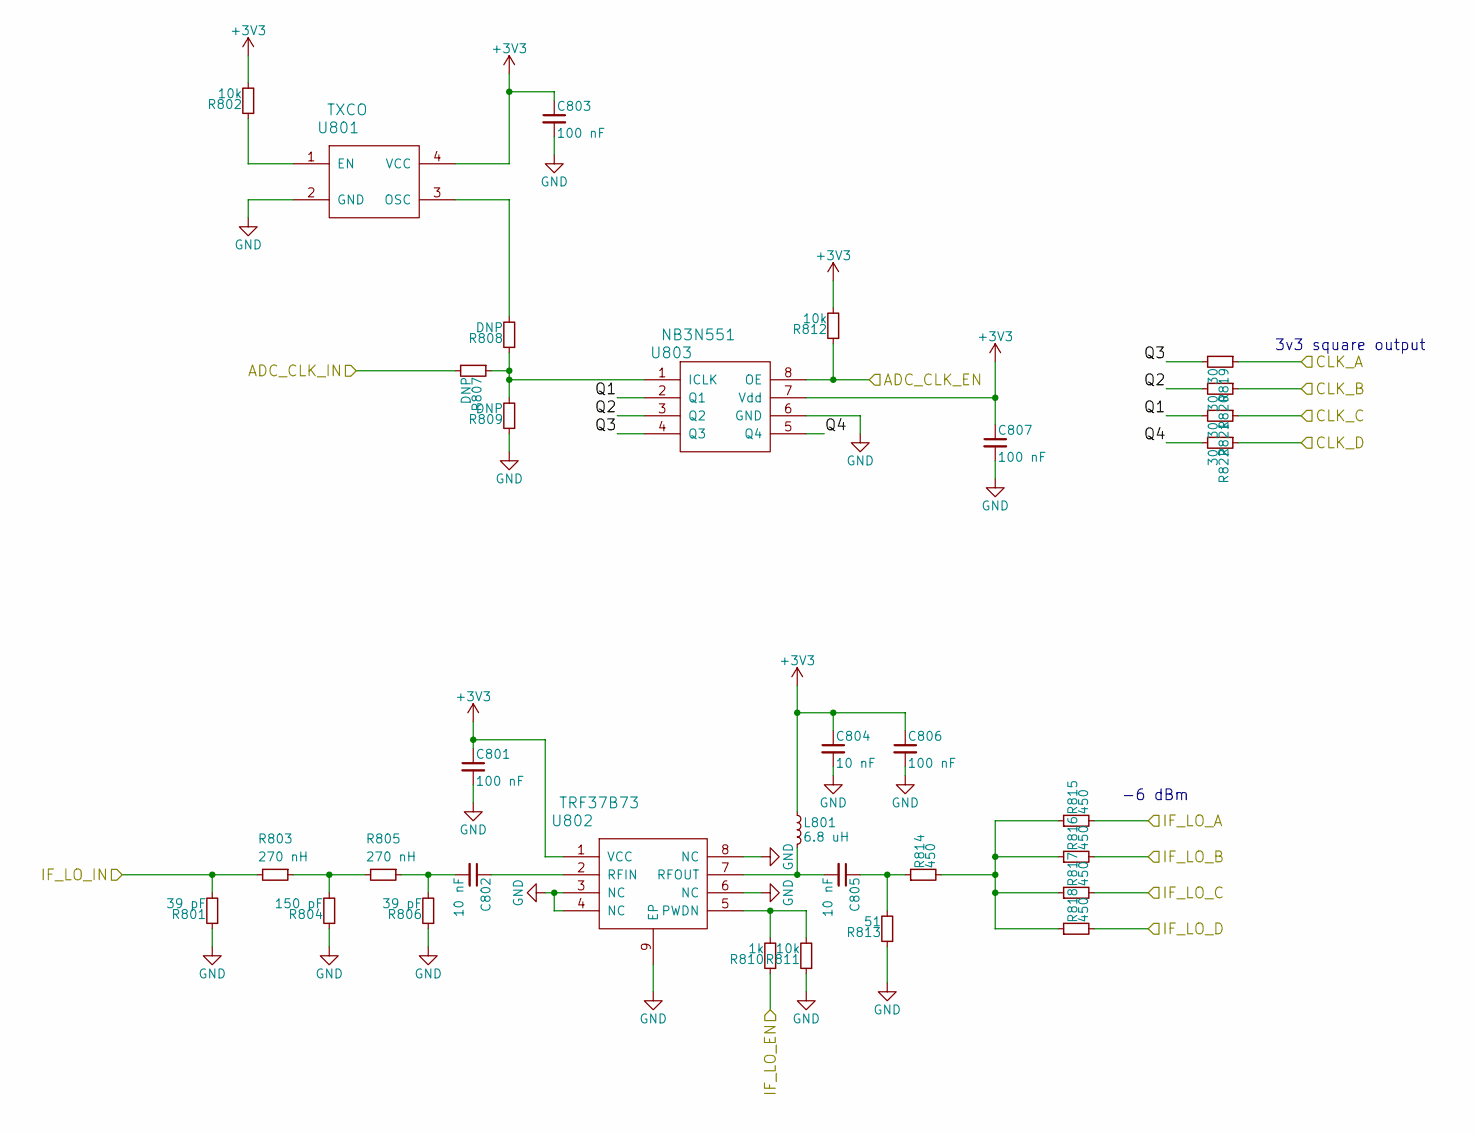
[picture p139: schematic clock_distro.sch]

Parts:
C801, C803, C806, C807: 100 nF; C_0402
C802, C804, C805: 10 nF; C_0402
L801: 6.8 uH; R_0603
R801, R806: 39 pF; R_0402
R802, R811, R812: 10k; R_0402
R803, R805: 270 nH; R_0402
R804: 150 pF; R_0402
R807, R808, R809: DNP; R_0402
R810: 1k; R_0402
R813: 51; R_0402
R814, R815, R816, R817, R818: 450; R_0402
R819, R820, R821, R822: 30; R_0402
U801: TXCO; crystal_FA238-TSX3225
U802: TRF37B73; DFN-8-1EP_2x2mm_Pitch0.5mm
U803: NB3N551; SOIC-8_3.9x4.9mm_Pitch1.27mm

Connections:
+3V3: C801.1, C803.1, C804.1, C806.1, C807.1, L801.1, R802.2, R812.2, U801.4 (VCC), U802.1 (VCC), U803.7 (Vdd)
ADC_CLK_EN: R812.1, U803.8 (OE)
ADC_CLK_IN: R807.2
CLK_A: R819.1
CLK_B: R820.1
CLK_C: R821.1
CLK_D: R822.1
GND: C801.2, C803.2, C804.2, C806.2, C807.2, R801.1, R804.1, R806.1, R809.1, R811.1, R813.1, U801.2 (GND), U802.3 (NC), U802.4 (NC), U802.6 (NC), U802.8 (NC), U802.9 (EP), U803.6 (GND)
IF_LO_A: R815.2
IF_LO_B: R816.2
IF_LO_C: R817.2
IF_LO_D: R818.2
IF_LO_EN: R810.1
IF_LO_IN: R801.2, R803.2
unnamed: C802.1, U802.2 (RFIN)
unnamed: C802.2, R805.1, R806.2
unnamed: C805.1, R813.2, R814.1
unnamed: C805.2, L801.2, U802.7 (RFOUT)
unnamed: R802.1, U801.1 (EN)
unnamed: R803.1, R804.2, R805.2
unnamed: R807.1, R808.1, R809.2, U803.1 (ICLK)
unnamed: R808.2, U801.3 (OSC)
unnamed: R810.2, R811.2, U802.5 (PWDN)
unnamed: R814.2, R815.1, R816.1, R817.1, R818.1
Q1: R821.2, U803.2 (Q1)
Q2: R820.2, U803.3 (Q2)
Q3: R819.2, U803.4 (Q3)
Q4: R822.2, U803.5 (Q4)

Notes on the sheet:
3v3 square output
-6 dBm
