loxodes/vna/hardware/vna_r0/vna_demod/conn_power.sch

## KiCad design hardware/vna_r0/vna_demod/conn_power.sch (2017-08-17)

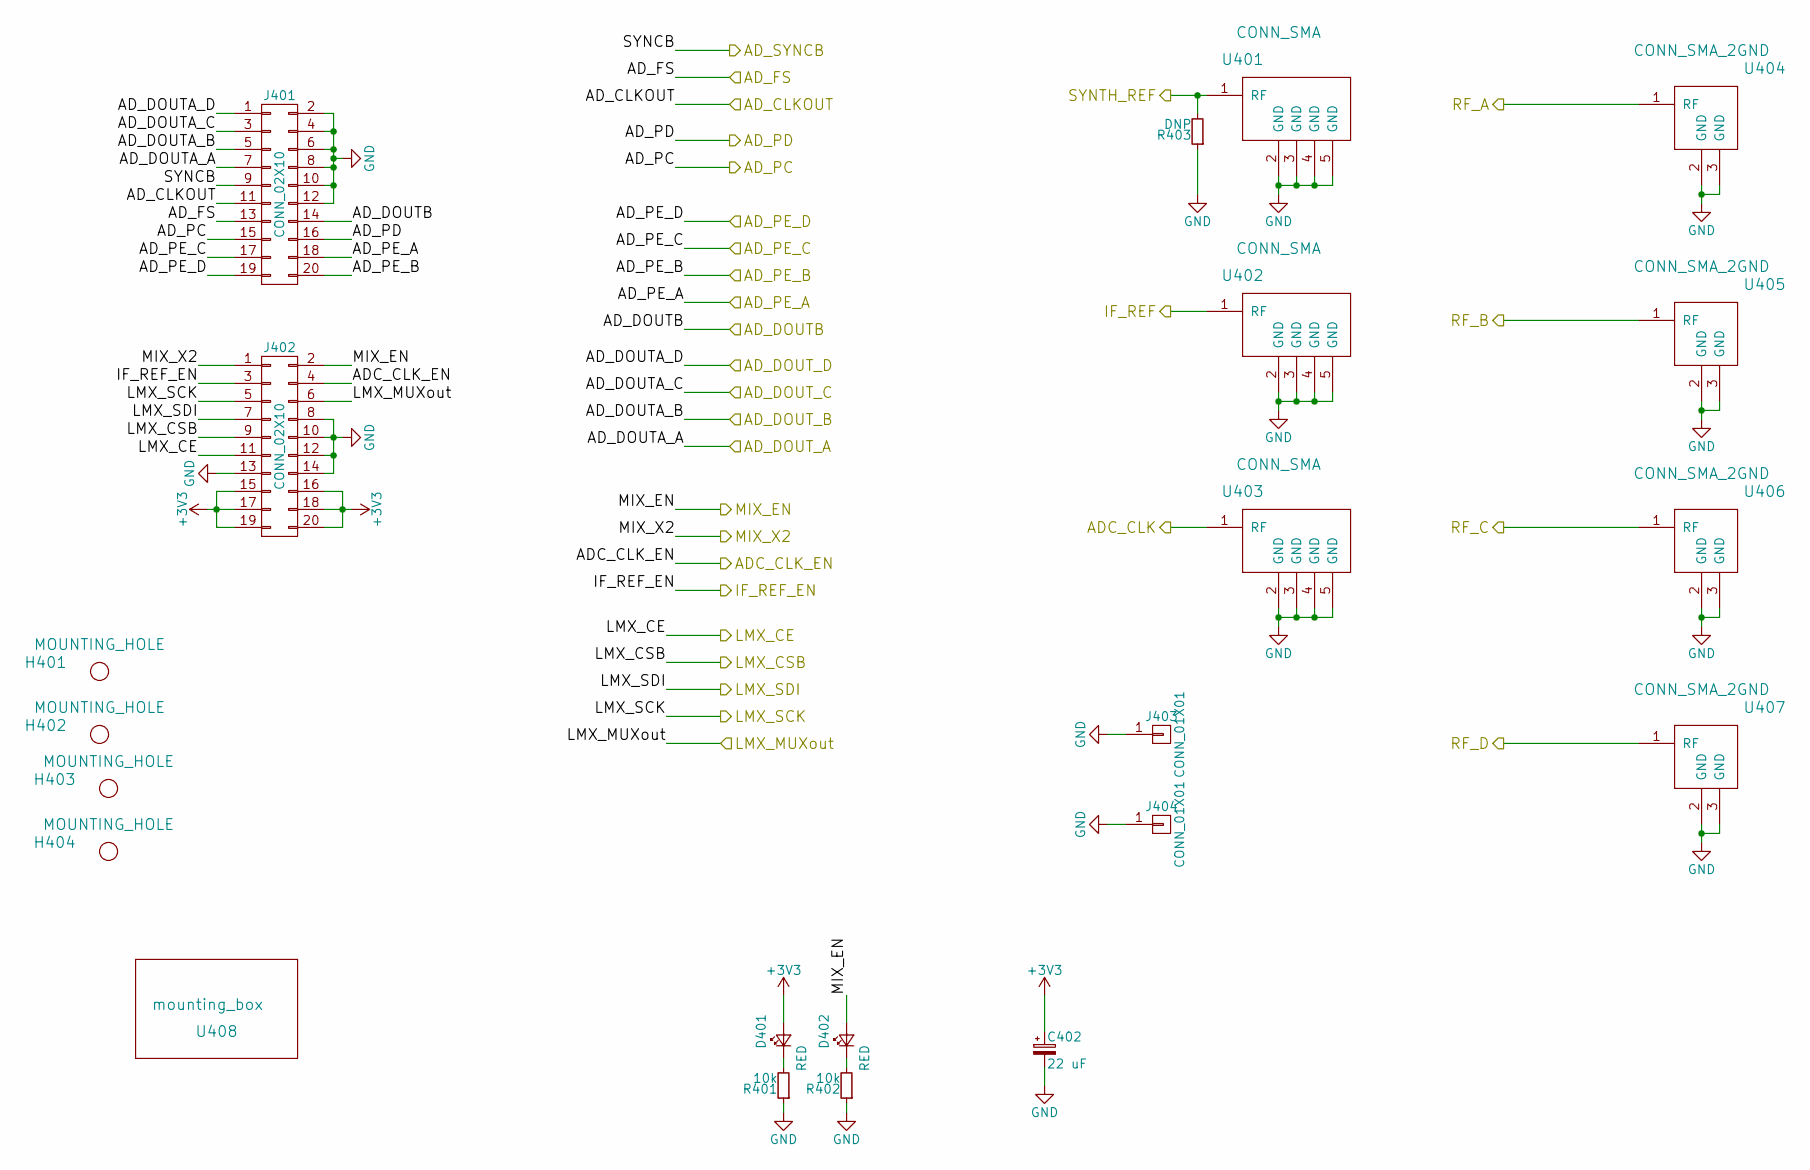
[picture p140: schematic conn_power.sch]

Parts:
C402: 22 uF; c_elec_10x10
D401, D402: RED; LED_0603
H401, H402, H403, H404: MOUNTING_HOLE; MountingHole_2-7mm
J401, J402: CONN_02X10; IDC_Header_Straight_20pins
J403, J404: CONN_01X01; Pin_Header_Straight_1x01
R401, R402: 10k; R_0402
R403: DNP; R_0402
U401, U402, U403: CONN_SMA; 732511150_sma_thin
U404, U405, U406, U407: CONN_SMA_2GND; SMA_901-10512_30MIL_OSHFR408_CPW_LAUNCH
U408: mounting_box; snail

Connections:
+3V3: C402.1, D401.2 (A), J402.15, J402.16, J402.17, J402.18, J402.19, J402.20
ADC_CLK: U403.1 (RF)
ADC_CLK_EN: J402.4
AD_CLKOUT: J401.11
AD_DOUTB: J401.14
AD_DOUT_A: J401.7
AD_DOUT_B: J401.5
AD_DOUT_C: J401.3
AD_DOUT_D: J401.1
AD_FS: J401.13
AD_PC: J401.15
AD_PD: J401.16
AD_PE_A: J401.18
AD_PE_B: J401.20
AD_PE_C: J401.17
AD_PE_D: J401.19
AD_SYNCB: J401.9
GND: C402.2, J401.2, J401.4, J401.6, J401.8, J401.10, J401.12, J402.8, J402.10, J402.12, J402.13, J402.14, J403.1, J404.1, R401.1, R402.1, R403.1, U401.2 (GND), U401.3 (GND), U401.4 (GND), U401.5 (GND), U402.2 (GND), U402.3 (GND), U402.4 (GND), U402.5 (GND), U403.2 (GND), U403.3 (GND), U403.4 (GND), U403.5 (GND), U404.2 (GND), U404.3 (GND), U405.2 (GND), U405.3 (GND), U406.2 (GND), U406.3 (GND), U407.2 (GND), U407.3 (GND)
IF_REF: U402.1 (RF)
IF_REF_EN: J402.3
LMX_CE: J402.11
LMX_CSB: J402.9
LMX_MUXout: J402.6
LMX_SCK: J402.5
LMX_SDI: J402.7
MIX_EN: D402.2 (A), J402.2
MIX_X2: J402.1
unnamed: D401.1 (K), R401.2
unnamed: D402.1 (K), R402.2
RF_A: U404.1 (RF)
RF_B: U405.1 (RF)
RF_C: U406.1 (RF)
RF_D: U407.1 (RF)
SYNTH_REF: R403.2, U401.1 (RF)
