loxodes/vna/hardware/vna_r0/vna_demod/demod.sch

## KiCad design hardware/vna_r0/vna_demod/demod.sch (2017-07-08)

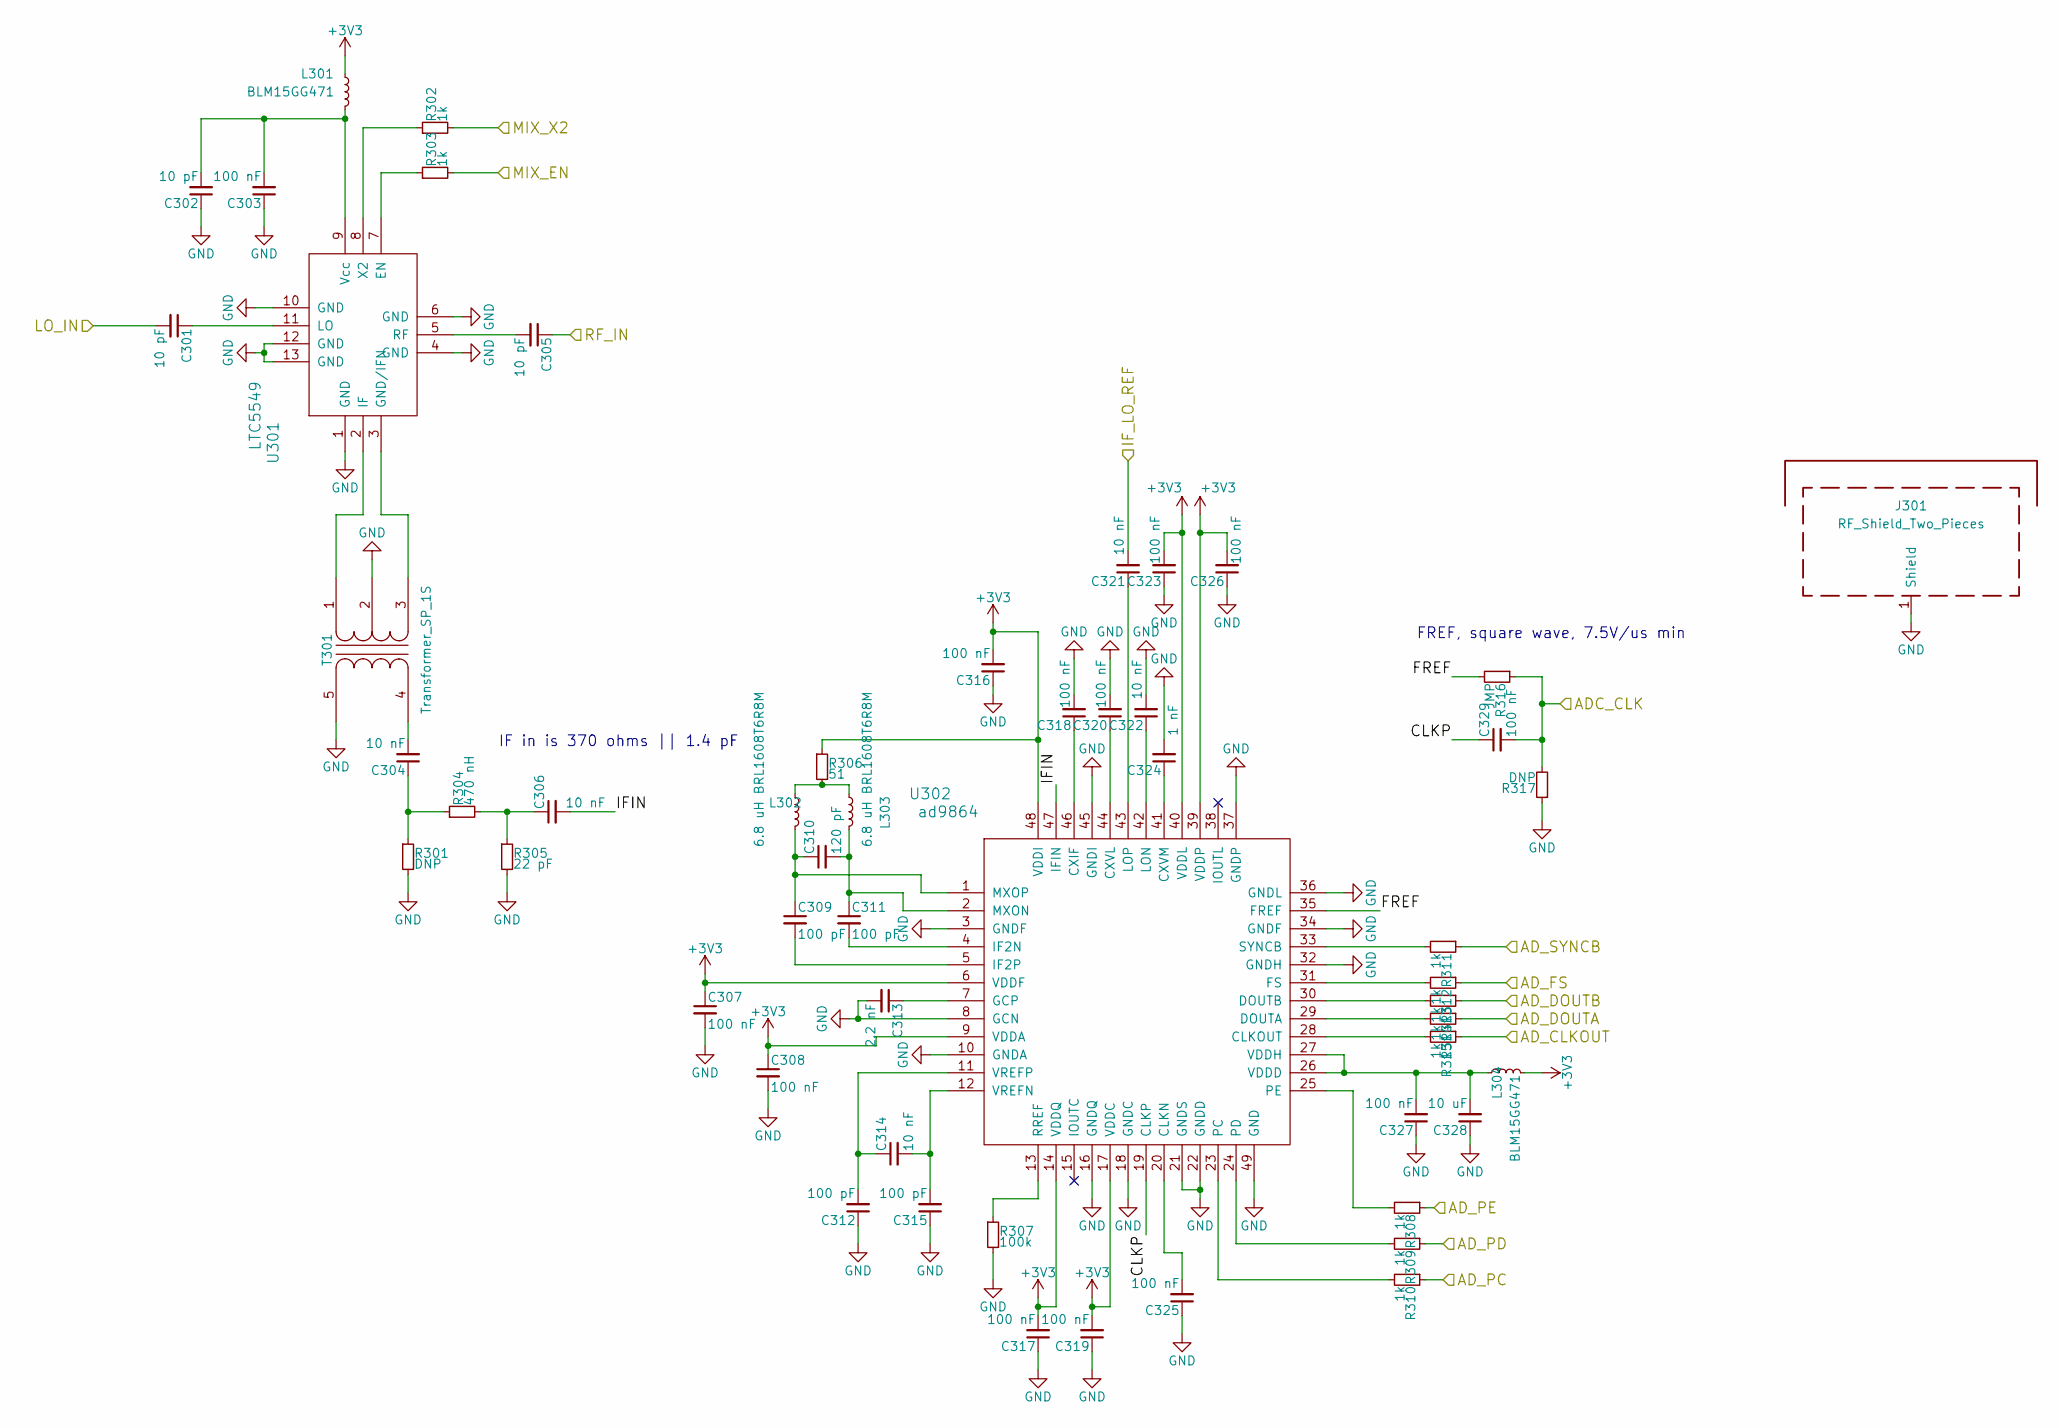
[picture p141: schematic demod.sch]

Parts:
C301, C302, C305: 10 pF; C_0402
C303, C307, C308, C316, C317, C318, C319, C320, C323, C325, C326, C327, C329: 100 nF; C_0402
C304, C306, C314, C321, C322: 10 nF; C_0402
C309, C311, C312, C315: 100 pF; C_0402
C310: 120 pF; C_0402
C313: 2.2 nF; C_0402
C324: 1 nF; C_0402
C328: 10 uF; C_0603
J301: RF_Shield_Two_Pieces; Laird_Technologies_BMI-S-209-F_29.36x18.50mm
L301, L304: BLM15GG471; R_0402
L302, L303: 6.8 uH BRL1608T6R8M; R_0603
R301, R317: DNP; R_0402
R302, R303, R308, R309, R310, R311, R312, R313, R314, R315: 1k; R_0402
R304: 470 nH; R_0402
R305: 22 pF; R_0402
R306: 51; R_0402
R307: 100k; R_0402
R316: JMP; R_0402
T301: Transformer_SP_1S; 5LEAD_BALUN_4p83mm_3p3mm
U301: LTC5549; QFN_12_3mm2mm
U302: ad9864; QFN-48-1EP_7x7mm_Pitch0.5mm

Connections:
+3V3: C307.1, C308.1, C316.2, C317.2, C319.2, C323.2, C326.2, L301.1, L304.2, R306.1, U302.6 (VDDF), U302.9 (VDDA), U302.14 (VDDQ), U302.17 (VDDC), U302.39 (VDDP), U302.40 (VDDL), U302.48 (VDDI)
ADC_CLK: C329.2, R316.1, R317.2
AD_CLKOUT: R315.1
AD_DOUTA: R314.1
AD_DOUTB: R313.1
AD_FS: R312.1
AD_PC: R310.1
AD_PD: R309.1
AD_PE: R308.1
AD_SYNCB: R311.1
CLKP: C329.1, U302.19 (CLKP)
FREF: R316.2, U302.35 (FREF)
GND: C302.1, C303.1, C307.2, C308.2, C312.1, C313.2, C315.1, C316.1, C317.1, C318.2, C319.1, C320.2, C322.2, C323.1, C324.2, C325.1, C326.1, C327.1, C328.1, J301.1, R301.2, R305.2, R307.2, R317.1, T301.2 (PM), T301.5 (S2), U301.1 (GND), U301.4 (GND), U301.6 (GND), U301.10 (GND), U301.12 (GND), U301.13 (GND), U302.3 (GNDF), U302.8 (GCN), U302.10 (GNDA), U302.16 (GNDQ), U302.18 (GNDC), U302.21 (GNDS), U302.22 (GNDD), U302.32 (GNDH), U302.34 (GNDF), U302.36 (GNDL), U302.37 (GNDP), U302.45 (GNDI), U302.49 (GND)
IFIN: C306.2, U302.47 (IFIN)
IF_LO_REF: C321.2
LO_IN: C301.2
MIX_EN: R303.2
MIX_X2: R302.2
unnamed: C301.1, U301.11 (LO)
unnamed: C302.2, C303.2, L301.2, U301.9 (Vcc)
unnamed: C304.1, R301.1, R304.1
unnamed: C304.2, T301.4 (S1)
unnamed: C305.2, U301.5 (RF)
unnamed: C306.1, R304.2, R305.1
unnamed: C309.1, C310.1, L302.2, U302.1 (MXOP)
unnamed: C309.2, U302.5 (IF2P)
unnamed: C310.2, C311.1, L303.2, U302.2 (MXON)
unnamed: C311.2, U302.4 (IF2N)
unnamed: C312.2, C314.1, U302.11 (VREFP)
unnamed: C313.1, U302.7 (GCP)
unnamed: C314.2, C315.2, U302.12 (VREFN)
unnamed: C318.1, U302.46 (CXIF)
unnamed: C320.1, U302.44 (CXVL)
unnamed: C321.1, U302.43 (LOP)
unnamed: C322.1, U302.42 (LON)
unnamed: C324.1, U302.41 (CXVM)
unnamed: C325.2, U302.20 (CLKN)
unnamed: C327.2, C328.2, L304.1, U302.26 (VDDD), U302.27 (VDDH)
unnamed: L302.1, L303.1, R306.2
unnamed: R302.1, U301.8 (X2)
unnamed: R303.1, U301.7 (EN)
unnamed: R307.1, U302.13 (RREF)
unnamed: R308.2, U302.25 (PE)
unnamed: R309.2, U302.24 (PD)
unnamed: R310.2, U302.23 (PC)
unnamed: R311.2, U302.33 (SYNCB)
unnamed: R312.2, U302.31 (FS)
unnamed: R313.2, U302.30 (DOUTB)
unnamed: R314.2, U302.29 (DOUTA)
unnamed: R315.2, U302.28 (CLKOUT)
unnamed: T301.1 (PR1), U301.2 (IF)
unnamed: T301.3 (PR2), U301.3 (GND/IFN)
RF_IN: C305.1

Notes on the sheet:
FREF, square wave, 7.5V/us min
IF in is 370 ohms || 1.4 pF
