loxodes/vna/hardware/vna_r0/vna_demod/lo_synth.sch

## KiCad design hardware/vna_r0/vna_demod/lo_synth.sch (2017-08-17)

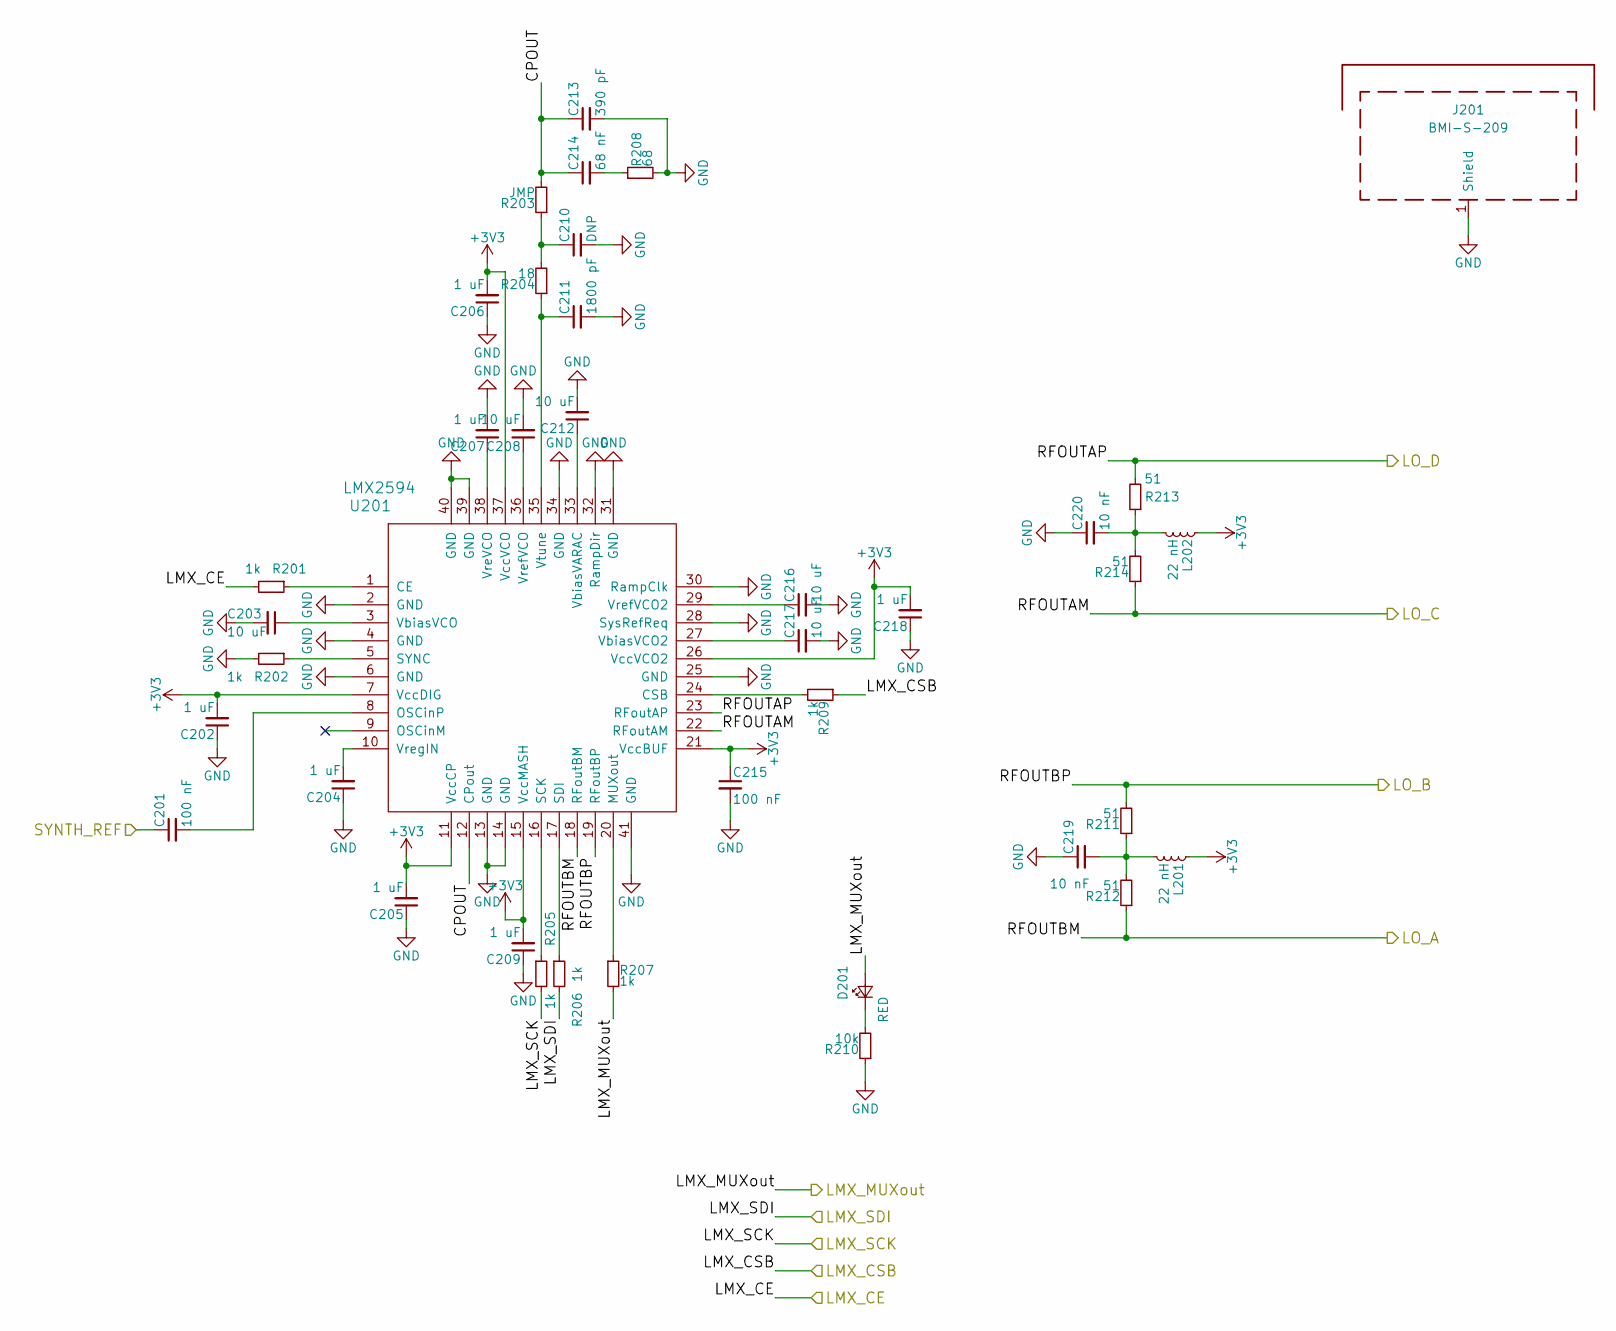
[picture p142: schematic lo_synth.sch]

Parts:
C201, C215: 100 nF; C_0402
C202, C204, C205, C206, C207, C209, C218: 1 uF; C_0402
C203, C208, C212, C216, C217: 10 uF; C_0603
C210: DNP; C_0402
C211: 1800 pF; C_0402
C213: 390 pF; C_0402
C214: 68 nF; C_0402
C219, C220: 10 nF; C_0402
D201: RED; LED_0603
J201: BMI-S-209; Laird_Technologies_BMI-S-209-F_29.36x18.50mm
L201, L202: 22 nH; R_0402
R201, R202, R205, R206, R207, R209: 1k; R_0402
R203: JMP; R_0402
R204: 18; R_0402
R208: 68; R_0402
R210: 10k; R_0402
R211, R212, R213, R214: 51; R_0402
U201: LMX2594; QFN-40-1EP_6x6mm_Pitch0.5mm

Connections:
+3V3: C202.2, C205.2, C206.2, C209.2, C215.1, C218.2, L201.1, L202.1, U201.7 (VccDIG), U201.11 (VccCP), U201.15 (VccMASH), U201.21 (VccBUF), U201.26 (VccVCO2), U201.37 (VccVCO)
CPOUT: C213.1, C214.1, R203.2, U201.12 (CPout)
GND: C202.1, C203.2, C204.1, C205.1, C206.1, C207.2, C208.2, C209.1, C210.2, C211.2, C212.2, C213.2, C215.2, C216.2, C217.2, C218.1, C219.1, C220.1, J201.1, R202.2, R208.2, R210.1, U201.2 (GND), U201.4 (GND), U201.6 (GND), U201.13 (GND), U201.14 (GND), U201.25 (GND), U201.28 (SysRefReq), U201.30 (RampClk), U201.31 (GND), U201.32 (RampDir), U201.34 (GND), U201.39 (GND), U201.40 (GND), U201.41 (GND)
LMX_CE: R201.2
LMX_CSB: R209.1
LMX_MUXout: D201.2 (A), R207.2
LMX_SCK: R205.2
LMX_SDI: R206.2
LO_A: R212.1, U201.18 (RFoutBM)
LO_B: R211.2, U201.19 (RFoutBP)
LO_C: R214.1, U201.22 (RFoutAM)
LO_D: R213.2, U201.23 (RFoutAP)
unnamed: C201.2, U201.8 (OSCinP)
unnamed: C203.1, U201.3 (VbiasVCO)
unnamed: C204.2, U201.10 (VregIN)
unnamed: C207.1, U201.38 (VreVCO)
unnamed: C208.1, U201.36 (VrefVCO)
unnamed: C210.1, R203.1, R204.2
unnamed: C211.1, R204.1, U201.35 (Vtune)
unnamed: C212.1, U201.33 (VbiasVARAC)
unnamed: C214.2, R208.1
unnamed: C216.1, U201.29 (VrefVCO2)
unnamed: C217.1, U201.27 (VbiasVCO2)
unnamed: C219.2, L201.2, R211.1, R212.2
unnamed: C220.2, L202.2, R213.1, R214.2
unnamed: D201.1 (K), R210.2
unnamed: R201.1, U201.1 (CE)
unnamed: R202.1, U201.5 (SYNC)
unnamed: R205.1, U201.16 (SCK)
unnamed: R206.1, U201.17 (SDI)
unnamed: R207.1, U201.20 (MUXout)
unnamed: R209.2, U201.24 (CSB)
SYNTH_REF: C201.1
