loxodes/vna/hardware/vna_r0/vna_rf/conn_power.sch

## KiCad design hardware/vna_r0/vna_rf/conn_power.sch (2017-08-17)

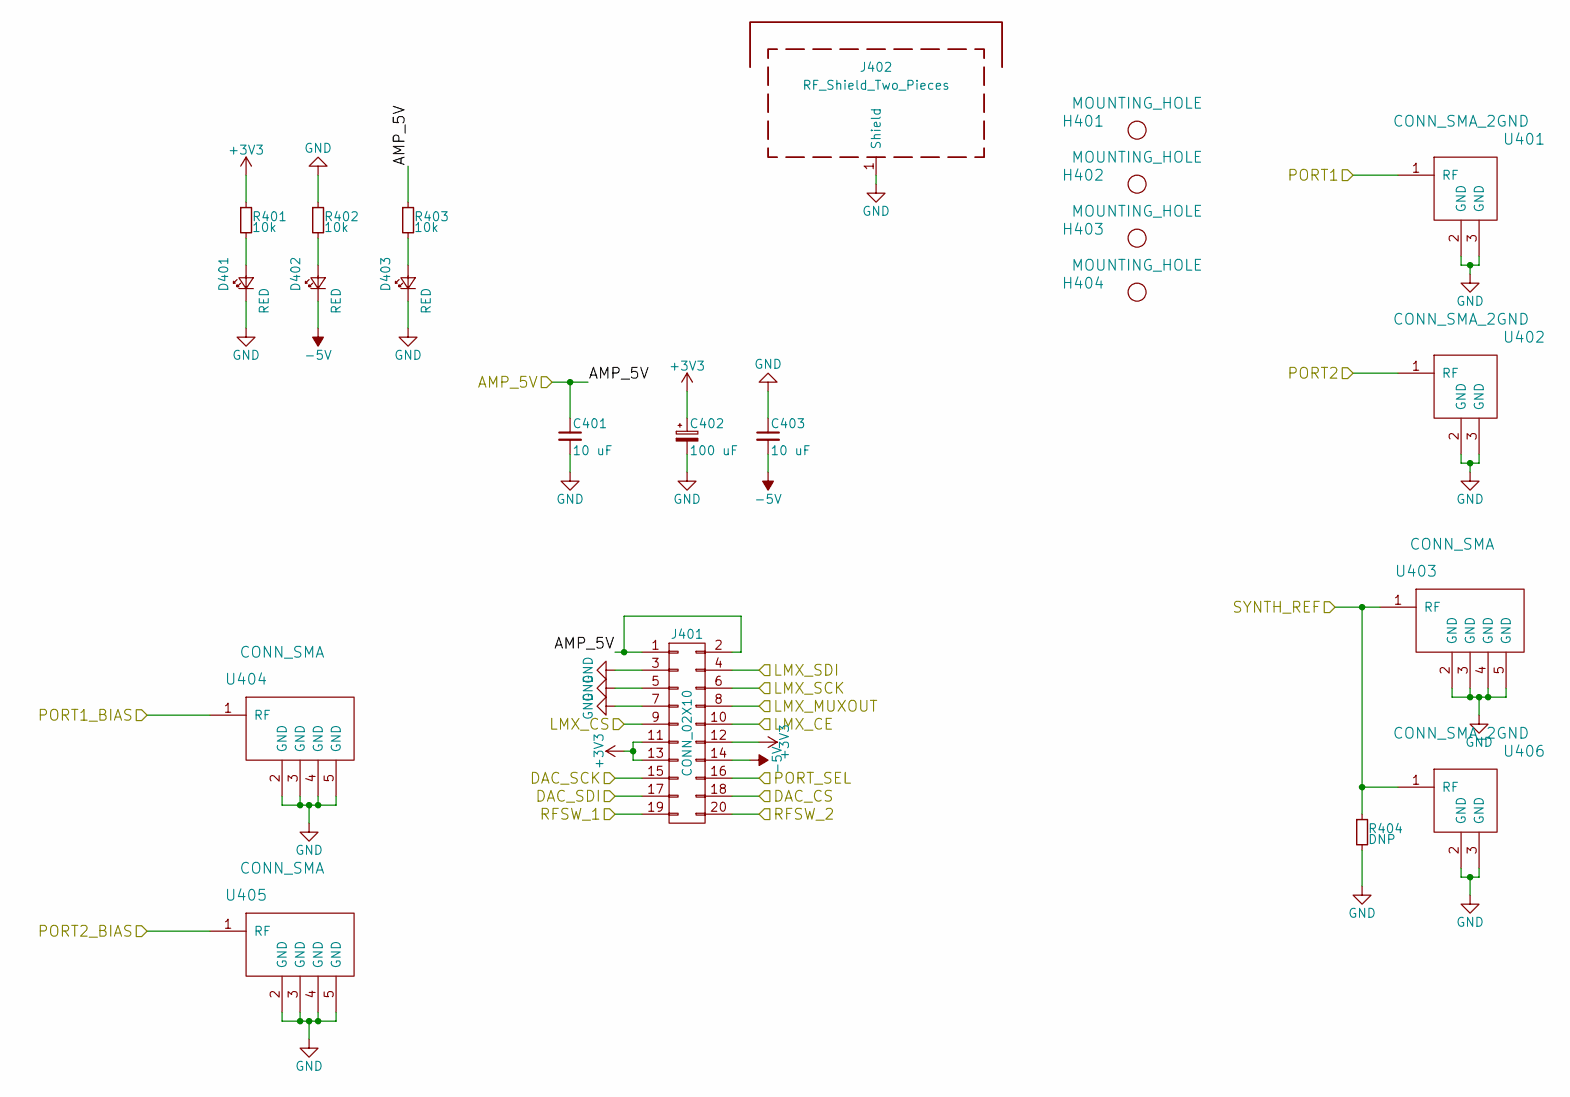
[picture p143: schematic conn_power.sch]

Parts:
C401, C403: 10 uF; C_0603
C402: 100 uF; c_elec_10x10
D401, D402, D403: RED; LED_0603
H401, H402, H403, H404: MOUNTING_HOLE; MountingHole_2-7mm
J401: CONN_02X10; IDC_Header_Straight_20pins
J402: RF_Shield_Two_Pieces; Laird_Technologies_BMI-S-205-F_38.10x25.40mm
R401, R402, R403: 10k; R_0402
R404: DNP; R_0402
U401, U402: CONN_SMA_2GND; SMA_901-10512_30MIL_OSHFR408_CPW_LAUNCH
U403, U404, U405: CONN_SMA; 732511150_sma_thin
U406: CONN_SMA_2GND; 734120110_ufl_umc

Connections:
+3V3: C402.1, J401.11, J401.12, J401.13, R401.1
-5V: C403.2, D402.1 (K), J401.14
AMP_5V: C401.1, J401.1, J401.2, R403.1
DAC_CS: J401.18
DAC_SCK: J401.15
DAC_SDI: J401.17
GND: C401.2, C402.2, C403.1, D401.1 (K), D403.1 (K), J401.3, J401.5, J401.7, J402.1, R402.1, R404.2, U401.2 (GND), U401.3 (GND), U402.2 (GND), U402.3 (GND), U403.2 (GND), U403.3 (GND), U403.4 (GND), U403.5 (GND), U404.2 (GND), U404.3 (GND), U404.4 (GND), U404.5 (GND), U405.2 (GND), U405.3 (GND), U405.4 (GND), U405.5 (GND), U406.2 (GND), U406.3 (GND)
LMX_CE: J401.10
LMX_CS: J401.9
LMX_MUXOUT: J401.8
LMX_SCK: J401.6
LMX_SDI: J401.4
unnamed: D401.2 (A), R401.2
unnamed: D402.2 (A), R402.2
unnamed: D403.2 (A), R403.2
PORT1: U401.1 (RF)
PORT1_BIAS: U404.1 (RF)
PORT2: U402.1 (RF)
PORT2_BIAS: U405.1 (RF)
PORT_SEL: J401.16
RFSW_1: J401.19
RFSW_2: J401.20
SYNTH_REF: R404.1, U403.1 (RF), U406.1 (RF)
