loxodes/vna/hardware/vna_r0/vna_rf/port_switch.sch

## KiCad design hardware/vna_r0/vna_rf/port_switch.sch (2017-08-02)

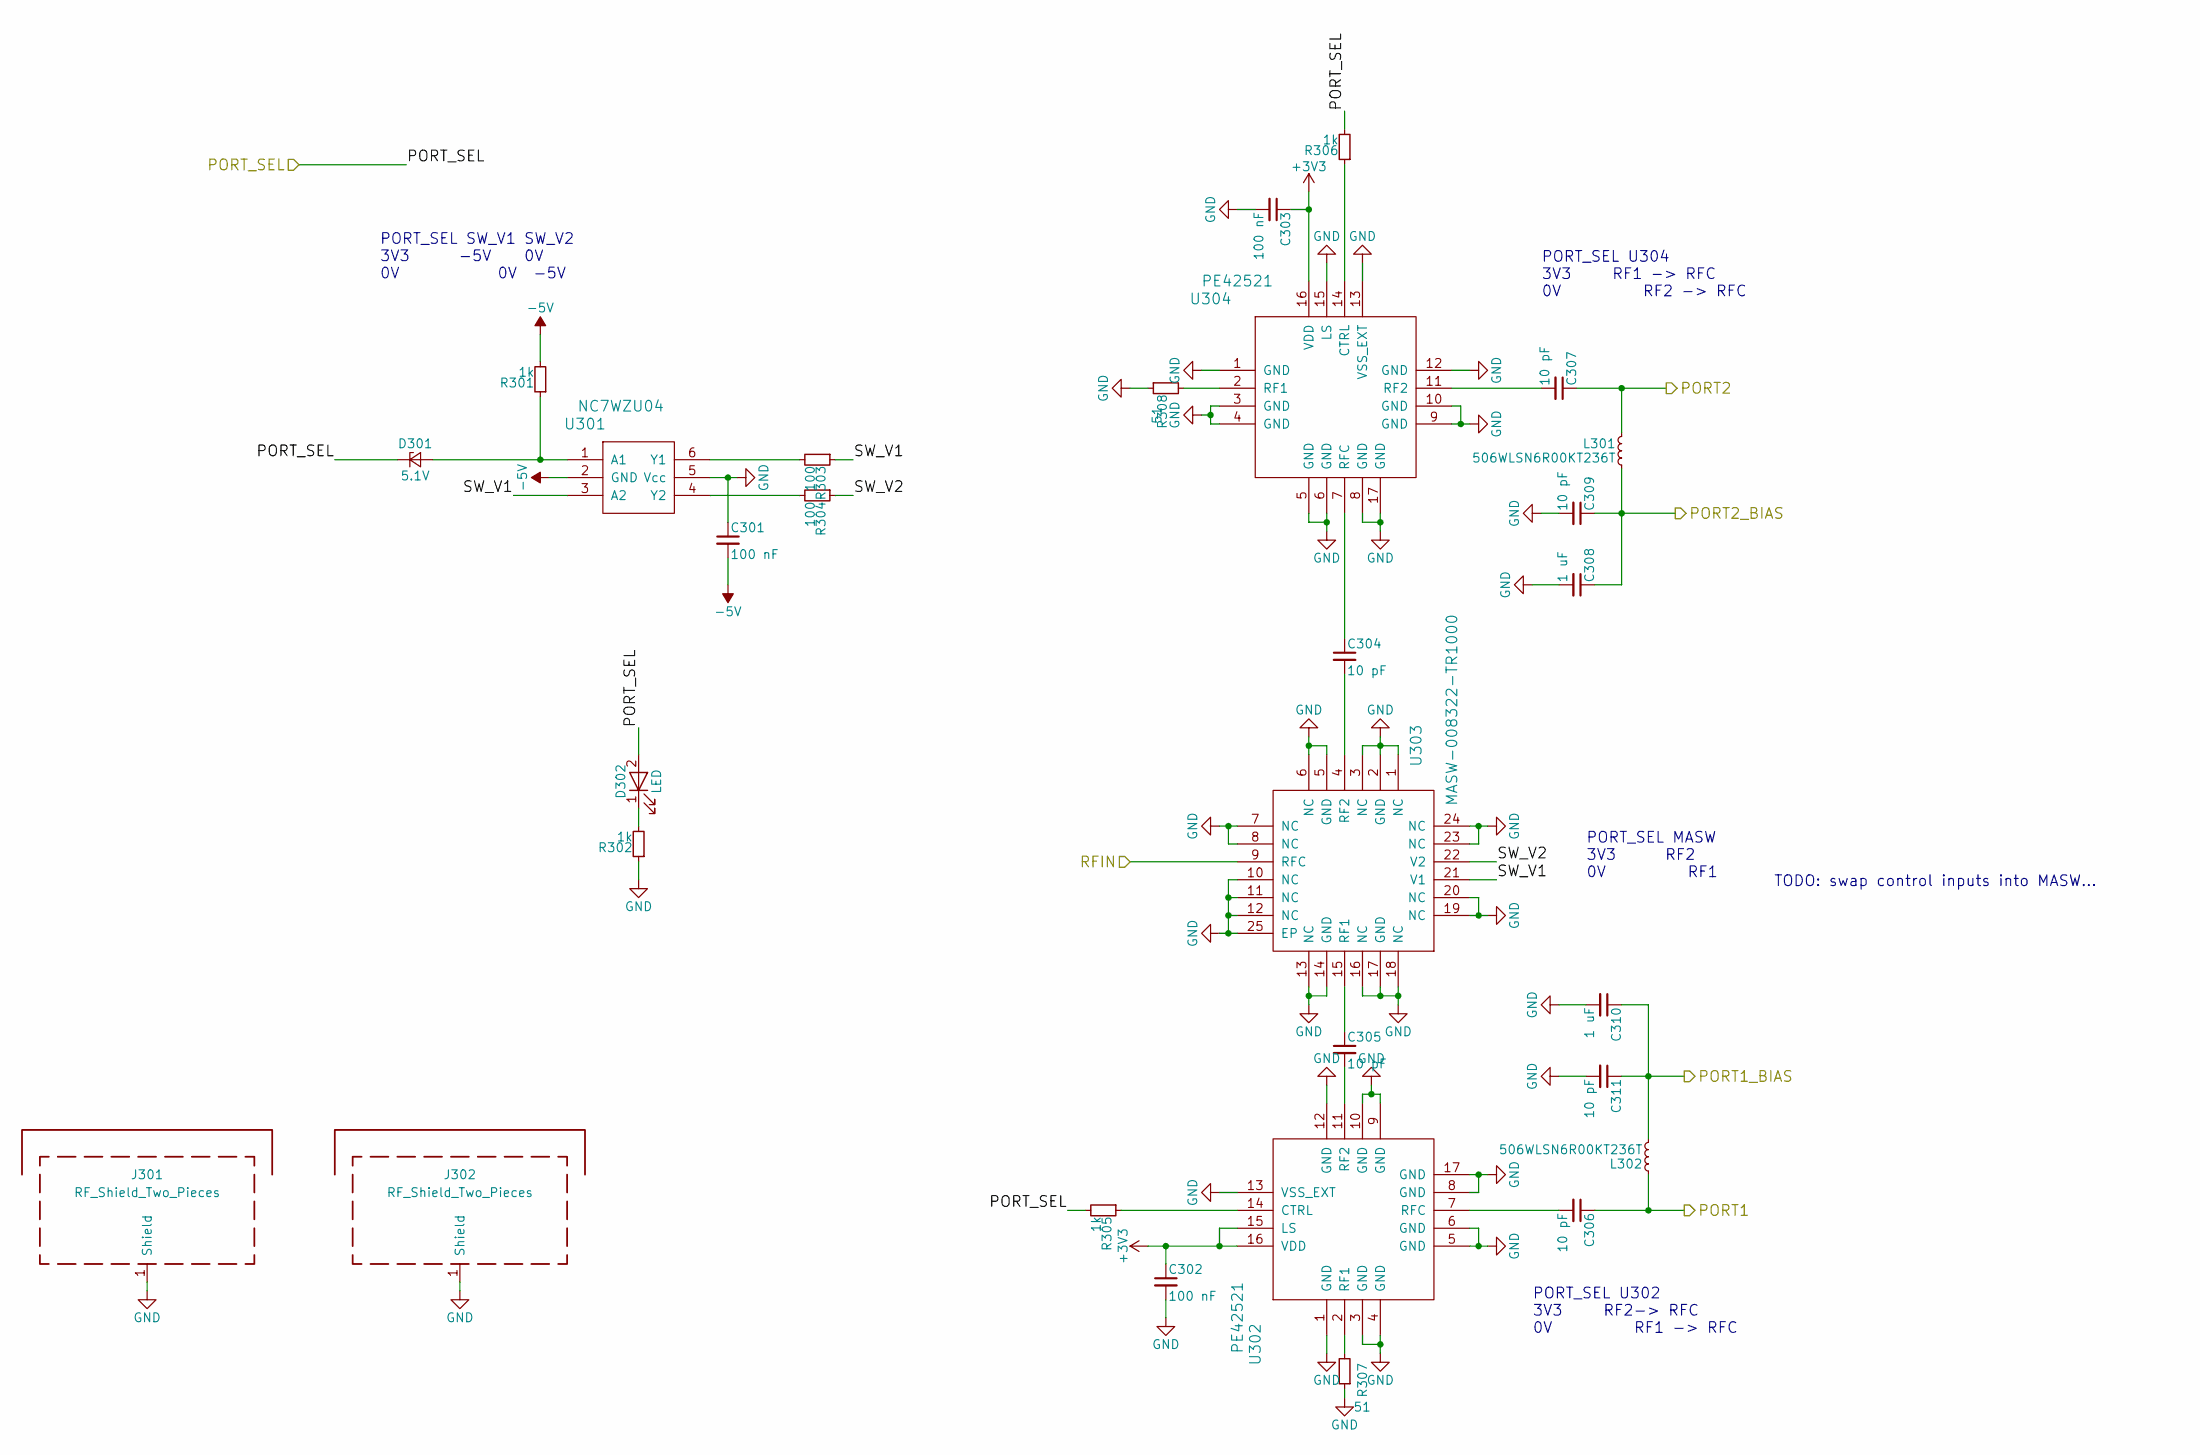
[picture p144: schematic port_switch.sch]

Parts:
C301, C302, C303: 100 nF; C_0402
C304, C305, C306, C307, C309, C311: 10 pF; C_0402
C308, C310: 1 uF; C_0805
D301: 5.1V; SOD-323
D302: LED; LED_0603
J301, J302: RF_Shield_Two_Pieces; Laird_Technologies_BMI-S-202-F_16.50x16.50mm
L301, L302: 506WLSN6R00KT236T; ATC506WLS
R301, R302, R305, R306: 1k; R_0402
R303, R304: 100; R_0402
R307, R308: 51; R_0402
U301: NC7WZU04; SC-70-6
U302, U304: PE42521; QFN-16-1EP_3x3mm_Pitch0.5mm
U303: MASW-008322-TR1000; QFN-24-1EP_4x4mm_Pitch0.5mm

Connections:
+3V3: C302.1, C303.1, U302.15 (LS), U302.16 (VDD), U304.16 (VDD)
-5V: C301.2, R301.2, U301.2 (GND)
GND: C301.1, C302.2, C303.2, C308.2, C309.2, C310.2, C311.2, J301.1, J302.1, R302.1, R307.1, R308.1, U301.5 (Vcc), U302.1 (GND), U302.3 (GND), U302.4 (GND), U302.5 (GND), U302.6 (GND), U302.8 (GND), U302.9 (GND), U302.10 (GND), U302.12 (GND), U302.13 (VSS_EXT), U302.17 (GND), U303.1 (NC), U303.2 (GND), U303.3 (NC), U303.5 (GND), U303.6 (NC), U303.7 (NC), U303.8 (NC), U303.10 (NC), U303.11 (NC), U303.12 (NC), U303.13 (NC), U303.14 (GND), U303.16 (NC), U303.17 (GND), U303.18 (NC), U303.19 (NC), U303.20 (NC), U303.23 (NC), U303.24 (NC), U303.25 (EP), U304.1 (GND), U304.3 (GND), U304.4 (GND), U304.5 (GND), U304.6 (GND), U304.8 (GND), U304.9 (GND), U304.10 (GND), U304.12 (GND), U304.13 (VSS_EXT), U304.15 (LS), U304.17 (GND)
unnamed: C304.1, U304.7 (RFC)
unnamed: C304.2, U303.4 (RF2)
unnamed: C305.1, U303.15 (RF1)
unnamed: C305.2, U302.11 (RF2)
unnamed: C306.2, U302.7 (RFC)
unnamed: C307.2, U304.11 (RF2)
unnamed: D301.2 (A), R301.1, U301.1 (A1)
unnamed: D302.1 (K), R302.2
unnamed: R303.2, U301.6 (Y1)
unnamed: R304.2, U301.4 (Y2)
unnamed: R305.1, U302.14 (CTRL)
unnamed: R306.1, U304.14 (CTRL)
unnamed: R307.2, U302.2 (RF1)
unnamed: R308.2, U304.2 (RF1)
PORT1: C306.1, L302.1
PORT1_BIAS: C310.1, C311.1, L302.2
PORT2: C307.1, L301.1
PORT2_BIAS: C308.1, C309.1, L301.2
PORT_SEL: D301.1 (K), D302.2 (A), R305.2, R306.2
RFIN: U303.9 (RFC)
SW_V1: R303.1, U301.3 (A2), U303.21 (V1)
SW_V2: R304.1, U303.22 (V2)

Notes on the sheet:
PORT_SEL SW_V1 SW_V2 3V3 -5V 0V 0V 0V -5V
PORT_SEL MASW 3V3 RF2 0V RF1
PORT_SEL U304 3V3 RF1 -> RFC 0V RF2 -> RFC
PORT_SEL U302 3V3 RF2-> RFC 0V RF1 -> RFC
TODO: swap control inputs into MASW...
