loxodes/vna/hardware/vna_r0/vna_rf/rf_synth.sch

## KiCad design hardware/vna_r0/vna_rf/rf_synth.sch (2017-08-17)

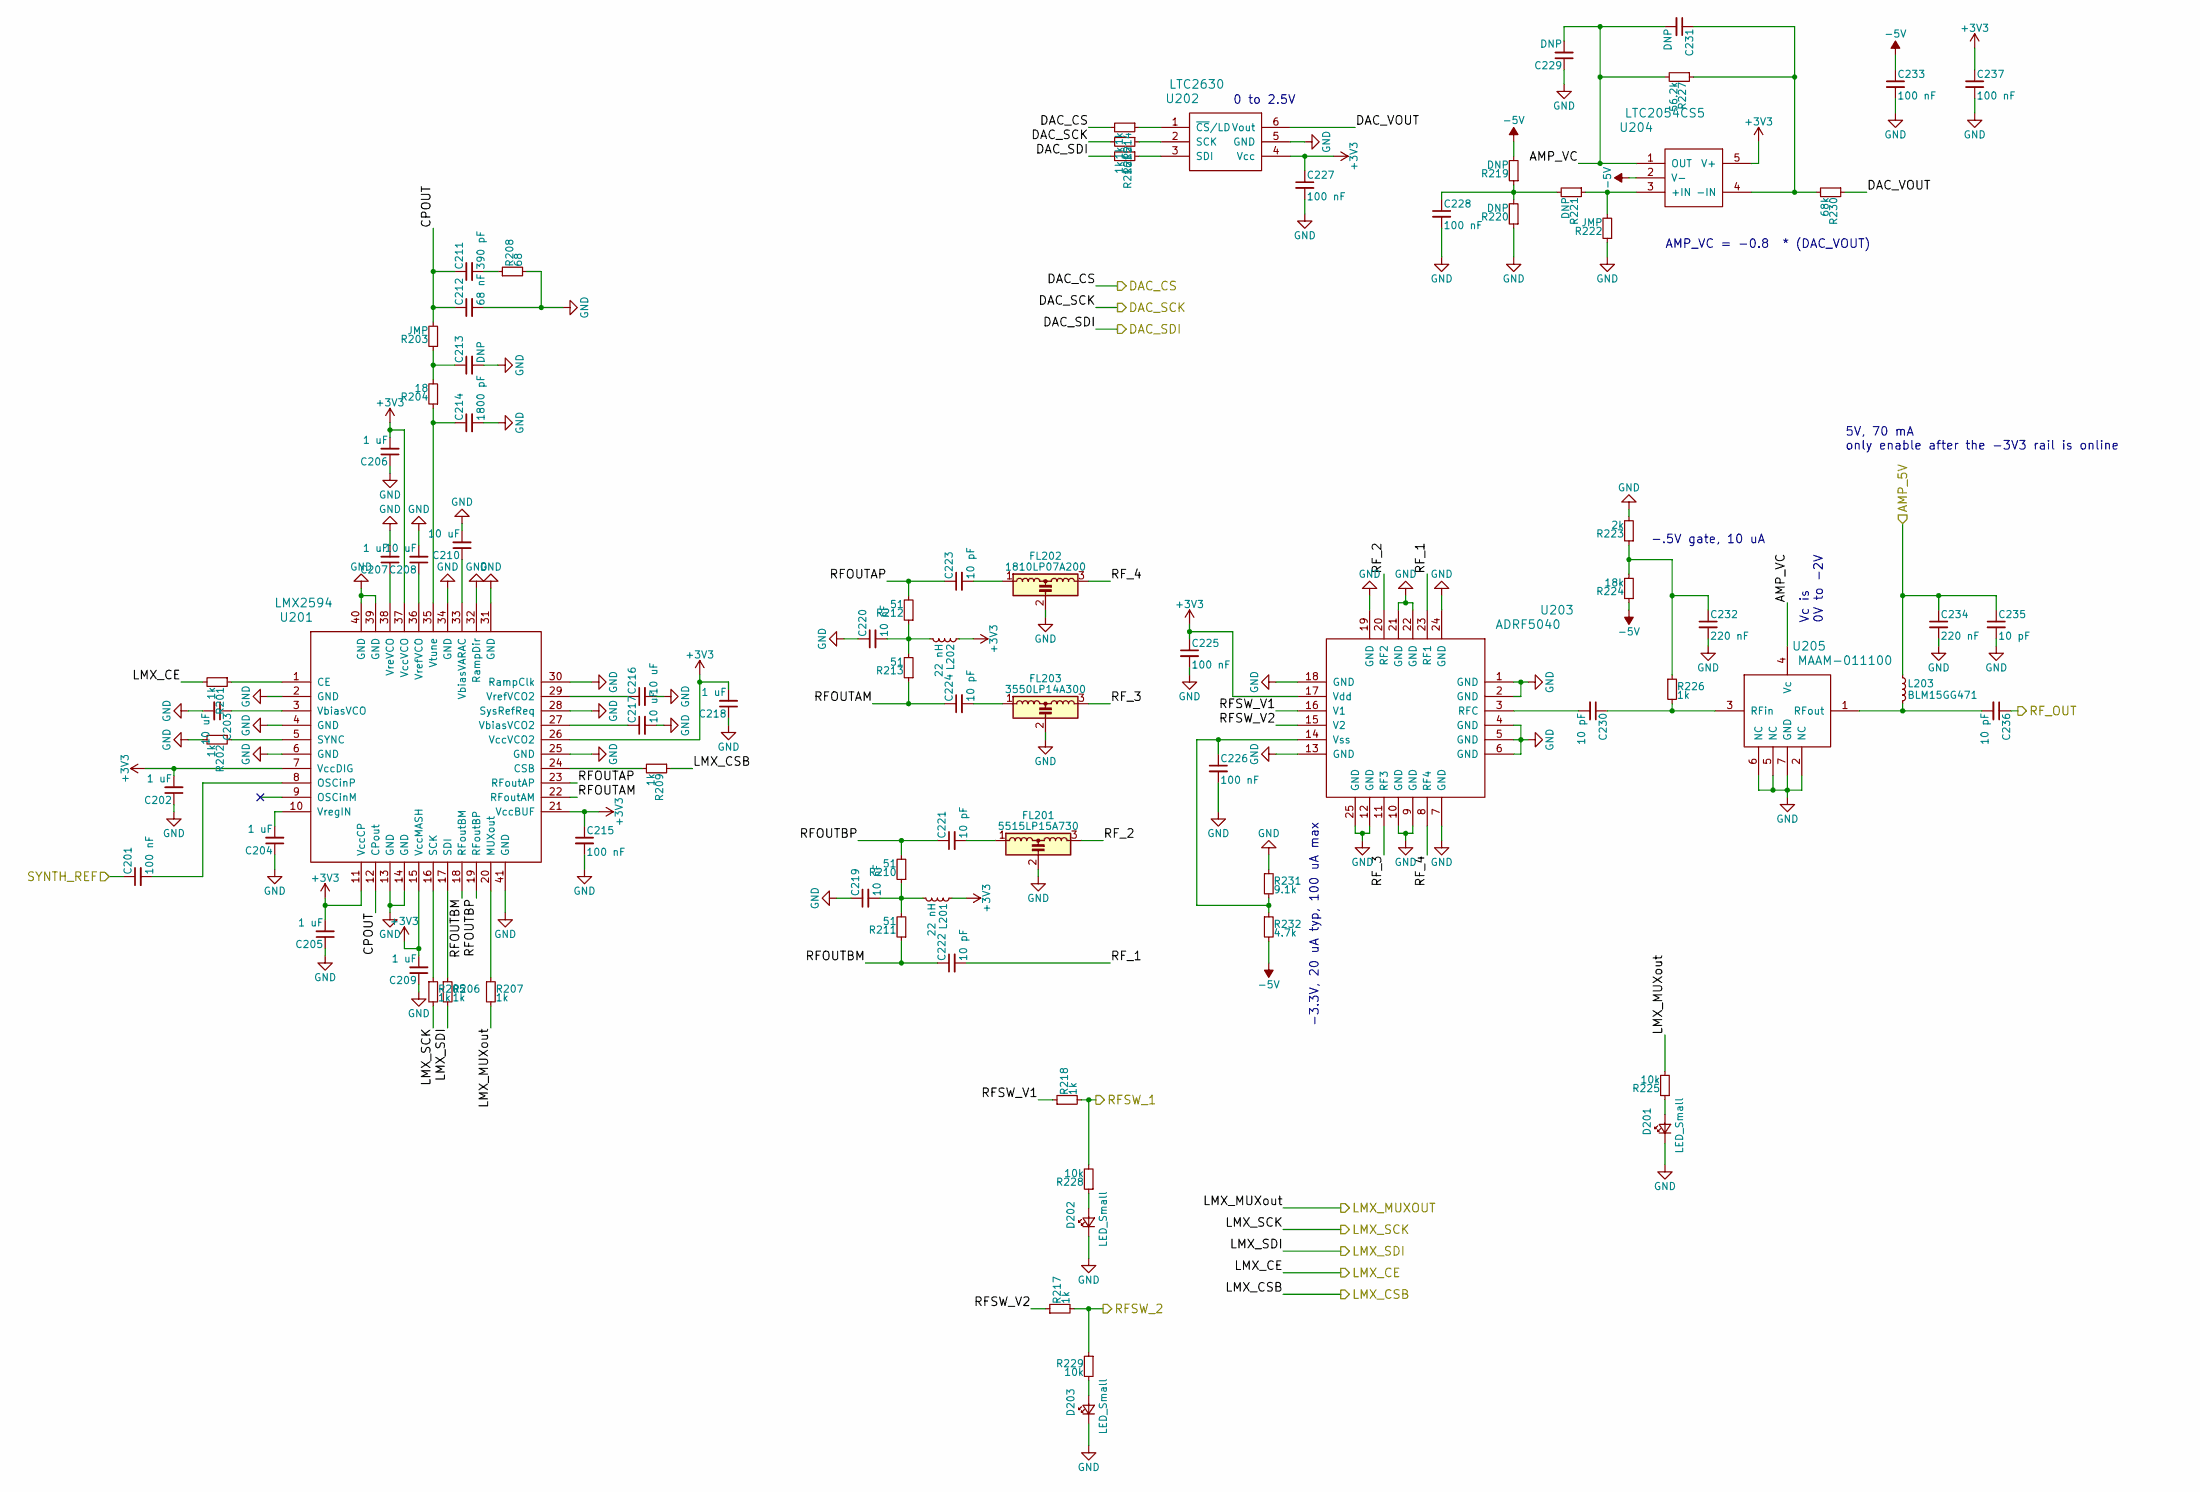
[picture p145: schematic rf_synth.sch]

Parts:
C201, C215, C225, C226, C227, C228, C233, C237: 100 nF; C_0402
C202, C204, C205, C206, C207, C209, C218: 1 uF; C_0402
C203, C208, C210, C216, C217: 10 uF; C_0603
C211: 390 pF; C_0402
C212: 68 nF; C_0402
C213, C229, C231: DNP; C_0402
C214: 1800 pF; C_0402
C219, C220: 10 nF; C_0402
C221, C222, C223, C224, C230, C235, C236: 10 pF; C_0402
C232, C234: 220 nF; C_0402
D201, D202, D203: LED_Small; LED_0603
FL201: 5515LP15A730
FL202: 1810LP07A200
FL203: 3550LP14A300
L201, L202: 22 nH; R_0402
L203: BLM15GG471; R_0402
R201, R202, R205, R206, R207, R209, R214, R215, R216, R217, R218, R226: 1k; R_0402
R203, R222: JMP; R_0402
R204: 18; R_0402
R208: 68; R_0402
R210, R211, R212, R213: 51; R_0402
R219, R220, R221: DNP; R_0402
R223: 2k; R_0402
R224: 18k; R_0402
R225, R228, R229: 10k; R_0402
R227: 56.2k; R_0402
R230: 68k; R_0402
R231: 9.1k; R_0402
R232: 4.7k; R_0402
U201: LMX2594; QFN-40-1EP_6x6mm_Pitch0.5mm
U202: LTC2630; SC-70-6
U203: ADRF5040; QFN-24-1EP_4x4mm_Pitch0.5mm
U204: LTC2054CS5; SOT-23-5
U205: MAAM-011100; TDFN6

Connections:
+3V3: C202.2, C205.2, C206.2, C209.2, C215.1, C218.2, C225.1, C227.1, C237.1, L201.1, L202.1, U201.7 (VccDIG), U201.11 (VccCP), U201.15 (VccMASH), U201.21 (VccBUF), U201.26 (VccVCO2), U201.37 (VccVCO), U202.4 (Vcc), U203.17 (Vdd), U204.5 (V+)
-5V: C233.1, R219.2, R224.1, R232.2, U204.2 (V-)
AMP_5V: C234.1, C235.1, L203.1
AMP_VC: C229.2, C231.2, R227.2, U204.1 (OUT), U205.4 (Vc)
CPOUT: C211.1, C212.1, R203.2, U201.12 (CPout)
DAC_CS: R214.2
DAC_SCK: R215.2
DAC_SDI: R216.2
DAC_VOUT: R230.1, U202.6 (Vout)
GND: C202.1, C203.2, C204.1, C205.1, C206.1, C207.2, C208.2, C209.1, C210.2, C212.2, C213.2, C214.2, C215.2, C216.2, C217.2, C218.1, C219.1, C220.1, C225.2, C226.2, C227.2, C228.2, C229.1, C232.2, C233.2, C234.2, C235.2, C237.2, D201.1 (K), D202.1 (K), D203.1 (K), FL201.2, FL202.2, FL203.2, R202.2, R208.2, R220.1, R222.1, R223.2, R231.1, U201.2 (GND), U201.4 (GND), U201.6 (GND), U201.13 (GND), U201.14 (GND), U201.25 (GND), U201.28 (SysRefReq), U201.30 (RampClk), U201.31 (GND), U201.32 (RampDir), U201.34 (GND), U201.39 (GND), U201.40 (GND), U201.41 (GND), U202.5 (GND), U203.1 (GND), U203.2 (GND), U203.4 (GND), U203.5 (GND), U203.6 (GND), U203.7 (GND), U203.9 (GND), U203.10 (GND), U203.12 (GND), U203.13 (GND), U203.18 (GND), U203.19 (GND), U203.21 (GND), U203.22 (GND), U203.24 (GND), U203.25 (GND), U205.2 (NC), U205.5 (NC), U205.6 (NC), U205.7 (GND)
LMX_CE: R201.2
LMX_CSB: R209.1
LMX_MUXout: R207.2, R225.2
LMX_SCK: R205.2
LMX_SDI: R206.2
unnamed: C201.2, U201.8 (OSCinP)
unnamed: C203.1, U201.3 (VbiasVCO)
unnamed: C204.2, U201.10 (VregIN)
unnamed: C207.1, U201.38 (VreVCO)
unnamed: C208.1, U201.36 (VrefVCO)
unnamed: C210.1, U201.33 (VbiasVARAC)
unnamed: C211.2, R208.1
unnamed: C213.1, R203.1, R204.2
unnamed: C214.1, R204.1, U201.35 (Vtune)
unnamed: C216.1, U201.29 (VrefVCO2)
unnamed: C217.1, U201.27 (VbiasVCO2)
unnamed: C219.2, L201.2, R210.1, R211.2
unnamed: C220.2, L202.2, R212.1, R213.2
unnamed: C221.2, FL201.1
unnamed: C223.2, FL202.1
unnamed: C224.2, FL203.1
unnamed: C226.1, R231.2, R232.1, U203.14 (Vss)
unnamed: C228.1, R219.1, R220.2, R221.2
unnamed: C230.1, R226.2, U205.3 (RFin)
unnamed: C230.2, U203.3 (RFC)
unnamed: C231.1, R227.1, R230.2, U204.4 (-IN)
unnamed: C232.1, R223.1, R224.2, R226.1
unnamed: C236.2, L203.2, U205.1 (RFout)
unnamed: D201.2 (A), R225.1
unnamed: D202.2 (A), R228.1
unnamed: D203.2 (A), R229.2
unnamed: R201.1, U201.1 (CE)
unnamed: R202.1, U201.5 (SYNC)
unnamed: R205.1, U201.16 (SCK)
unnamed: R206.1, U201.17 (SDI)
unnamed: R207.1, U201.20 (MUXout)
unnamed: R209.2, U201.24 (CSB)
unnamed: R214.1, U202.1 (~CS~/LD)
unnamed: R215.1, U202.2 (SCK)
unnamed: R216.1, U202.3 (SDI)
unnamed: R221.1, R222.2, U204.3 (+IN)
RFOUTAM: C224.1, R213.1, U201.22 (RFoutAM)
RFOUTAP: C223.1, R212.2, U201.23 (RFoutAP)
RFOUTBM: C222.1, R211.1, U201.18 (RFoutBM)
RFOUTBP: C221.1, R210.2, U201.19 (RFoutBP)
RFSW_1: R218.2, R228.2
RFSW_2: R217.2, R229.1
RFSW_V1: R218.1, U203.16 (V1)
RFSW_V2: R217.1, U203.15 (V2)
RF_1: C222.2, U203.23 (RF1)
RF_2: FL201.3, U203.20 (RF2)
RF_3: FL203.3, U203.11 (RF3)
RF_4: FL202.3, U203.8 (RF4)
RF_OUT: C236.1
SYNTH_REF: C201.1

Notes on the sheet:
-.5V gate, 10 uA
5V, 70 mA only enable after the -3V3 rail is online
Vc is 0V to -2V
0 to 2.5V
AMP_VC = -0.8 * (DAC_VOUT)
-3.3V, 20 uA typ, 100 uA max
