loxodes/vna/software/vna_controller/zmq_synth_server.py

import zmq
import argparse
import pdb
import numpy as np

import synth_bbone
from synth_commands import *


SYNTH_PINS = {'rf':synth_bbone.RF_SYNTH_PINS, 'demod':synth_bbone.DEMOD_SYNTH_PINS}


class zmq_synth_server:
    def __init__(self, context, synth, port):
        self.synth = synth
        self.context = context
        self.socket = context.socket(zmq.REP)
        self.socket.bind("tcp://*:{}".format(str(port)))
    
    def _set_freq(self, message):
        freq = float(message[1:])
        print('setting frequency to {} Hz'.format(freq))
        self.synth.set_freq(freq)
        return message[COMMAND_INDEX]

    def _set_filter_bank(self, message):
        freq = float(message[1:])
        print('setting filter bank for {} GHz'.format(freq/1e9))
        self.synth.set_filter_bank(freq)
        return message[COMMAND_INDEX]

    def _set_power_dac(self, message):
        pow_dac = int(message[1:])
        print('dac to set to '.format(pow_dac))
        self.synth.set_power_dac(pow_dac)
        return message[COMMAND_INDEX]

    def _set_power_lmx(self, message):
        pow_lmx = int(message[1:])
        print('lmx power level to {}'.format(pow_lmx))
        self.synth.set_power_lmx(pow_lmx)
        return message[COMMAND_INDEX]


    def _wait_for_lock(self, message):
        print('waiting for pll lock')
        self.synth.wait_for_lock()
        print('locked!')
        return message[COMMAND_INDEX]


    def run(self):
        self.command_handlers = {\
            FREQ_CMD : self._set_freq, \
            LMX_POW_CMD : self._set_power_lmx, \
            FILT_CMD : self._set_filter_bank, \
            DAC_POW_CMD : self._set_power_dac, \
            WAIT_CMD : self._wait_for_lock}

        print('entering run loop')
        while True:
            print('waiting for command..')
            message = self.socket.recv().decode('utf-8') 
            command = message[COMMAND_INDEX]
            print('received {} command, message: {}'.format(command, message))

            response = ''

            if command in self.command_handlers:
                response = self.command_handlers[command](message)
            
            else:
                print('unrecognized command')
                pdb.set_trace()
            
            self.socket.send(response.encode('utf-8'))


if __name__ == '__main__':

    parser = argparse.ArgumentParser()
    parser.add_argument('--synth', help = 'synth (rf/demod)', default = 'rf')
    args = parser.parse_args()

    context = zmq.Context()
    synth_name = args.synth
    
    pins = SYNTH_PINS[synth_name]
    port = SYNTH_PORTS[synth_name]

    synth = synth_bbone.synth_r1(pins)
    print('initializing synth')
    synth_server = zmq_synth_server(context, synth, port)
    print('running zmq server')
    synth_server.run()
    raw_input('press enter to continue')
    synth_server.close()
    
    context.destroy()
